niravkumar2008/AI-CALCULATOR/hardware/fab_v15_lcd/cpl_easyeda_check_v15.md

| Ref | LCSC | EasyEDA footprint | KiCad rot | CPL rot | EasyEDA pin 1 -> KiCad pad 1 (mm) | worst same-number pad offset (mm) | every EasyEDA pad on a KiCad pad | Result |
|---|---|---|---|---|---|---|---|---|
| D1 | C8598 | SOD-123_L2.7-W1.6-LS3.7-RD-1 | 0 | 0 | 0.05 | 0.05 | yes | PASS |
| D2 | C8598 | SOD-123_L2.7-W1.6-LS3.7-RD-1 | 0 | 0 | 0.05 | 0.05 | yes | PASS |
| D6 | C8598 | SOD-123_L2.7-W1.6-LS3.7-RD-1 | 0 | 0 | 0.05 | 0.05 | yes | PASS |
| D7 | C193402 | SOD-123FL_L2.7-W1.8-LS3.8-RD | 180 | 180 | 0.18 | 0.18 | yes | PASS |
| J1 | C6364666 | FPC-SMD_24P-P0.50_FPC-0.5-24P-HYH2.0 | 180 | 180 | 11.50 | 11.50 | yes | PASS (pin numbers mirrored on purpose: geometry only) |
| J3 | C46061768 | CONN-SMD_4P-P2.54_HX-PM2.54-1X4PWT | 0 | 180 | 7.62 | 7.62 | yes | PASS (unpolarised 4 identical contacts: geometry only) |
| J4 | C295747 | CONN-SMD_P2.00_S2B-PH-SM4-TB-LF-SN | 0 | 0 | 0.00 | 0.00 | yes | PASS |
| J5 | C2919501 | FPC-SMD_30P-P0.50_HDGC_0.5K-HX-30PWB | 90 | 90 | 14.50 | 14.50 | yes | PASS (pin numbers mirrored on purpose, _LcdReversed, review 13: geometry only) |
| Q1 | C15127 | SOT-23_L2.9-W1.3-P1.90-LS2.4-BR | 0 | 180 | 0.21 | 0.21 | yes | PASS |
| Q2 | C15127 | SOT-23_L2.9-W1.3-P1.90-LS2.4-BR | 90 | 270 | 0.21 | 0.21 | yes | PASS |
| Q4 | C15127 | SOT-23_L2.9-W1.3-P1.90-LS2.4-BR | 90 | 270 | 0.21 | 0.21 | yes | PASS |
| Q5 | C20917 | SOT-23-3_L2.9-W1.3-P1.90-LS2.4-BR | -90 | 90 | 0.06 | 0.06 | yes | PASS |
| R23 | C22810 | R0603 | 180 | 180 | 0.07 | 0.07 | yes | PASS |
| U1 | C3013941 | BULETM-SMD_ESP32-S3-MINI-1-N8 | 90 | 90 | 0.02 | 0.03 | yes | PASS |
| U2 | C424093 | SOT-23-5_L3.0-W1.7-P0.95-LS2.8-BL | 0 | 270 | 0.01 | 0.01 | yes | PASS |
| U3 | C841192 | TSOT-23-5_L2.9-W1.6-P0.95-LS2.8-BL | 0 | 270 | 0.01 | 0.01 | yes | PASS |
| U4 | C53099 | SOT-23-5_L3.0-W1.7-P0.95-LS2.8-BR | 0 | 180 | 0.16 | 0.16 | yes | PASS |
| U5 | C53100 | SOT-23-5_L3.0-W1.7-P0.95-LS2.8-BR | 0 | 180 | 0.16 | 0.16 | yes | PASS |
| U6 | C138713 | WQFN-24_L4.0-W4.0-P0.50-TL-EP2.5 | 0 | 0 | 0.08 | 0.08 | yes | PASS |
| U7 | C7519 | SOT-23-6_L2.9-W1.6-P0.95-LS2.8-BL | 0 | 270 | 0.01 | 0.01 | yes | PASS |
