niravkumar2008/AI-CALCULATOR/hardware/fitcheck/clearance_table.md

# F-side clearance table (generated by tools/make_fitcheck.py)

Height = tallest point of the 3D model above the board F side. Rib = tallest back-cover feature within 1.5 mm of the part (photo positions are +-1 mm). Margin = free height - rib - part, for the free-height cases in backcover_fx115es.json (design 6.0 = D4 measured to the inside face of the back cover). Below 0.3 = needs a fix or a grind.

Last column: after the grind plan (solar box -> 0 mm, upper rib B (camera) -> 0 mm).

| Part | Height | Back-cover feature over it | Feature height | Margin @ 6.0 (design) | Margin @ 5.5 (pessimistic) | Margin after grind (design) |
|---|---|---|---|---|---|---|
| J4 | 5.50 | solar box | 5.5 | **-5.00** | **-5.50** | 0.50 |
| camera 5.4 * | 5.40 | upper rib B (camera) | 1 | **-0.40** | **-0.90** | 0.60 |
| magnet body * | 4.80 | - | 0 | 1.20 | 0.70 | 1.20 |
| LiPo #1317 150 mAh 3.8 thick * | 3.80 | solar box | 5.5 | **-3.30** | **-3.80** | 2.20 |
| J3 | 2.50 | solar box | 5.5 | **-2.00** | **-2.50** | 3.50 |
| U1 | 2.41 | upper rib B left | 1 | 2.59 | 2.09 | 2.59 |
| L1 | 2.00 | upper vert 1 | 1 | 3.00 | 2.50 | 3.00 |
| J2 | 1.99 | upper rib B | 1 | 3.01 | 2.51 | 3.01 |
| J1 | 1.99 | low rib 1 | 1 | 3.01 | 2.51 | 3.01 |
| U2 | 1.60 | solar box | 5.5 | **-1.10** | **-1.60** | 4.40 |
| C20 | 1.59 | - | 0 | 4.41 | 3.91 | 4.41 |
| U7 | 1.55 | upper rib A | 1 | 3.45 | 2.95 | 3.45 |
| U3 | 1.55 | solar box | 5.5 | **-1.05** | **-1.55** | 4.45 |
| U5 | 1.55 | low rib 1 | 1 | 3.45 | 2.95 | 3.45 |
| U4 | 1.55 | - | 0 | 4.45 | 3.95 | 4.45 |
| D4 | 1.26 | upper rib C, upper vert 1 | 1 | 3.74 | 3.24 | 3.74 |
| D1 | 1.26 | solar box | 5.5 | **-0.76** | **-1.26** | 4.74 |
| D3 | 1.26 | upper rib C, upper vert 1 | 1 | 3.74 | 3.24 | 3.74 |
| D5 | 1.26 | upper rib C, upper vert 1 | 1 | 3.74 | 3.24 | 3.74 |
| D6 | 1.26 | - | 0 | 4.74 | 4.24 | 4.74 |
| D2 | 1.26 | big ring | 4 | 0.74 | **0.24** | 0.74 |
| C32 | 1.24 | upper rib A | 1 | 3.76 | 3.26 | 3.76 |
| C33 | 1.24 | - | 0 | 4.76 | 4.26 | 4.76 |
| C34 | 1.24 | - | 0 | 4.76 | 4.26 | 4.76 |
| C1 | 1.24 | upper rib C | 1 | 3.76 | 3.26 | 3.76 |
| Q2 | 1.20 | solar box | 5.5 | **-0.70** | **-1.20** | 4.80 |
| Q1 | 1.20 | upper rib A, upper vert 2 | 1 | 3.80 | 3.30 | 3.80 |
| Q3 | 1.10 | upper rib B | 1 | 3.90 | 3.40 | 3.90 |
| U6 | 1.02 | - | 0 | 4.98 | 4.48 | 4.98 |
| D7 | 0.99 | solar box | 5.5 | **-0.49** | **-0.99** | 5.01 |
| C6 | 0.79 | solar box | 5.5 | **-0.29** | **-0.79** | 5.21 |
| C23 | 0.79 | - | 0 | 5.21 | 4.71 | 5.21 |
| C19 | 0.79 | upper rib B, upper rib B (camera) | 1 | 4.21 | 3.71 | 4.21 |
| C27 | 0.79 | upper rib C, upper vert 1 | 1 | 4.21 | 3.71 | 4.21 |
| C22 | 0.79 | - | 0 | 5.21 | 4.71 | 5.21 |
| FB1 | 0.79 | - | 0 | 5.21 | 4.71 | 5.21 |
| C7 | 0.79 | - | 0 | 5.21 | 4.71 | 5.21 |
| C28 | 0.79 | upper rib B | 1 | 4.21 | 3.71 | 4.21 |
| C21 | 0.79 | - | 0 | 5.21 | 4.71 | 5.21 |
| C8 | 0.79 | upper rib A | 1 | 4.21 | 3.71 | 4.21 |
| C3 | 0.79 | upper rib C | 1 | 4.21 | 3.71 | 4.21 |
| C5 | 0.79 | solar box | 5.5 | **-0.29** | **-0.79** | 5.21 |
| C24 | 0.79 | - | 0 | 5.21 | 4.71 | 5.21 |
| C25 | 0.79 | - | 0 | 5.21 | 4.71 | 5.21 |
| C26 | 0.79 | upper rib B | 1 | 4.21 | 3.71 | 4.21 |
| C30 | 0.79 | - | 0 | 5.21 | 4.71 | 5.21 |
| C29 | 0.79 | - | 0 | 5.21 | 4.71 | 5.21 |
| C17 | 0.60 | - | 0 | 5.40 | 4.90 | 5.40 |
| C18 | 0.49 | - | 0 | 5.51 | 5.01 | 5.51 |
| C13 | 0.49 | - | 0 | 5.51 | 5.01 | 5.51 |
| C16 | 0.49 | big ring | 4 | 1.51 | 1.01 | 1.51 |
| C31 | 0.49 | - | 0 | 5.51 | 5.01 | 5.51 |
| C9 | 0.49 | upper rib C, upper vert 2 | 1 | 4.51 | 4.01 | 4.51 |
| C10 | 0.49 | - | 0 | 5.51 | 5.01 | 5.51 |
| C12 | 0.49 | - | 0 | 5.51 | 5.01 | 5.51 |
| C2 | 0.49 | upper rib C | 1 | 4.51 | 4.01 | 4.51 |
| C15 | 0.49 | low rib 1 | 1 | 4.51 | 4.01 | 4.51 |
| C11 | 0.49 | - | 0 | 5.51 | 5.01 | 5.51 |
| C14 | 0.49 | - | 0 | 5.51 | 5.01 | 5.51 |
| C4 | 0.49 | - | 0 | 5.51 | 5.01 | 5.51 |
| R12 | 0.45 | upper rib B, upper vert 1 | 1 | 4.55 | 4.05 | 4.55 |
| R10 | 0.34 | - | 0 | 5.66 | 5.16 | 5.66 |
| R19 | 0.34 | - | 0 | 5.66 | 5.16 | 5.66 |
| R3 | 0.34 | - | 0 | 5.66 | 5.16 | 5.66 |
| R17 | 0.34 | - | 0 | 5.66 | 5.16 | 5.66 |
| R20 | 0.34 | upper rib A | 1 | 4.66 | 4.16 | 4.66 |
| R11 | 0.34 | - | 0 | 5.66 | 5.16 | 5.66 |
| R2 | 0.34 | solar box | 5.5 | **0.16** | **-0.34** | 5.66 |
| R6 | 0.34 | upper rib C | 1 | 4.66 | 4.16 | 4.66 |
| R16 | 0.34 | - | 0 | 5.66 | 5.16 | 5.66 |
| R15 | 0.34 | - | 0 | 5.66 | 5.16 | 5.66 |
| R1 | 0.34 | - | 0 | 5.66 | 5.16 | 5.66 |
| R14 | 0.34 | - | 0 | 5.66 | 5.16 | 5.66 |
| R13 | 0.34 | - | 0 | 5.66 | 5.16 | 5.66 |
| R4 | 0.34 | solar box | 5.5 | **0.16** | **-0.34** | 5.66 |
| R5 | 0.34 | upper rib A | 1 | 4.66 | 4.16 | 4.66 |
| R9 | 0.34 | - | 0 | 5.66 | 5.16 | 5.66 |
| R18 | 0.34 | - | 0 | 5.66 | 5.16 | 5.66 |
| R7 | 0.34 | upper rib C | 1 | 4.66 | 4.16 | 4.66 |
| R8 | 0.34 | - | 0 | 5.66 | 5.16 | 5.66 |
| TP6 | 0.05 | upper rib A, upper vert 2 | 1 | 4.95 | 4.45 | 4.95 |
| TP1 | 0.05 | - | 0 | 5.95 | 5.45 | 5.95 |
| TP5 | 0.05 | upper rib A | 1 | 4.95 | 4.45 | 4.95 |
| TP4 | 0.05 | - | 0 | 5.95 | 5.45 | 5.95 |
| TP3 | 0.05 | upper vert 2 | 1 | 4.95 | 4.45 | 4.95 |
| TP7 | 0.05 | - | 0 | 5.95 | 5.45 | 5.95 |
| TP2 | 0.05 | upper vert 2 | 1 | 4.95 | 4.45 | 4.95 |

\* = not a board part. **camera:** not soldered; module sits on the board (or taped to the cover), lens under the drilled window. **LiPo:** rev E: Adafruit #1317 flat on the back-cover floor under the solar-box zone (ground flat), 2.2 mm under the board, 0.3 mm under the LR44 cup (kept); its margin row counts the floor-to-board space (6.0) only. **magnet:** stage 13b: body in front of the board edge (y 57.3-61.3), centred 1.3 mm above the F side, spanning 2.2 below to 4.8 above it; legs straightened into J3 (right-angle header). The LiPo row is the floor-to-board space (6.0) minus the cell (3.8): the real limit is the LR44 cup in the faceplate (0.3 mm, assembly_report.md section 9).

Front shell: LR44 cup (centre 168.3, 69.0, outer dia 14); magnet slot (top wall) at [116.75, 56.9]-[138.25, 58.6]; antenna relief (inner rib) at [114.15, 71.5]-[115.15, 106.5]. See the grind list on grind_map_front_shell.svg.
