niravkumar2008/AI-CALCULATOR/hardware/kicad/DESIGN_SUMMARY.md

# AI Calculator PCB - KiCad design summary

Generated by `hardware/kicad/kicad_summary.py` from the KiCad 10 project in `C:\Users\r_kas\OneDrive\Documents\GitHub\AI-CALCULATOR\hardware\kicad`. Do not edit by hand. Context and decisions: `Claude outputs/AI_CALC_PCB_HANDOFF.md`.

## Hierarchy

Root sheet `ai_calc.kicad_sch` contains:

- **Power and charging** (`power.kicad_sch`)
- **ESP32-S3 MCU** (`mcu.kicad_sch`)
- **Camera OV5640** (`camera.kicad_sch`)
- **E-paper driver** (`epaper.kicad_sch`)
- **Keypad and TCA8418** (`keypad.kicad_sch`)
- **Connectors (magnet USB, battery)** (`connectors.kicad_sch`)

## Sheet: Power and charging (`power.kicad_sch`)

Net labels: +3V3, BAT+, CHG_PROG, CHG_STAT, CHG_STAT_RAW, GND, Q1_G, SYS, VBAT_P, VBAT_SENSE, VBUS, VBUS_SENSE

| Ref | Value | Footprint | LCSC |
|---|---|---|---|
| C5 | 4.7uF | Capacitor_SMD:C_0603_1608Metric | C19666 |
| C6 | 4.7uF | Capacitor_SMD:C_0603_1608Metric | C19666 |
| C7 | 4.7uF | Capacitor_SMD:C_0603_1608Metric | C19666 |
| C8 | 10uF | Capacitor_SMD:C_0603_1608Metric | C19702 |
| C9 | 100nF | Capacitor_SMD:C_0402_1005Metric | C1525 |
| D1 | B5819W | Diode_SMD:D_SOD-123 | C8598 |
| D6 | B5819W (STAT level clamp) | Diode_SMD:D_SOD-123 | C8598 |
| Q1 | AO3401A (reverse battery) | Package_TO_SOT_SMD:SOT-23 | C15127 |
| Q2 | AO3401A (load share) | Package_TO_SOT_SMD:SOT-23 | C15127 |
| R2 | 20k (50 mA) | Resistor_SMD:R_0402_1005Metric | C25765 |
| R3 | 100k | Resistor_SMD:R_0402_1005Metric | C25741 |
| R4 | 10k | Resistor_SMD:R_0402_1005Metric | C25744 |
| R5 | 20k | Resistor_SMD:R_0402_1005Metric | C25765 |
| R6 | 1M | Resistor_SMD:R_0402_1005Metric | C26083 |
| R7 | 1M | Resistor_SMD:R_0402_1005Metric | C26083 |
| R20 | 100k | Resistor_SMD:R_0402_1005Metric | C25741 |
| U2 | MCP73831T-2ACI/OT | Package_TO_SOT_SMD:SOT-23-5 | C424093 |
| U3 | RT9080-33GJ5 | Package_TO_SOT_SMD:SOT-23-5 | C841192 |

## Sheet: ESP32-S3 MCU (`mcu.kicad_sch`)

Net labels: +3V3, BAT+, BOOT, CAM_D0, CAM_D1, CAM_D2, CAM_D3, CAM_D4, CAM_D5, CAM_D6, CAM_D7, CAM_HREF, CAM_PCLK, CAM_PWDN, CAM_PWR_EN, CAM_RESET, CAM_SIOC, CAM_SIOD, CAM_VSYNC, CAM_XCLK, CHG_STAT, EN, EPD_BUSY, EPD_CLK, EPD_CS, EPD_DC, EPD_DIN, EPD_RST, GND, I2C_SCL, I2C_SDA, KEYPAD_INT, KEY_ON, UART_RX, UART_TX, USB_DM, USB_DP, VBAT_SENSE, VBUS_SENSE

| Ref | Value | Footprint | LCSC |
|---|---|---|---|
| C1 | 22uF | Capacitor_SMD:C_0805_2012Metric | C45783 |
| C2 | 100nF | Capacitor_SMD:C_0402_1005Metric | C1525 |
| C3 | 10uF | Capacitor_SMD:C_0603_1608Metric | C19702 |
| C4 | 1uF | Capacitor_SMD:C_0402_1005Metric | C52923 |
| C32 | 22uF | Capacitor_SMD:C_0805_2012Metric | C45783 |
| C33 | 22uF | Capacitor_SMD:C_0805_2012Metric | C45783 |
| C34 | 22uF | Capacitor_SMD:C_0805_2012Metric | C45783 |
| R1 | 10k | Resistor_SMD:R_0402_1005Metric | C25744 |
| TP1 | BOOT | TestPoint:TestPoint_Pad_D1.5mm |  |
| TP2 | UART_TX | TestPoint:TestPoint_Pad_D1.0mm |  |
| TP3 | UART_RX | TestPoint:TestPoint_Pad_D1.0mm |  |
| TP4 | GND | TestPoint:TestPoint_Pad_D1.5mm |  |
| TP5 | +3V3 | TestPoint:TestPoint_Pad_D1.5mm |  |
| TP6 | BAT+ | TestPoint:TestPoint_Pad_D1.5mm |  |
| TP7 | EN | TestPoint:TestPoint_Pad_D1.5mm |  |
| U1 | ESP32-S3-MINI-1-N4R2 | ai_calc:ESP32-S3-MINI-1 | C3013941 |

## Sheet: Camera OV5640 (`camera.kicad_sch`)

Net labels: CAM_2V8, CAM_AF, CAM_AVDD, CAM_D0, CAM_D1, CAM_D2, CAM_D3, CAM_D4, CAM_D5, CAM_D6, CAM_D7, CAM_DVDD, CAM_HREF, CAM_PCLK, CAM_PWDN, CAM_PWR_EN, CAM_RESET, CAM_SIOC, CAM_SIOD, CAM_VSYNC, CAM_XCLK, GND, SYS

| Ref | Value | Footprint | LCSC |
|---|---|---|---|
| C10 | 1uF | Capacitor_SMD:C_0402_1005Metric | C52923 |
| C11 | 2.2uF | Capacitor_SMD:C_0402_1005Metric | C12530 |
| C12 | 100nF | Capacitor_SMD:C_0402_1005Metric | C1525 |
| C13 | 2.2uF | Capacitor_SMD:C_0402_1005Metric | C12530 |
| C14 | 1uF | Capacitor_SMD:C_0402_1005Metric | C52923 |
| C15 | 2.2uF | Capacitor_SMD:C_0402_1005Metric | C12530 |
| C16 | 2.2uF | Capacitor_SMD:C_0402_1005Metric | C12530 |
| C17 | 100nF | Capacitor_SMD:C_0402_1005Metric | C1525 |
| C18 | 100nF | Capacitor_SMD:C_0402_1005Metric | C1525 |
| D2 | B5819W | Diode_SMD:D_SOD-123 | C8598 |
| FB1 | 600R@100MHz | Inductor_SMD:L_0603_1608Metric | C1002 |
| J1 | Camera FPC 24P 0.5mm dual-contact (OV5640, cable contacts down) | ai_calc:FPC_24P_P0.5mm_DualContact_C6364666_CamReversed | C6364666 |
| R8 | 10k | Resistor_SMD:R_0402_1005Metric | C25744 |
| R9 | 10k | Resistor_SMD:R_0402_1005Metric | C25744 |
| R10 | 100k | Resistor_SMD:R_0402_1005Metric | C25741 |
| R18 | 4.7k | Resistor_SMD:R_0402_1005Metric | C25900 |
| R19 | 4.7k | Resistor_SMD:R_0402_1005Metric | C25900 |
| U4 | ME6211C28M5G-N | Package_TO_SOT_SMD:SOT-23-5 | C53099 |
| U5 | ME6211C15M5G-N | Package_TO_SOT_SMD:SOT-23-5 | C53100 |

## Sheet: E-paper driver (`epaper.kicad_sch`)

Net labels: +3V3, EPD_BUSY, EPD_CLK, EPD_CS, EPD_DC, EPD_DIN, EPD_GDR, EPD_PREVGH, EPD_PREVGL, EPD_PUMP, EPD_RESE, EPD_RST, EPD_SW, EPD_VCOM, EPD_VDD, EPD_VGH, EPD_VGL, EPD_VPP, EPD_VSH, EPD_VSL, GND

| Ref | Value | Footprint | LCSC |
|---|---|---|---|
| C19 | 4.7uF | Capacitor_SMD:C_0603_1608Metric | C19666 |
| C20 | 4.7uF 50V | Capacitor_SMD:C_1206_3216Metric | C29823 |
| C21 | 1uF 50V | Capacitor_SMD:C_0603_1608Metric | C15849 |
| C22 | 1uF 50V | Capacitor_SMD:C_0603_1608Metric | C15849 |
| C23 | 1uF 50V | Capacitor_SMD:C_0603_1608Metric | C15849 |
| C24 | 1uF 50V | Capacitor_SMD:C_0603_1608Metric | C15849 |
| C25 | 1uF 50V | Capacitor_SMD:C_0603_1608Metric | C15849 |
| C26 | 1uF 50V | Capacitor_SMD:C_0603_1608Metric | C15849 |
| C27 | 1uF 50V | Capacitor_SMD:C_0603_1608Metric | C15849 |
| C28 | 1uF 50V | Capacitor_SMD:C_0603_1608Metric | C15849 |
| C29 | 1uF 50V | Capacitor_SMD:C_0603_1608Metric | C15849 |
| C30 | 1uF 50V | Capacitor_SMD:C_0603_1608Metric | C15849 |
| D3 | B5819W | Diode_SMD:D_SOD-123 | C8598 |
| D4 | B5819W | Diode_SMD:D_SOD-123 | C8598 |
| D5 | B5819W | Diode_SMD:D_SOD-123 | C8598 |
| J2 | E-paper FPC 24P 0.5mm dual-contact (2.13in V4) | ai_calc:FPC_24P_P0.5mm_DualContact_C6364666 | C6364666 |
| L1 | 68uH SMNR4020 | ai_calc:L_SMNR4020_4.0x4.0mm | C135265 |
| Q3 | SI1308EDL-T1-GE3 | ai_calc:SOT-323_SI1308EDL | C469327 |
| R11 | 10k | Resistor_SMD:R_0402_1005Metric | C25744 |
| R12 | 3R (2.13in B/W panel) | Resistor_SMD:R_0603_1608Metric | C23157 |

## Sheet: Keypad and TCA8418 (`keypad.kicad_sch`)

Net labels: +3V3, COL0, COL1, COL2, COL3, COL4, COL5, COL6, COL7, COL8, COL9, GND, I2C_SCL, I2C_SDA, KEYPAD_INT, KEY_ON, ROW0, ROW1, ROW2, ROW3, ROW4, ROW5, ROW6, ROW7, TCA_RESET

| Ref | Value | Footprint | LCSC |
|---|---|---|---|
| C31 | 100nF | Capacitor_SMD:C_0402_1005Metric | C1525 |
| R13 | 4.7k | Resistor_SMD:R_0402_1005Metric | C25900 |
| R14 | 4.7k | Resistor_SMD:R_0402_1005Metric | C25900 |
| R15 | 10k | Resistor_SMD:R_0402_1005Metric | C25744 |
| R16 | 10k | Resistor_SMD:R_0402_1005Metric | C25744 |
| R17 | 100k | Resistor_SMD:R_0402_1005Metric | C25741 |
| SW1 | SHIFT | ai_calc:KeyPad_6.0x4.5_H3notch |  |
| SW2 | ALPHA | ai_calc:KeyPad_6.0x4.5 |  |
| SW3 | MODE | ai_calc:KeyPad_6.0x4.5 |  |
| SW4 | CALC | ai_calc:KeyPad_6.0x4.5 |  |
| SW5 | ∫dx | ai_calc:KeyPad_6.0x4.5 |  |
| SW6 | x^-1 | ai_calc:KeyPad_6.0x4.5 |  |
| SW7 | log_a | ai_calc:KeyPad_6.0x4.5 |  |
| SW8 | a/b | ai_calc:KeyPad_6.0x4.5 |  |
| SW9 | sqrt | ai_calc:KeyPad_6.0x4.5 |  |
| SW10 | x^2 | ai_calc:KeyPad_6.0x4.5 |  |
| SW11 | x^n | ai_calc:KeyPad_6.0x4.5 |  |
| SW12 | log | ai_calc:KeyPad_6.0x4.5 |  |
| SW13 | ln | ai_calc:KeyPad_6.0x4.5 |  |
| SW14 | (-) | ai_calc:KeyPad_6.0x4.5 |  |
| SW15 | deg-min-sec | ai_calc:KeyPad_6.0x4.5 |  |
| SW16 | hyp | ai_calc:KeyPad_6.0x4.5 |  |
| SW17 | sin | ai_calc:KeyPad_6.0x4.5 |  |
| SW18 | cos | ai_calc:KeyPad_6.0x4.5 |  |
| SW19 | tan | ai_calc:KeyPad_6.0x4.5 |  |
| SW20 | RCL | ai_calc:KeyPad_6.0x4.5 |  |
| SW21 | ENG | ai_calc:KeyPad_6.0x4.5 |  |
| SW22 | ( | ai_calc:KeyPad_6.0x4.5 |  |
| SW23 | ) | ai_calc:KeyPad_6.0x4.5 |  |
| SW24 | S<>D | ai_calc:KeyPad_6.0x4.5 |  |
| SW25 | M+ | ai_calc:KeyPad_6.0x4.5 |  |
| SW26 | 7 | ai_calc:KeyPad_9.0x7.0 |  |
| SW27 | 8 | ai_calc:KeyPad_9.0x7.0 |  |
| SW28 | 9 | ai_calc:KeyPad_9.0x7.0 |  |
| SW29 | DEL | ai_calc:KeyPad_9.0x7.0 |  |
| SW30 | AC | ai_calc:KeyPad_9.0x7.0 |  |
| SW31 | 4 | ai_calc:KeyPad_9.0x7.0 |  |
| SW32 | 5 | ai_calc:KeyPad_9.0x7.0 |  |
| SW33 | 6 | ai_calc:KeyPad_9.0x7.0 |  |
| SW34 | x | ai_calc:KeyPad_9.0x7.0 |  |
| SW35 | / | ai_calc:KeyPad_9.0x7.0 |  |
| SW36 | 1 | ai_calc:KeyPad_9.0x7.0 |  |
| SW37 | 2 | ai_calc:KeyPad_9.0x7.0 |  |
| SW38 | 3 | ai_calc:KeyPad_9.0x7.0 |  |
| SW39 | + | ai_calc:KeyPad_9.0x7.0 |  |
| SW40 | - | ai_calc:KeyPad_9.0x7.0 |  |
| SW41 | 0 | ai_calc:KeyPad_6.0x4.5 |  |
| SW42 | . | ai_calc:KeyPad_6.0x4.5 |  |
| SW43 | x10^x | ai_calc:KeyPad_6.0x4.5 |  |
| SW44 | Ans | ai_calc:KeyPad_6.0x4.5 |  |
| SW45 | = | ai_calc:KeyPad_6.0x4.5 |  |
| SW46 | UP | ai_calc:KeyPad_5.0x4.0 |  |
| SW47 | DOWN | ai_calc:KeyPad_5.0x4.0 |  |
| SW48 | LEFT | ai_calc:KeyPad_5.0x4.0 |  |
| SW49 | RIGHT | ai_calc:KeyPad_5.0x4.0 |  |
| SW50 | ON | ai_calc:KeyPad_6.0x4.5 |  |
| U6 | TCA8418RTWR | Package_DFN_QFN:HVQFN-24-1EP_4x4mm_P0.5mm_EP2.6x2.6mm | C138713 |

## Sheet: Connectors (magnet USB, battery) (`connectors.kicad_sch`)

Net labels: +3V3, BAT+, GND, USB_DM, USB_DP, VBUS

| Ref | Value | Footprint | LCSC |
|---|---|---|---|
| D7 | SMF5.0A (VBUS TVS) | Diode_SMD:D_SMF | C193402 |
| J3 | Magnetic USB (Adafruit 5358, N end at pin 1): VBUS D- D+ GND | ai_calc:PinSocket_1x04_P2.54mm_SMD_RA_C46061768 | C46061768 |
| J4 | Battery JST-PH (Adafruit 1570) | ai_calc:JST_PH_S2B-PH-SM4-TB_LCSC | C295747 |
| U7 | USBLC6-2SC6 | Package_TO_SOT_SMD:SOT-23-6 | C7519 |

## Board (`ai_calc.kicad_pcb`)

- Outline extent: 71.6 x 148.8 mm, thickness 0.8 mm, 2 layers (F.Cu = component side facing back cover, B.Cu = key pads + e-paper)
- 147 footprints, 3035 track segments, 333 vias
- Copper zones on: GND
- Nets (92): +3V3, /Keypad and TCA8418/COL0, /Keypad and TCA8418/COL1, /Keypad and TCA8418/COL2, /Keypad and TCA8418/COL3, /Keypad and TCA8418/COL4, /Keypad and TCA8418/COL5, /Keypad and TCA8418/COL6, /Keypad and TCA8418/COL7, /Keypad and TCA8418/COL8, /Keypad and TCA8418/COL9, /Keypad and TCA8418/ROW0, /Keypad and TCA8418/ROW1, /Keypad and TCA8418/ROW2, /Keypad and TCA8418/ROW3, /Keypad and TCA8418/ROW4, /Keypad and TCA8418/ROW5, /Keypad and TCA8418/ROW6, /Keypad and TCA8418/ROW7, BAT+, BOOT, CAM_2V8, CAM_AF, CAM_AVDD, CAM_D0, CAM_D1, CAM_D2, CAM_D3, CAM_D4, CAM_D5, CAM_D6, CAM_D7, CAM_DVDD, CAM_HREF, CAM_PCLK, CAM_PWDN, CAM_PWR_EN, CAM_RESET, CAM_SIOC, CAM_SIOD, CAM_VSYNC, CAM_XCLK, CHG_PROG, CHG_STAT, CHG_STAT_RAW, EN, EPD_BUSY, EPD_CLK, EPD_CS, EPD_DC, EPD_DIN, EPD_GDR, EPD_PREVGH, EPD_PREVGL, EPD_PUMP, EPD_RESE, EPD_RST, EPD_SW, EPD_VCOM, EPD_VDD, EPD_VGH, EPD_VGL, EPD_VPP, EPD_VSH, EPD_VSL, GND, I2C_SCL, I2C_SDA, KEYPAD_INT, KEY_ON, Q1_G, SYS, TCA_RESET, UART_RX, UART_TX, USB_DM, USB_DP, VBAT_P, VBAT_SENSE, VBUS, VBUS_SENSE, unconnected-(J1-Pin_1-Pad1), unconnected-(J2-Pin_1-Pad1), unconnected-(J2-Pin_6-Pad6), unconnected-(J2-Pin_7-Pad7), unconnected-(U1-IO26-Pad26), unconnected-(U1-IO3-Pad7), unconnected-(U1-IO45-Pad41), unconnected-(U1-IO46-Pad44), unconnected-(U3-NC-Pad4), unconnected-(U4-NC-Pad4), unconnected-(U5-NC-Pad4)

| Ref | Footprint | Layer | Position (x y rot) |
|---|---|---|---|
| C1 | Capacitor_SMD:C_0805_2012Metric | F.Cu | 121.3 106.8 90 |
| C2 | Capacitor_SMD:C_0402_1005Metric | F.Cu | 123.3 106.15 90 |
| C3 | Capacitor_SMD:C_0603_1608Metric | F.Cu | 125 106.6 90 |
| C4 | Capacitor_SMD:C_0402_1005Metric | F.Cu | 125.7 87.9 |
| C5 | Capacitor_SMD:C_0603_1608Metric | F.Cu | 135.9 72 90 |
| C6 | Capacitor_SMD:C_0603_1608Metric | F.Cu | 139.6 66 90 |
| C7 | Capacitor_SMD:C_0603_1608Metric | F.Cu | 119 76.8 90 |
| C8 | Capacitor_SMD:C_0603_1608Metric | F.Cu | 125.8 79.3 |
| C9 | Capacitor_SMD:C_0402_1005Metric | F.Cu | 139 107 90 |
| C10 | Capacitor_SMD:C_0402_1005Metric | F.Cu | 134.6 157 90 |
| C11 | Capacitor_SMD:C_0402_1005Metric | F.Cu | 140 157 90 |
| C12 | Capacitor_SMD:C_0402_1005Metric | F.Cu | 141.2 157 90 |
| C13 | Capacitor_SMD:C_0402_1005Metric | F.Cu | 140 154.4 90 |
| C14 | Capacitor_SMD:C_0402_1005Metric | F.Cu | 134.6 160.6 90 |
| C15 | Capacitor_SMD:C_0402_1005Metric | F.Cu | 140 160.6 90 |
| C16 | Capacitor_SMD:C_0402_1005Metric | F.Cu | 158 151.8 |
| C17 | Capacitor_SMD:C_0402_1005Metric | F.Cu | 158 156.2 |
| C18 | Capacitor_SMD:C_0402_1005Metric | F.Cu | 137.2 165.2 90 |
| C19 | Capacitor_SMD:C_0603_1608Metric | F.Cu | 157.8 97.03 90 |
| C20 | Capacitor_SMD:C_1206_3216Metric | F.Cu | 165.2 102.83 |
| C21 | Capacitor_SMD:C_0603_1608Metric | F.Cu | 168.6 86.03 |
| C22 | Capacitor_SMD:C_0603_1608Metric | F.Cu | 168.6 87.63 |
| C23 | Capacitor_SMD:C_0603_1608Metric | F.Cu | 168.6 89.23 |
| C24 | Capacitor_SMD:C_0603_1608Metric | F.Cu | 168.6 90.83 |
| C25 | Capacitor_SMD:C_0603_1608Metric | F.Cu | 168.6 92.43 |
| C26 | Capacitor_SMD:C_0603_1608Metric | F.Cu | 168.6 94.03 |
| C27 | Capacitor_SMD:C_0603_1608Metric | F.Cu | 160.4 108.83 180 |
| C28 | Capacitor_SMD:C_0603_1608Metric | F.Cu | 168.6 97.23 |
| C29 | Capacitor_SMD:C_0603_1608Metric | F.Cu | 168.6 98.83 |
| C30 | Capacitor_SMD:C_0603_1608Metric | F.Cu | 168.6 100.43 |
| C31 | Capacitor_SMD:C_0402_1005Metric | F.Cu | 129.4 144.2 90 |
| C32 | Capacitor_SMD:C_0805_2012Metric | F.Cu | 118.4 81 90 |
| C33 | Capacitor_SMD:C_0805_2012Metric | F.Cu | 121.7 84.75 180 |
| C34 | Capacitor_SMD:C_0805_2012Metric | F.Cu | 124.55 85.35 -90 |
| D1 | Diode_SMD:D_SOD-123 | F.Cu | 129.2 75.2 |
| D2 | Diode_SMD:D_SOD-123 | F.Cu | 158 154 |
| D3 | Diode_SMD:D_SOD-123 | F.Cu | 164.6 106.23 |
| D4 | Diode_SMD:D_SOD-123 | F.Cu | 159.5 106.23 |
| D5 | Diode_SMD:D_SOD-123 | F.Cu | 164.6 108.63 |
| D6 | Diode_SMD:D_SOD-123 | F.Cu | 130.3 78.6 |
| D7 | Diode_SMD:D_SMF | F.Cu | 119.2 73.4 180 |
| FB1 | Inductor_SMD:L_0603_1608Metric | F.Cu | 137.4 154.4 |
| FID1 | Fiducial_1mm_Mask2mm | F.Cu | 121.5 203.5 |
| FID2 | Fiducial_1mm_Mask2mm | F.Cu | 178.5 203.5 |
| FID3 | Fiducial_1mm_Mask2mm | F.Cu | 177 112.5 |
| H1 | ai_calc:ScrewBoss_Hole_6.0mm | F.Cu | 127.5 126.1 |
| H2 | ai_calc:Post_Slot_4.2x5.0mm | F.Cu | 130.85 176.25 |
| H3 | ai_calc:ScrewBoss_Hole_6.0mm | F.Cu | 174 126.1 |
| H4 | ai_calc:Post_Hole_4.2mm | F.Cu | 171.06 145.96 |
| H6 | ai_calc:Post_Hole_4.2mm | F.Cu | 130.6 186.99 |
| H8 | ai_calc:Post_Hole_4.2mm | F.Cu | 128.85 137 |
| H9 | ai_calc:Post_Slot_4.4x4.8mm | F.Cu | 169.2 176.2 |
| H10 | ai_calc:Post_Hole_4.2mm | F.Cu | 171.25 136.8 |
| H13 | ai_calc:Post_Slot_4.2x4.45mm | F.Cu | 130.5 198.325 |
| H14 | ai_calc:Post_Slot_4.2x4.65mm | F.Cu | 169.1 198.375 |
| J1 | ai_calc:FPC_24P_P0.5mm_DualContact_C6364666_CamReversed | F.Cu | 150 161 180 |
| J2 | ai_calc:FPC_24P_P0.5mm_DualContact_C6364666 | F.Cu | 177.9 92.83 -90 |
| J3 | ai_calc:PinSocket_1x04_P2.54mm_SMD_RA_C46061768 | F.Cu | 127.5 72 |
| J4 | ai_calc:JST_PH_S2B-PH-SM4-TB_LCSC | F.Cu | 142.6 74.6 |
| L1 | ai_calc:L_SMNR4020_4.0x4.0mm | F.Cu | 159.8 101.83 180 |
| Q1 | Package_TO_SOT_SMD:SOT-23 | F.Cu | 136.1 79.5 |
| Q2 | Package_TO_SOT_SMD:SOT-23 | F.Cu | 135.9 75.6 90 |
| Q3 | ai_calc:SOT-323_SI1308EDL | F.Cu | 163.6 97.43 |
| R1 | Resistor_SMD:R_0402_1005Metric | F.Cu | 127.6 87.9 |
| R2 | Resistor_SMD:R_0402_1005Metric | F.Cu | 132.5 74.6 |
| R3 | Resistor_SMD:R_0402_1005Metric | F.Cu | 133.25 78.6 90 |
| R4 | Resistor_SMD:R_0402_1005Metric | F.Cu | 124.9 74.8 90 |
| R5 | Resistor_SMD:R_0402_1005Metric | F.Cu | 126.07 81 |
| R6 | Resistor_SMD:R_0402_1005Metric | F.Cu | 136.6 107 90 |
| R7 | Resistor_SMD:R_0402_1005Metric | F.Cu | 137.8 107 90 |
| R8 | Resistor_SMD:R_0402_1005Metric | F.Cu | 136 165.2 90 |
| R9 | Resistor_SMD:R_0402_1005Metric | F.Cu | 138.4 165.2 90 |
| R10 | Resistor_SMD:R_0402_1005Metric | F.Cu | 134.6 163.4 |
| R11 | Resistor_SMD:R_0402_1005Metric | F.Cu | 165.45 99.85 |
| R12 | Resistor_SMD:R_0603_1608Metric | F.Cu | 164 95.3 180 |
| R13 | Resistor_SMD:R_0402_1005Metric | F.Cu | 122.4 141 90 |
| R14 | Resistor_SMD:R_0402_1005Metric | F.Cu | 123.6 141 90 |
| R15 | Resistor_SMD:R_0402_1005Metric | F.Cu | 124.8 141 90 |
| R16 | Resistor_SMD:R_0402_1005Metric | F.Cu | 126 141 90 |
| R17 | Resistor_SMD:R_0402_1005Metric | F.Cu | 124 117.6 |
| R18 | Resistor_SMD:R_0402_1005Metric | F.Cu | 139.6 165.2 90 |
| R19 | Resistor_SMD:R_0402_1005Metric | F.Cu | 140.8 165.2 90 |
| R20 | Resistor_SMD:R_0402_1005Metric | F.Cu | 130.3 80.6 |
| SW1 | ai_calc:KeyPad_6.0x4.5_H3notch | B.Cu | 176.623 120.795 180 |
| SW2 | ai_calc:KeyPad_6.0x4.5 | B.Cu | 166.026 120.795 180 |
| SW3 | ai_calc:KeyPad_6.0x4.5 | B.Cu | 133.974 120.795 180 |
| SW4 | ai_calc:KeyPad_6.0x4.5 | B.Cu | 176.623 132.45 180 |
| SW5 | ai_calc:KeyPad_6.0x4.5 | B.Cu | 166.026 132.45 180 |
| SW6 | ai_calc:KeyPad_6.0x4.5 | B.Cu | 133.974 132.45 180 |
| SW7 | ai_calc:KeyPad_6.0x4.5 | B.Cu | 123.377 132.45 180 |
| SW8 | ai_calc:KeyPad_6.0x4.5 | B.Cu | 176.623 141.325 180 |
| SW9 | ai_calc:KeyPad_6.0x4.5 | B.Cu | 166.026 141.325 180 |
| SW10 | ai_calc:KeyPad_6.0x4.5 | B.Cu | 155.298 141.325 180 |
| SW11 | ai_calc:KeyPad_6.0x4.5 | B.Cu | 144.702 141.325 180 |
| SW12 | ai_calc:KeyPad_6.0x4.5 | B.Cu | 133.974 141.325 180 |
| SW13 | ai_calc:KeyPad_6.0x4.5 | B.Cu | 123.377 141.325 180 |
| SW14 | ai_calc:KeyPad_6.0x4.5 | B.Cu | 176.623 150.728 180 |
| SW15 | ai_calc:KeyPad_6.0x4.5 | B.Cu | 166.026 150.728 180 |
| SW16 | ai_calc:KeyPad_6.0x4.5 | B.Cu | 155.298 150.728 180 |
| SW17 | ai_calc:KeyPad_6.0x4.5 | B.Cu | 144.702 150.728 180 |
| SW18 | ai_calc:KeyPad_6.0x4.5 | B.Cu | 133.974 150.728 180 |
| SW19 | ai_calc:KeyPad_6.0x4.5 | B.Cu | 123.377 150.728 180 |
| SW20 | ai_calc:KeyPad_6.0x4.5 | B.Cu | 176.623 160.265 180 |
| SW21 | ai_calc:KeyPad_6.0x4.5 | B.Cu | 166.026 160.265 180 |
| SW22 | ai_calc:KeyPad_6.0x4.5 | B.Cu | 155.298 160.265 180 |
| SW23 | ai_calc:KeyPad_6.0x4.5 | B.Cu | 144.702 160.265 180 |
| SW24 | ai_calc:KeyPad_6.0x4.5 | B.Cu | 133.974 160.265 180 |
| SW25 | ai_calc:KeyPad_6.0x4.5 | B.Cu | 123.377 160.265 180 |
| SW26 | ai_calc:KeyPad_9.0x7.0 | B.Cu | 175.695 170.728 180 |
| SW27 | ai_calc:KeyPad_9.0x7.0 | B.Cu | 162.848 170.728 180 |
| SW28 | ai_calc:KeyPad_9.0x7.0 | B.Cu | 150 170.728 180 |
| SW29 | ai_calc:KeyPad_9.0x7.0 | B.Cu | 137.152 170.728 180 |
| SW30 | ai_calc:KeyPad_9.0x7.0 | B.Cu | 124.305 170.728 180 |
| SW31 | ai_calc:KeyPad_9.0x7.0 | B.Cu | 175.695 181.854 180 |
| SW32 | ai_calc:KeyPad_9.0x7.0 | B.Cu | 162.848 181.854 180 |
| SW33 | ai_calc:KeyPad_9.0x7.0 | B.Cu | 150 181.854 180 |
| SW34 | ai_calc:KeyPad_9.0x7.0 | B.Cu | 137.152 181.854 180 |
| SW35 | ai_calc:KeyPad_9.0x7.0 | B.Cu | 124.305 181.854 180 |
| SW36 | ai_calc:KeyPad_9.0x7.0 | B.Cu | 175.695 192.98 180 |
| SW37 | ai_calc:KeyPad_9.0x7.0 | B.Cu | 162.848 192.98 180 |
| SW38 | ai_calc:KeyPad_9.0x7.0 | B.Cu | 150 192.98 180 |
| SW39 | ai_calc:KeyPad_9.0x7.0 | B.Cu | 137.152 192.98 180 |
| SW40 | ai_calc:KeyPad_9.0x7.0 | B.Cu | 124.305 192.98 180 |
| SW41 | ai_calc:KeyPad_6.0x4.5 | B.Cu | 175.695 204.106 180 |
| SW42 | ai_calc:KeyPad_6.0x4.5 | B.Cu | 162.848 204.106 180 |
| SW43 | ai_calc:KeyPad_6.0x4.5 | B.Cu | 150 204.106 180 |
| SW44 | ai_calc:KeyPad_6.0x4.5 | B.Cu | 137.152 204.106 180 |
| SW45 | ai_calc:KeyPad_6.0x4.5 | B.Cu | 124.305 204.106 180 |
| SW46 | ai_calc:KeyPad_5.0x4.0 | B.Cu | 150 119 180 |
| SW47 | ai_calc:KeyPad_5.0x4.0 | B.Cu | 150 131.9 180 |
| SW48 | ai_calc:KeyPad_5.0x4.0 | B.Cu | 156.623 125.563 180 |
| SW49 | ai_calc:KeyPad_5.0x4.0 | B.Cu | 143.377 125.563 180 |
| SW50 | ai_calc:KeyPad_6.0x4.5 | B.Cu | 123.377 120.795 180 |
| TP1 | TestPoint:TestPoint_Pad_D1.5mm | F.Cu | 121 110.4 |
| TP2 | TestPoint:TestPoint_Pad_D1.0mm | F.Cu | 138 86.4 |
| TP3 | TestPoint:TestPoint_Pad_D1.0mm | F.Cu | 140.4 86.4 |
| TP4 | TestPoint:TestPoint_Pad_D1.5mm | F.Cu | 120.6 113.1 |
| TP5 | TestPoint:TestPoint_Pad_D1.5mm | F.Cu | 123.6 82.35 |
| TP6 | TestPoint:TestPoint_Pad_D1.5mm | F.Cu | 140.4 80.3 |
| TP7 | TestPoint:TestPoint_Pad_D1.5mm | F.Cu | 128 84.6 |
| U1 | ai_calc:ESP32-S3-MINI-1 | F.Cu | 127.55 97 90 |
| U2 | Package_TO_SOT_SMD:SOT-23-5 | F.Cu | 135.9 67.5 |
| U3 | Package_TO_SOT_SMD:SOT-23-5 | F.Cu | 122 76.8 |
| U4 | Package_TO_SOT_SMD:SOT-23-5 | F.Cu | 137.4 157 |
| U5 | Package_TO_SOT_SMD:SOT-23-5 | F.Cu | 137.4 160.6 |
| U6 | Package_DFN_QFN:HVQFN-24-1EP_4x4mm_P0.5mm_EP2.6x2.6mm | F.Cu | 126 146.5 |
| U7 | Package_TO_SOT_SMD:SOT-23-6 | F.Cu | 133.6 83.2 |

## Custom footprint library `ai_calc.pretty`

- ESP32-S3-MINI-1
- FPC_24P_P0.5mm_DualContact_C6364666
- FPC_24P_P0.5mm_DualContact_C6364666_CamReversed
- FPC_AFC01-S24FCA-00_24P_P0.5mm_BottomContact
- JST_PH_S2B-PH-SM4-TB_LCSC
- KeyPad_5.0x4.0
- KeyPad_6.0x4.5
- KeyPad_6.0x4.5_H3notch
- KeyPad_7.0x5.5
- KeyPad_9.0x7.0
- L_SMNR4020_4.0x4.0mm
- MX1.25_2P_SMD_RA_H3.6_C7430468
- PinSocket_1x04_P2.54mm_SMD_H5.0_C42379197
- PinSocket_1x04_P2.54mm_SMD_RA_C46061768
- Post_Hole_4.2mm
- Post_Hole_4.4mm
- Post_Slot_4.2x4.45mm
- Post_Slot_4.2x4.65mm
- Post_Slot_4.2x5.0mm
- Post_Slot_4.4x4.8mm
- SOT-323_SI1308EDL
- ScrewBoss_Hole_6.0mm
