niravkumar2008/AI-CALCULATOR/hardware/enclosure/replica/fitcheck_report.md

# Fit check: our PCB in the fx-115ES replica

Generated by `python build_fx115es_replica.py fitcheck` on 2026-10-03 23:25:03. Re-run it after the PCB STEP is regenerated.

| Input | File | Timestamp |
| --- | --- | --- |
| PCB STEP | `hardware/fab/ai_calc_board.step` | **2026-10-03 23:02:16** |
| KiCad board (read only: positions, holes, keep-outs) | `hardware/kicad/ai_calc.kicad_pcb` | 2026-10-03 20:08:08 |

## Placement

- Front-view frame: X = 150 − x_kicad, Y = 138.94 − y_kicad, Z from the outside of the back cover. The board is turned over (180° about Y): F.Cu parts face the back cover, the key pads (B.Cu) face the keys.
- Board key side (B.Cu) at Z = 7.80, back side (F.Cu) at Z = 7.09; free height behind the board to the back floor 6.09 (D4 = 6.0 to the inside of the floor, rev B2). See "Stack-up used" for how the thickness readings were reconciled.
- STEP frame: x_step = x_kicad +0.00, y_step = −y_kicad -0.00, board 0.71 mm thick (KiCad 0.8: our parts sit 0.09 mm closer to the floor in reality); STEP board size matches Edge.Cuts to 0.00 mm.
- Check: 73 STEP parts land 0.00 mm (median) / 2.83 mm (max, model offsets) from their KiCad footprint origins.
- Bodies checked: 153 from the STEP + 3 proxies, against Front shell, Back cover, Keymat, Battery lid, Solar cell (dummy). 312 body pairs had overlapping boxes.

### Parts not in the STEP

- Proxy box: **camera module**, Z 1.69 to 7.09
- Proxy box: **LiPo battery**, Z 3.29 to 7.09
- Proxy box: **e-paper panel (P3)**, Z 7.80 to 8.80
- Not modelled: the magnetic connector (P5 not in hand), wires, solder fillets.

## Collisions (3D)

Depth = the smallest size of the overlap box (how far the parts would have to move apart). Location is the middle of the overlap: front-view X/Y and KiCad x/y. Sorted by depth.

| # | PCB part | Hits | X, Y (front view) | x, y (KiCad) | Z range | Overlap box (mm) | Depth | Volume mm³ | Note |
| --- | --- | --- | --- | --- | --- | --- | --- | --- | --- |
| 1 | J4 (conn-smd_p2.00_s2b-ph-sm4-tb-lf-sn) | Back cover: solar box (1 high) | 8.4, 66.5 | 141.6, 72.5 | 1.50–6.00 | 7.90 × 7.60 × 4.50 | **4.50** (Z) | 33.34 | part bottom Z 1.48, 0.48 above the floor: grind the rib/box |
| 2 | proxy: LiPo battery | Back cover: solar box grid (D13, 5 high) | -1.2, 69.7 | 151.2, 69.3 | 3.29–6.50 | 6.60 × 11.46 × 3.21 | **3.21** (Z) | 69.14 | part bottom Z 3.29, 2.29 above the floor: grind the rib/box |
| 3 | proxy: LiPo battery | Front shell: LR44 cup (D7) | -22.6, 69.7 | 172.6, 69.2 | 5.10–7.09 | 5.42 × 11.50 × 1.99 | **1.99** (Z) | 22.44 |  |
| 4 | proxy: LiPo battery | Front shell: LR44 cup (D7) | -14.0, 69.7 | 164.0, 69.2 | 5.10–7.09 | 5.44 × 11.50 × 1.99 | **1.99** (Z) | 22.44 |  |
| 5 | U3 (sot-23-5) | Back cover: solar box frame (D6, 5.5 high) | 28.0, 63.0 | 122.0, 75.9 | 5.45–6.50 | 2.25 × 1.19 × 1.05 | **1.05** (Z) | 1.68 | part bottom Z 5.45, 4.45 above the floor: grind the rib/box |
| 6 | J3 (hdr-smd_hx-pm2.54-1x4p-tp-yq) | Back cover: solar box grid (D13, 5 high) | 12.5, 72.3 | 137.5, 66.6 | 2.00–6.00 | 1.00 × 2.51 × 4.00 | **1.00** (X) | 6.22 | part bottom Z 2.00, 1.00 above the floor: grind the rib/box |
| 7 | J3 (hdr-smd_hx-pm2.54-1x4p-tp-yq) | Back cover: solar box grid (D13, 5 high) | 12.5, 72.3 | 137.5, 66.6 | 4.13–6.00 | 1.00 × 1.50 × 1.87 | **1.00** (X) | 1.37 | part bottom Z 2.00, 1.00 above the floor: grind the rib/box |
| 8 | D1 (d_sod-123) | Back cover: solar box grid (D13, 5 high) | 20.8, 63.7 | 129.2, 75.2 | 5.75–6.50 | 2.75 × 1.54 × 0.75 | **0.75** (Z) | 1.10 | part bottom Z 5.74, 4.74 above the floor: grind the rib/box |
| 9 | PCB (board) | Front shell: locating post H2 | 19.2, -38.7 | 130.8, 177.6 | 7.09–7.80 | 2.80 × 1.08 × 0.71 | **0.71** (Z) | 0.85 | the board itself |
| 10 | Q2 (sot-23) | Back cover: solar box frame (D6, 5.5 high) | 14.1, 63.2 | 135.9, 75.8 | 5.80–6.50 | 3.00 × 1.58 × 0.70 | **0.70** (Z) | 1.52 | part bottom Z 5.79, 4.79 above the floor: grind the rib/box |
| 11 | PCB (board) | Front shell: locating post H9 | -19.2, -38.9 | 169.2, 177.8 | 7.09–7.80 | 2.47 × 0.69 × 0.71 | **0.69** (Y) | 0.38 | the board itself |
| 12 | J4 (conn-smd_p2.00_s2b-ph-sm4-tb-lf-sn) | Back cover: solar box grid (D13, 5 high) | 7.4, 68.7 | 142.6, 70.3 | 3.62–6.00 | 0.50 × 0.62 × 2.38 | **0.50** (X) | 0.55 | part bottom Z 1.48, 0.48 above the floor: grind the rib/box |
| 13 | J4 (conn-smd_p2.00_s2b-ph-sm4-tb-lf-sn) | Back cover: solar box grid (D13, 5 high) | 9.4, 68.7 | 140.6, 70.3 | 3.62–6.00 | 0.50 × 0.62 × 2.38 | **0.50** (X) | 0.55 | part bottom Z 1.48, 0.48 above the floor: grind the rib/box |
| 14 | J4 (conn-smd_p2.00_s2b-ph-sm4-tb-lf-sn) | Back cover: solar box frame (D6, 5.5 high) | 5.7, 63.0 | 144.3, 75.9 | 4.15–6.50 | 0.50 × 0.71 × 2.35 | **0.50** (X) | 0.81 | part bottom Z 1.48, 0.48 above the floor: grind the rib/box |
| 15 | J4 (conn-smd_p2.00_s2b-ph-sm4-tb-lf-sn) | Back cover: solar box frame (D6, 5.5 high) | 11.1, 63.0 | 138.9, 75.9 | 4.15–6.50 | 0.50 × 0.71 × 2.35 | **0.50** (X) | 0.81 | part bottom Z 1.48, 0.48 above the floor: grind the rib/box |
| 16 | J4 (conn-smd_p2.00_s2b-ph-sm4-tb-lf-sn) | Back cover: solar box frame (D6, 5.5 high) | 11.5, 63.0 | 138.5, 75.9 | 4.46–6.50 | 0.35 × 0.71 × 2.04 | **0.35** (X) | 0.51 | part bottom Z 1.48, 0.48 above the floor: grind the rib/box |
| 17 | PCB (board) | Front shell: locating post H6 | 19.4, -46.2 | 130.6, 185.1 | 7.09–7.80 | 1.80 × 0.31 × 0.71 | **0.31** (Y) | 0.10 | the board itself |
| 18 | proxy: camera module | Back cover: upper rib B (1 high) | 0.0, 43.9 | 150.0, 95.1 | 1.69–2.00 | 8.50 × 1.04 × 0.31 | **0.31** (Z) | 2.64 | part bottom Z 1.69, 0.69 above the floor: grind the rib/box |
| 19 | J4 (conn-smd_p2.00_s2b-ph-sm4-tb-lf-sn) | Back cover: solar box frame (D6, 5.5 high) | 5.3, 63.0 | 144.7, 75.9 | 4.46–6.50 | 0.25 × 0.71 × 2.05 | **0.25** (X) | 0.36 | part bottom Z 1.48, 0.48 above the floor: grind the rib/box |
| 20 | J4 (conn-smd_p2.00_s2b-ph-sm4-tb-lf-sn) | Back cover: solar box frame (D6, 5.5 high) | 7.4, 63.3 | 142.6, 75.6 | 3.65–4.04 | 0.40 × 0.21 × 0.40 | **0.21** (Y) | 0.02 | part bottom Z 1.48, 0.48 above the floor: grind the rib/box |
| 21 | J4 (conn-smd_p2.00_s2b-ph-sm4-tb-lf-sn) | Back cover: solar box frame (D6, 5.5 high) | 9.4, 63.3 | 140.6, 75.6 | 3.65–4.04 | 0.40 × 0.21 × 0.40 | **0.21** (Y) | 0.02 | part bottom Z 1.48, 0.48 above the floor: grind the rib/box |

## Clearances at board height (2D, exact)

Negative = overlap. Holes: radial clearance between the KiCad hole and the replica post (post positions from calipers C8/C9/C10/C15, the rest from photos).

| Board feature | Shell feature | Clearance mm | Note |
| --- | --- | --- | --- |
| hole H2 Ø4.2 | locating post H2 Ø2.90 | **-0.54** | hole centre 1.19 from the post |
| hole H9 Ø4.2 | locating post H9 Ø2.90 | **-0.29** | hole centre 0.94 from the post |
| hole H6 Ø4.2 | locating post H6 Ø2.90 | **-0.11** | hole centre 0.76 from the post |
| hole H13 Ø4.2 | locating post H13 Ø2.90 | 0.01 | hole centre 0.64 from the post |
| hole H14 Ø4.2 | locating post H14 Ø2.90 | 0.11 | hole centre 0.54 from the post |
| hole H4 Ø4.2 | locating post H4 Ø2.90 | 0.53 | hole centre 0.12 from the post |
| hole H10 Ø4.2 | locating post H10 Ø2.90 | 0.58 | hole centre 0.07 from the post |
| hole H8 Ø4.2 | locating post H8 Ø2.90 | 0.59 | hole centre 0.06 from the post |
| hole H1 Ø6.0 | screw post mid R Ø3.85 | 0.91 | hole centre 0.17 from the post |
| hole H3 Ø6.0 | screw post mid L Ø3.85 | 0.91 | hole centre 0.17 from the post |
| board edge near (28.5, -71.6) | front-shell inner skin (outside it = wall) | 1.35 | KiCad (121.48, 210.53) |

## Display

- E-paper glass (P3 59.0 × 29.2) centre 0.03, 45.95 vs window (C12 60.65 × 24.30) centre 0.00, 45.95: offset 0.03, 0.00.
- The window is 1.65 mm wider than the glass: 0.82 mm of board shows at each end unless masked.

Side-wall stubs, wire holders and the inner rib end at Z 8.00, 0.20 above the board's key side (Nirav: they stop above the board plane), so they are not board-edge clearances any more; parts on the key side under them are in the 3D table.

## Compared with `hardware/fitcheck/clearance_table.md` (PCB agent)

That table assumes a 4.0 / 4.5 / 5.5 free height ("design" column 4.5) and adds a rib's height to the part height whenever a rib is within 1.5 mm. This report uses exact 3D overlap with the photo rib positions and 6.09 free height (D4 = 6.0 to the inside of the floor). Rows where the two disagree, or that they flag:

| Part | Their height | Their margin @4.5 | Their margin after grind | Here: overlap | Here: part bottom above the floor | Agree? |
| --- | --- | --- | --- | --- | --- | --- |
| J4 | 5.50 | -6.50 | -1.00 | 4.50 (Back cover: solar box (1 high)) | 0.48 | yes |
| J3 | 5.00 | -6.00 | -0.50 | 1.00 (Back cover: solar box grid (D13, 5 high)) | 1.00 | yes |
| U3 | 1.55 | -2.55 | 2.95 | 1.05 (Back cover: solar box frame (D6, 5.5 high)) | 4.45 | yes |
| U2 | 1.55 | -2.55 | 2.95 | none | 4.54 | no |
| D1 | 1.26 | -2.26 | 3.24 | 0.75 (Back cover: solar box grid (D13, 5 high)) | 4.74 | yes |
| Q2 | 1.20 | -2.20 | 3.30 | 0.70 (Back cover: solar box frame (D6, 5.5 high)) | 4.79 | yes |
| D7 | 0.99 | -1.99 | 3.51 | none | 5.10 | no |
| C6 | 0.79 | -1.79 | 3.71 | none | 5.30 | no |
| C5 | 0.79 | -1.79 | 3.71 | none | 5.30 | no |
| R2 | 0.34 | -1.34 | 4.16 | none | 5.75 | no |
| R4 | 0.34 | -1.34 | 4.16 | none | 5.75 | no |
| D2 | 1.26 | -0.76 | 1.24 | none | 4.83 | no |
| C16 | 0.49 | 0.01 | 2.01 | none | 5.60 | no |

- Camera: not in their table (it is a separate module). Here: 0.31 overlap with upper rib B (1 high), bottom 0.69 above the floor.
- Free height: their design value 4.5 came from reading D4 to the outside of the back; Nirav has since said D4 = 6.0 is to the inside face, so their "optimistic 5.5" column is the closest, and with 6.0 every part that only clashes with the floor clears it (J4 bottom 0.48, J3 bottom 1.00 above the floor, from the STEP models).

## Stack-up used

**How the thickness readings fit together (rev B2, Nirav's answers).** D4 = 6.0 is from the board's back (component, F.Cu) face to the *inside* of the back cover; D1 = 5.5 is from the front shell's *rim* (parting line) down to that same face. Stack at the top part: floor 1.0 (D5) + 6.0 (D4) + board 0.8 + 4.0 front side = 11.8 (D10 11.8); at the keys 3.5 front side gives 11.3 (D10 11.3). Parting line at Z 1.5. Cross-checks: D3 (board line to the outside at the top edge, "about 5") = 4.8; photo 871567b6: the LCD shield (D8 3.75 under a 1.2 plate) ends at Z 6.80, level with the Casio board's back face (Z 7.0).

| Z (mm) | What |
| --- | --- |
| 0 – 1.0 | back cover floor (D5) |
| 1.0 – 5.0 | rings (D13: 4 high); rib grid and lower ribs 1 high; solar box grid to 6.0, frame to 6.5 (D13, D6) |
| 7.0 – 7.8 | PCB (F.Cu parts below, towards the back) |
| 7.8 – 9.6 | keymat sheet + domes (D9) |
| 10.1 / 10.6 | front plate underside, keypad / screen section |
| 11.3 / 11.8 | face, keypad / screen section (D10) |

## Before / after: `fitcheck_report_stage11.md` vs this run

STEP 2026-10-03 18:10:31 (before) vs 2026-10-03 23:02:16 (now). Depth = worst overlap per part and shell feature (mm).

| PCB part | Shell feature | Before | Now | Status |
| --- | --- | --- | --- | --- |
| J4 | Back cover: solar box + floor | 4.50 | **4.50** | same |
| proxy: LiPo battery | Back cover: solar box grid | 3.21 | **3.21** | same |
| proxy: LiPo battery | Front shell: LR44 cup | 1.99 | **1.99** | same |
| U3 | Back cover: solar box frame | 1.05 | **1.05** | same |
| J3 | Back cover: solar box grid | 1.00 | **1.00** | same |
| D1 | Back cover: solar box grid | 0.75 | **0.75** | same |
| PCB | Front shell: screw post mid R | 0.71 | - | **gone** |
| PCB | Front shell: locating post H2 | 0.71 | **0.71** | same |
| Q2 | Back cover: solar box frame | 0.70 | **0.70** | same |
| PCB | Front shell: locating post H9 | 0.69 | **0.69** | same |
| J4 | Back cover: solar box grid | 0.50 | **0.50** | same |
| J4 | Back cover: solar box frame | 0.50 | **0.50** | same |
| PCB | Front shell: locating post H6 | 0.31 | **0.31** | same |
| proxy: camera module | Back cover: upper rib B | 0.31 | **0.31** | same |

2D clearances at board height (negative = overlap; worst value per item, only items below 0.3 mm):

| Item | Before | Now | Status |
| --- | --- | --- | --- |
| hole H2 | -0.54 | -0.54 | still overlaps |
| hole H9 | -0.29 | -0.29 | still overlaps |
| hole H6 | -0.11 | -0.11 | still overlaps |
| hole H1 | -0.06 | 0.91 | **ok now** |
| hole H13 | 0.01 | 0.01 | ok |
| hole H14 | 0.11 | 0.11 | ok |
