niravkumar2008/AI-CALCULATOR/hardware/enclosure/replica/photo_notes.md

# Photo notes for the fx-115ES replica

Nirav's 23 photos (uploads/60646b63-...). What each one shows and what the model takes from it.
Calipers override photos.

| Photo | Shows | Used for |
|---|---|---|
| 050df9b7 | back cover inside, top half | battery: a round LR44 opening (with a cross-shaped key notch) inside a recessed rounded-rectangle pad at the top-left (back view), not a separate door; ribbed box (4 x 2 cells) behind the solar cell top-right; 2 short ribs ("ticks") perpendicular to each long side wall, in pairs, every ~20 mm; 6 screw holes; two "x" marks between the rings |
| 132b4559 | bare Casio board + LCD | board is a plain rectangle with 2 half-round notches on the bottom edge; LCD glass sits above the board's top edge, joined by a flex; front shell is light grey/silver; the LR44 holder is a round cup fixed in the front shell top corner |
| 25490985 | front shell inside, one long side wall beside the screen | the "4.7 mm wall" (C4) is NOT solid: it is the outer skin plus a parallel inner rib with a ~2 mm channel between them where the solar/battery wires run. Three round horizontal pins (~1.5 mm dia, ~3 mm long) stick inward from the rib at mid-height = the "stubs". A rectangular rib frame surrounds the LCD. Small hook (wire holder) near the top = C4's 5.5 mm bit |
| 27bff2c8 | back cover inside + front shell with board, side by side | back cover is dark navy, front shell silver-grey; solar cell top-right and LR44 cup top-left (front view); the big ring sits over the board's black chip blob; lower ribs + long centre rib as in stage 10 |
| 28bb9c4b | loose rubber keymat, contact side | the mat is a plain grey RECTANGLE about the size of the Casio board (not case-shaped), with 2 half-round notches on one short edge (bottom screw posts), round post holes between keys, one round dome per key (5 big per number row, 6 small per function row), REPLAY = 4 small domes + 2 side clips. Model: mat outline = board rectangle |
| 32a2eea0 | duplicate of 25490985 (same file) | - |
| 4e287737 | whole calculator, front (branding NOT copied) | silver front face; all key caps dark grey (number keys bigger), SHIFT/ALPHA/MODE/ON ovals, REPLAY a grey round pad with 4 dark dots; display window has a darker grey bezel band around the LCD; solar cell top-right; the NAVY back cover shows along the lower half of both long sides -> the parting line is not flat (the back cover's side walls rise higher in the keypad section) - check side photos |
| 60c961e7 | board with LCD module + loose mat (key side) | LCD is a metal-framed module above the board top edge; mat is a rectangle with 2 bottom notches, round holes for posts |
| 66bb7a5f | front shell inside, top corner with LR44 cup | round LR44 cup (~12.5 mm inside) with spring-clip slots just under the corner screw post; 3 side-wall pins confirmed; outside of the long side shows a step/band along the side (consistent with a rail for the slide cover) |
| 76dd27d2 | front shell inside, whole | every key opening has a low raised collar on the inside; a full-width rib runs between every key row below the REPLAY rows; locating/screw posts sit ON those ribs; the oval-key/REPLAY area has its own frame; display window has an inner frame rib; solar window + LR44 cup above the display. Key openings are rounded rectangles (number keys slightly barrel-shaped) |
| 7c6e8116 | front shell inside, top half + LCD + solar cell | solar cell (~34 x 11) sits in its own through-window in a rib frame top-right (front view); LCD window has a deep rib frame; a cross rib separates display from keys; small hooks/pins on both side walls in the screen section; oval openings and the REPLAY opening have collars; posts sit on row ribs |
| 84e63d95 | back cover inside, whole | the back cover is a TRAY with real side walls (several mm tall), not a flat plate; pairs of short ribs on the inside of both long walls (about 7 pairs per side); upper rib grid in the screen section is LOW (thin ridges); keypad ribs, the small ring (with a rib through it) and the big ring are taller; 6 screw holes; ribbed box top-right (inside view = top-left... see note) |
| 921b4503 | front face, top half, LCD removed | display window sits in a wide (~3 mm) recessed bezel whose outer edge slopes down (bevelled), the window is a plain through-opening; solar window is a separate through-opening (cell behind it); the oval keys and REPLAY have a shallow dished/countersunk ring in the face; face is flat; top edge well rounded |
| 9f31444b | same corner as 66bb7a5f (closer) | pins are horizontal round pins (~1.5 mm dia, ~3 mm) pointing inward from the wall, at about mid-height, 3 per side, ~10 mm apart; wires run in the gap between the outer skin and a thin inner rib |
| aa09fe8a | front face, keypad, keys removed | key openings are NOT plain rounded rectangles: straight top edge with small corners, bottom corners much rounder (a "tab"/U shape) for both number and function keys; SHIFT/ALPHA/MODE/ON openings are ellipses; REPLAY opening round; thin bevel round each opening |
| dc7abe75 | mat lying on the board, key side | mat = rectangle the size of the board with 2 bottom notches; post holes line up with board holes |
| e82c982d | front shell inside + back cover OUTSIDE | back is flat navy; the battery opening is a round hole with a key notch, top-left in front view, sitting in a shallow rectangular recess (no separate door in the photo: lid missing, or a sticker?); screw holes: 2 top corners, 2 bottom, and a row of THREE at the REPLAY level (the 2 mid screws + a centre hole over the small ring); small round bumps near the corners look like feet |
| faf9599f | side wall pins, other side | same 3 pins + wire channel on the other long side |
| 88e03c27 | front shell (outside) next to back cover (inside) | the traced silhouette (fx115es_outline.json) is the BACK COVER. Together with 4e287737 (navy visible along the lower sides and the bottom) this says the back cover is a tray whose side walls come up round the front shell in the keypad section, and the front shell is slightly smaller there |

## Conclusions used in the model
1. Back cover = tray, outline = traced silhouette at 161 x 79.3 (C3). Front shell = the same outline, flush at the top and screen section, inset 0.9 mm per side below the screen (0.8 tray wall = C5, plus 0.1 gap) and 1.1 mm at the bottom end (gives exactly C1 = 159.9). Tray wall height is a guess (no side photo).
2. The 4.7 mm "wall" beside the screen (C4) = 1.2 skin + ~2.5 mm wire channel + 1.0 inner rib, with 3 horizontal pins per side.
3. Key openings: tab shape (small top corners, big bottom corners); SHIFT/ALPHA/MODE/ON ellipses; thin bevel on top; collars + full-width row ribs underneath.
4. Display: bevelled recessed bezel, lens in it. Solar: separate through-window with a cell behind it.
5. Keymat: board-sized rectangle with 2 notches.
6. Back: battery = round hole (with notch) in a shallow rectangular recess, lid modelled as a thin plate (guess); 7th hole in the centre over the small ring; low ribs in the screen section, tall ones in the keypad section; pairs of short ribs on the inside of the side walls.
7. Colours: silver front, navy back, dark grey keys.

## Batch 2 (2026-10-03, uploads/0abf7810-...)

| Photo | Shows | Used for |
|---|---|---|
| e59eff71 | whole calculator front, straight on, calipers along the length (159.8) (branding NOT copied) | confirms C1; long sides straight, top corners ~5 mm radius, larger bottom corners; screen section full width, navy tray visible along the keypad sides; bezel = lighter recessed band; solar window shows 4 cell segments |
| 2a97120d | front shell inside with the keymat in place | the 8 post rows (corner screws, mid screws, H8/H10 pair, single H4, H2/H9 pair, single H6, H13/H14 pair, bottom screws) = C15 mapping; locating posts are white tubes (bore); 3 stubs per side beside the window at Y ≈ 37 / 47.5 / 56 and a hook-shaped wire holder near the window's bottom corners (Y ≈ 26); LR44 cup with a frame and the solar-window frame at the top |
| fd923128 | Casio board (back side) + LCD module (white block) | LCD module about 68 wide (fits between the stub tips, 68.4), 3.75 thick (D8); board holes as before |
| fb0c138c | Waveshare 2.13" e-paper HAT | not shell-related (ignored) |
| 050df9b7 (re-read) | back cover inside, top half | the battery hole sits in a low pad, no tall rib round it, so the D7 "coin-cell holder rib" (5-6) is the cup in the front shell; solar box = 4 x 2 cells, clearly taller than the low rib grid |

### Rev B conclusions
1. Stack-up: D1 and D4 are both to the outside faces (5.5 + 0.8 + 5.5 = 11.8 = D10 top part).
2. Posts from calipers: C9 (68.1), C8 (46.5, 42.3), C10 (39), C15 rows read to the far edge of each post's hole.
3. The trace's top corners were too soft for C9 + C11 + C15; straightened sides up to Y 77 (about a 5 mm corner), matching e59eff71.
| 871567b6 | front shell inside with the real Casio board and the LCD module (metal shield) in place | the side-wall clips flank the LCD and stop above the board plane (stubs modelled down to Z 8.0); LCD shield back roughly level with the board's back face, which fits D8 3.75 under a 1.2 plate (LCD 6.8 to 10.55, board back 7.0); every post passes through the board; coin-cell holder and solar window frame as modelled |

## Rev C / C2 re-read (2026-10-05): split line, silver vs navy, side walls, grooves, case

Every photo looked at again for the split line, the silver faceplate vs the navy back cover, side profiles, rail
grooves and the slide case. Side-by-side photo/CAD comparisons: `../final_assembly/renders/compare/cmp_*.jpg`.

| Photo | What it shows about the body split / sides / case |
| --- | --- |
| 4e287737 | front: silver face; navy shows round the silver along both long sides from about the 3rd function row (~Y 0) down and along the bottom end, widening downwards: the navy cover wraps the keypad section |
| e59eff71 | front with calipers (159.8): same navy band on the keypad sides only; screen section all silver to the edge; top corners ~5 mm, bottom end curved. No groove visible from the front |
| 3d608fdb | knock-off listing (different product, no sizes taken): same look, silver face inside a navy back that wraps the keypad sides and bottom; "sliding hard cover" icon |
| 88e03c27 | silver part (outside) next to the navy back cover (inside): the cover's long walls are low in the top third and become tall/thick from about the small ring down; the cover outline = traced silhouette |
| e82c982d | silver part inside + navy cover outside: silver part has deep walls round the screen section only; keypad section edges are a thin rim (faceplate); snap clips ("III") mid top and mid bottom; flat navy back |
| 478afcb6 | navy cover inside + silver part with mat: navy walls rise from about the double ticks / small ring; silver keypad edges thin with a step line along both sides |
| 2f54d6c7 | navy cover inside (best view): screen-section walls are a low rim, then the walls thicken/rise at about 51 mm below the top and stay tall to the bottom, incl. the curved bottom end wall; wall ticks in pairs |
| 84e63d95 | navy cover inside, angled: confirms the low rim at the top and tall long walls + tall bottom wall in the keypad section (no separate inner lip there) |
| 050df9b7 | navy cover top half: low walls in the screen section, the right wall starts to rise below the double ticks |
| 27bff2c8 | navy cover inside + silver part with board: silver keypad-section sides narrower than the screen section (waist); deep silver walls only round the LCD |
| 7c6e8116 | silver part inside, top half: deep walls with clips round the screen; from just under SHIFT/ALPHA a long thin ledge runs down both keypad sides = where the silver steps in and the navy wall takes over |
| 76dd27d2 | silver part inside, whole: keypad section is a faceplate (collars, row ribs, posts) with a low edge; the deep walls end at the oval-key row |
| 2a97120d | silver part inside with mat: same; tall top wall at the display end (the magnet U-notch goes there), clips mid top and mid bottom |
| 871567b6 | silver part with board + LCD: deep silver walls in the screen section reach the board plane; keypad edges low |
| 921b4503 | face, top half: bevelled bezel recess (sharp top edge, sloped lower edge), separate solar through-window; the face edge is a smooth round-over, no groove on the face side |
| aa09fe8a | face, keypad: tab-shaped key openings, oval SHIFT/ALPHA/MODE/ON, round REPLAY; side edges plain |
| 66bb7a5f | silver top corner inside: LR44 cup, pins; the "band along the side" noted before is the glass table edge, NOT a groove |
| 9f31444b | same corner closer: pins, wire channel; outer side of the silver wall plain |
| faf9599f | other side's pins + wire channel; outer side plain |
| 25490985 / 32a2eea0 | (duplicates) screen-section wall = skin + wire channel + inner rib, clips; no outside detail |
| 0103f1dd | bare Casio board + LCD + mat (no shell info) |
| 132b4559 | board + LCD + loose mat on the silver part (no side info) |
| 28bb9c4b / 6996fcbd | key mat, both sides (no shell info) |
| 60c961e7 / dc7abe75 | board + LCD + mat (no shell info) |
| fd923128 | Casio board + LCD module (no shell info) |
| fb0c138c | Waveshare e-paper HAT: ignored for the shell |

**Conclusions used in rev C2:**
1. Two body parts, as Nirav says: a **silver faceplate** that is deep only in the screen section (and forms the top
   wall, so the magnet U-notch stays in it), and a **navy back cover** whose walls rise along a ramp (small ring ->
   big ring, Y 31 -> 8) to 9.8 and form the side walls round the keypad and the bottom end. The silver part steps in
   0.95 there (navy band visible from the front) and has only a short skirt (to Z 8.3, guess) inside the navy wall.
2. **No photo shows a rail groove** or the slide case itself. The groove in the model is a placeholder guess
   (questions 2-4 in `hardware/QUESTIONS_AND_ISSUES.md`).
3. Not modelled: the slight waist of the keypad-section sides. (The snap clips mid top / mid bottom: modelled in rev D, below.)
## Rev D re-read (2026-10-05 evening): faceplate details

Photos e82c982d (silver part flat on the table, inside up), 2a97120d (inside, with the mat), 2f54d6c7 (navy cover inside),
cropped and compared with `../final_assembly/renders/compare/cmp_faceplate_inside_e82c982d.jpg`.

| Feature | What the photos show | Rev D model |
| --- | --- | --- |
| LR44 holder (top-left in front view) | not a plain ring: a round cup open on its left and right sides (spring-clip slots), an I-shaped bar either side joined to the ring ends by short lugs (holder ~21 x 14), a bar across the cup with the contact clip on it | cup Ø12.4 + 0.8 wall, **D7 5.5 tall (unchanged)**, 4.0 gaps left/right, I-bars at ±9.0 (1.0 thick, 14 long, 2.6 flanges), lugs 0.8, contact rib 0.8 wide x 1.2 tall at +1.5. **Not ground any more** (stage 14: the LiPo lies on the back floor) |
| Comb snap tabs | mid top and mid bottom of the silver part: a block of 3 teeth ("III"), the top one ~9-11 wide just right of centre (front view), standing proud of the rim; the bottom one ~7 wide | 3 teeth each (1.0 gaps). Top: 1.6 deep, down to Z 1.1 (0.4 below the rim) into a notch in the navy lip (0.2 clearance). Bottom: hang inside the navy end wall (0.3 from it) down to Z 2.4 |
| Navy mating features | 2f54d6c7: a small lighter block on the top rim (~7 wide, right of centre) and a low block at the foot of the bottom end wall (~9 wide) | top: the lip notch; bottom: catch block 0.7-1.9 in from the outline, up to Z 2.2 (0.2 under the teeth). The hook/barb itself is not modelled |
| Side clips (screen section) | per side: 3 round pins + 3 wire hooks: one at the solar-window level (Y ~63.5), one at the window's top edge (Y ~58), one near the window's bottom corner (Y ~26-27, the C4 holder) | pins unchanged (C14, Y 37.3/47.5/56.0; photo re-read 36.6/47.4/54.7); hooks = arm to the C4 5.5 depth + a 1.6 return leg (towards the top for the upper two, down for the C4 one) |
| Key collars | a clear raised rim round every opening | 0.25-0.75 from the edge, **0.8 tall** (was 0.5, and the rings had not actually been built: only the webs between keys). REPLAY rim 0.35 (its direction domes sit under it) |
| Row ribs | full-width ribs between rows with small round beads between the columns; one more rib under the last row, just above the bottom screw bosses | beads Ø1.4 at the column gaps; extra rib midway between the last row and the bottom screws |
| Posts | screw posts = round bosses with a pilot hole (corner, mid, bottom); locating posts = thin pins with small star/crush ribs at the plate | screw posts unchanged; 4 crush ribs per locating post (0.5 wide, 0.6 past the post, 0.9 tall at the plate) |
