niravkumar2008/AI-CALCULATOR/firmware-v15-lcd/PORT_NOTES.md

# Port notes: v14 e-paper firmware → v15-LCD (2026-10-08)

Rules followed: `firmware-prototype/` (v14) and `core/` were **not modified** (`pio run` in
`firmware-prototype` still gives RAM 30.7 %, flash 63.4 %, byte-identical numbers to before; core tests
not re-run because core/ is untouched). Nothing committed. No API key anywhere. No eFuse touched.

## Build result

| Project | RAM | Flash (1.9 MB OTA slot) |
| --- | --- | --- |
| `firmware-v15-lcd` (`env:v15lcd`) | **28.8 %** (94,396 B) | **68.3 %** (1,343,269 B) (after the 2026-10-10 UI fixes; was 94,372 B / 1,336,201 B) |
| `firmware-prototype` (v14, unchanged) | 30.7 % (100,440 B) | 63.4 % (1,245,549 B) |

LovyanGFX 1.2.32 adds ~90 KB of flash over GxEPD2; internal RAM went *down* because the 320x170 canvas
lives in PSRAM and the e-paper library's buffers are gone. No compiler warnings from `src/`.
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
