niravkumar2008/AI-CALCULATOR/hardware/enclosure/final_assembly/renders/grind/overview_back_cover_after.png

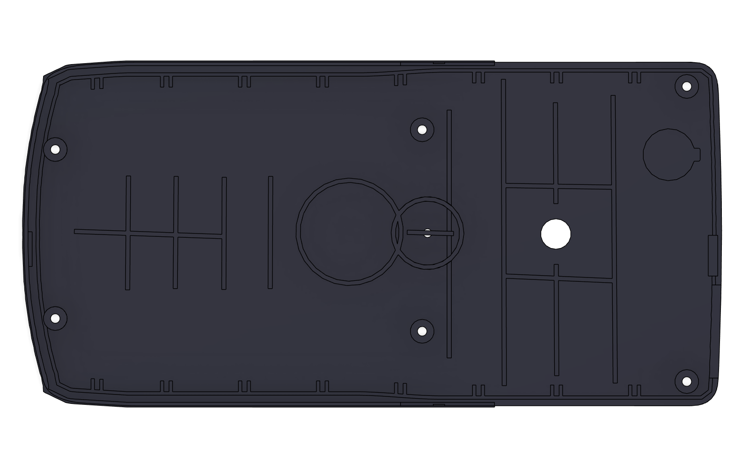
hardware/enclosure/final_assembly/renders/grind/overview_back_cover_after.png
