niravkumar2008/AI-CALCULATOR/hardware/enclosure/final_assembly/renders/grind/overview_faceplate_after.png

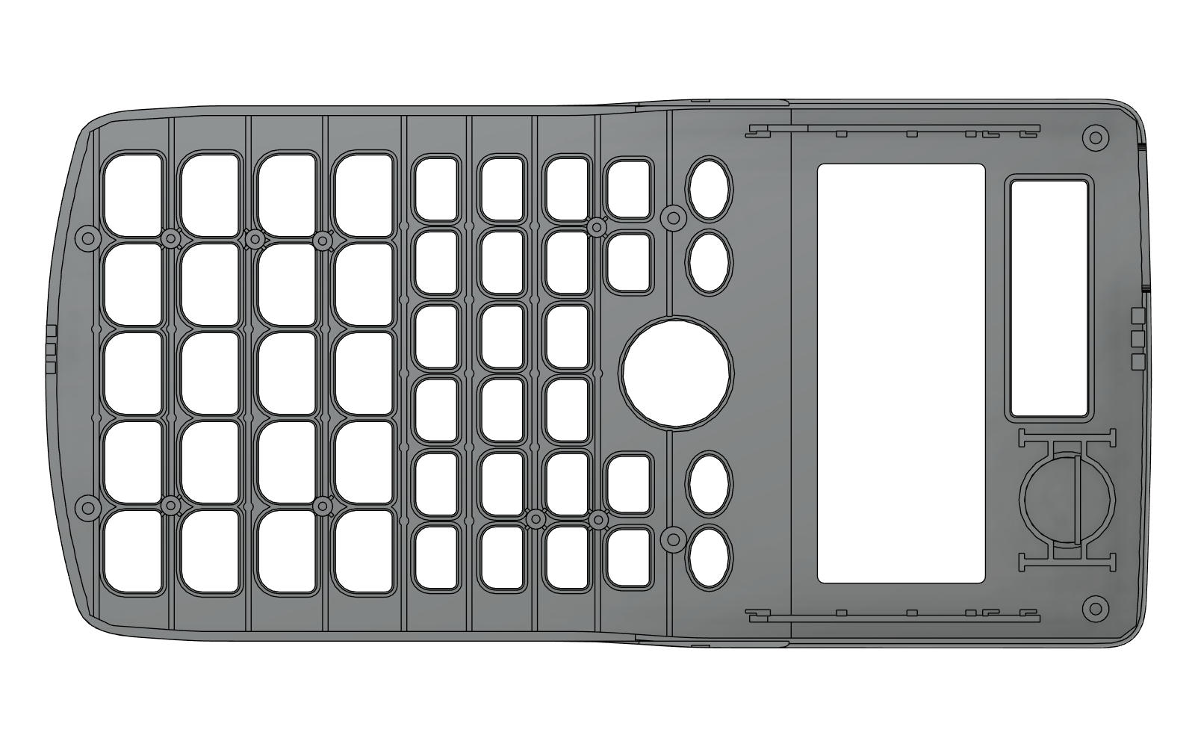
hardware/enclosure/final_assembly/renders/grind/overview_faceplate_after.png
