niravkumar2008/AI-CALCULATOR/hardware/enclosure/final_assembly/renders/photos/epaper_hat.jpg

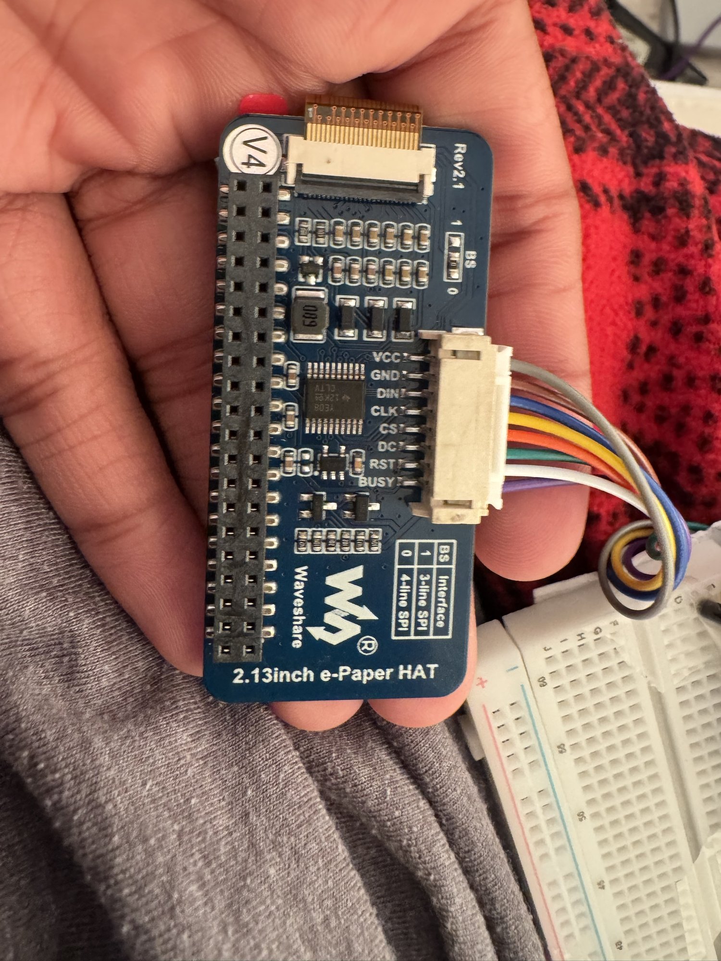
hardware/enclosure/final_assembly/renders/photos/epaper_hat.jpg
