niravkumar2008/AI-CALCULATOR/hardware/enclosure/final_assembly/renders/steps/s05a_epaper_fold.png

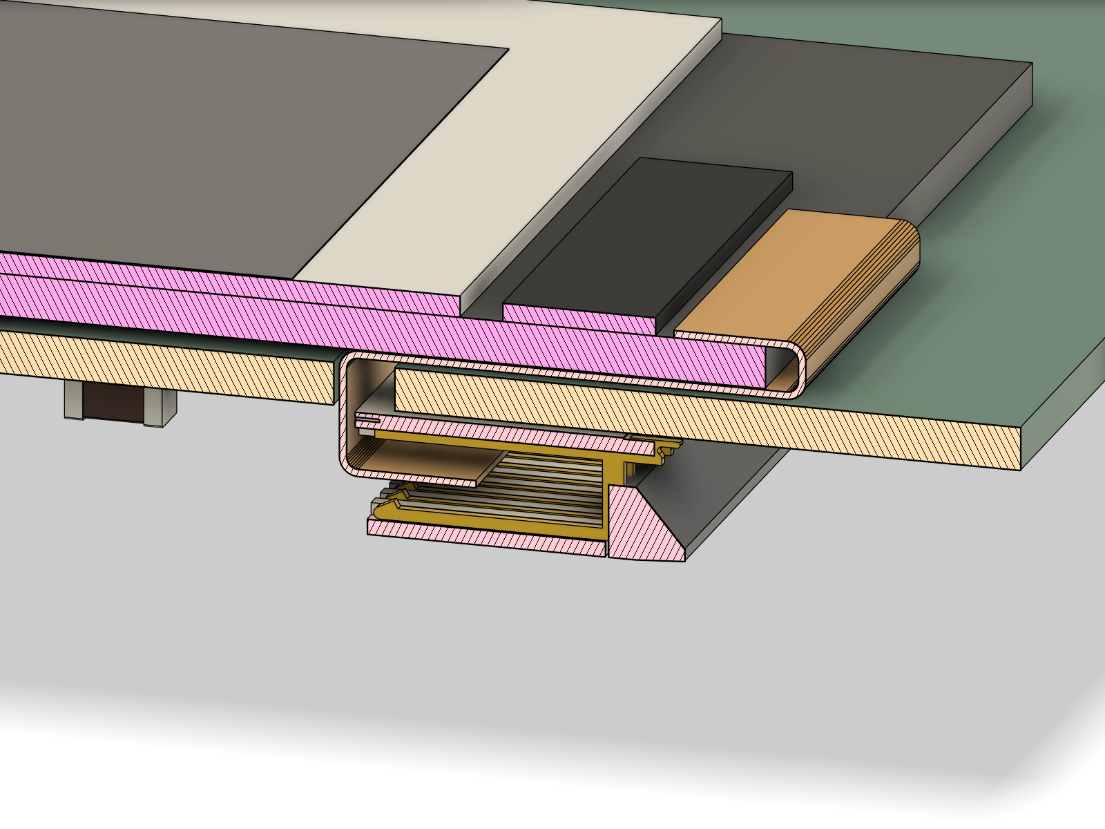
hardware/enclosure/final_assembly/renders/steps/s05a_epaper_fold.png
