niravkumar2008/AI-CALCULATOR/hardware/enclosure/final_assembly/renders/steps/s05b_epaper_j2_ann.png

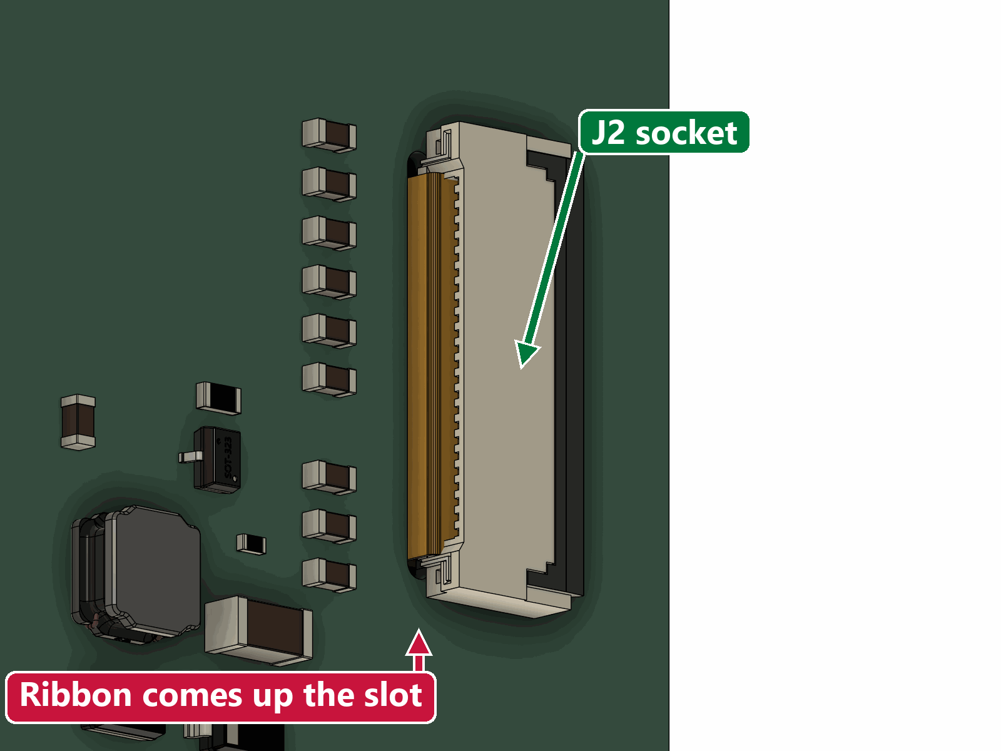
hardware/enclosure/final_assembly/renders/steps/s05b_epaper_j2_ann.png
