niravkumar2008/AI-CALCULATOR/hardware/enclosure/final_assembly/renders/steps/s05c_epaper_on_board.png

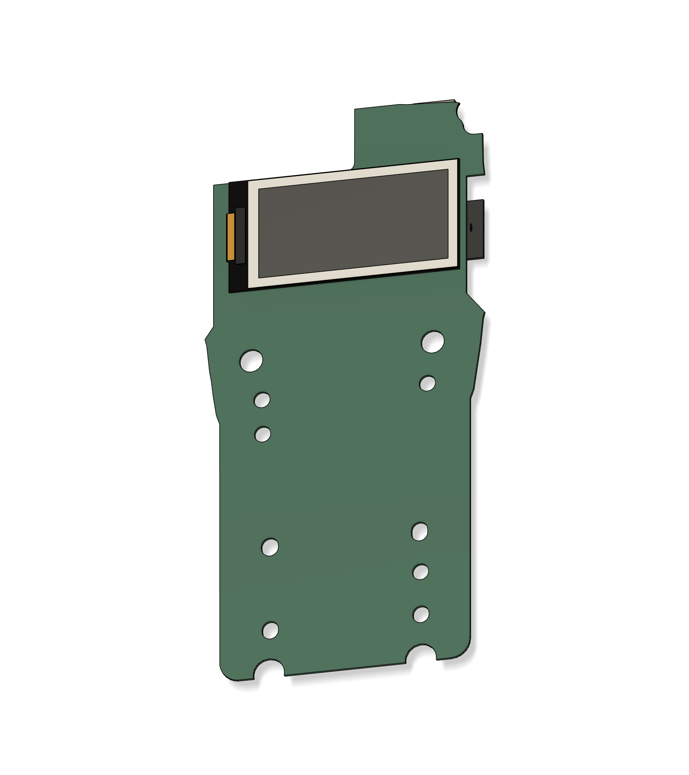
hardware/enclosure/final_assembly/renders/steps/s05c_epaper_on_board.png
