niravkumar2008/AI-CALCULATOR/hardware/enclosure/renders/front.png

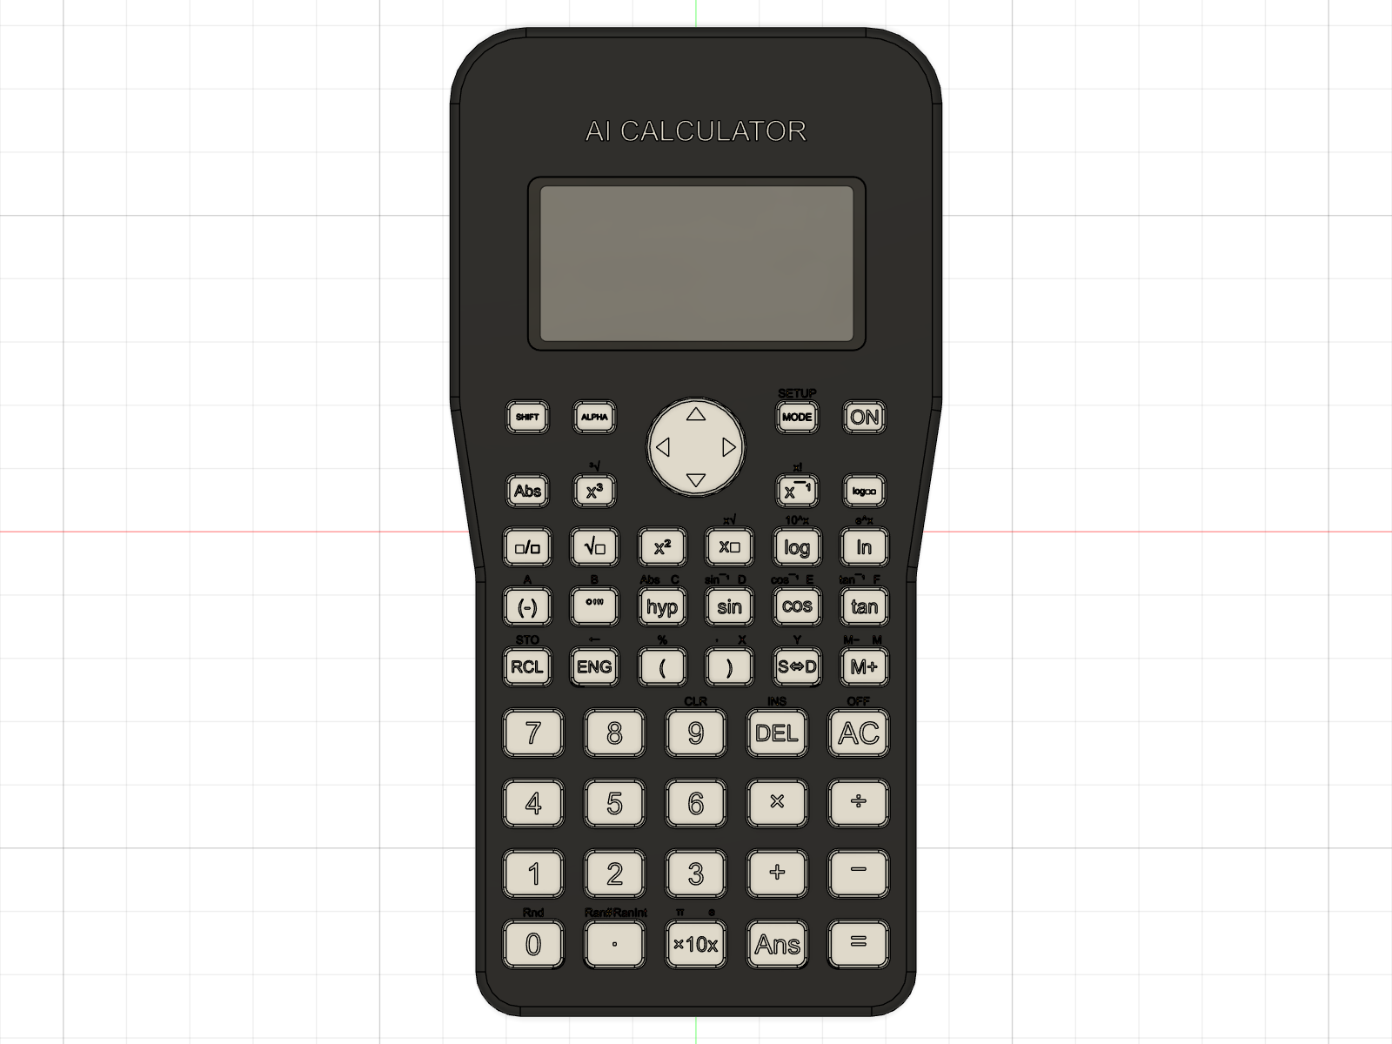
hardware/enclosure/renders/front.png
