niravkumar2008/AI-CALCULATOR/hardware/enclosure/renders/section_left.png

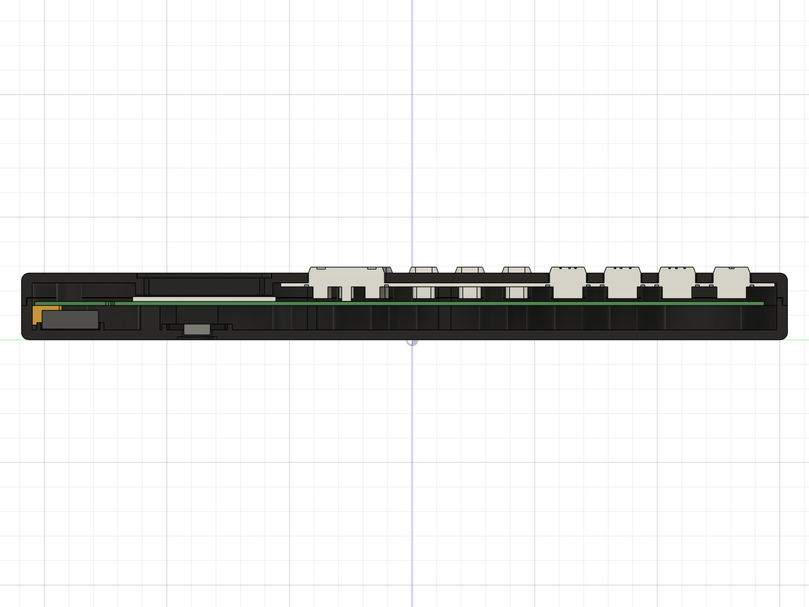
hardware/enclosure/renders/section_left.png
