niravkumar2008/AI-CALCULATOR/hardware/enclosure/renders/side.png

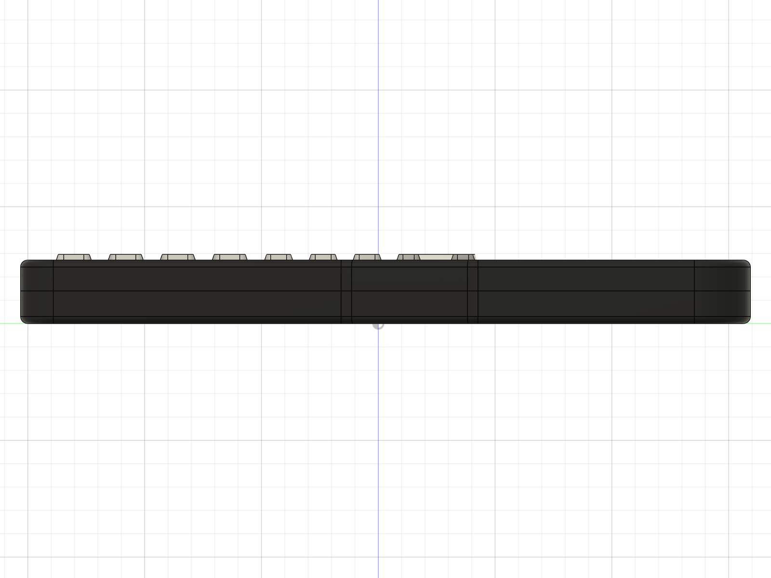
hardware/enclosure/renders/side.png
