niravkumar2008/AI-CALCULATOR/hardware/enclosure/replica/renders/closeup_top_0.png

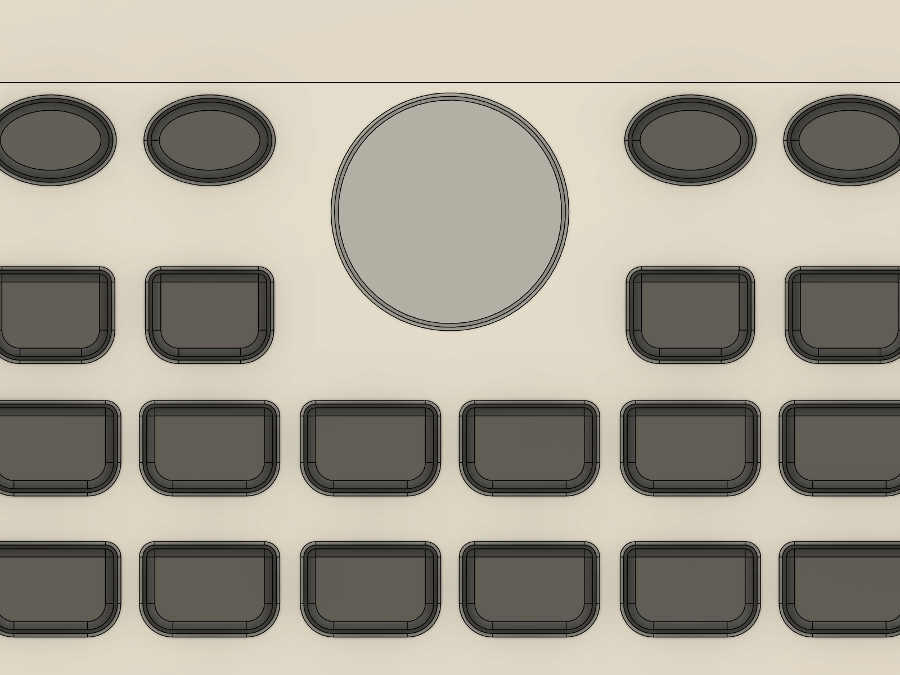
hardware/enclosure/replica/renders/closeup_top_0.png
