niravkumar2008/AI-CALCULATOR/hardware/enclosure/replica/renders/exploded_iso_back.png

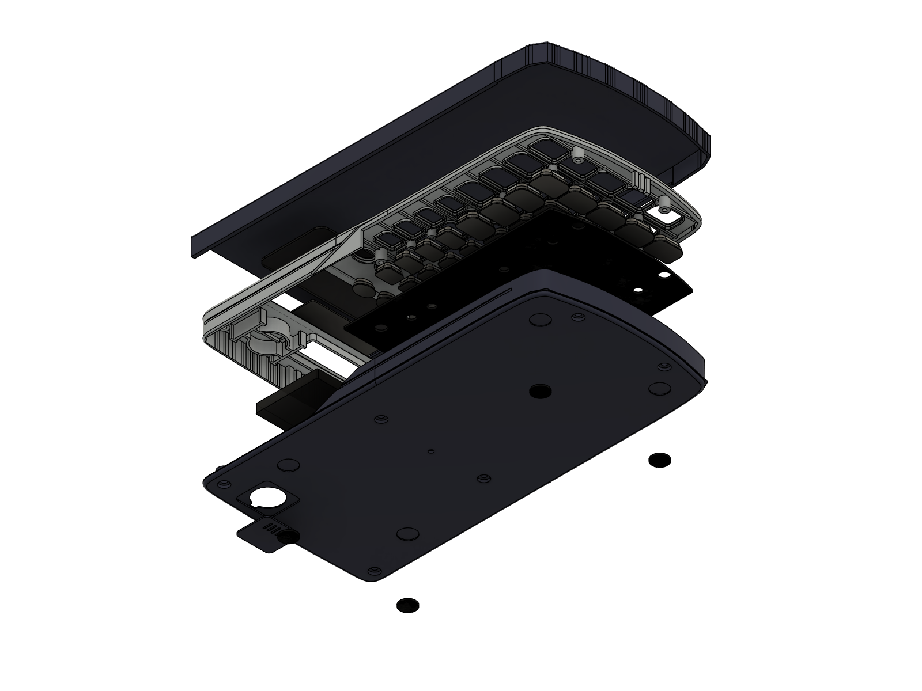
hardware/enclosure/replica/renders/exploded_iso_back.png
