niravkumar2008/AI-CALCULATOR/hardware/enclosure/replica/renders/fitcheck_front.png

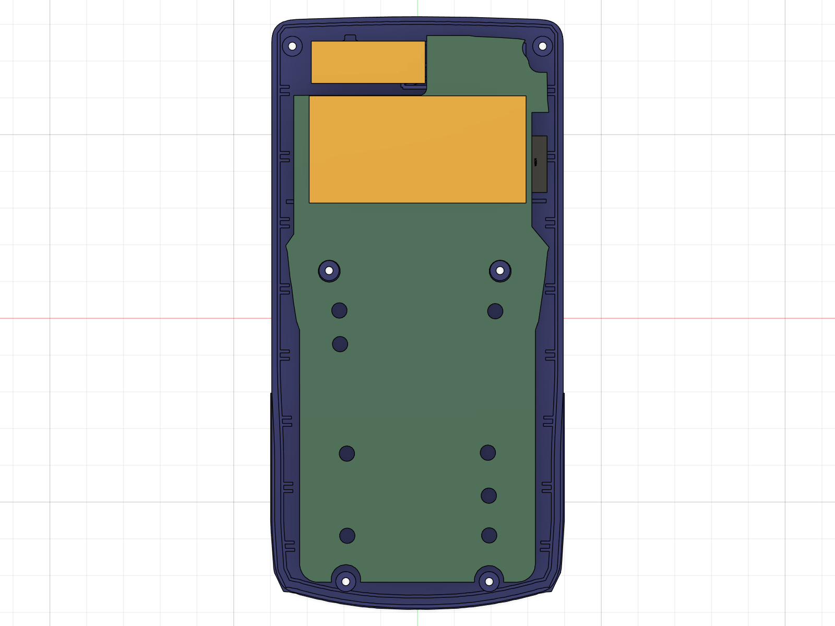
hardware/enclosure/replica/renders/fitcheck_front.png
