niravkumar2008/AI-CALCULATOR/hardware/enclosure/replica/renders/fitcheck_open_back_back.png

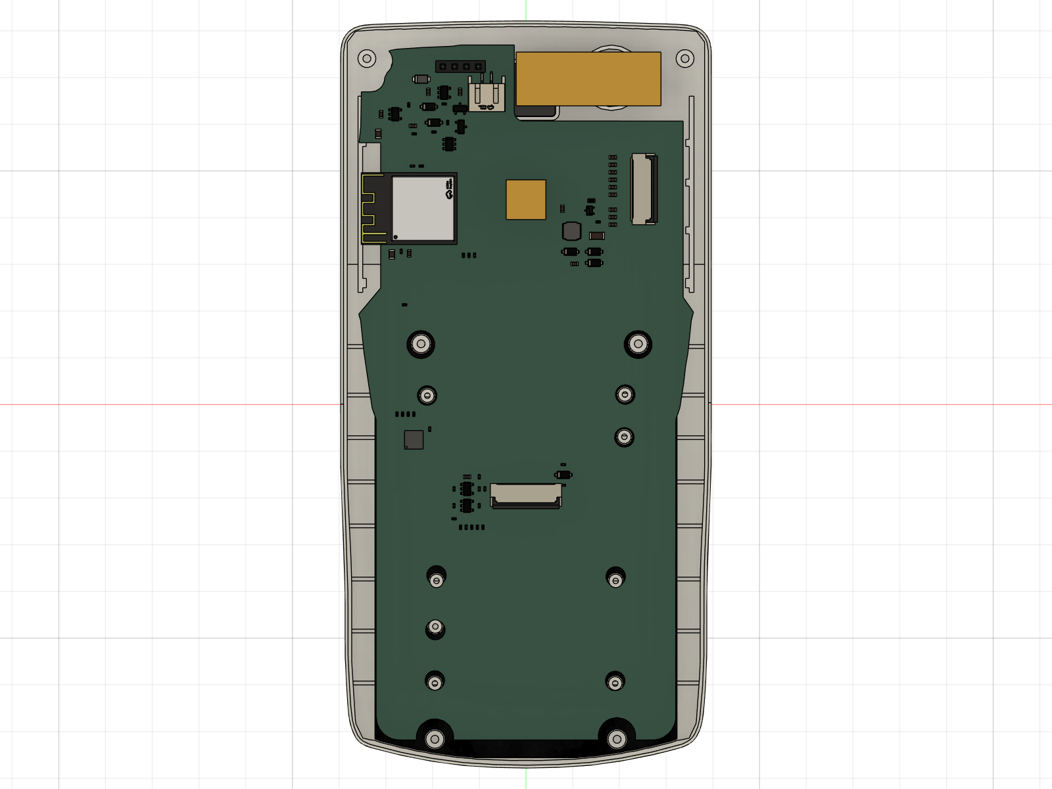
hardware/enclosure/replica/renders/fitcheck_open_back_back.png
