niravkumar2008/AI-CALCULATOR/hardware/enclosure/replica/renders/section_j4_eye_1.png

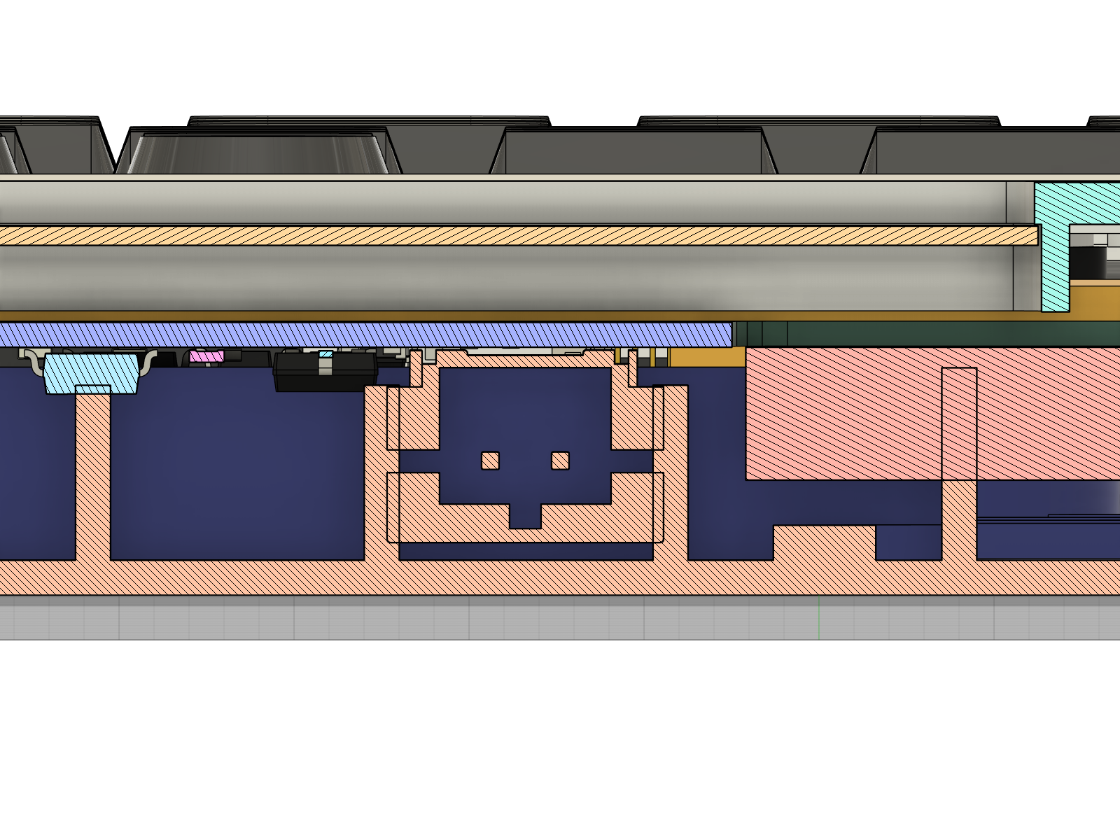
hardware/enclosure/replica/renders/section_j4_eye_1.png
