niravkumar2008/AI-CALCULATOR/hardware/enclosure/replica/renders/section_j4_top_end.png

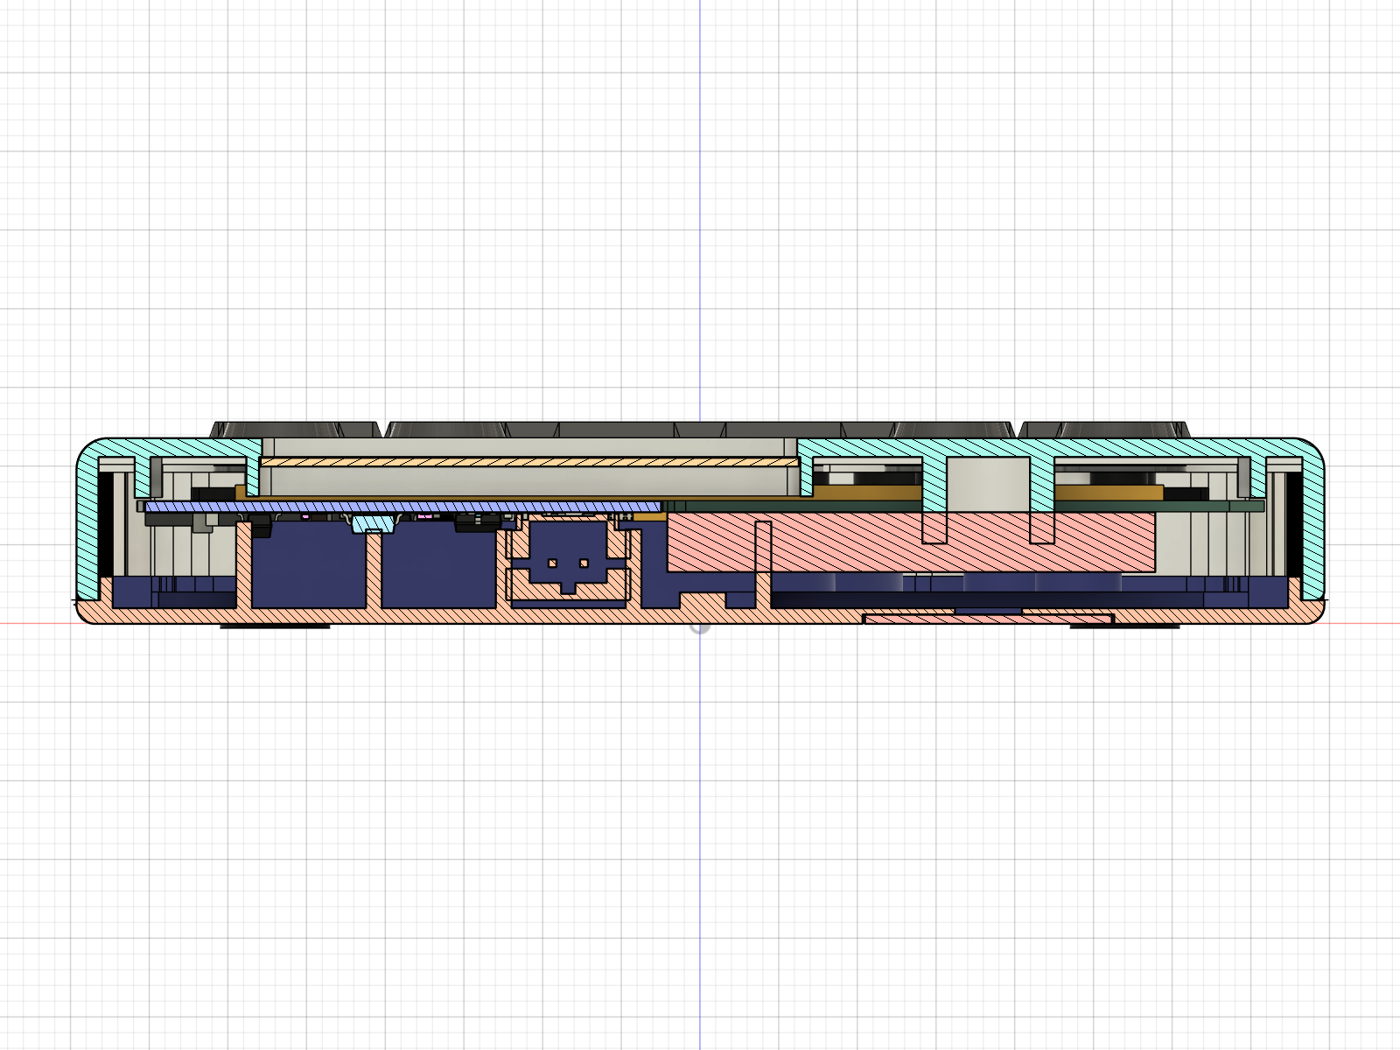
hardware/enclosure/replica/renders/section_j4_top_end.png
