niravkumar2008/AI-CALCULATOR/hardware/enclosure/replica/renders/section_screen_eye_1.png

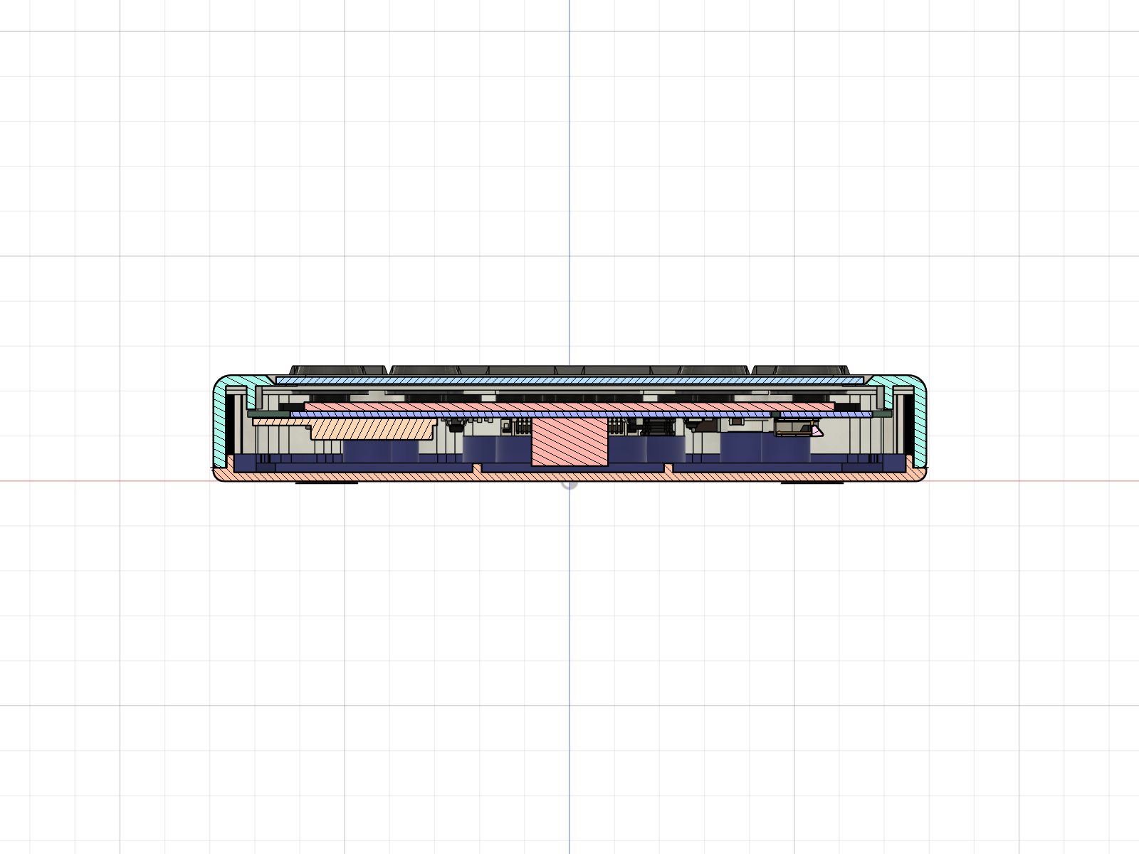
hardware/enclosure/replica/renders/section_screen_eye_1.png
