niravkumar2008/AI-CALCULATOR/hardware/enclosure/replica/renders/section_x_side.png

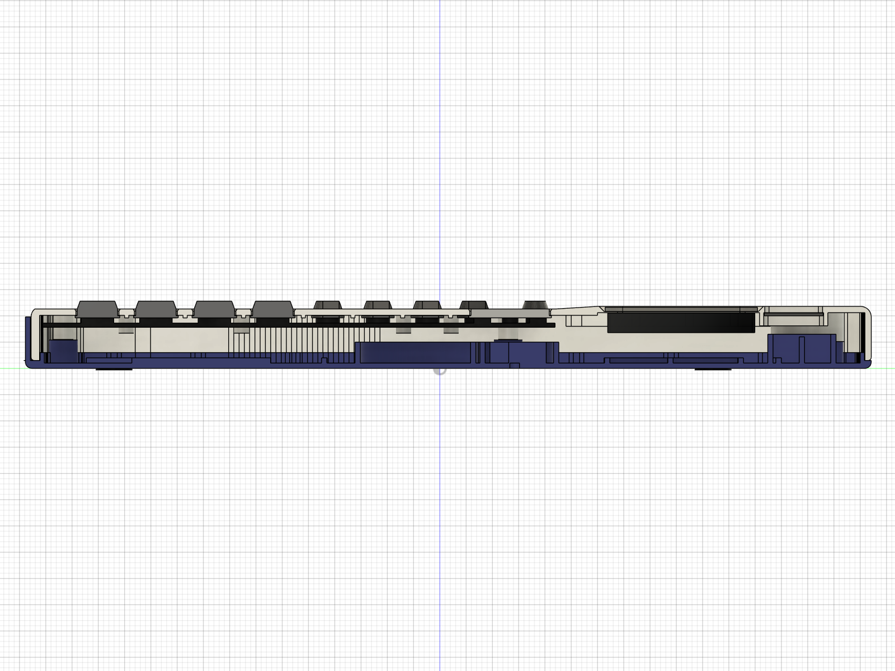
hardware/enclosure/replica/renders/section_x_side.png
