niravkumar2008/AI-CALCULATOR/hardware/enclosure/replica/renders/top_end.png

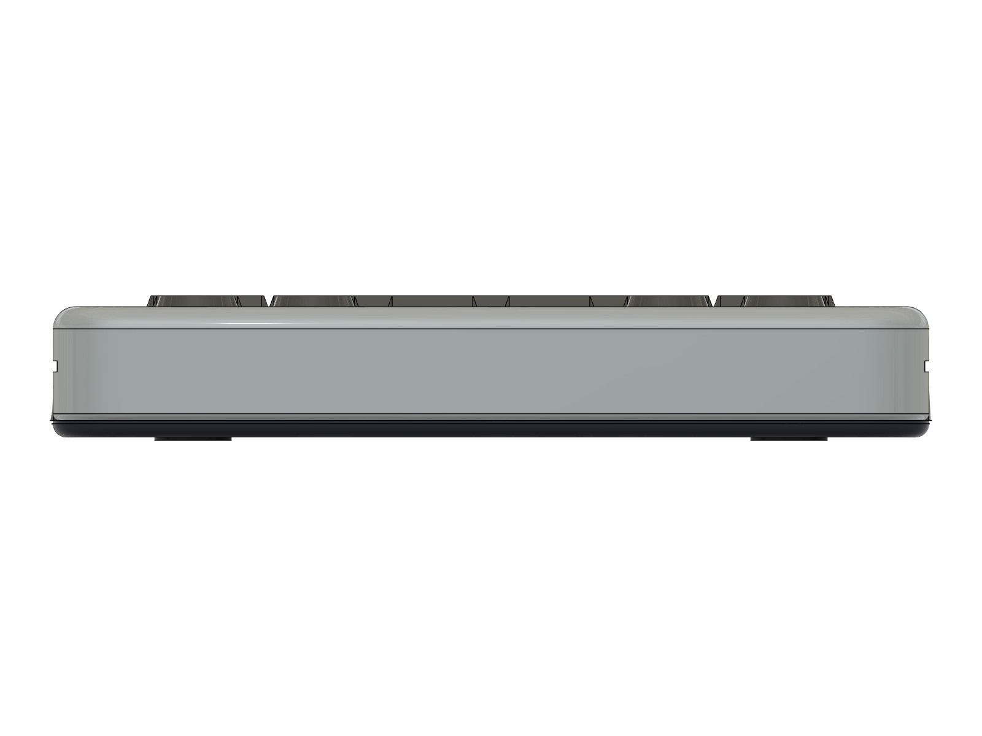
hardware/enclosure/replica/renders/top_end.png
