niravkumar2008/AI-CALCULATOR/hardware/project_hub/img/anim_turntable_v14_poster.jpg

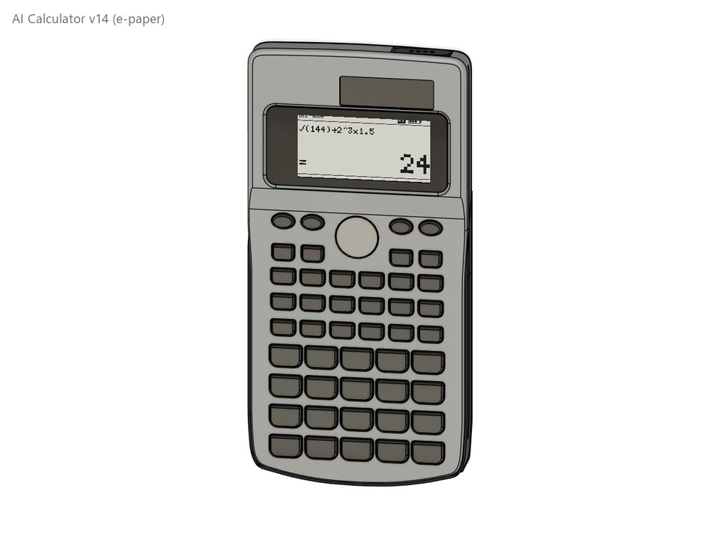
hardware/project_hub/img/anim_turntable_v14_poster.jpg
