niravkumar2008/AI-CALCULATOR/hardware/project_hub/img/anim_xray_v14_poster.jpg

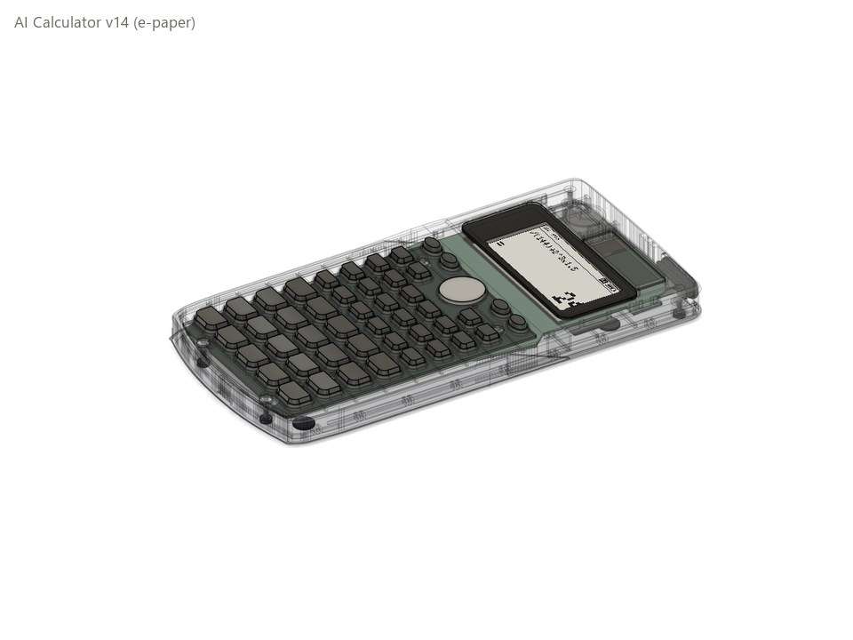
hardware/project_hub/img/anim_xray_v14_poster.jpg
