niravkumar2008/AI-CALCULATOR/hardware/project_hub/img/anim_xray_v15.gif

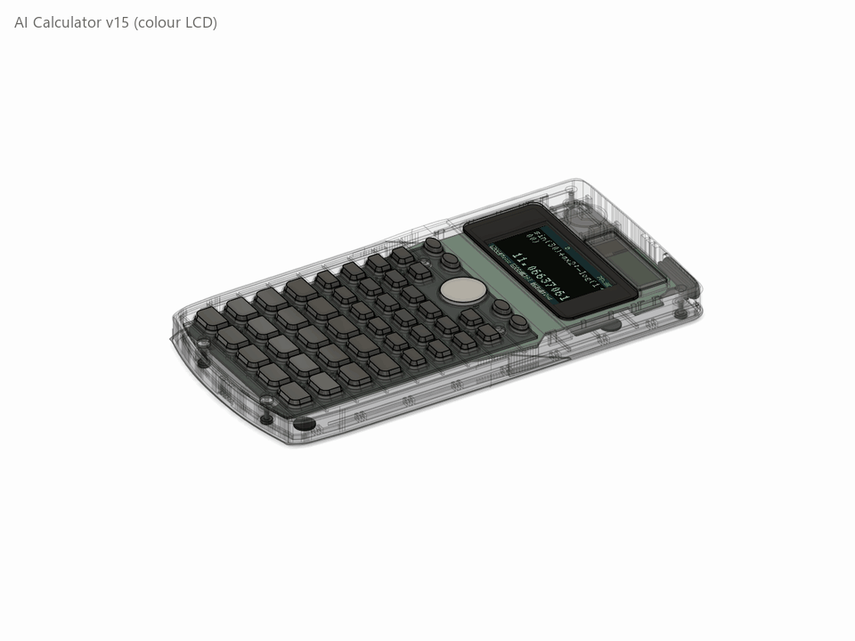
hardware/project_hub/img/anim_xray_v15.gif
