niravkumar2008/AI-CALCULATOR/hardware/project_hub/img/back_camera_window.jpg

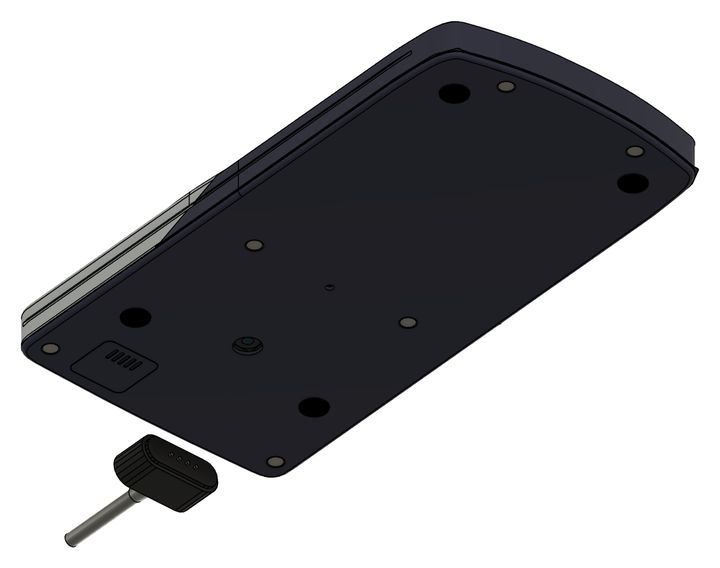
hardware/project_hub/img/back_camera_window.jpg
