niravkumar2008/AI-CALCULATOR/hardware/project_hub/img/front_v15.jpg

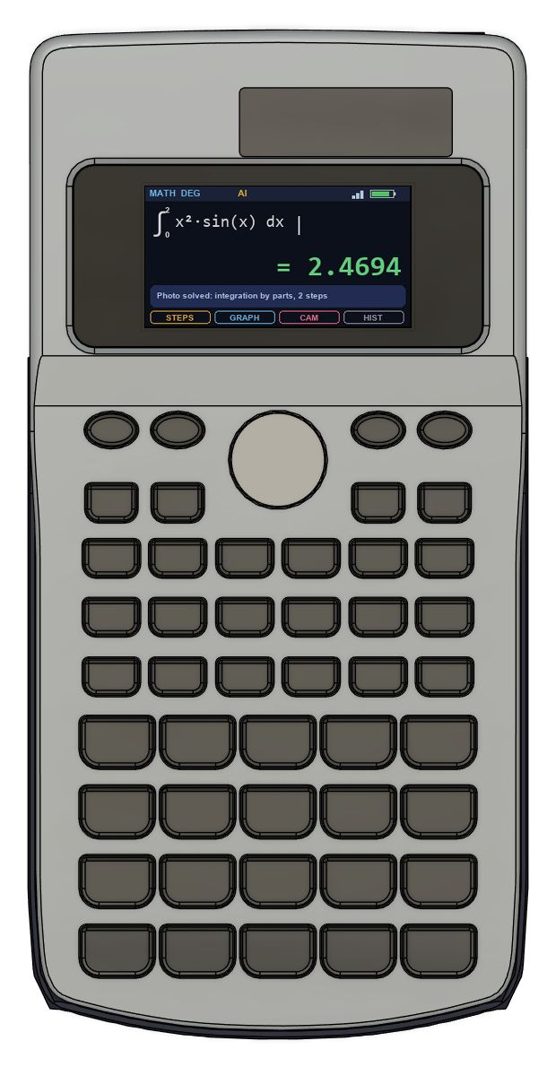
hardware/project_hub/img/front_v15.jpg
