niravkumar2008/AI-CALCULATOR/hardware/project_hub/img/hero_v15_lcd.jpg

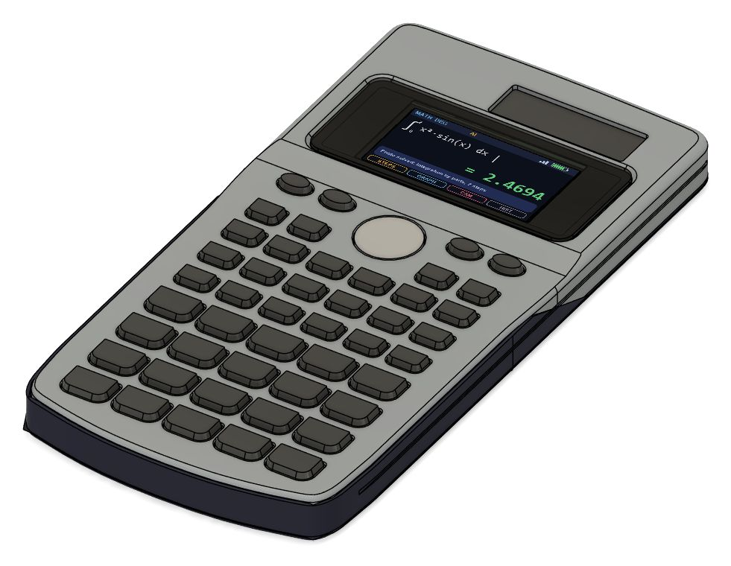
hardware/project_hub/img/hero_v15_lcd.jpg
