niravkumar2008/AI-CALCULATOR/hardware/project_hub/img/mock_ui.png

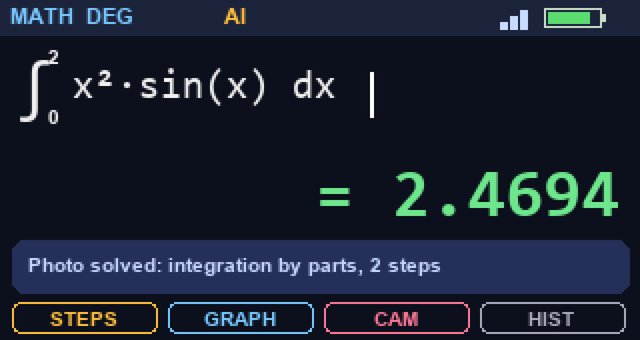
hardware/project_hub/img/mock_ui.png
