niravkumar2008/AI-CALCULATOR/hardware/project_hub/img/part_dcxyx_sfold.jpg

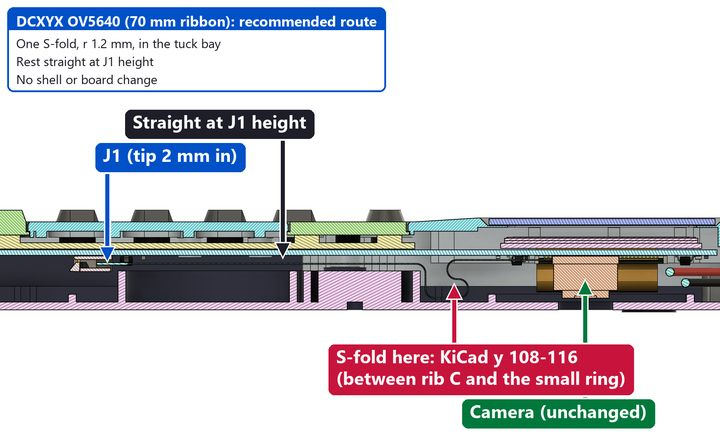
hardware/project_hub/img/part_dcxyx_sfold.jpg
