niravkumar2008/AI-CALCULATOR/hardware/project_hub/img/part_lcd_tail.jpg

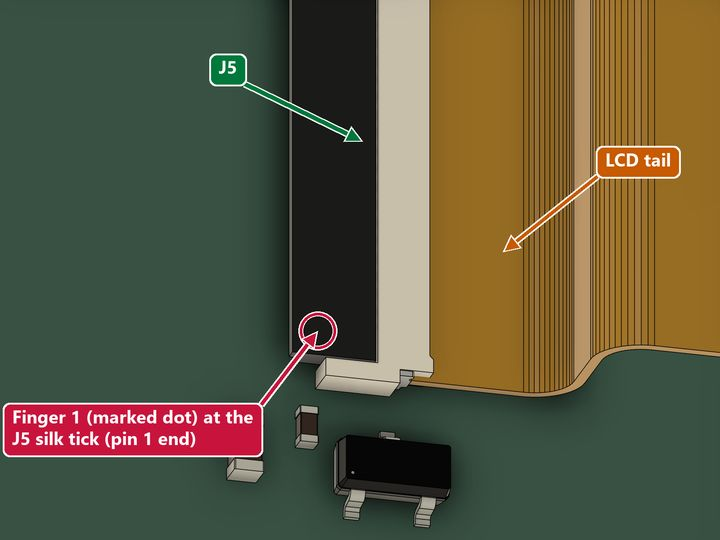
hardware/project_hub/img/part_lcd_tail.jpg
