niravkumar2008/AI-CALCULATOR/hardware/project_hub/img/part_magnet.jpg

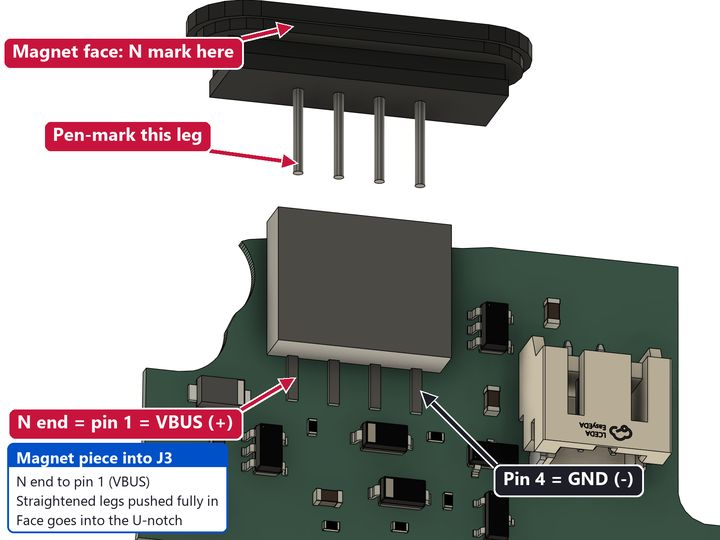
hardware/project_hub/img/part_magnet.jpg
