niravkumar2008/AI-CALCULATOR/hardware/project_hub/img/thumb_powerup_v14.jpg

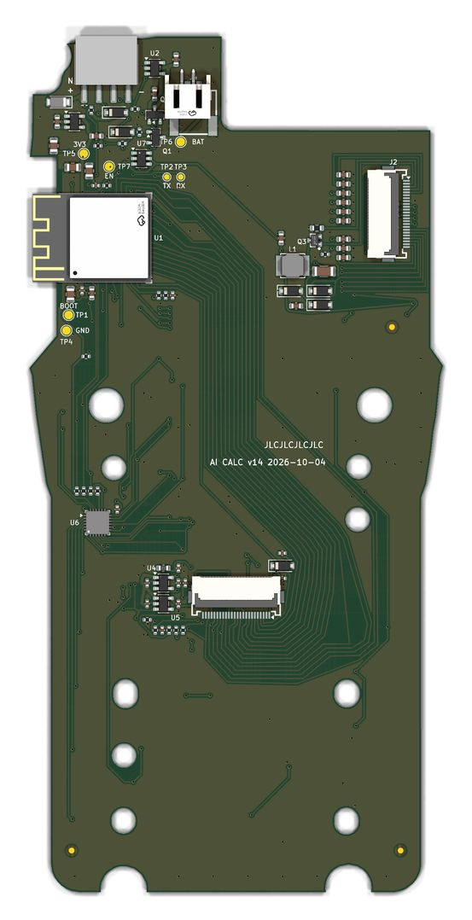
hardware/project_hub/img/thumb_powerup_v14.jpg
