niravkumar2008/AI-CALCULATOR/hardware/verification/renders/zoom_epaper_slot_J2.png

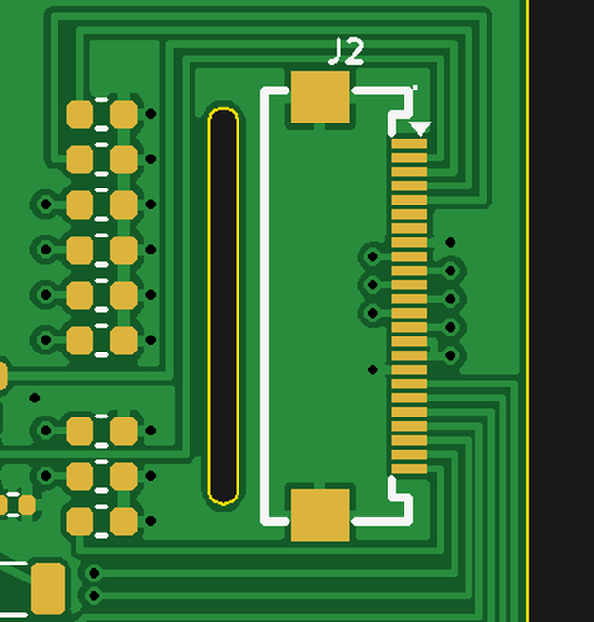
hardware/verification/renders/zoom_epaper_slot_J2.png
