niravkumar2008/AI-CALCULATOR/hardware/production/COST_MODEL.xlsx

Sheet: Summary
AI Calculator cost model: headline numbers
All values are formulas pointing at the other sheets. Edit blue cells on 'Inputs', 'Unit cost' and 'Cash budget'.
 | 5 testers | 10 units | 100 units | 1,000 units
Cost per unit (parts, freight, scrap, batch one-time)
Cost per unit incl. FCC / lawyer / LLC / trademark / insurance
Hardware profit per $225 unit
Hardware margin %
Subscription profit per paying user per month
Subscription margin %
Total profit per calculator (hardware + 12 months' subscription)
Units to cover this batch's one-time costs
Versions (10 / 100 / 1,000 only; the 5 testers are e-paper)
LCD version: cost per unit incl. selling-legally | n/a
LCD version: hardware profit per $225 unit | n/a
E-paper + 1,200-1,500 mAh: cost per unit incl. selling-legally | n/a
LCD + 1,200-1,500 mAh: cost per unit incl. selling-legally | n/a
LCD + 1,200-1,500 mAh: hardware profit per $225 unit | n/a
Claude API
Model
Cost per solve
API cost per subscriber per month (typical use)
API cost per month for a user at the 500 cap
Solves per day that $15 pays for (break-even)
Suggested fair-use cap (solves/month) for break-even
Same API cost per month on Sonnet 5.5 (typical)
Same on Sonnet 5.5 for a user at the 500 cap
The $2,000
Planned spend (5 testers → v15 order + panels → v15-LCD pilot)
Left over
Cash needed before the first 100 public units
Pre-orders at $225 that would fund it

Sheet: Inputs
Inputs: every blue number is an assumption you can edit. Black = formula.
Written 2026-10-06, updated 2026-10-08 evening (5 v14 testers, v15-LCD verified ORDER with the BuyDisplay ER-TFT019-1 panel, bigger battery). Sources beside each input. (estimate) = no hard source; confirm by quote.
Input | Value | Unit | Source / why
Pricing and fees
Calculator price | $225.00 | $ | Decided 2026-10-04 (LAUNCH_ROADMAP.md §0).
Subscription price per month | $15.00 | $/month | Decided 2026-10-04 (LAUNCH_ROADMAP.md §0).
Free months at the start | 1 | months | First month free = proxy TRIAL_DAYS=30 (server/proxy/config.py).
Fair-use cap, solves per month | 500 | solves | Proxy MONTHLY_CAP=500 (server/proxy/config.py).
Card fee, percent | 2.9% | % | Stripe US standard online card rate 2.9 % + 30¢ (estimate; check your Stripe dashboard).
Card fee, fixed per charge | $0.30 | $ | Stripe US standard 30¢ per charge (estimate).
Shipping one calculator to a customer | $6.00 | $ | USPS Ground Advantage, ~8 oz padded box, zone 4-5 (estimate).
Returns / warranty allowance (% of price) | 3.0% | % | Roadmap §5: budget 2-5 % of units needing help or replacement (estimate).
Subscription behaviour
Buyers who start paying after the free month | 70.0% | % | Assumption (estimate). Nothing measured yet: replace with beta data.
Monthly cancellation rate of paying users | 8.0% | %/month | Assumption (estimate). Student products churn in summer; 8 %/month ≈ half gone after 8 months.
Months counted for subscription value (LTV) | 12 | months | One school year plus summer. Conservative; anything after month 12 is upside.
Proxy hosting per month (server + database) | $25.00 | $/month | Small Render/Fly instance + disk (estimate). server/proxy/README.md: not deployed yet.
Claude API usage (per solve)
Model used for solves | Opus 5.5 |  | Pick from the table below (Opus 5.5 / Sonnet 5.5 / Haiku 4.5). NOTE: the proxy's default MAIN_MODEL today is claude-sonnet-5-5 (config.py).
Solves per active user per day (typical) | 5.00 | solves/day | Roadmap §3.3 'typical' = 150 solves/month ≈ 5/day (estimate).
Days per month | 30.40 | days | 365 / 12.
Input tokens per solve (photo + prompt) | 2500 | tokens | Roadmap §3.3: photo ≈ (w×h)/750 ≈ 1,600 for 1280×960, plus system prompt ≈ 2,500 total (estimate).
…of which a fixed system prompt that can be cached | 900 | tokens | Estimate. If the fixed prompt is shorter than the model's minimum cacheable prefix (512-4,096 tokens) it will not cache: set 0.
Cache hit rate on that prefix | 80.0% | % | Estimate (cache lives ~5 min; busy hours hit, quiet hours miss).
Cache write price as a multiple of input price | 1.25 | × | Anthropic 5-minute cache write = 1.25× base input.
Batch discount applied | 0.0% | % | Batch API is 50 % off but answers take minutes to hours: unusable for live solves. Keep 0 %.
Selling legally (one-time, before public sales)
FCC Part 15B SDoC test (1 lab day) | $1750 | $ | Roadmap §4: $1,000-2,500 [S10]; midpoint.
Lawyer: trade dress + terms of service | $300 | $ | Roadmap §4: clinic $0-300; KNOCKOFF_SHELL_PLAN.md §5: private consult $200-500.
Indiana LLC | $97 | $ | Roadmap §4 [S25].
USPTO trademark, classes 9 + 42 | $700 | $ | Roadmap §4: $350 per class [S24].
Product liability insurance, first year | $700 | $ | Roadmap §4: ~$400-1,000/yr (estimate).
JLCPCB assembly fee check (already inside the PCBA price row)
Standard PCBA setup fee per order | $25.00 | $ | Given 2026-10-06 (JLCPCB Standard PCBA).
Extended-part loading fee per part type | $3.00 | $ | Roadmap §3.1: $3 × 14 extended types per order (JLCPCB rule).
Extended part types on the board | 14 | types | Roadmap §3.1.
Solder joints per board | 310 | joints | Estimate from the 77-designator BOM: ESP32 module 65, TCA8418 25, 2 FPCs 52, SOT-23s ~45, connectors ~12, ~55 passives × 2.
Price per solder joint at 100 boards | $0.0013 | $ | Given 2026-10-06 (JLCPCB).
Your own time (shown, not added to cost at 2-100)
Your minutes per unit: grind + assemble + QA | 37 | min | Grinds with jigs 9-11 min (jigs/README.md), assembly ~15 min (estimate), QA Part A 5 + Part B 6-8 min (QA_TEST_PLAN.md).
Value of your hour | $15.00 | $/h | Assumption: a student job wage (estimate).
v15-LCD board change (per board; hardware/stage15_lcd.md §3, verification/13 and 14)
Parts removed: 17 e-paper parts (J2, L1, Q3, R11, R12, D3-D5, C20-C30) | $0.75 | $/board | Estimate from LCSC 1-off prices: J2 FPC socket ~$0.30, L1 68 µH ~$0.12, Q3 ~$0.15, 3 × B5819W ~$0.06, C20 + 10 × 1 µF/50 V ~$0.11, 2 resistors. Stage 15: board BOM ≈ $1 cheaper.
Parts added: J5 C2919501 $0.36, Q4 AO3401A $0.10, Q5 AO3400A C20917 $0.09, R21/R22/C36, R23 15 Ω C22810 | $0.56 | $/board | JLCPCB prices 2026-10-08 (stage15_lcd.md §3 table): 0.36 + 0.10 + 0.09 + 3 × 0.002 + R23 C22810 0.0013 (review 14: 22 Ω → 15 Ω).
Change in JLCPCB extended part types (v15 vs v14) | -1 | types | Review 14 stock list: v14 had 14 extended types, v15 has 13. L1 (C135265), Q3 (C469327) and R12 (C23157) leave; J5 (C2919501) and R23 15 Ω (C22810, ~$3 fee) join; J1 keeps C6364666.
v15-LCD JLCPCB order: 5 PCBs, 5 assembled, delivered (DHL + ~35 % duty) | $270 | $ | Estimate (hardware/ORDER_WALKTHROUGH_v15_lcd.md §8): the real v14 total $275 minus one extended-part fee and the ~$0.19/board cheaper BOM, with duty; range ≈ $255-285. Replace with the real quote.
Assembled v15 boards from that order that go into the pilot | 5 | boards | Plan: the 5 bench-tested v15 boards become pilot units 1-5, so the pilot pays for fewer new boards. Set 0 to keep them as spares.
Budget
Cash available for supply | $2000 | $ | Business plan: $2,000 budget.
v14 e-paper testers being built | 5 | units | Plan 2026-10-08: 5 testers in Casio shells.
v15-LCD pilot size (knockoff shells) | 10 | units | Plan: after the v15 order. Lower it (e.g. 5) if the cash budget goes negative.
Claude model prices (per million tokens)
Model | Input $/M | Output $/M | Cache read $/M | Output tokens per solve | Source
Opus 5.5 | $4.00 | $20.00 | $0.20 | 2100 | Given 2026-10-06 and Anthropic price table (cached 2026-09-25). Output incl. thinking (roadmap §3.3).
Sonnet 5.5 | $2.00 | $10.00 | $0.20 | 2100 | Anthropic price table (cached 2026-09-25). Proxy default MAIN_MODEL.
Haiku 4.5 | $1.00 | $5.00 | $0.10 | 800 | Anthropic price table; cache read = 0.1× input (estimate). Roadmap §3.3: ~800 output tokens.
Derived certification total (formula) |  |  | FCC + lawyer + LLC + trademark + insurance. Roadmap §3 calls this 'about $3.5k one-time'.

Sheet: Unit cost
Cost per finished calculator at 5 / 10 / 100 / 1,000 units (e-paper version; LCD and big battery on 'Versions')
5 = the v14 e-paper TESTERS in genuine Casio fx-115ES shells (option C of Claude outputs/AI_Calculator_Shopping_List.xlsx). 10 / 100 / 1,000 = knockoff 991ES-style shell (v15 board). Per-unit prices from Claude outputs/Alibaba_Bulk_Sourcing.xlsx 'Cost by batch' and LAUNCH_ROADMAP.md §3 unless noted.
# | Item | 5 testers | 10 units | 100 units | 1,000 units | Source / notes
 | Batch size (units) | 5 | 10 | 100 | 1000 | Edit to test other batch sizes; the per-unit prices below don't re-scale by themselves.
 | Shell used | Casio donor | Clone (retail) | Clone (Alibaba) | Clone (factory)
Per-unit parts (price per unit at that volume)
1 | PCB + PCBA (board, all SMD parts, JLCPCB assembly) | $55.00 | $18.00 | $9.00 | $7.30 | 5: JLCPCB v14 DELIVERED (incl. DHL + ~35 % duty) ≈ $220 for 2 assembled + $55 for 5 assembled = $275 ÷ 5 (Shopping List rows 1-2). 10/100/1,000: roadmap §3 table [S8].
2 | Shell + key mat + window + screws | $20.00 | $6.00 | $3.99 | $3.25 | 5: Casio fx-115ES $20 each (3 bought, 2 already owned; value shown for all 5). 10: retail clone incl. shipping. 100: Alibaba $3.25-3.99 MOQ 20 [S1]. 1,000: $3.25 (factories quote $1.50-3.50 at 3,000 [S2]).
3 | Camera OV5640 AF | $10.59 | $12.00 | $6.00 | $4.50 | 5: option C = (3 × Seeed 114993115 $12.99 + 2 × generic $7) ÷ 5. Then roadmap / Alibaba OEM [S3].
4 | E-paper 2.13" raw panel | $5.99 | $6.60 | $5.50 | $4.00 | 5: option C = (3 × Waveshare $6.99 + 2 × GDEY0213B74 $4.50) ÷ 5. Then Good Display direct by RFQ (estimate).
5 | LiPo 150 mAh + JST-PH | $4.77 | $5.95 | $1.80 | $1.30 | 5: option C = (3 × Adafruit #1317 $5.95 + 2 × generic 302030 $3) ÷ 5. 10: Adafruit #1317. 100/1,000: Alibaba cell with PH lead + PCM (estimate).
6 | Battery dangerous-goods freight surcharge | $0.00 | $0.00 | $0.80 | $0.30 | UN3481 air surcharge (estimate).
7 | Magnetic connector pair | $6.50 | $5.85 | $1.80 | $1.20 | Adafruit #5358 $6.50 / $5.85 (10+); Alibaba MG04-254-RA $1.80 [S7].
8 | Magnetic USB cable (in the box) | $4.95 | $4.95 | $1.80 | $1.40 | Adafruit #5412 $4.95; OEM $1.40-1.80 (estimate).
9 | Retail box + insert | $0.00 | $1.50 | $1.00 | $0.60 | Prototypes unboxed. Alibaba rigid box $0.20-1.02 @100 [S9].
10 | Quick-start card (with 'not affiliated with Casio') | $0.00 | $0.10 | $0.25 | $0.05 | [S10]; small runs estimate.
11 | Serial / QC label + polybag | $0.00 | $0.15 | $0.10 | $0.05 | Estimate.
12 | Tape, Kapton, glue (per-unit share) | $0.00 | $0.50 | $0.30 | $0.20 | 2: bought as bench tools (one-time row below). Estimate.
13 | Inbound freight + US import duty (per unit) | $0.00 | $8.00 | $8.00 | $5.00 | 5: JLCPCB freight/duty is inside row 1; other shipping is a lump (one-time row below). Roadmap: ~35 % duty, low end of 35-92.5 % [S8]. Biggest swing factor.
 | Parts subtotal
 | Scrap + spares allowance, % | 0.0% | 10.0% | 7.0% | 5.0% | Alibaba sheet row 15 (estimate). At 5 the spares are a one-time row instead.
 | Scrap + spares allowance, $
 | Paid assembly labour (box build) | $0.00 | $0.00 | $0.00 | $2.50 | You build 5-100 yourself (time not costed, see row below). 1,000: EMS box build (roadmap §3, estimate).
 | Variable cost per unit
One-time costs for the batch (whole $ amount)
 | Other shipping lump (Adafruit $15 + Seeed $12 + Waveshare $20 + AliExpress $10; JLCPCB's is in row 1) | $57.00 | $0.00 | $0.00 | $0.00 | Shopping List (option C) shipping rows. At 10+ freight is per unit (row 13).
 | Bench tools and consumables (tape, glue, drill bit, vinyl, IPA, glasses) | $61.00 | $0.00 | $0.00 | $0.00 | Shopping List supplies section (charger qty 0 = you own one).
 | Tester spares (option C: 1 spare of each current + generic camera, screen, battery; 1 magnet piece) | $46.93 | $0.00 | $0.00 | $0.00 | 12.99 + 7 + 6.99 + 4.50 + 5.95 + 3 + 6.50 (Shopping List qty 6 of each kind).
 | Supplier samples (2 each from 2 suppliers, incl. 4 knockoff shells) + express | $0.00 | $150.00 | $150.00 | $120.00 | Alibaba sheet row 16 (estimate); KNOCKOFF_SHELL_PLAN.md §1.
 | Pogo test jig + fixtures | $0.00 | $0.00 | $100.00 | $150.00 | Roadmap §5: $50-150 (estimate).
 | Third-party pre-shipment inspection | $0.00 | $0.00 | $0.00 | $300.00 | ~1 man-day (estimate). Only worth it at 1,000.
 | One-time total for the batch
 | One-time per unit
 | COST PER UNIT (before selling-legally costs) |  |  |  |  | Compare: Alibaba_Bulk_Sourcing.xlsx ≈ $92 @10, $46 @100, $34 @1,000 (see 'Checks').
 | Selling legally? (1 = yes, spread the one-time certification over this batch) | 0 | 0 | 1 | 1 | 5 = testers (not sold); 10 = free / at-cost beta (KNOCKOFF_SHELL_PLAN.md §5). Public sales start at 100.
 | Certification, lawyer, LLC, trademark, insurance per unit
 | COST PER UNIT incl. selling-legally costs
 | Cash for the whole batch (incl. one-time)
Information only (not added above)
 | JLCPCB assembly fee inside the PCBA price: (setup + extended fees) ÷ batch + joints × rate |  |  |  |  | Why the board price drops from 10 to 100: the fixed $67 per order is shared. The joint fee itself is only ~$0.40 a board; the rest of row 1 is parts.
 | Your time per unit, valued (not cash) |  |  |  |  | 37 min × $15/h. Zero where paid labour takes over.

Sheet: API cost
Claude API cost per solve and per subscriber per month
Chosen model and usage come from 'Inputs'. Batch pricing does not apply to live solves.
Item | Value | How it's worked out
Model |  | Inputs
Input price $/M tokens |  | Model table on Inputs
Output price $/M tokens |  | Model table
Cache read price $/M tokens |  | Model table
Output tokens per solve (incl. thinking) |  | Model table
Input tokens read from cache |  | cached prefix × hit rate
Input tokens written to cache (misses) |  | cached prefix × miss rate
Input tokens at full price |  | all input − cache reads (writes are billed at full price plus the write premium)
Input cost per solve |  | full-price input + cache reads + write premium
Output cost per solve |  | output tokens × output price
COST PER SOLVE |  | after any batch discount
Solves per user per month (typical) |  | solves/day × days
API COST PER SUBSCRIBER PER MONTH (typical)
API cost per month for a user at the fair-use cap |  | cap = 500 solves (proxy)
Solves per month that $15 can pay for |  | ($15 − card fee) ÷ cost per solve. Hosting excluded.
…as solves per day
Cap that keeps a heavy user at break-even (suggested MONTHLY_CAP) |  | rounded down to 10
Scenarios: API cost per user per month (same cache assumptions)
Model | Cost per solve | Light 2/day | Typical (Inputs) | Heavy 10/day | At the cap | Light / heavy solves per day: | 2 | 10
Column C is narrow-looking because it also holds the notes above; numbers are $ per user per month.

Sheet: Margins & payback
Margin on the $225 calculator, margin on the $15 subscription, break-even and payback
Columns = batch size. Unit cost includes the selling-legally costs where 'Selling legally' = 1 on 'Unit cost'.
Item | 5 testers | 10 units | 100 units | 1,000 units | How it's worked out
Batch size
HARDWARE
Price |  |  |  |  | Inputs
Card fee |  |  |  |  | 2.9 % + 30¢
Shipping to the customer |  |  |  |  | Inputs
Returns / warranty allowance |  |  |  |  | % of price
API cost of the free first month |  |  |  |  | Every buyer gets it, paying or not
Unit cost (incl. selling-legally costs) |  |  |  |  | 'Unit cost' sheet
HARDWARE PROFIT PER UNIT |  |  |  |  | price − everything above
Hardware margin % |  |  |  |  | profit ÷ price
SUBSCRIPTION (per paying user per month)
Price |  |  |  |  | Inputs
Card fee |  |  |  |  | the 30¢ hurts most on small charges
Claude API (typical user) |  |  |  |  | 'API cost' sheet
Hosting share |  |  |  |  | server $/month ÷ paying users (batch × attach rate)
SUBSCRIPTION PROFIT PER USER PER MONTH
Subscription margin %
Same, for a user at the 500-solve cap |  |  |  |  | negative = that user costs you money
Does $15 cover the API? (typical user)
LIFETIME (per calculator sold)
Expected paid months in the horizon |  |  |  |  | attach × (1 − (1−churn)^(months−free)) ÷ churn
Subscription profit over the horizon
TOTAL PROFIT PER CALCULATOR (hardware + subscription)
BREAK-EVEN AND PAYBACK
One-time costs this batch carries (samples, jig, QC, certification) |  |  |  |  | 'Unit cost' one-time + certification if selling
Variable cost per unit
Profit per unit before one-time costs
Units to sell to cover the one-time costs (hardware only) |  |  |  |  | one-time ÷ profit per unit
Months for one paying user to repay the free month's API |  |  |  |  | free-month API ÷ subscription profit
Months of subscription that would repay the unit cost alone |  |  |  |  | if the calculator were sold at cost
Calculators to sell to get the $2,000 budget back |  |  |  |  | $2,000 ÷ hardware profit per unit

Sheet: Versions
Four versions at 10 / 100 / 1,000: e-paper or LCD, 150 mAh or 1,200-1,500 mAh battery
Starts from the e-paper cost on 'Unit cost' and adds only the differences (each difference also carries that column's scrap %). LCD = v15-LCD board (hardware/stage15_lcd.md): 1.9" 170×320 IPS ST7789 30-pin panel instead of the 2.13" e-paper. Big battery = Adafruit #258 1,200 mAh at 10, Alibaba 504060 ~1,500 mAh at 100+ (enclosure/final_assembly/battery_upgrade.md): needs the custom shell pocket (70 × 41 × 5.4 mm) or a knockoff with room (KNOCKOFF_SHELL_PLAN.md K-D7/K-S5).
# | Item | 10 units | 100 units | 1,000 units | Source / notes
Inputs that differ by version
 | E-paper panel (from 'Unit cost') |  |  |  | Unit cost row 4.
 | LCD panel price at 10: BuyDisplay ER-TFT019-1 (no touch, datasheet-verified) | $6.22 |  |  | Given 2026-10-08 (verification/14, LCD_PANEL_OPTIONS.md): ~$6-7 each, $6.22 @10, $5.71 @100.
 | BuyDisplay shipping per order | $12.00 |  |  | Estimate, not quoted: check at checkout and replace.
 | LCD panel price at 100 / 1,000 (Alibaba / panel maker) |  | $2.50 | $2.30 | hardware/production/lcd_suppliers.json (2026-10-08): Alibaba, Zhengzhou Zhongjingyuan (ZJY) ST7789V3 30-pin, $2.50 @100, $2.30 @1,000, MOQ 2 (prices from search snippets; confirm drawing + pin table and get a written quote). Sample: Shenzhen Goldenmorning T190X7-C30-01 $1.85-2.50. No listing gave a short-tail FPC price.
 | LCD panel per unit |  |  |  | 10: BuyDisplay price + one shipping charge shared by the batch. 100/1,000: the line above (Alibaba after a sample check).
 | v15 PCBA parts change per board (added − removed) |  |  |  | Inputs: v15-LCD board change.
 | v15 extended-part fee change per board |  |  |  | types change × $3 per order ÷ batch.
 | 150 mAh battery + its DG surcharge (from 'Unit cost') |  |  |  | Unit cost rows 5-6.
 | 1,200-1,500 mAh battery | $9.95 | $4.00 | $3.00 | 10: Adafruit #258 1,200 mAh $9.95 (battery_upgrade.md). 100/1,000: Alibaba 504060 ~1,500 mAh ~$3-5 at MOQ (estimate). Must come with UN38.3 in the seller's name.
 | Its dangerous-goods freight surcharge | $0.00 | $1.20 | $0.50 | Estimate: ~5.5 Wh cell, heavier than the 150 mAh one (UN3481). At 10 it ships ground from Adafruit (in the price).
 | Longer JST-PH lead / extension (the pocket is under the keypad, ~150 mm lead) | $0.50 | $0.25 | $0.15 | Estimate. Also R2 20 k → 4.7 k on the board for a ~3 h charge (one resistor, no cost change).
Differences per unit (incl. scrap %)
 | LCD instead of e-paper |  |  |  | (panel − e-paper + board change) × (1 + scrap %).
 | Big battery instead of 150 mAh |  |  |  | (big cell + its DG + lead − small cell − its DG) × (1 + scrap %).
Results by version
 | Version | 10 units | 100 units | 1,000 units
 | Cost per unit before selling-legally costs
 | E-paper, 150 mAh (= 'Unit cost')
 | LCD, 150 mAh (v15-LCD)
 | E-paper, 1,200-1,500 mAh
 | LCD, 1,200-1,500 mAh (the long-term target)
 | Cost per unit incl. selling-legally costs (FCC, lawyer, LLC, trademark, insurance)
 | E-paper, 150 mAh (= 'Unit cost')
 | LCD, 150 mAh (v15-LCD)
 | E-paper, 1,200-1,500 mAh
 | LCD, 1,200-1,500 mAh (the long-term target)
 | Hardware profit per $225 unit (same fees, shipping, warranty, free-month API as 'Margins & payback')
 | E-paper, 150 mAh (= 'Unit cost')
 | LCD, 150 mAh (v15-LCD)
 | E-paper, 1,200-1,500 mAh
 | LCD, 1,200-1,500 mAh (the long-term target)
 | Variable cost per unit (no one-time costs), for the cash budget
 | E-paper, 150 mAh (= 'Unit cost')
 | LCD, 150 mAh (v15-LCD)
Battery life (stage15_lcd.md §3): LCD screen-on ≈ 80-90 mA → ~1.5 h on 150 mAh (charge every 1-2 days), 13-17 h on 1,200-1,500 mAh. The e-paper draws almost nothing between refreshes (~3 h screen-on, weekly charging). That is why the big cell matters for the LCD version.

Sheet: Cash budget
Where the $2,000 goes (supply budget), in order
Cash actually leaving your account, in the order of the 2026-10-08 plan. The 2 Casio shells you own are not cash. v14 JLCPCB was ordered 10/8; v15-LCD is verified ORDER (review 14) and is next; nothing else is bought yet.
# | What | When | Amount | Source / notes
1 | v14 JLCPCB order: 5 PCBs, 5 assembled, delivered (DHL + ~35 % duty) | Paid 10/8 | $275.00 | Shopping List rows 1-2: ≈ $220 for 2 assembled + ≈ $55 for 5 assembled (ranges $200-240 and $50-60). Replace with the real total.
2 | 5 testers: 3 Casio shells, cameras, screens, batteries, magnet pieces, cables, shipping, supplies (option C) | Now, before boards land | $388.97 | AI_Calculator_Shopping_List.xlsx option C total $663.97 minus the JLCPCB order. Option B would be ≈ $92 less, option A ≈ $2 less.
3 | v15-LCD prototype panels: 3 × BuyDisplay ER-TFT019-1 (no touch) + shipping | Now, with the v15 order | $32.25 | Shopping List sheet 'v15-LCD prototype' rows 1-2: 3 × ~$6.75 + ~$12 shipping (estimate). Bench checks at arrival: diode test, tail length, backlight current, 3.3 V.
4 | v15-LCD JLCPCB order (verified ORDER, review 14): 5 PCBs, 5 assembled, delivered | Now |  | Inputs: v15 order estimate. Files hardware/fab_v15_lcd/, steps hardware/ORDER_WALKTHROUGH_v15_lcd.md.
5 | Knockoff shell samples: 4 clones, 2 sellers (KNOCKOFF_SHELL_PLAN.md §1) | During tester feedback | $60.00 | Alibaba pair $40-60 incl. DHL + AliExpress/Amazon pair $10-16 (estimate).
6 | Other supplier samples for bulk (camera, bare LCD panels, 150 mAh + 1,200-1,500 mAh cells, magnet pair + cable) | After shells pass | $90.00 | Alibaba sheet row 16 total $150 minus the shells (estimate).
7 | v15-LCD pilot in knockoff shells: the remaining boards + all parts, freight, scrap | After the v15 boards pass the bench checks |  | Pilot size (Inputs) × LCD variable cost at 10 ('Versions'), minus the boards re-used from the v15 order × the $18 board cost at 10 ('Unit cost' row 1). Includes $8/unit freight and duty.
8 | Proxy hosting, first 3 months | At beta |  | Inputs: server $/month × 3.
9 | Claude API for the testers' and pilot users' free month | At beta |  | (testers + pilot) × 1 month at the typical rate of the model chosen on Inputs.
10 | Lawyer / IP clinic: trade-dress check before any unit leaves the house | Before testers go out | $150.00 | KNOCKOFF_SHELL_PLAN.md §5. University clinic / SCORE can be $0; private $200-500.
11 | Indiana LLC | Before taking money |  | Inputs (roadmap §4).
12 | Domain + email for the link page | Before beta | $20.00 | Estimate.
 | Subtotal
 | Contingency, % of subtotal (re-orders, a dead camera, express shipping) | 10.0%
 | TOTAL PLANNED SPEND
 | Budget
 | LEFT OVER (negative = over budget)
Not inside the $2,000: what the first 100 public units need
 | 100-unit batch (LCD version): variable cost × 100 + its one-time costs (samples, jig)
 | Selling legally: FCC SDoC, lawyer, LLC, trademark, insurance
 | Cash needed before the first public sale
 | Pre-orders at $225 (after card fees) that fund it |  |  | Uses any money left from the $2,000 first. Roadmap §6: take pre-orders before each step up.

Sheet: Checks
Cross-checks against earlier files
Check | This model | Earlier figure | Difference | Earlier source
5 testers: cash for the batch minus the 2 owned shells' value |  | $663.97 |  | AI_Calculator_Shopping_List.xlsx option C total ($663.97)
LCD version cost per unit at 100 (before selling-legally) |  | $42.22 |  | Alibaba_Bulk_Sourcing.xlsx 'v15-LCD cost by batch' total @100
Cost per unit at 10 (before selling-legally) |  | $92.00 |  | Alibaba_Bulk_Sourcing.xlsx 'Cost by batch' (≈ $92)
Cost per unit at 100 (before selling-legally) |  | $46.00 |  | Alibaba_Bulk_Sourcing.xlsx (≈ $46)
Cost per unit at 1,000 (before selling-legally) |  | $34.00 |  | Alibaba_Bulk_Sourcing.xlsx (≈ $34)
Opus 5.5 cost per solve, no caching (roadmap §3.3) |  | $0.0520 |  | LAUNCH_ROADMAP.md §3.3 (~$0.052)
Certification etc. one-time |  | $3500.00 |  | LAUNCH_ROADMAP.md §3 ('about $3.5k')
Differences come from the tester-only rows, rounding in the earlier sheet, and the cache saving on the system prompt.
