niravkumar2008/AI-CALCULATOR/hardware/enclosure/final_assembly/renders/exploded_3_parts_and_case.png

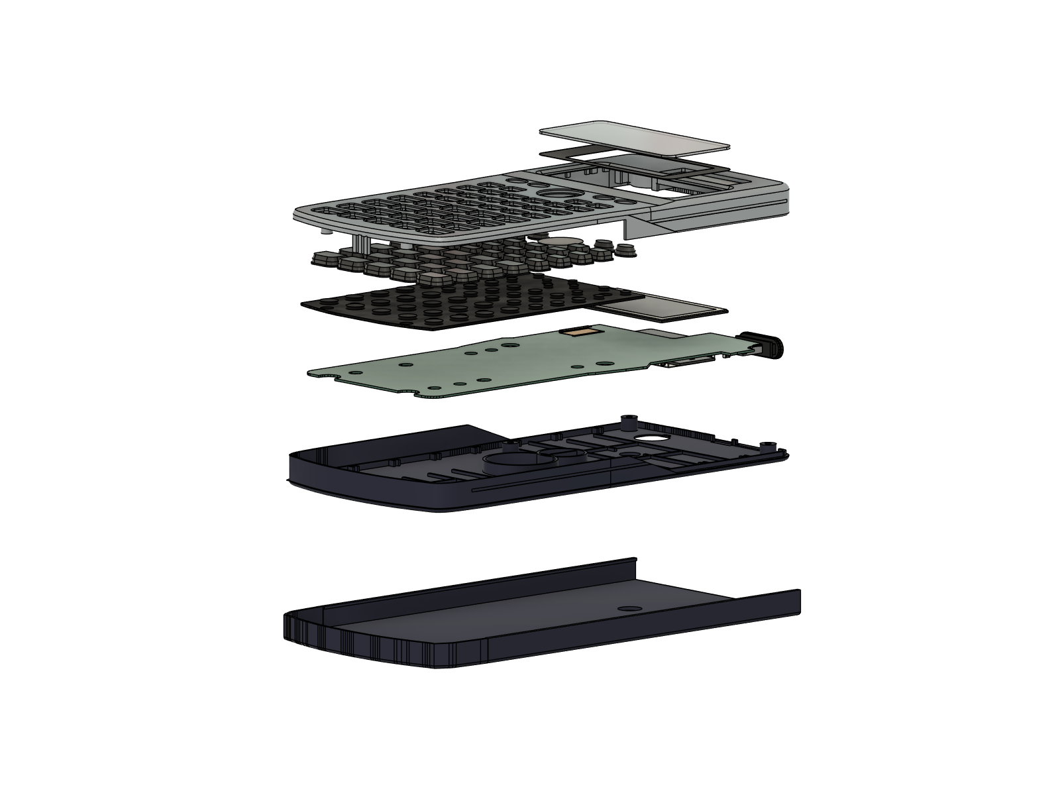
hardware/enclosure/final_assembly/renders/exploded_3_parts_and_case.png
