niravkumar2008/AI-CALCULATOR/hardware/enclosure/replica/stl/keycaps/05_Key_ALPHA.stl

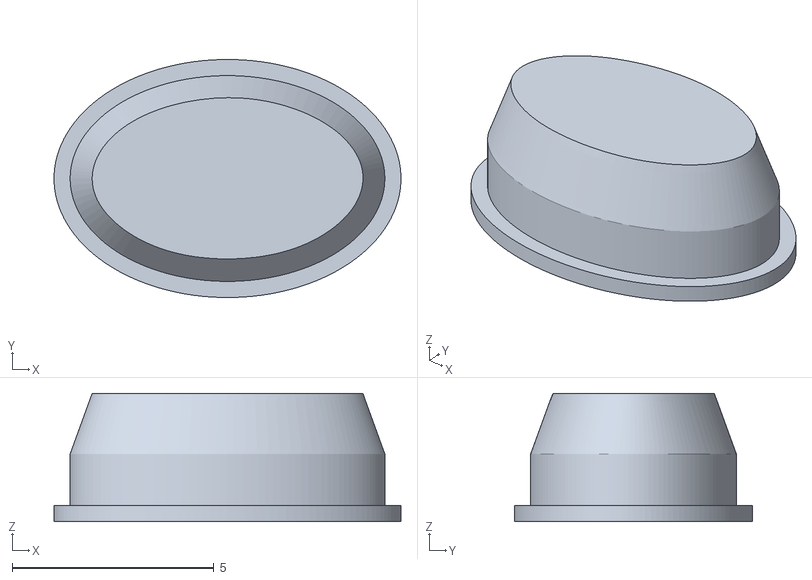
[picture p70: CAD file, 2026-10-08]
hardware/enclosure/replica/stl/keycaps/05_Key_ALPHA.stl
8.60 x 5.90 x 3.18
