niravkumar2008/AI-CALCULATOR/hardware/enclosure/replica/stl/Rubber_feet_Foot_2.stl

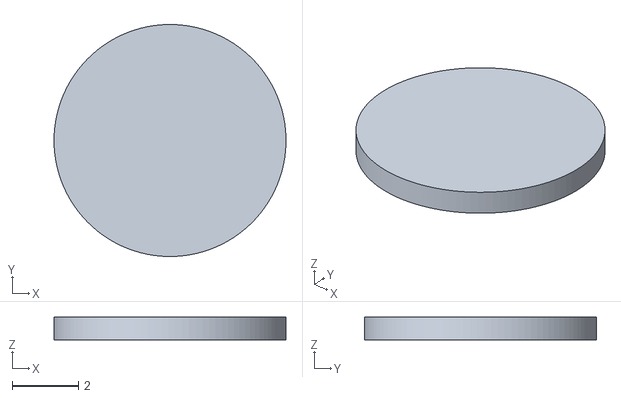
[picture p71: CAD file, 2026-10-08]
hardware/enclosure/replica/stl/Rubber_feet_Foot_2.stl
7.00 x 7.00 x 0.68
