niravkumar2008/AI-CALCULATOR/hardware/enclosure/export/back_cover.stl

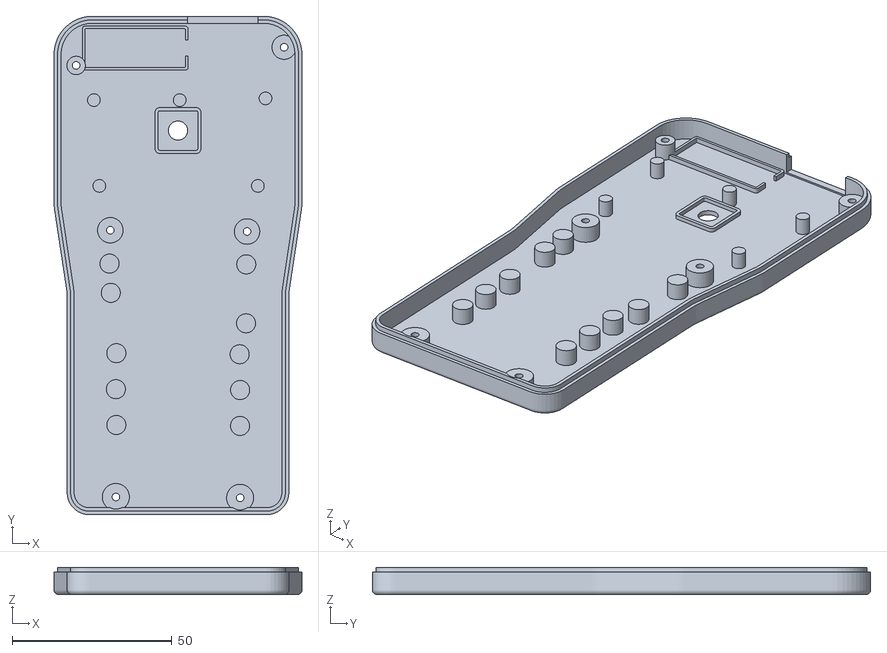
[picture p72: CAD file, 2026-10-03]
hardware/enclosure/export/back_cover.stl
77.7 x 156.2 x 8.50
