niravkumar2008/AI-CALCULATOR/hardware/enclosure/jigs/A3_depth_gauge_7_2.stl

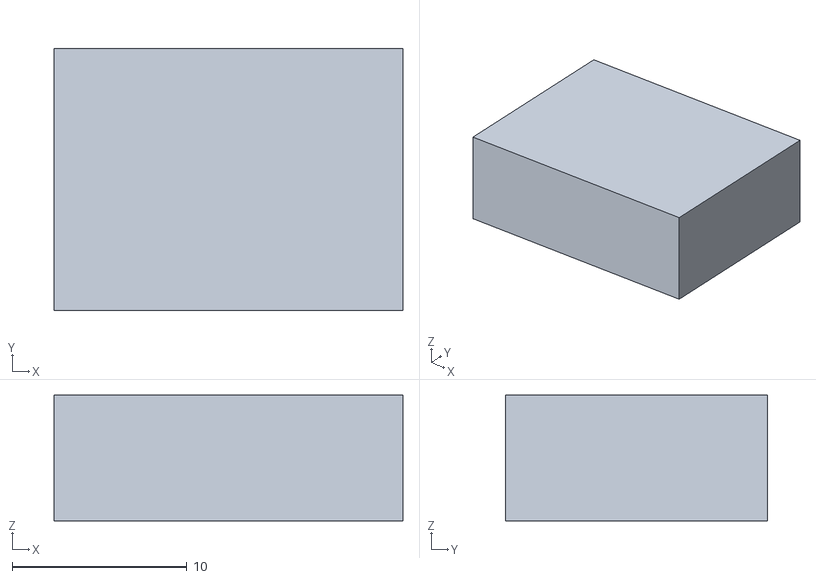
[picture p73: CAD file, 2026-10-08]
hardware/enclosure/jigs/A3_depth_gauge_7_2.stl
20.0 x 15.0 x 7.20
