niravkumar2008/AI-CALCULATOR/hardware/enclosure/replica/stl/Solar_cell__dummy__Solar_cell__dummy.stl

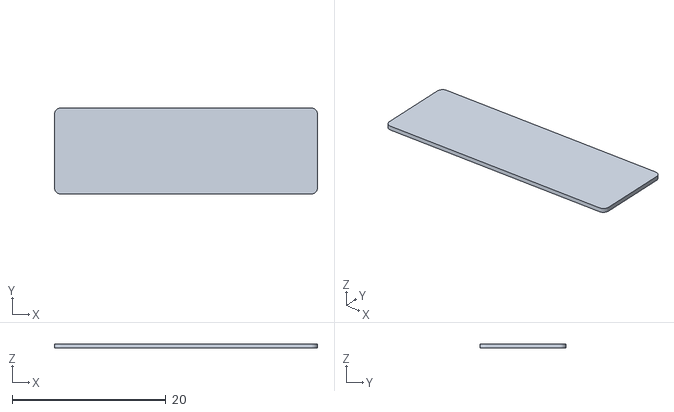
[picture p74: CAD file, 2026-10-08]
hardware/enclosure/replica/stl/Solar_cell__dummy__Solar_cell__dummy.stl
34.2 x 11.2 x 0.55
