niravkumar2008/AI-CALCULATOR/hardware/enclosure/export/ai_calc_case.step

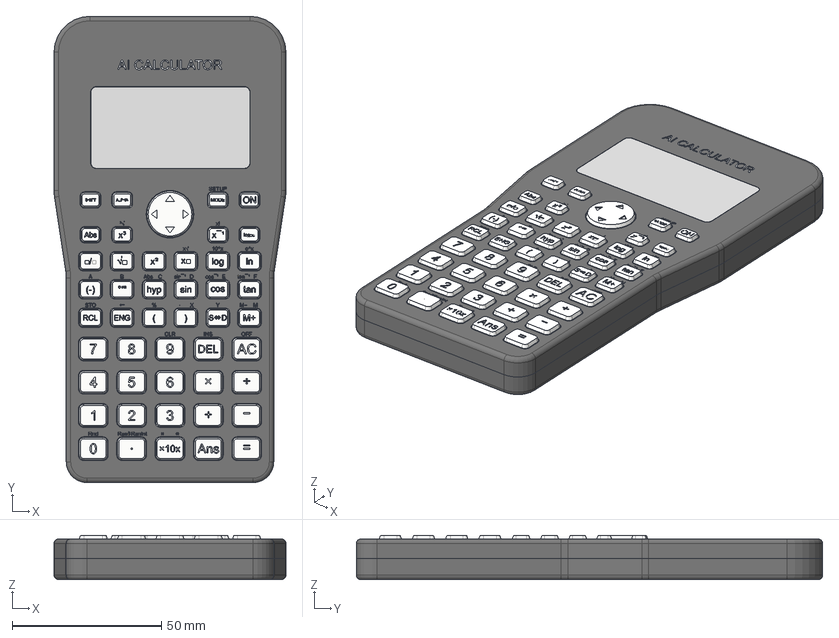
[picture p75: CAD file, 2026-10-03]
hardware/enclosure/export/ai_calc_case.step
77.7 x 156.2 x 14.8 mm
