niravkumar2008/AI-CALCULATOR/hardware/enclosure/jigs/A_back_cover_plate.stl

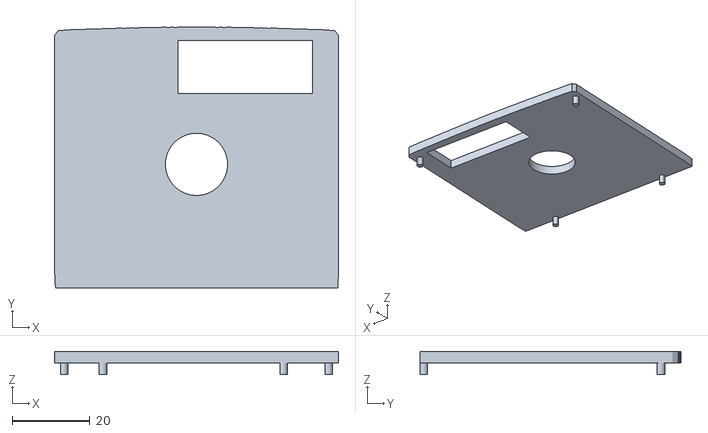
[picture p76: CAD file, 2026-10-08]
hardware/enclosure/jigs/A_back_cover_plate.stl
73.1 x 67.2 x 6.00
