niravkumar2008/AI-CALCULATOR/hardware/enclosure/replica/stl/Back_cover_Back_cover.stl

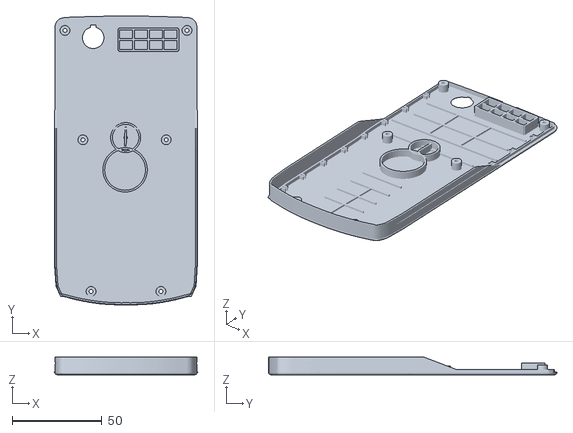
[picture p77: CAD file, 2026-10-08]
hardware/enclosure/replica/stl/Back_cover_Back_cover.stl
79.9 x 161.3 x 9.80
