niravkumar2008/AI-CALCULATOR/hardware/enclosure/replica/stl/keycaps/10_Key_x_2.stl

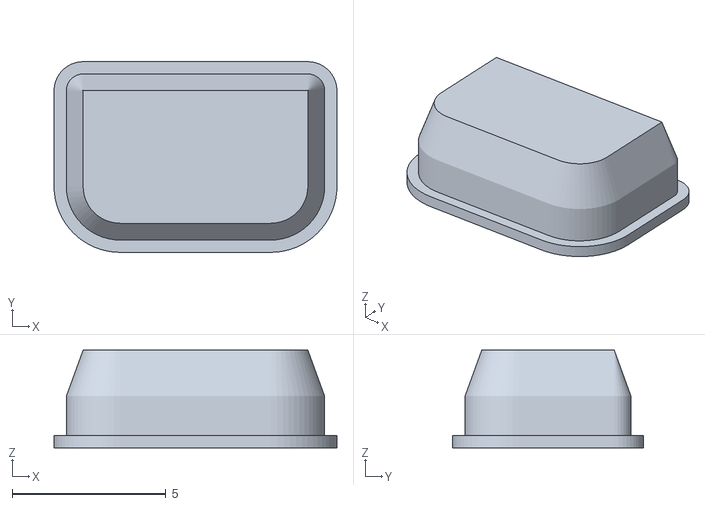
[picture p78: CAD file, 2026-10-08]
hardware/enclosure/replica/stl/keycaps/10_Key_x_2.stl
9.20 x 6.20 x 3.18
