niravkumar2008/AI-CALCULATOR/hardware/enclosure/export/front_shell.stl

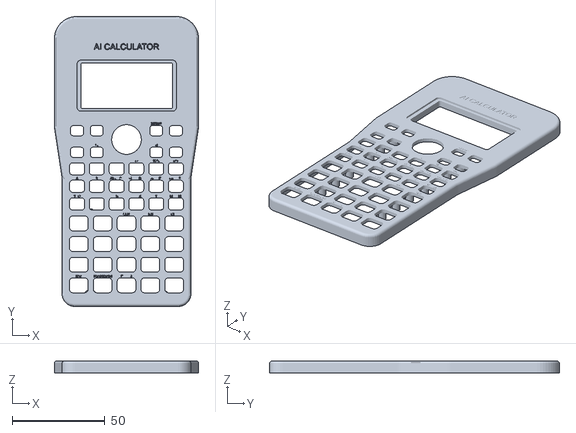
[picture p79: CAD file, 2026-10-03]
hardware/enclosure/export/front_shell.stl
77.7 x 156.2 x 6.60
