niravkumar2008/AI-CALCULATOR/hardware/enclosure/jigs/B_magnet_notch_saddle.stl

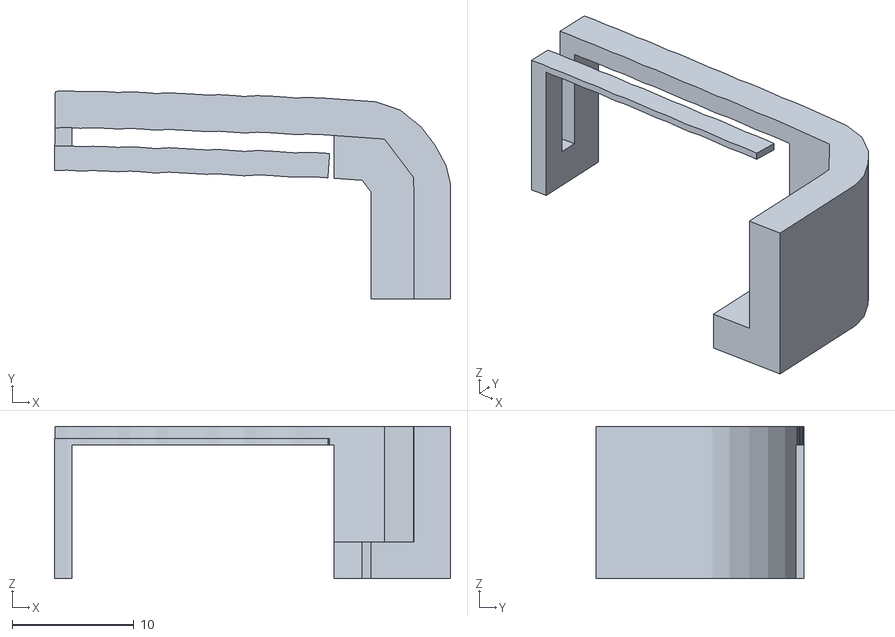
[picture p80: CAD file, 2026-10-08]
hardware/enclosure/jigs/B_magnet_notch_saddle.stl
32.5 x 17.1 x 12.5
