niravkumar2008/AI-CALCULATOR/hardware/enclosure/replica/stl/Slide_case__stored__Slide_case.stl

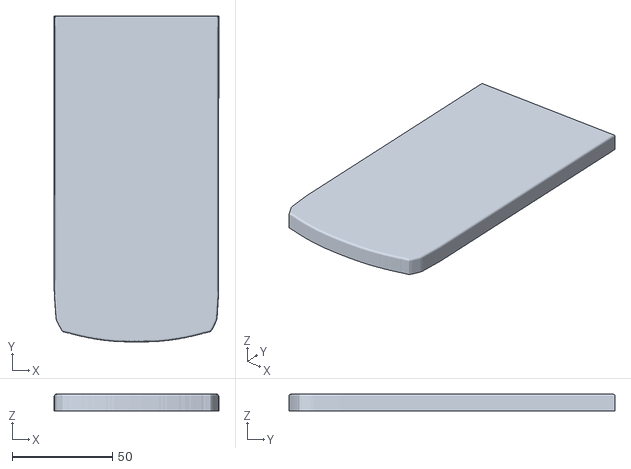
[picture p81: CAD file, 2026-10-08]
hardware/enclosure/replica/stl/Slide_case__stored__Slide_case.stl
81.9 x 162.3 x 8.35
