niravkumar2008/AI-CALCULATOR/hardware/enclosure/replica/stl/keycaps/29_Key_x__1.stl

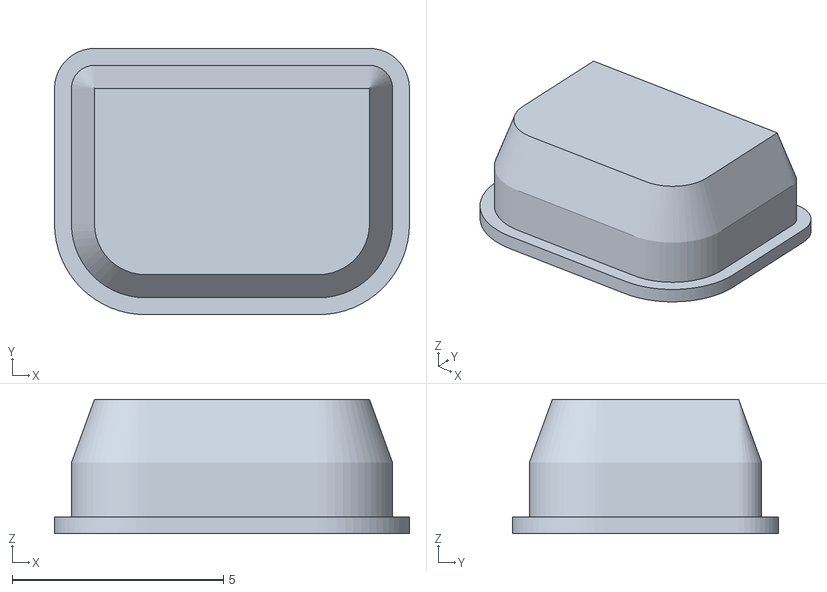
[picture p82: CAD file, 2026-10-08]
hardware/enclosure/replica/stl/keycaps/29_Key_x__1.stl
8.40 x 6.30 x 3.18
