niravkumar2008/AI-CALCULATOR/hardware/enclosure/replica/stl/Window_lens_Window_lens__clear.stl

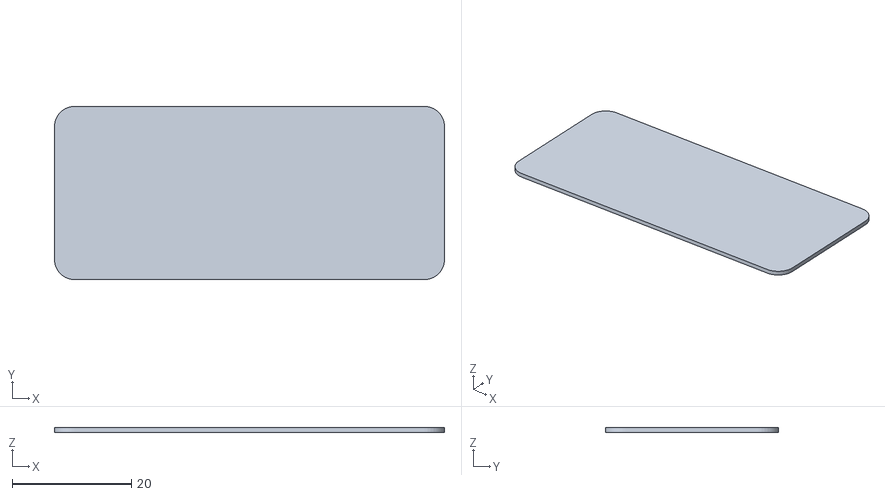
[picture p83: CAD file, 2026-10-08]
hardware/enclosure/replica/stl/Window_lens_Window_lens__clear.stl
65.3 x 29.0 x 0.8
