niravkumar2008/AI-CALCULATOR/hardware/enclosure/replica/stl/Front_shell_Front_shell.stl

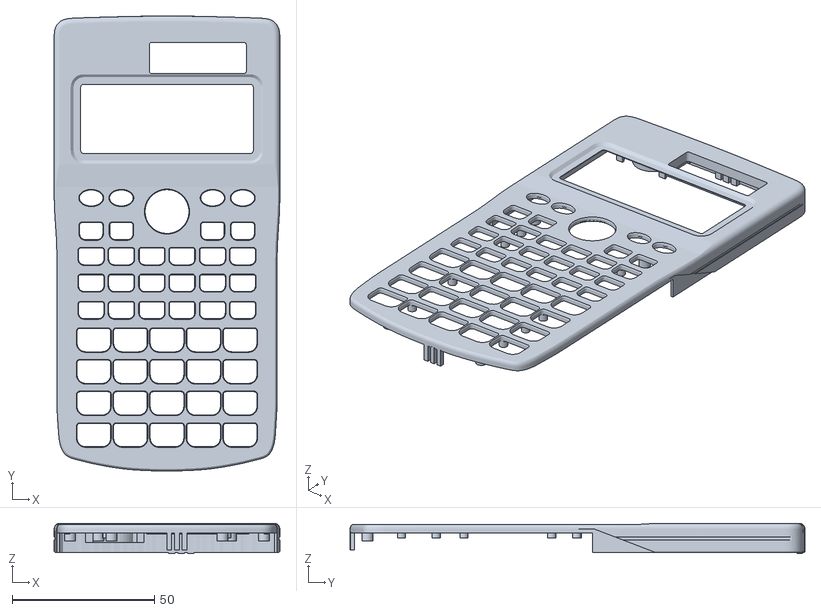
[picture p84: CAD file, 2026-10-08]
hardware/enclosure/replica/stl/Front_shell_Front_shell.stl
79.3 x 159.9 x 10.7
