niravkumar2008/AI-CALCULATOR/hardware/enclosure/replica/stl/Battery_lid_Battery_lid.stl

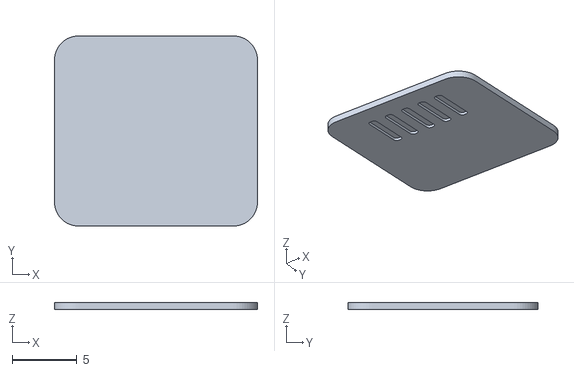
[picture p85: CAD file, 2026-10-08]
hardware/enclosure/replica/stl/Battery_lid_Battery_lid.stl
15.7 x 14.7 x 0.58
