niravkumar2008/AI-CALCULATOR/hardware/enclosure/replica/stl/Slide_cover_Slide_cover.stl

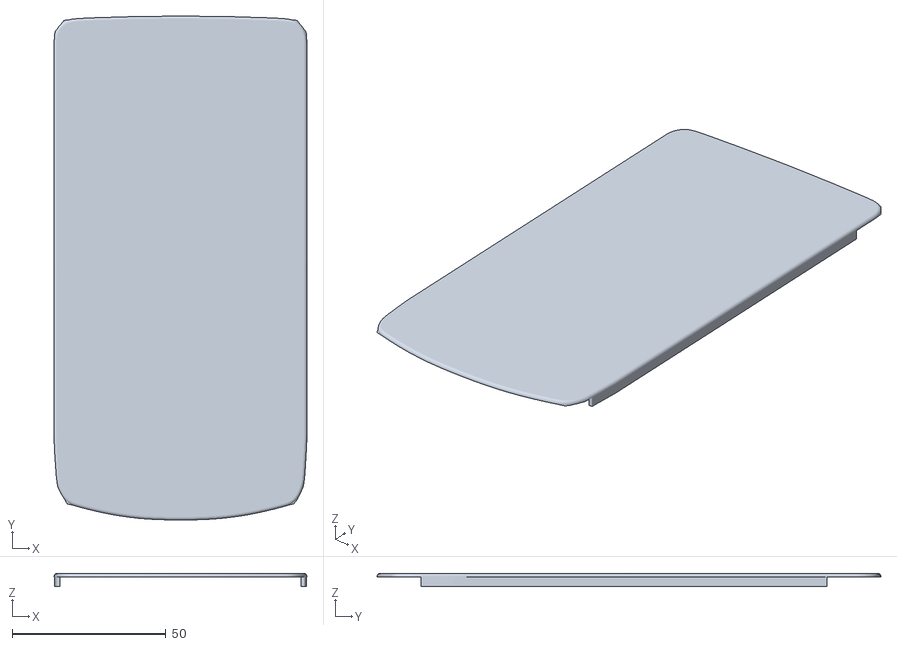
[picture p86: CAD file, 2026-10-08]
hardware/enclosure/replica/stl/Slide_cover_Slide_cover.stl
82.2 x 163.9 x 4.30
