niravkumar2008/AI-CALCULATOR/hardware/enclosure/replica/stl/keycaps_all.stl

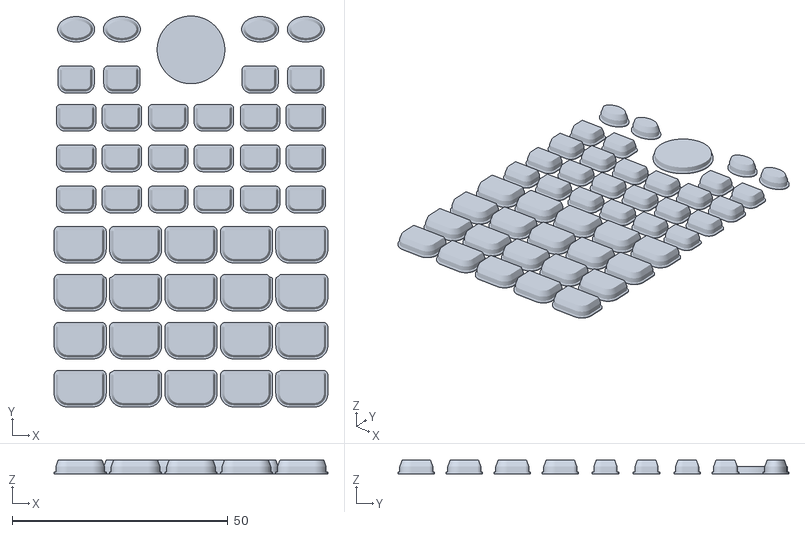
[picture p87: CAD file, 2026-10-08]
hardware/enclosure/replica/stl/keycaps_all.stl
63.5 x 90.6 x 3.18
