niravkumar2008/AI-CALCULATOR/hardware/enclosure/replica/stl/keycaps/46_Key_REPLAY.stl

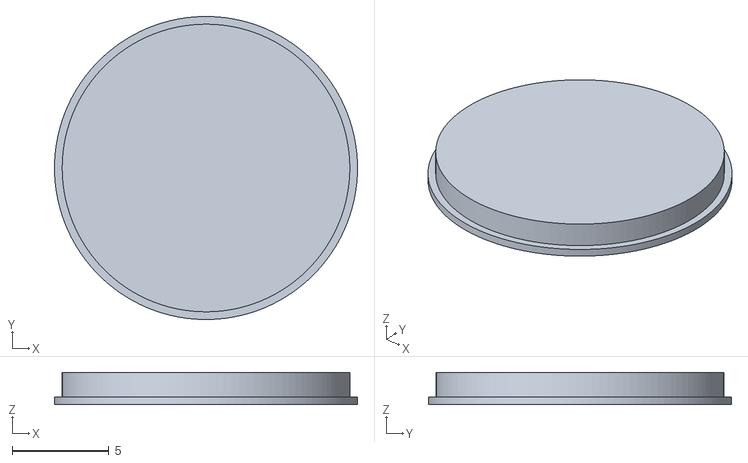
[picture p88: CAD file, 2026-10-08]
hardware/enclosure/replica/stl/keycaps/46_Key_REPLAY.stl
15.7 x 15.7 x 1.68
