niravkumar2008/AI-CALCULATOR/hardware/verification/04_manufacturing.md

# 04 — Manufacturing verification (JLCPCB PCB + PCBA), stage 13b

> **⚠ Superseded by stage 14: see `../FINAL_STATUS.md` and `05_stage14_recheck.md`.** M1/M2 (CPL rotations) are fixed: `fab/` CPL is generated by `tools/jlc_cpl.py`. In JLCPCB's preview rotate nothing; only verify.

Date: 2026-10-04. Board `kicad/ai_calc.kicad_pcb` (saved 04:09), fab files `fab/` (generated 04:11).
Method: gerbers unzipped and parsed with gerbonara, rasterised (20 px/mm) and checked with exact vector geometry (shapely); board data read with KiCad 10 `pcbnew` Python; DRC re-run with kicad-cli; JLCPCB footprints fetched with `easyeda2kicad` for every LCSC number and fitted against the KiCad footprints; live stock and parameters from JLCPCB's parts API. Nothing in `kicad/` or `fab/` was changed.

## Verdict

**Do not upload the CPL in `fab/` as-is.** 8 of the 77 placements will come out wrong in JLCPCB's frame:
- 7 rotated ICs and transistors, including the charger (U2), the 3.3 V regulator (U3) and both camera LDOs.
- J3, whose body would face into the board.

Use `verification/ai_calc_CPL_JLCPCB_corrected.csv` instead, and still check the preview.

The gerbers, drills, BOM and LCSC numbers are good to order. One copper-to-hole clearance on the key side is below JLCPCB's rule, but it is cosmetic: expect a question from JLCPCB, not a dead board.

With the corrected CPL and a preview check, the order is **GO**.

## Findings, by severity

### FATAL (if not corrected)

**M1. CPL rotations for the SOT packages: 7 parts would be placed with pin 1 in the wrong corner.**
- JLCPCB places each part using the EasyEDA footprint of its LCSC number. Those footprints have a different zero orientation from KiCad's.
- The corrections were derived from each part's EasyEDA pad coordinates, matched pin by pin to the KiCad footprint. Each one gives an exact match (residual ≤ 0.2 mm, which is only pad-size differences).
- **Not all SOT-23-5 parts need the same correction:**
  - The "-BL" EasyEDA footprints (U2, U3, U7) are drawn with pin 1 bottom-left and the pins in horizontal rows, so they need **+270°**.
  - The "-BR" footprints (U4, U5) and the SOT-23 (Q1, Q2) need **+180°**.
  - The previous review's "probably 180° for all SOT parts" is wrong for U2, U3 and U7. A 180° click on those would still be 90° off.
- **What happens if they aren't corrected:**
  - U3 (RT9080) reversed puts SYS into VOUT, so there is no 3.3 V.
  - U2 reversed means the charger is dead.
  - Q1 reversed means no battery path.
  - U7 is on the USB lines.

**M2. J3 (magnet socket, C46061768) needs 180°.**
- In the EasyEDA footprint the socket body sits on the **+y side of the pads** (courtyard 2.55–11.05 mm below the pad row). In the KiCad footprint the body runs **towards the top edge** (−y).
- The pads are a symmetric row of 4, so JLCPCB would happily place it at 0°. The body would then face into the board, over D1/D6/R20/U7, with the openings pointing inward.
- At 180° the body points over the top edge as designed. The socket isn't polarised (4 identical contacts), so the reversed "pin numbers" don't matter electrically: contact positions = pads.
- Confidence medium-high: it's based on EasyEDA's silk and courtyard, not the 3D model.

### LIKELY PROBLEM

**M3. Key pad SW1 (B.Cu) is 0.055 mm from the 6.0 mm NPTH hole H3.**
- Where: the bottom bar of SW1 pad 2 (COL0), at x 173.6–179.6, y 122.445–123.045. H3 is at (174.0, 126.1), radius 3.0. See `renders/zoom_SW1_H3_npth_clearance_bottom.png`.
- JLCPCB wants ≥ 0.2 mm from NPTH to copper.
- KiCad DRC did **not** flag it (0/0/0, see below), so the hole-clearance rule apparently isn't applied between this NPTH pad and this SMD pad. It's a real geometry fact in the gerber.
- **Effect:** JLCPCB's CAM will either pull the copper back about 0.2 mm locally or email an engineering question (which holds the order). Electrically harmless: a sliver of one finger of a key contact.
- **Recommendation:** answer "OK to clip copper locally" if asked. Optionally fix in KiCad first by moving H3 or trimming that bar; that is a design change, so not done here.
- SW50 vs H1 is 0.255 mm and the zones are 0.25 mm. Those pass.

**M4. Edge rails / conveyor.**
- U1 overhangs the left edge by about 4.2 mm: the module spans x ≈ 114.7–135.2, and the board edge there is at x ≈ 118.9.
- The left edge also carries C32, D7 and C7 within about 4 mm of it.
- JLCPCB needs clear conveyor edges, so it will very likely add rails (paid) or ask.
- A breakaway rail on the **left** edge would sit under the antenna overhang and is awkward to snap off. Ask for rails only on the short (top/bottom) edges, or accept "no rails" if they agree.
- J3 also overhangs the top edge (see C3), so the top rail must leave J3 free. In practice, **rails on the right edge + bottom edge** is the safe answer.

### CHECK

- **C1. Silkscreen pin-1 marks.**
  - The pin-1 marks on J1, J2, J4, L1 and Q3 use 0.06 mm silk lines (JLCPCB minimum about 0.15 mm), so they may not print.
  - Most other silk is 0.12 mm, which normally prints.
  - It's only cosmetic, but it's the reference JLCPCB's engineer compares against. Use `fab/render_top.png` / the assembly PDF when checking the preview.
- **C2. 0.8 mm board, 71.7 × 148.9 mm, with an LGA module.**
  - Thin, long boards warp in reflow. That's the main risk for U1's hidden pads.
  - Standard PCBA includes X-ray for BGA/QFN-type parts. Ask for **X-ray of U1 and U6** in the order notes (U6 = QFN EP).
  - Keep 0.8 mm only if the enclosure requires it.
- **C3. J3 body position.**
  - The EasyEDA drawing puts the body 1.0 mm further from the pads than the KiCad model does (2.55 vs 1.55 mm).
  - The part will land on the pads either way. If EasyEDA is right, the body overhangs the top edge by about 1.0 mm instead of 0.4 mm. Check with the magnet dry fit.
- **C4. J1 reversed numbering.**
  - J1 uses the `_CamReversed` footprint, so its pad numbers are mirrored relative to the C6364666 EasyEDA footprint.
  - **Geometry** matches exactly at the CPL's 180° (the mounting tabs fix it; at 0° it would be 3.2 mm off).
  - JLCPCB's preview will show EasyEDA "pin 1" at KiCad pin 24's end. That's correct: **do not let them rotate J1**. Tell them the numbering is intentionally reversed and they should align by the pads and mounting tabs.
- **C5. Solder-mask expansion is 0 everywhere.**
  - Every pad does have its own opening (checked pad by pad: 329 top pads, 556 key pads, 0 covered).
  - The dams between 0.5 mm-pitch pads are 0.2 mm, which is within JLCPCB's green-mask capability.
- **C6. TVS D7 leakage.**
  - SMF5.0A has Vrwm 5 V and Ir up to 400 µA (JLCPCB data). With 5.25–5.5 V adapters it conducts a little more, but only while plugged in.
  - Harmless for this design.

### OK (verified)

**Gerbers and drill**
- **Outline:** 2 closed loops, every endpoint degree 2. The outer loop is 71.65 × 148.76 mm. The inner loop is the e-paper slot: 1.0 × 14.0 mm, round ends, x 172.4–173.4.
- **Drills:**
  - PTH = 332 vias, all 0.30 mm drill / 0.60 mm pad, so the annular ring is 0.15 mm (≥ 0.13).
  - NPTH = 4.2 mm and 6.0 mm round holes, plus 4 oval slots (G85): H2 4.2×5.0, H9 4.4×4.8, H13 4.2×4.45, H14 4.2×4.65.
  - Nothing is under 0.3 mm.
- **Copper to the board edge** (exact vector distance to the Edge.Cuts centrelines, including the slot): **≥ 0.30 mm on both layers.** No copper outside the outline.
- **Antenna:** no copper exists under the antenna, because the board stops at x ≈ 118.9 and the antenna overhangs it. There are keep-out areas above and below it.
- **Trace / space:**
  - Minimum trace 0.20 mm (2,529 × 0.2, 356 × 0.25, 35 × 0.3, 113 × 0.5).
  - Minimum clearance 0.15 mm (global and the J1 fan-out rule), 0.2 on the camera netclass.
  - JLCPCB's 2-layer limit is 0.127 / 0.127.
- **Silk:** 0 px over any mask opening and 0 px off-board. B.Silk contains only clear objects, so nothing prints on the key side.
- **Mask:**
  - Every pad has an opening.
  - The ENIG key pads are 100 % exposed, with no silk and no paste.
  - Vias are tented.
  - The only openings without a pad are the 10 NPTH holes.
- **Fiducials:** FID1–3 are 1.0 mm copper with a 2.0 mm mask opening.
- **Paste:**
  - F.Paste sits only on copper inside mask openings. Fiducials and test points have none.
  - B.Paste is empty: there are no bottom-side parts.

**DRC and file freshness**
- **DRC re-run** (scratch copy, `--refill-zones --schematic-parity --severity-all`): **0 violations, 0 unconnected, 0 parity.**
  - Ignored checks: missing courtyard, track-not-centred-on-via, footprint filters, `npth_inside_courtyard`, footprint type mismatch.
- **Fab freshness:**
  - Gerbers and drill are from 04:11, newer than the board (04:09).
  - A fresh drill export is byte-identical apart from dates.
  - Fresh copper differs only by plot-option extras.
  - CPL positions and rotations equal the board for all 77 parts.

**BOM ↔ CPL ↔ schematic**
- 77 = 77 = 77 designators.
- Every LCSC number and footprint in the BOM equals the schematic field and the board field.
- No DNP parts.
- TP, FID, H and SW items are correctly excluded.

**Part ratings (JLCPCB data vs the nets they sit on)**
- C5 (VBUS) 4.7 µF 16 V.
- C11/C13/C15/C16 2.2 µF 6.3 V on the 2.8 / 1.5 V rails: about 1.3 µF effective at bias, still above the ME6211's 1 µF.
- EPD caps C21–C30 1 µF 50 V X5R. C20 4.7 µF 50 V X7R 1206.
- L1 68 µH, Isat 600 mA, 1.38 Ω.
- FB1 200 mA.
- Q1/Q2 AO3401A 30 V, Vgs ±12 V. Q3 SI1308 30 V. B5819W 40 V / 1 A.
- RT9080 5.5 V maximum input. SYS ≤ about 5.2 V via D1.
- MCP73831 6 V. JST-PH 2 A.

**Stock (live, 2026-10-04)**
- ESP32-S3-MINI-1-N4R2 C3013941: 1,888.
- L1: 5,250. MCP73831: 8,799. J3: 8,753.
- Everything else ≥ 13 k.
- 14 Extended part types (14 × $3 loading fee). The rest are Basic.
- JLCPCB adds attrition automatically: about 10 extra pieces per 0402/0603 line, 2–4 on SOT lines, 0 on U1, U6, J1/J2 and J3. That is cents in total.

**Assembly**
- Top side only.
- Courtyards touch but never overlap. The closest pairs are R2/D1, R1/C4, J3/R4, U1/C1 and U1/C3 at 0.0–0.03 mm courtyard-to-courtyard, which still leaves about 0.4–0.5 mm body-to-body. That's OK for JLCPCB's nozzles.
- Tallest parts: J4 5.5 mm, J3 about 5 mm, U1 2.4 mm. No parts underneath.

## Rotation table

JLCPCB rotation = KiCad rotation + Δ.
- "Offset" = how far the EasyEDA origin sits from the KiCad origin.
- All offsets are 0 except the pad-geometry residuals noted.
- **U1 has no 2.55 mm offset:** EasyEDA's origin is also the pad-area centre, with the antenna on the same side.

| Ref | LCSC | EasyEDA footprint | CPL rot (fab) | JLCPCB needs | Δ | Offset | Confidence |
|---|---|---|---|---|---|---|---|
| Q1 | C15127 | SOT-23 …-BR | 0 | **180** | +180 | 0 | High |
| Q2 | C15127 | SOT-23 …-BR | 90 | **270** | +180 | 0 | High |
| U2 | C424093 | SOT-23-5 …-BL | 0 | **270** | +270 | 0 | High |
| U3 | C841192 | TSOT-23-5 …-BL | 0 | **270** | +270 | 0 | High |
| U4 | C53099 | SOT-23-5 …-BR | 0 | **180** | +180 | 0 | High |
| U5 | C53100 | SOT-23-5 …-BR | 0 | **180** | +180 | 0 | High |
| U7 | C7519 | SOT-23-6 …-BL | 0 | **270** | +270 | 0 | High |
| J3 | C46061768 | HX-PM2.54-1X4PWT | 0 | **180** | +180 | 0 (body 1 mm further out) | Med-high |
| Q3 | C469327 | SOT-323 …-BR | 0 | 0 | 0 | 0 (identical pads) | High |
| U6 | C138713 | WQFN-24 …-TL | 0 | 0 | 0 | 0 (rms 0.08 mm) | High |
| U1 | C3013941 | ESP32-S3-MINI-1 | 90 | 90 | 0 | 0 (60 pins matched, rms 0.025 mm) | High |
| J1 | C6364666 | FPC-0.5-24P-HYH2.0 | 180 | 180 | 0 (geometry) | 0 | High (pin numbers intentionally reversed) |
| J2 | C6364666 | same | −90 | −90 | 0 | 0 | High |
| J4 | C295747 | S2B-PH-SM4-TB | 0 | 0 | 0 | 0 (tabs make it unambiguous) | High |
| D1–D6 | C8598 | SOD-123 (band = pad 1) | 0 | 0 | 0 | 0 | High |
| D7 | C193402 | SOD-123FL (band = pad 1) | 180 | 180 | 0 | 0 | High (cathode on VBUS, right pad) |
| L1, FB1, R, C | various | — | as is | as is | 0 | 0 | High (non-polar) |

## Instructions

1. Upload `hardware/verification/ai_calc_CPL_JLCPCB_corrected.csv` as the CPL, with the unchanged `fab/` gerber zip and BOM. Only the 8 rotations above differ from `fab/`.
2. In the placement preview, confirm:
   - **U2, U3, U4, U5, U7:** pin-1 dot top-left.
   - **Q1:** pins 1–2 on the left, pin 3 on the right.
   - **Q2:** single pin on top.
   - **J3:** body over the top edge.
   - **J1:** don't rotate it (C4).
   - **D7:** band on the right.
   - **U1:** antenna off the left edge.

   If the preview disagrees with this table, the preview wins: JLCPCB's library can change.
3. Order notes:
   - "J1 pin numbering intentionally reversed vs library, align to pads/tabs."
   - "U1 antenna and J3 overhang board edges intentionally; rails only on right/bottom edges please."
   - "X-ray U1/U6."
   - "OK to pull back copper at H3 on the bottom layer."
4. Once the order is final, regenerate the CPL from KiCad with these rotations, or keep the corrected file next to the order record.

## Renders (`hardware/verification/renders/`)

- `layer_*.png`: each gerber/drill layer on its own.
- `composite_top.png` / `composite_bottom_mirrored.png`: what the fab sees (gold = exposed ENIG).
- Zooms:
  - `zoom_U1_antenna_*`
  - `zoom_SW1_H3_npth_clearance_bottom` (M3)
  - `zoom_J3_J4_D7_top`
  - `zoom_epaper_slot_J2`
  - `zoom_J1_U4_U5`
