niravkumar2008/AI-CALCULATOR/hardware/enclosure/final_assembly_v15_lcd/key_pills.md

# Key pads vs key-mat pills (v15-LCD final board)

Made by `key_pills_v15.py` from the final `kicad_v15_lcd/ai_calc_v15_lcd.kicad_pcb`. Pill = the carbon dot on the Casio key mat. **Casio** = pill centre measured in verification 15 (mean of three photo fits, +-0.4 mm rows 3-9, +-0.6-0.8 mm top row and ring). **Model** = where the CAD keymat dome / keycap sits (the replica places it on the v14 pad centre, board_snapshot.json). On bbox = share of the pill on the pad's copper outline (review-15 metric); on copper = share on the finger metal itself; gaps = finger-to-finger gaps the pill bridges (1 is enough to close the key); worst 0.7 = on-bbox share if the pill is 0.7 mm off in the worst direction.

| Ref | Key | Pad centre (KiCad) | Pill Ø | Casio pill offset | on bbox | on copper | gaps | worst 0.7 | Model dome offset | on bbox | gaps |
|---|---|---|---|---|---|---|---|---|---|---|---|
| SW1 (moved) | SHIFT | 177.750, 119.800 | 3.8 | 0.03 | 100 % | 58 % | 5 | 95 % | 1.50 | 88 % | 4 |
| SW2 (moved) | ALPHA | 167.150, 120.800 | 3.9 | 0.21 | 100 % | 59 % | 5 | 90 % | 1.12 | 100 % | 4 |
| SW3 | MODE | 133.974, 120.795 | 3.6 | 0.59 | 100 % | 62 % | 4 | 92 % | 0.00 | 100 % | 5 |
| SW4 | CALC | 176.623, 132.450 | 3.8 | 0.35 | 100 % | 61 % | 5 | 89 % | 0.00 | 100 % | 5 |
| SW5 | ∫dx | 166.026, 132.450 | 3.8 | 0.22 | 100 % | 59 % | 5 | 92 % | 0.00 | 100 % | 5 |
| SW6 | x⁻¹ | 133.974, 132.450 | 3.5 | 0.25 | 100 % | 59 % | 4 | 96 % | 0.00 | 100 % | 5 |
| SW7 | logₐb | 123.377, 132.450 | 3.5 | 0.43 | 100 % | 59 % | 4 | 97 % | 0.00 | 100 % | 5 |
| SW8 | a/b | 176.623, 141.325 | 3.7 | 0.34 | 100 % | 60 % | 5 | 90 % | 0.00 | 100 % | 5 |
| SW9 | √ | 166.026, 141.325 | 3.8 | 0.40 | 100 % | 62 % | 5 | 87 % | 0.00 | 100 % | 5 |
| SW10 | x² | 155.298, 141.325 | 3.7 | 0.24 | 100 % | 59 % | 5 | 91 % | 0.00 | 100 % | 5 |
| SW11 | x^n | 144.702, 141.325 | 3.6 | 0.32 | 100 % | 60 % | 5 | 90 % | 0.00 | 100 % | 5 |
| SW12 | log | 133.974, 141.325 | 3.5 | 0.27 | 100 % | 59 % | 4 | 94 % | 0.00 | 100 % | 5 |
| SW13 | ln | 123.377, 141.325 | 3.5 | 0.21 | 100 % | 59 % | 5 | 93 % | 0.00 | 100 % | 5 |
| SW14 | (−) | 176.623, 150.728 | 3.7 | 0.12 | 100 % | 58 % | 5 | 94 % | 0.00 | 100 % | 5 |
| SW15 | °'" | 166.026, 150.728 | 3.7 | 0.16 | 100 % | 59 % | 5 | 96 % | 0.00 | 100 % | 5 |
| SW16 | hyp | 155.298, 150.728 | 3.6 | 0.19 | 100 % | 58 % | 4 | 94 % | 0.00 | 100 % | 5 |
| SW17 | sin | 144.702, 150.728 | 3.6 | 0.05 | 100 % | 58 % | 5 | 97 % | 0.00 | 100 % | 5 |
| SW18 | cos | 133.974, 150.728 | 3.5 | 0.06 | 100 % | 57 % | 5 | 97 % | 0.00 | 100 % | 5 |
| SW19 | tan | 123.377, 150.728 | 3.5 | 0.10 | 100 % | 58 % | 4 | 98 % | 0.00 | 100 % | 5 |
| SW20 | RCL | 176.623, 160.265 | 3.7 | 0.34 | 100 % | 61 % | 5 | 89 % | 0.00 | 100 % | 5 |
| SW21 | ENG | 166.026, 160.265 | 3.6 | 0.33 | 100 % | 60 % | 5 | 90 % | 0.00 | 100 % | 5 |
| SW22 | ( | 155.298, 160.265 | 3.6 | 0.43 | 100 % | 61 % | 5 | 87 % | 0.00 | 100 % | 5 |
| SW23 | ) | 144.702, 160.265 | 3.5 | 0.44 | 100 % | 62 % | 4 | 89 % | 0.00 | 100 % | 5 |
| SW24 | S⇔D | 133.974, 160.265 | 3.5 | 0.37 | 100 % | 59 % | 5 | 89 % | 0.00 | 100 % | 5 |
| SW25 | M+ | 123.377, 160.265 | 3.5 | 0.40 | 100 % | 61 % | 4 | 91 % | 0.00 | 100 % | 5 |
| SW26 | 7 | 175.695, 170.728 | 4.9 | 0.15 | 100 % | 60 % | 6 | 100 % | 0.00 | 100 % | 7 |
| SW27 | 8 | 162.848, 170.728 | 4.9 | 0.32 | 100 % | 62 % | 6 | 100 % | 0.00 | 100 % | 7 |
| SW28 | 9 | 150.000, 170.728 | 4.9 | 0.09 | 100 % | 60 % | 7 | 100 % | 0.00 | 100 % | 7 |
| SW29 | DEL | 137.152, 170.728 | 4.9 | 0.08 | 100 % | 60 % | 7 | 100 % | 0.00 | 100 % | 7 |
| SW30 | AC | 124.305, 170.728 | 4.9 | 0.27 | 100 % | 61 % | 6 | 100 % | 0.00 | 100 % | 7 |
| SW31 | 4 | 175.695, 181.854 | 4.9 | 0.10 | 100 % | 61 % | 6 | 100 % | 0.00 | 100 % | 7 |
| SW32 | 5 | 162.848, 181.854 | 4.9 | 0.18 | 100 % | 60 % | 6 | 100 % | 0.00 | 100 % | 7 |
| SW33 | 6 | 150.000, 181.854 | 4.9 | 0.50 | 100 % | 62 % | 6 | 100 % | 0.00 | 100 % | 7 |
| SW34 | × | 137.152, 181.854 | 4.9 | 0.15 | 100 % | 61 % | 6 | 100 % | 0.00 | 100 % | 7 |
| SW35 | ÷ | 124.305, 181.854 | 4.9 | 0.18 | 100 % | 60 % | 7 | 100 % | 0.00 | 100 % | 7 |
| SW36 | 1 | 175.695, 192.980 | 4.9 | 0.14 | 100 % | 59 % | 6 | 100 % | 0.00 | 100 % | 7 |
| SW37 | 2 | 162.848, 192.980 | 4.9 | 0.09 | 100 % | 60 % | 7 | 100 % | 0.00 | 100 % | 7 |
| SW38 | 3 | 150.000, 192.980 | 4.9 | 0.09 | 100 % | 59 % | 7 | 100 % | 0.00 | 100 % | 7 |
| SW39 | + | 137.152, 192.980 | 4.9 | 0.11 | 100 % | 61 % | 6 | 100 % | 0.00 | 100 % | 7 |
| SW40 | − | 124.305, 192.980 | 4.9 | 0.11 | 100 % | 60 % | 7 | 100 % | 0.00 | 100 % | 7 |
| SW41 | 0 | 175.695, 204.106 | 5.0 | 0.11 | 96 % | 61 % | 6 | 86 % | 0.00 | 96 % | 7 |
| SW42 | . | 162.848, 204.106 | 4.9 | 0.05 | 97 % | 61 % | 7 | 87 % | 0.00 | 97 % | 7 |
| SW43 | ×10^x | 150.000, 204.106 | 4.9 | 0.02 | 97 % | 61 % | 7 | 87 % | 0.00 | 97 % | 7 |
| SW44 | Ans | 137.152, 204.106 | 4.9 | 0.04 | 97 % | 62 % | 7 | 87 % | 0.00 | 97 % | 7 |
| SW45 | = | 124.305, 204.106 | 5.0 | 0.11 | 96 % | 62 % | 6 | 87 % | 0.00 | 96 % | 7 |
| SW46 | UP | 150.000, 119.000 | 3.5 | 0.73 | 92 % | 60 % | 4 | 70 % | 1.27 | 76 % | 4 |
| SW47 | DOWN | 150.000, 131.900 | 3.4 | 0.29 | 100 % | 62 % | 4 | 86 % | 1.04 | 84 % | 4 |
| SW48 | LEFT | 156.623, 125.563 | 3.6 | 0.60 | 94 % | 61 % | 4 | 75 % | 0.00 | 100 % | 4 |
| SW49 | RIGHT | 143.377, 125.563 | 3.4 | 0.82 | 91 % | 59 % | 4 | 69 % | 0.00 | 100 % | 4 |
| SW50 (moved) | ON | 122.450, 119.550 | 3.5 | 0.02 | 100 % | 56 % | 5 | 97 % | 1.55 | 85 % | 4 |
