niravkumar2008/AI-CALCULATOR/Claude outputs/tests/golden/answer_chem_steps.txt

icons: UP DN
.............................................................................................................................
.............................................................................................................................
.............................................................................................................................
.............................................................................................................................
.............................................................................................................................
.............................................................................................................................
.............................................................................................................................
.............................................................................................................................
####..##.........#........................#.......#..#.......##....#.........................................................
...#.#..........#.#......................#.#......#..#......#..#..#.#........................................................
.##..###........#.#.......###.......##...#........####......#..#....#........................................................
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
.............................................................................................................................
.............................................................................................................................
