niravkumar2008/AI-CALCULATOR/Claude outputs/tests/golden/menu_setup.txt

icons: -- --
...............#..#..........................###...........................................###...............................
...............####..........................#..#.........................................#...#..............................
...............####..........................#..#...........................................#................................
...............#..#..........................#..#..........................................#.#...............................
...............#..#..........................#..#............................................................................
...............#..#..........................###............................................#................................
.............................................................................................................................
.........################....................................................................................................
..#......#...############...............................##.......###..........#..............................................
.##...##.#.##.###########..............................#..#..##..#..#.........#..............................................
..#...##.#.##.##..###...#.................................#..##..#..#..###..###..............................................
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
.............................................................................................................................
.............................................................................................................................
