niravkumar2008/AI-CALCULATOR/hardware/enclosure/final_assembly/renders/antenna_corner.png

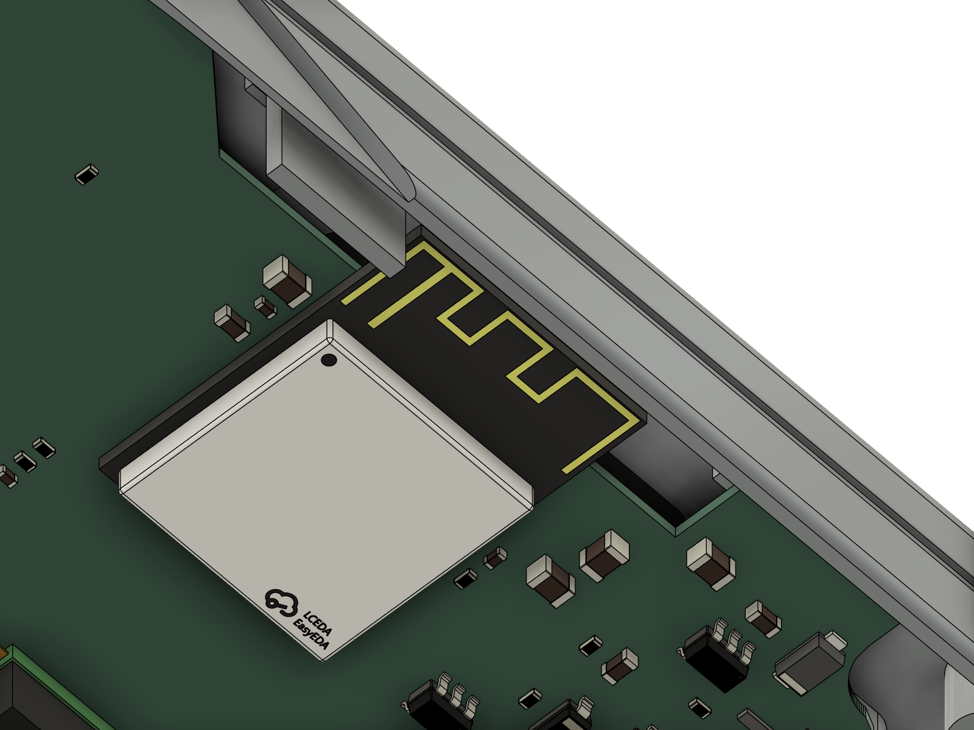
hardware/enclosure/final_assembly/renders/antenna_corner.png
