niravkumar2008/AI-CALCULATOR/hardware/enclosure/final_assembly/renders/back_cover_off_closeup_top.png

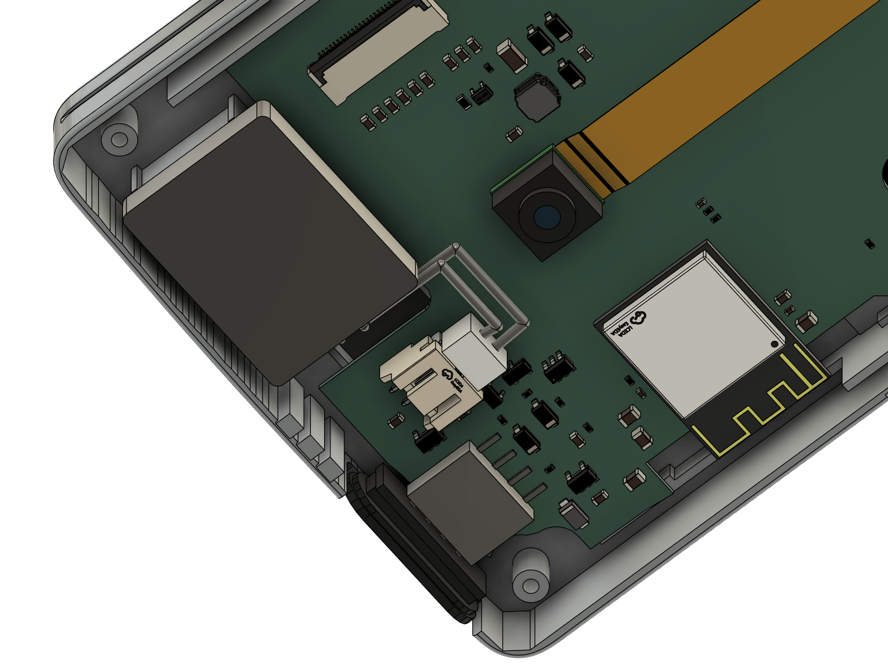
hardware/enclosure/final_assembly/renders/back_cover_off_closeup_top.png
