niravkumar2008/AI-CALCULATOR/hardware/enclosure/final_assembly/renders/battery_upgrade/cell_after_top.png

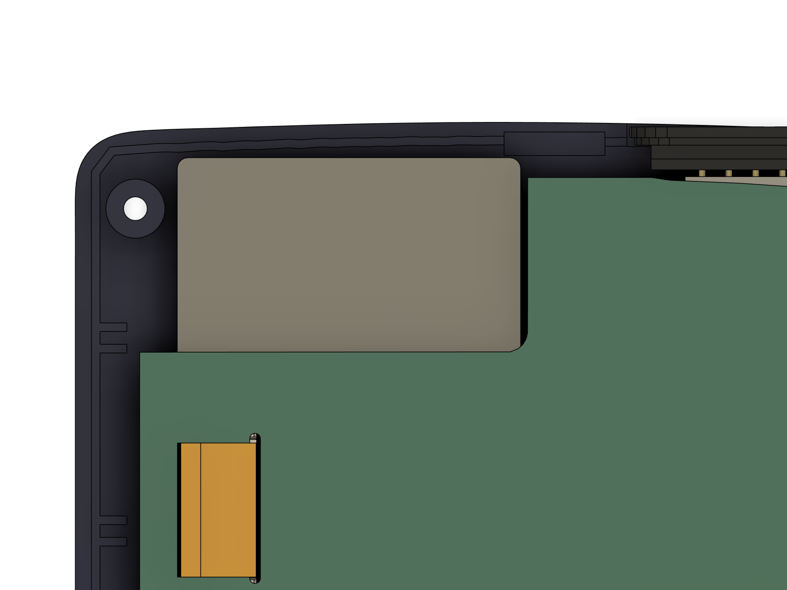
hardware/enclosure/final_assembly/renders/battery_upgrade/cell_after_top.png
