niravkumar2008/AI-CALCULATOR/hardware/enclosure/final_assembly/renders/battery_upgrade/envelope_custom.png

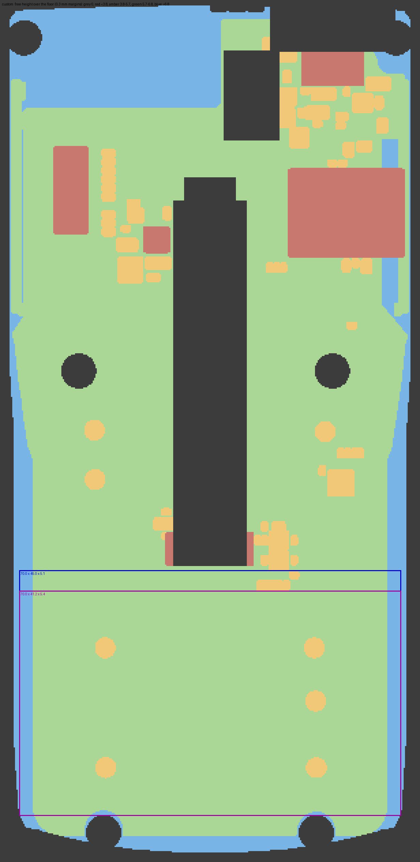
hardware/enclosure/final_assembly/renders/battery_upgrade/envelope_custom.png
