niravkumar2008/AI-CALCULATOR/hardware/enclosure/final_assembly/renders/battery_upgrade/lr44_holder_before.png

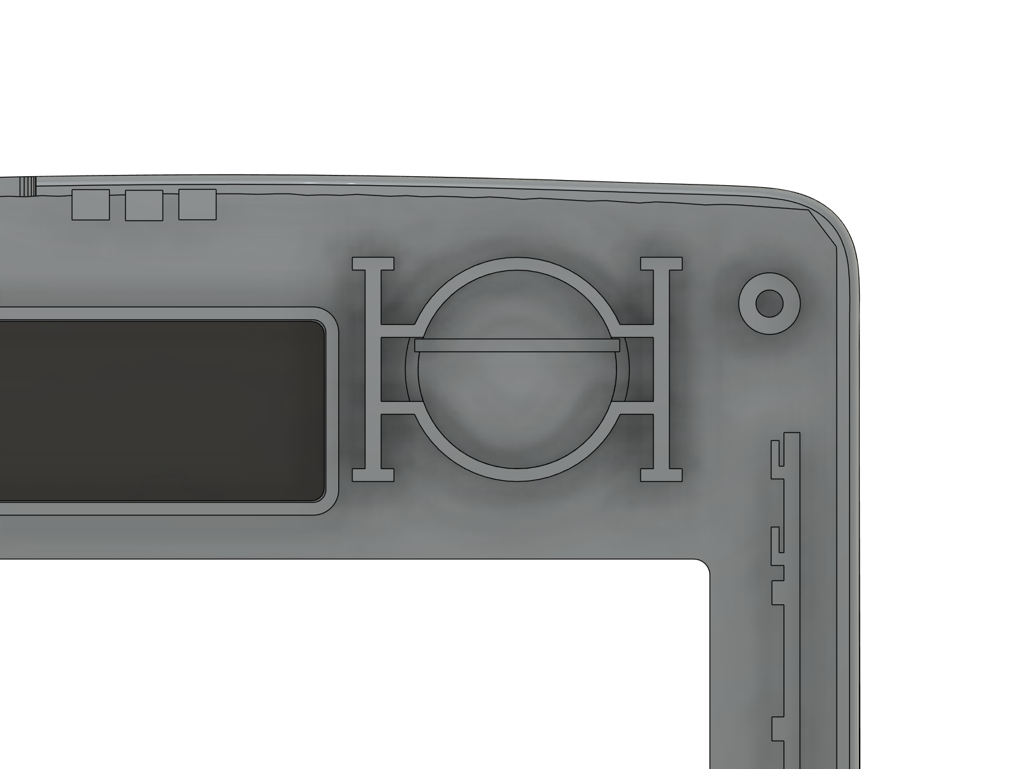
hardware/enclosure/final_assembly/renders/battery_upgrade/lr44_holder_before.png
