niravkumar2008/AI-CALCULATOR/hardware/enclosure/final_assembly/renders/case_camera_hole_section.png

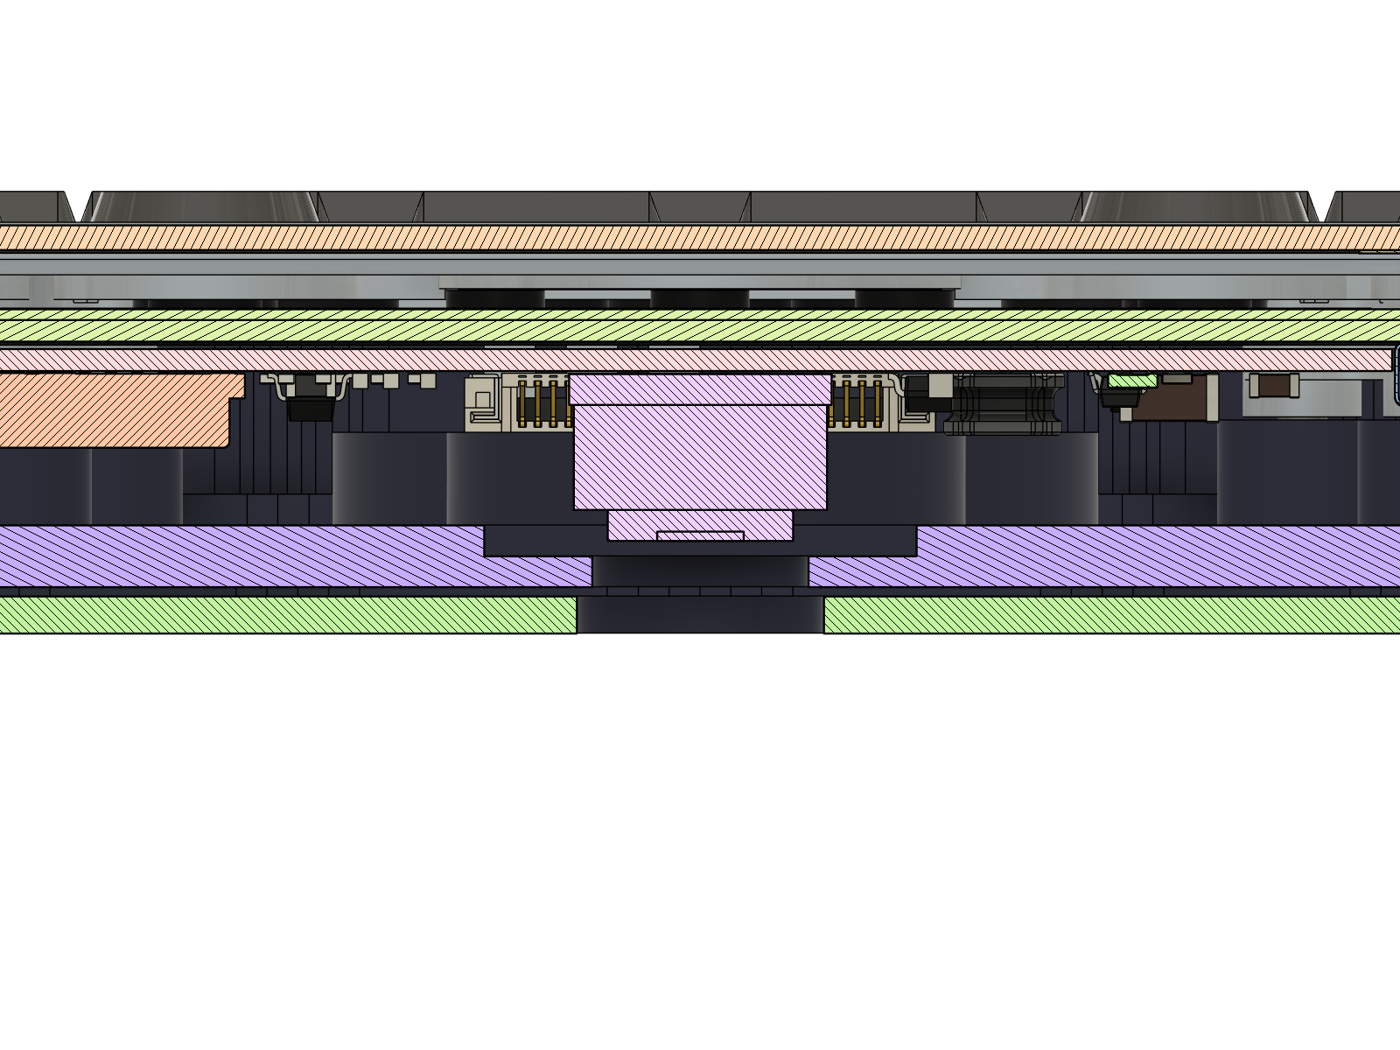
hardware/enclosure/final_assembly/renders/case_camera_hole_section.png
