niravkumar2008/AI-CALCULATOR/hardware/enclosure/final_assembly/renders/case_magnet_closeup_stored.png

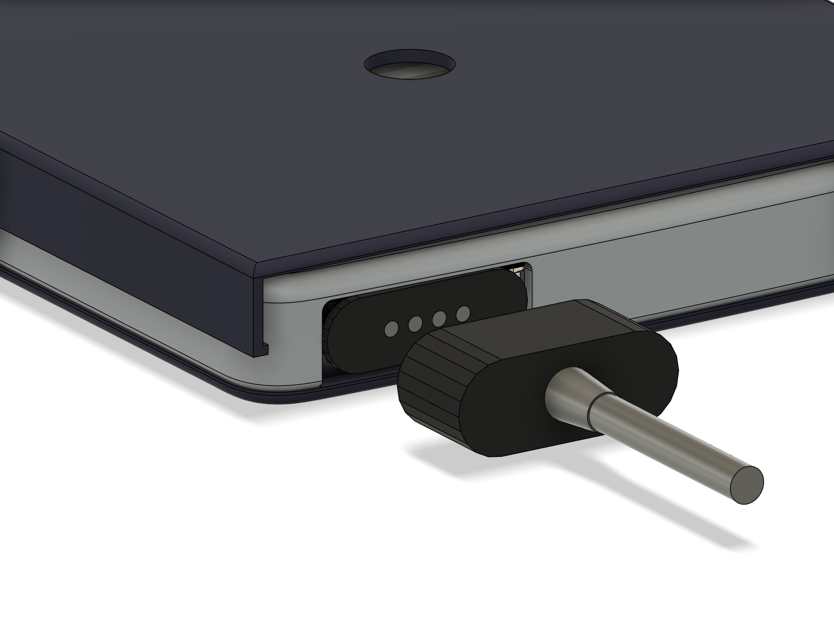
hardware/enclosure/final_assembly/renders/case_magnet_closeup_stored.png
