niravkumar2008/AI-CALCULATOR/hardware/enclosure/final_assembly/renders/compare/back_cad.png

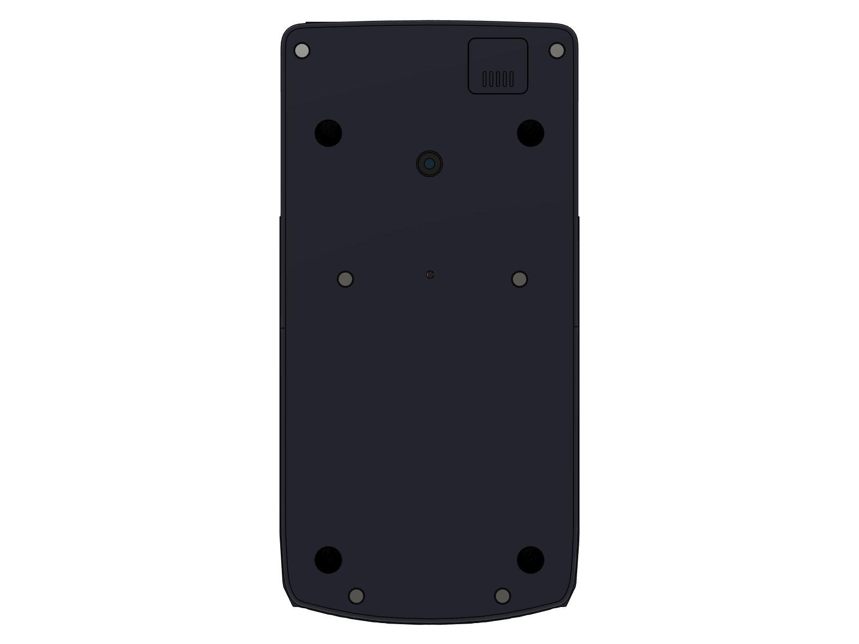
hardware/enclosure/final_assembly/renders/compare/back_cad.png
