niravkumar2008/AI-CALCULATOR/hardware/enclosure/final_assembly/renders/compare/back_cover_inside_persp_cad.png

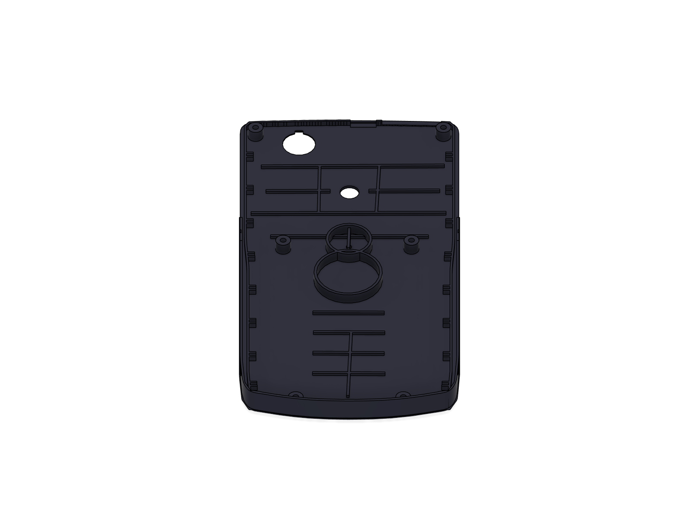
hardware/enclosure/final_assembly/renders/compare/back_cover_inside_persp_cad.png
