niravkumar2008/AI-CALCULATOR/hardware/enclosure/final_assembly/renders/compare/cmp_back_cover_inside_2f54d6c7.jpg

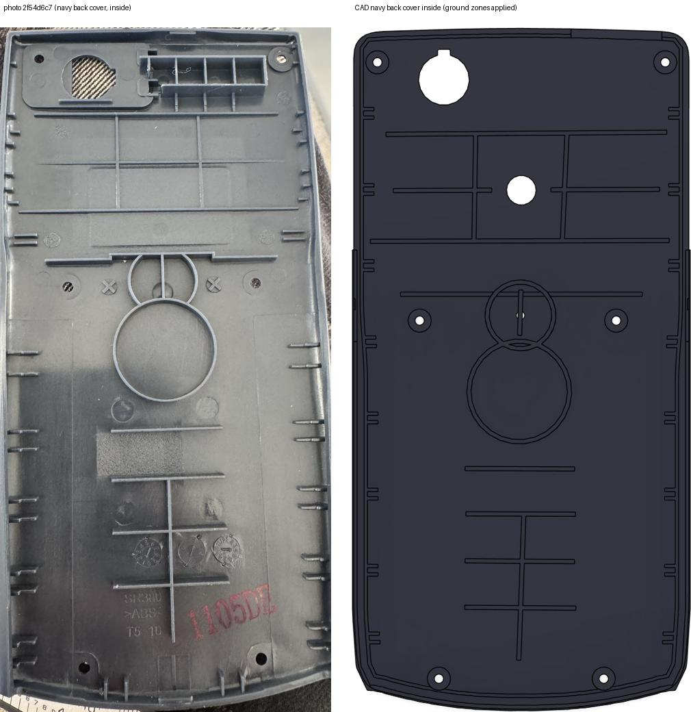
hardware/enclosure/final_assembly/renders/compare/cmp_back_cover_inside_2f54d6c7.jpg
