niravkumar2008/AI-CALCULATOR/hardware/enclosure/final_assembly/renders/compare/cmp_faceplate_inside_e82c982d.jpg

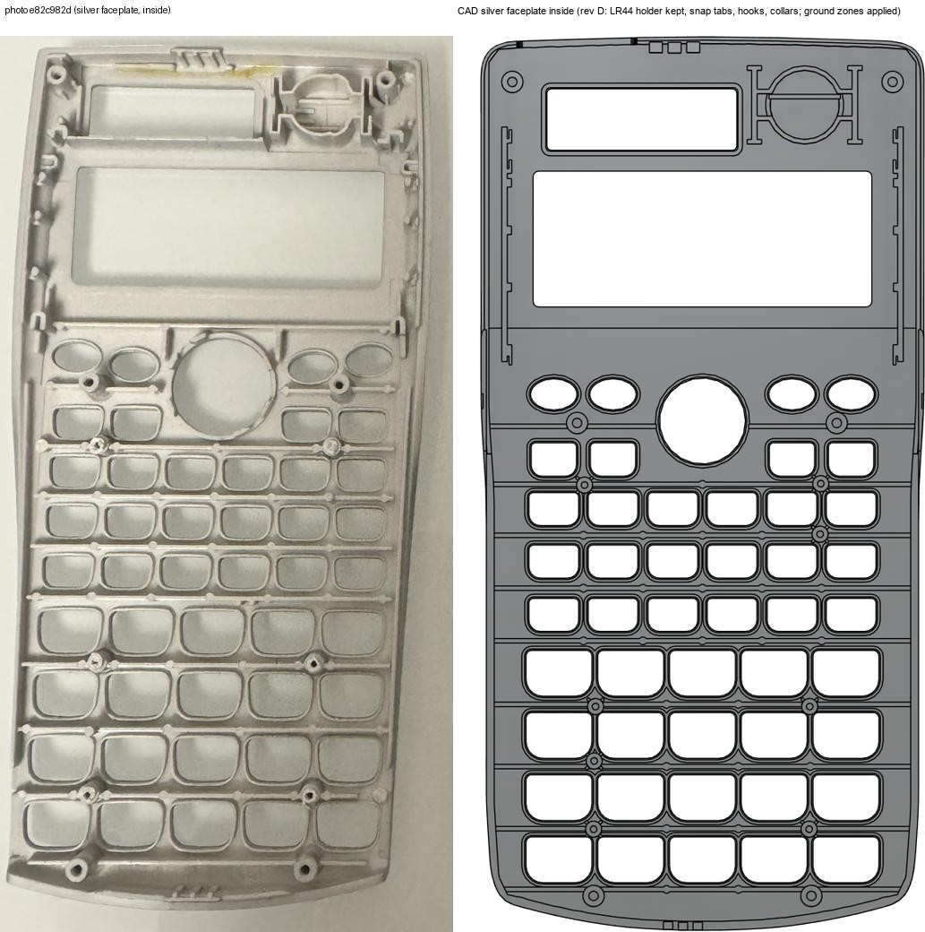
hardware/enclosure/final_assembly/renders/compare/cmp_faceplate_inside_e82c982d.jpg
