niravkumar2008/AI-CALCULATOR/hardware/enclosure/final_assembly/renders/compare/cmp_front_e59eff71.jpg

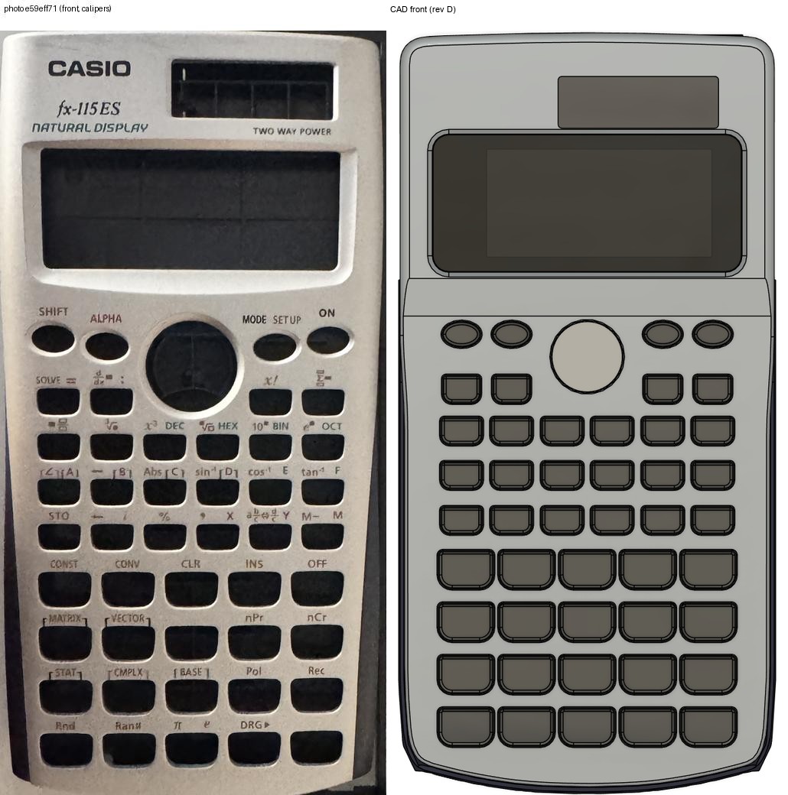
hardware/enclosure/final_assembly/renders/compare/cmp_front_e59eff71.jpg
