niravkumar2008/AI-CALCULATOR/hardware/enclosure/final_assembly/renders/compare/front_shell_inside_cad.png

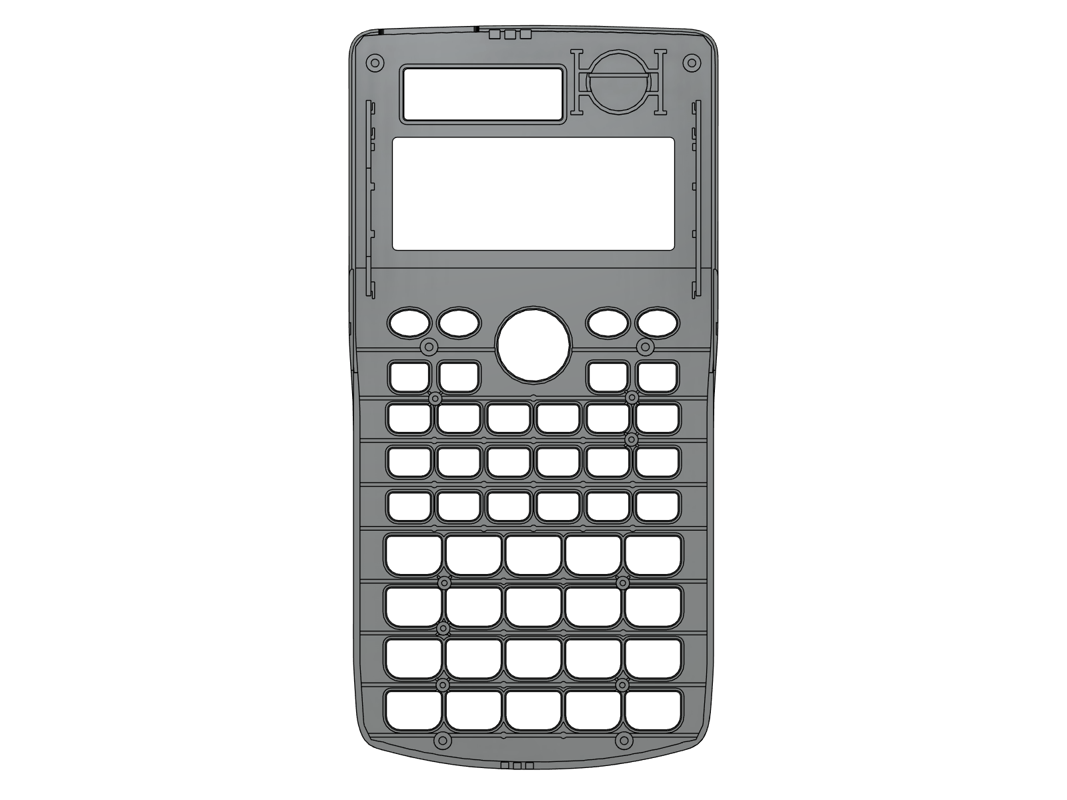
hardware/enclosure/final_assembly/renders/compare/front_shell_inside_cad.png
