niravkumar2008/AI-CALCULATOR/hardware/enclosure/final_assembly/renders/compare/side_cad.png

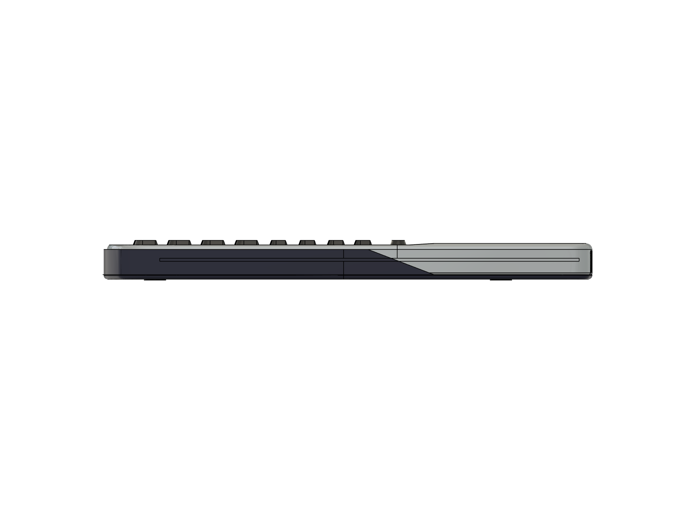
hardware/enclosure/final_assembly/renders/compare/side_cad.png
