niravkumar2008/AI-CALCULATOR/hardware/enclosure/final_assembly/renders/detail/d03_j2_latch_open.png

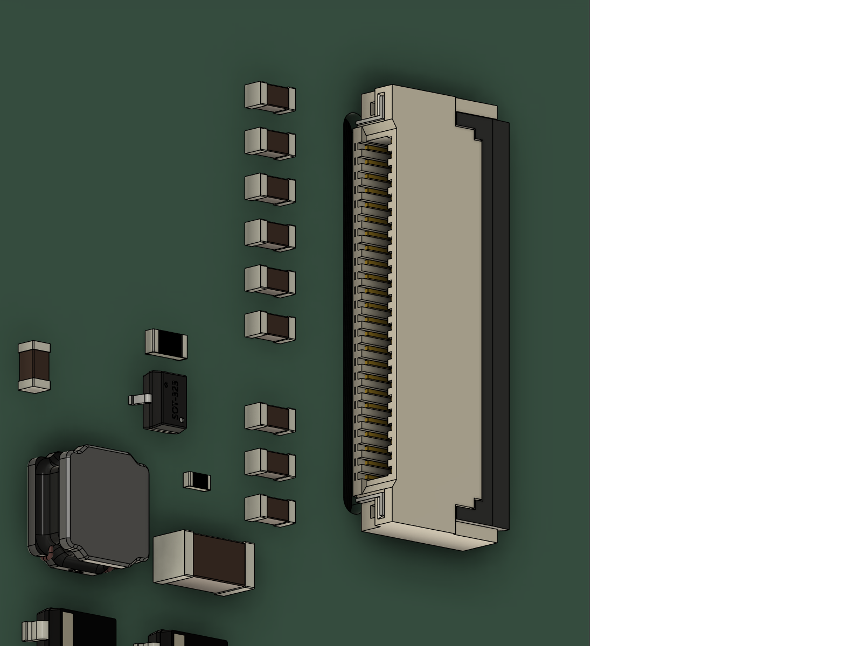
hardware/enclosure/final_assembly/renders/detail/d03_j2_latch_open.png
