niravkumar2008/AI-CALCULATOR/hardware/enclosure/final_assembly/renders/detail/d05_camera_tape.png

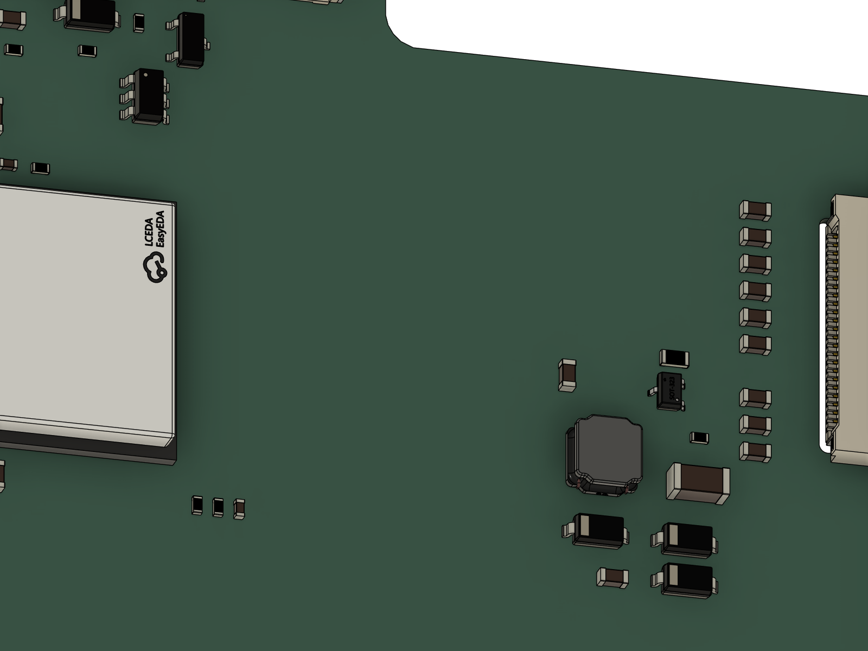
hardware/enclosure/final_assembly/renders/detail/d05_camera_tape.png
