niravkumar2008/AI-CALCULATOR/hardware/enclosure/final_assembly/renders/detail/d07_j1_latch_open.png

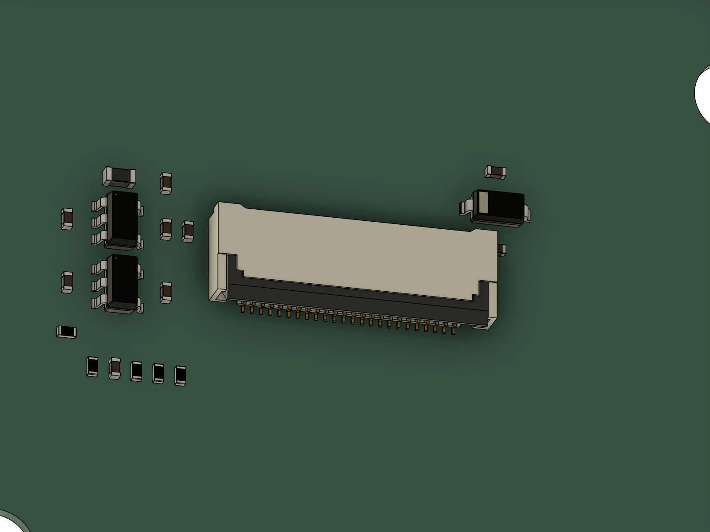
hardware/enclosure/final_assembly/renders/detail/d07_j1_latch_open.png
