niravkumar2008/AI-CALCULATOR/hardware/enclosure/final_assembly/renders/detail/d08_j1_latch_closed.png

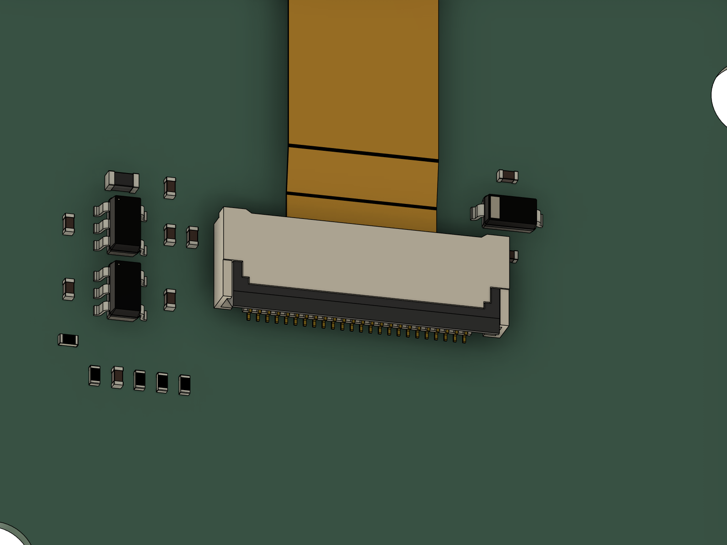
hardware/enclosure/final_assembly/renders/detail/d08_j1_latch_closed.png
