niravkumar2008/AI-CALCULATOR/hardware/enclosure/final_assembly/renders/detail/d09_magnet_j3.png

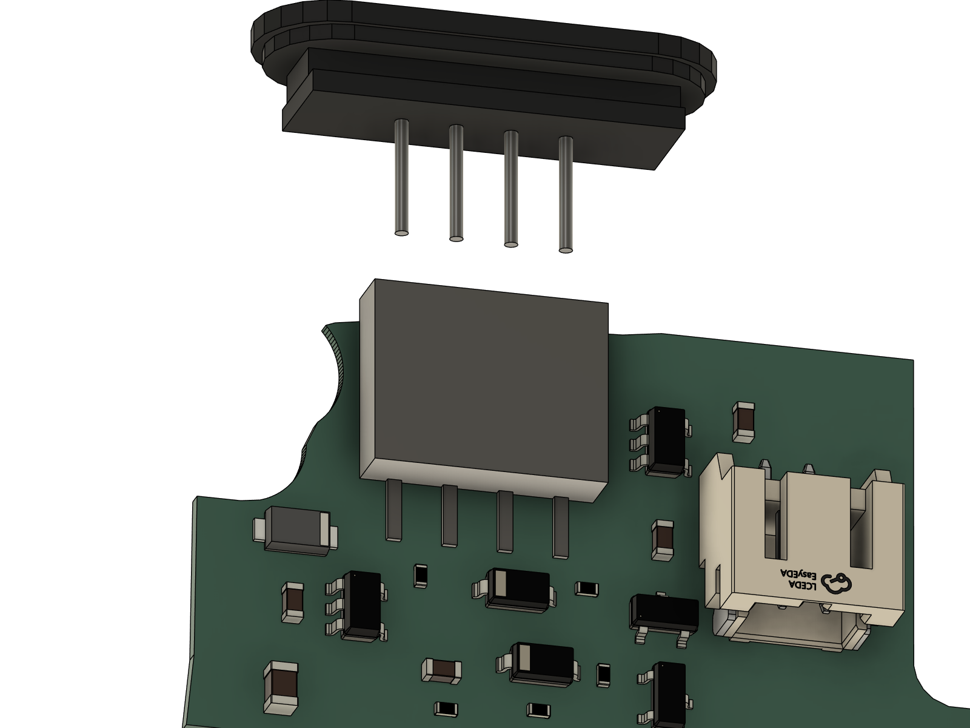
hardware/enclosure/final_assembly/renders/detail/d09_magnet_j3.png
