niravkumar2008/AI-CALCULATOR/hardware/enclosure/final_assembly/renders/detail/d10_battery_tape.png

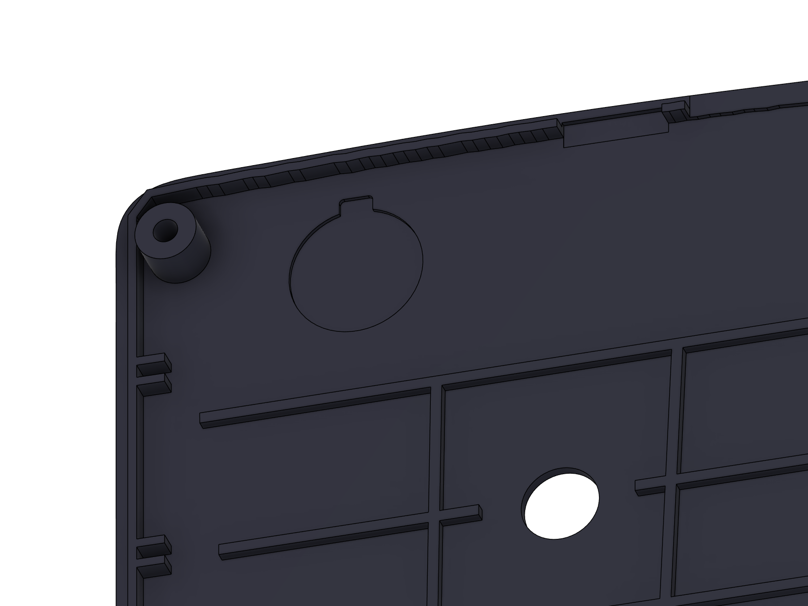
hardware/enclosure/final_assembly/renders/detail/d10_battery_tape.png
