niravkumar2008/AI-CALCULATOR/hardware/enclosure/final_assembly/renders/detail/d11_battery_placed.png

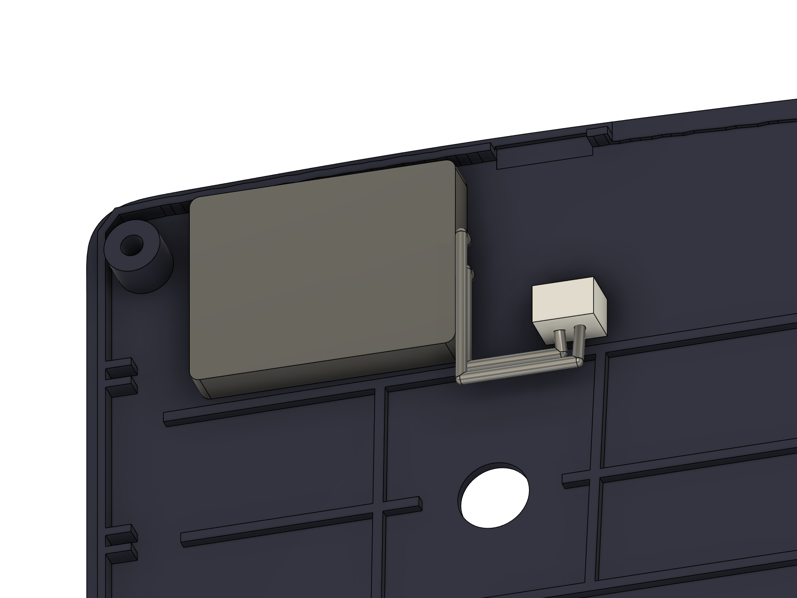
hardware/enclosure/final_assembly/renders/detail/d11_battery_placed.png
