niravkumar2008/AI-CALCULATOR/hardware/enclosure/final_assembly/renders/detail/d12_j4_plug.png

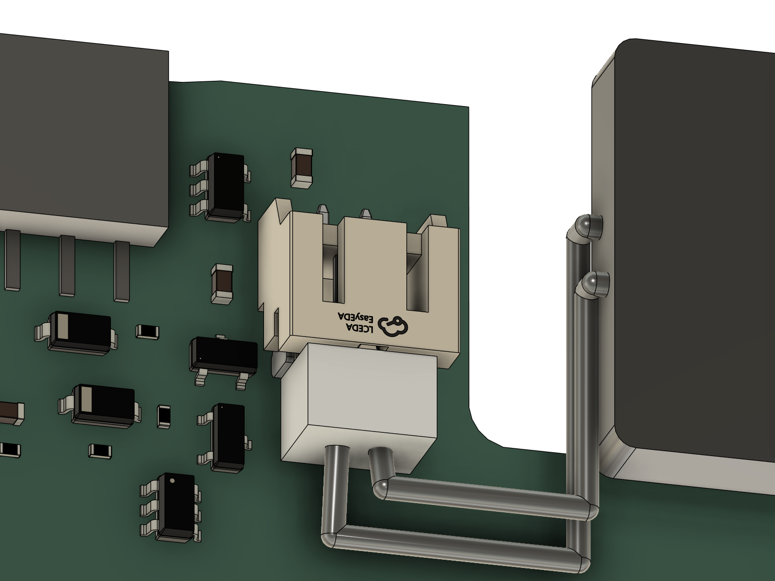
hardware/enclosure/final_assembly/renders/detail/d12_j4_plug.png
