niravkumar2008/AI-CALCULATOR/hardware/enclosure/final_assembly/renders/detail/d14_keymat_seated.png

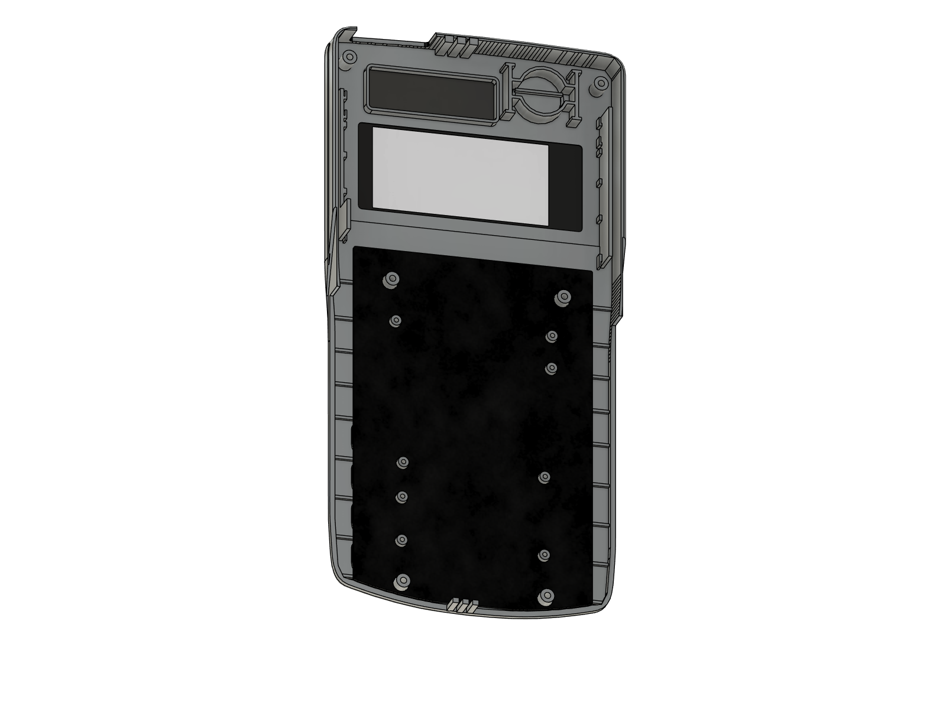
hardware/enclosure/final_assembly/renders/detail/d14_keymat_seated.png
