niravkumar2008/AI-CALCULATOR/hardware/enclosure/final_assembly/renders/detail/d17_cover_close_2.png

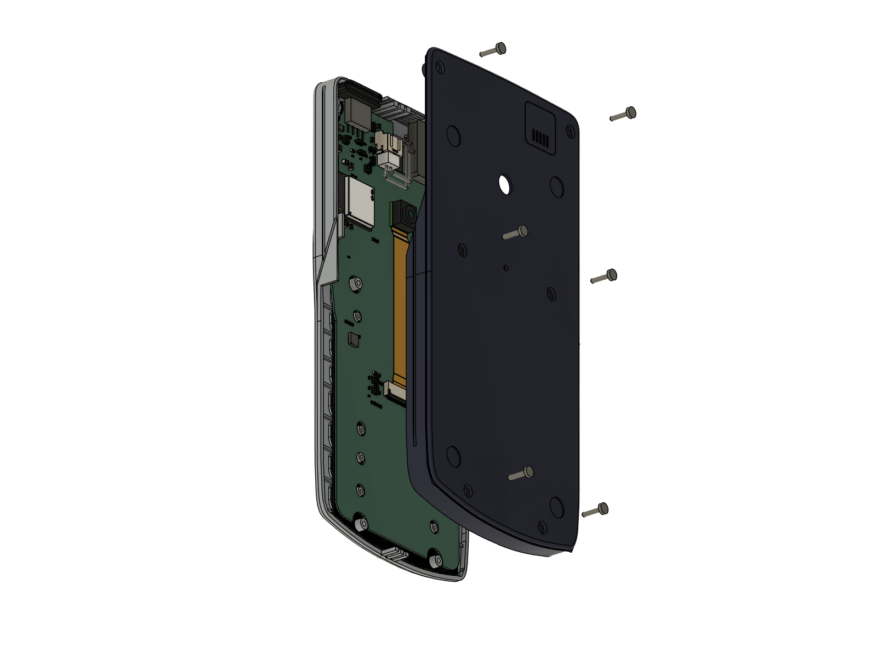
hardware/enclosure/final_assembly/renders/detail/d17_cover_close_2.png
