niravkumar2008/AI-CALCULATOR/hardware/enclosure/final_assembly/renders/detail/d19_cover_close_4.png

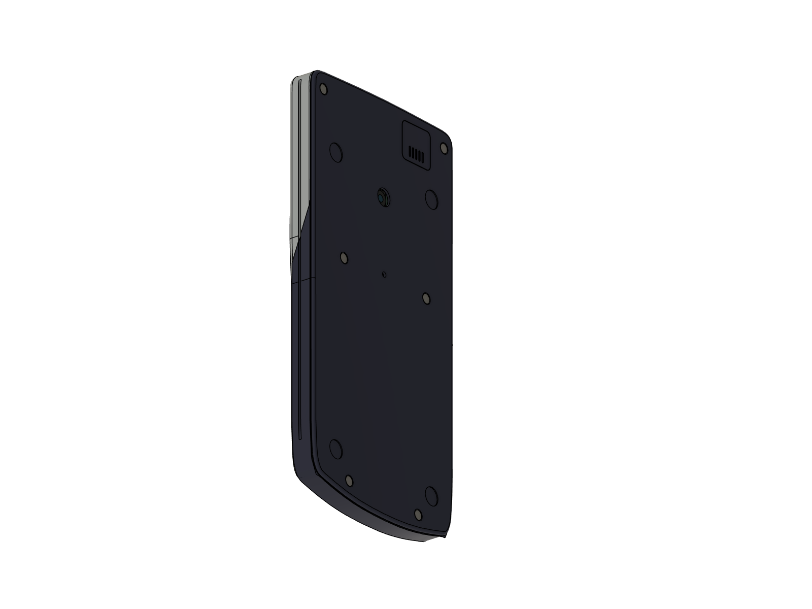
hardware/enclosure/final_assembly/renders/detail/d19_cover_close_4.png
