niravkumar2008/AI-CALCULATOR/hardware/enclosure/final_assembly/renders/exploded_shells_only.png

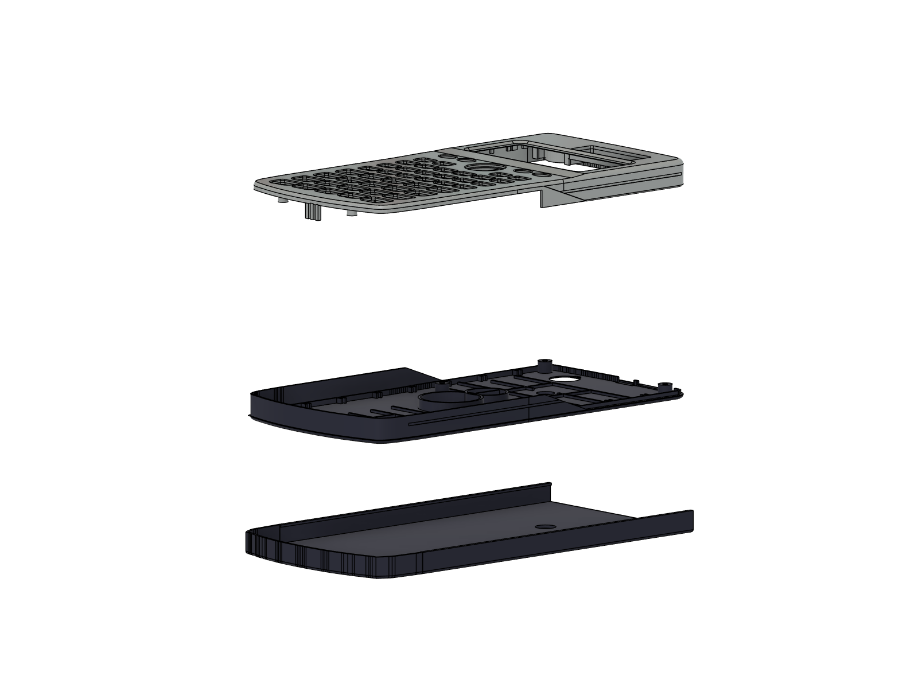
hardware/enclosure/final_assembly/renders/exploded_shells_only.png
