niravkumar2008/AI-CALCULATOR/hardware/enclosure/final_assembly/renders/front.png

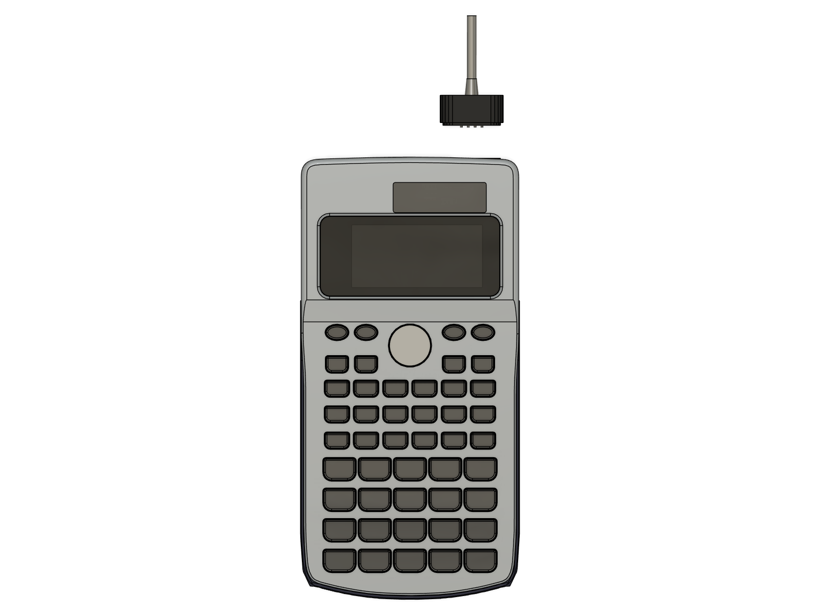
hardware/enclosure/final_assembly/renders/front.png
