niravkumar2008/AI-CALCULATOR/hardware/enclosure/final_assembly/renders/grind/magnet_notch_dims.png

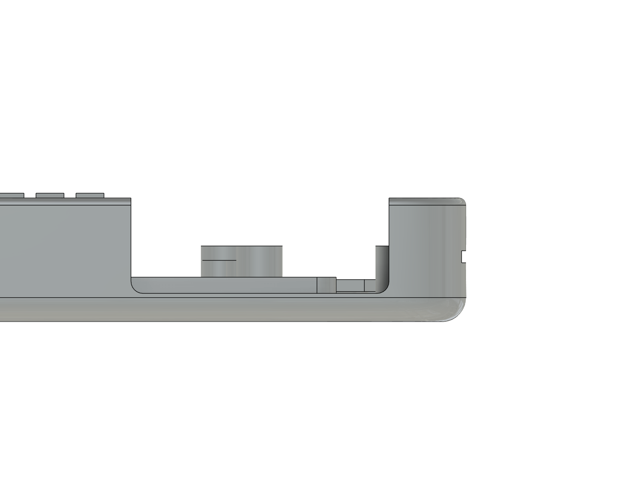
hardware/enclosure/final_assembly/renders/grind/magnet_notch_dims.png
