niravkumar2008/AI-CALCULATOR/hardware/enclosure/final_assembly/renders/grind/z1_solar_box_after.png

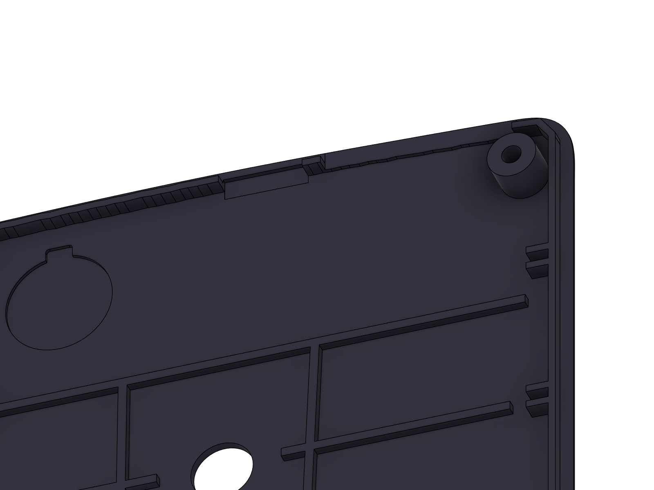
hardware/enclosure/final_assembly/renders/grind/z1_solar_box_after.png
