niravkumar2008/AI-CALCULATOR/hardware/enclosure/final_assembly/renders/grind/z2_rib_b_after.png

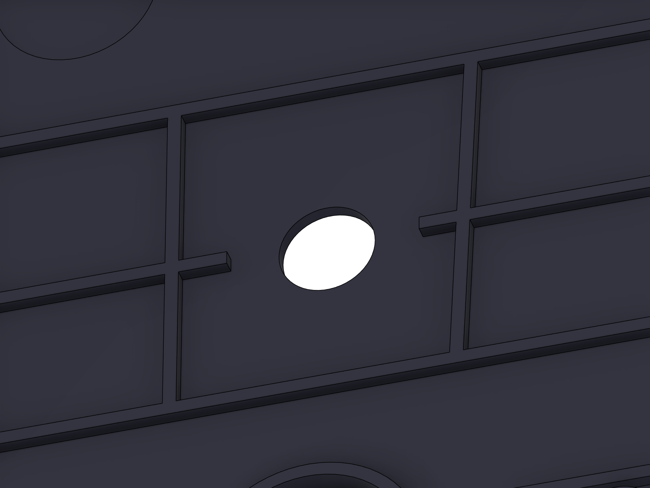
hardware/enclosure/final_assembly/renders/grind/z2_rib_b_after.png
