niravkumar2008/AI-CALCULATOR/hardware/enclosure/final_assembly/renders/grind/z3_camera_window_outside_after.png

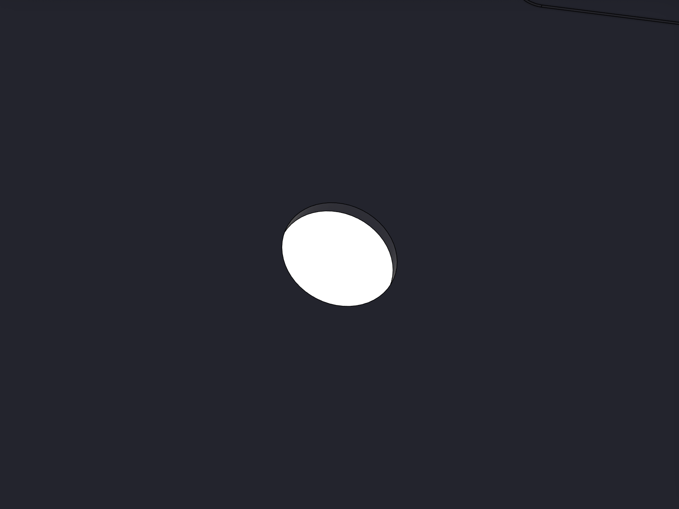
hardware/enclosure/final_assembly/renders/grind/z3_camera_window_outside_after.png
