niravkumar2008/AI-CALCULATOR/hardware/enclosure/final_assembly/renders/grind/z5_magnet_notch_before.png

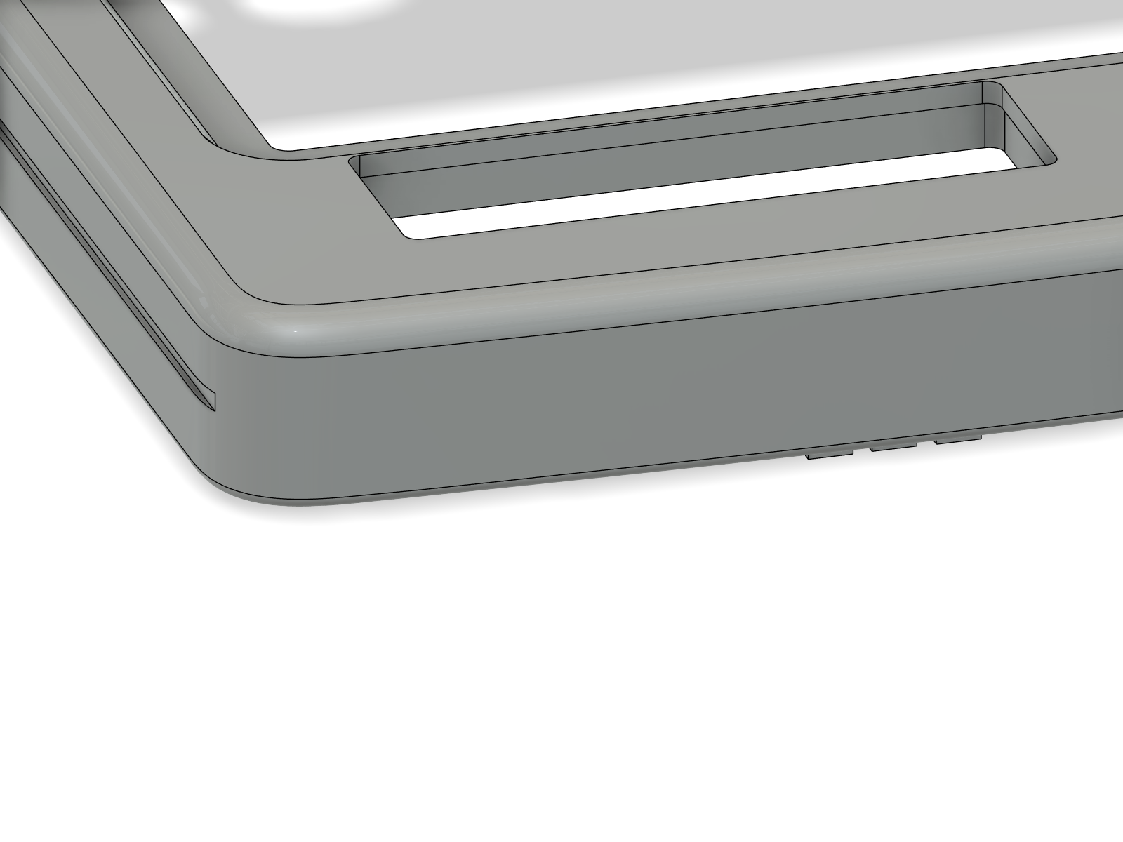
hardware/enclosure/final_assembly/renders/grind/z5_magnet_notch_before.png
