niravkumar2008/AI-CALCULATOR/hardware/enclosure/final_assembly/renders/grind/z5b_lip_after.png

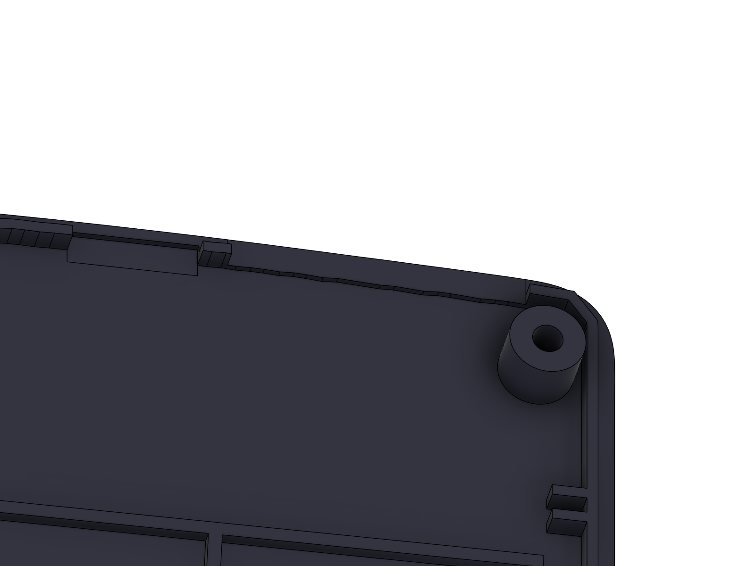
hardware/enclosure/final_assembly/renders/grind/z5b_lip_after.png
