niravkumar2008/AI-CALCULATOR/hardware/enclosure/final_assembly/renders/grind/z6_antenna_relief_before.png

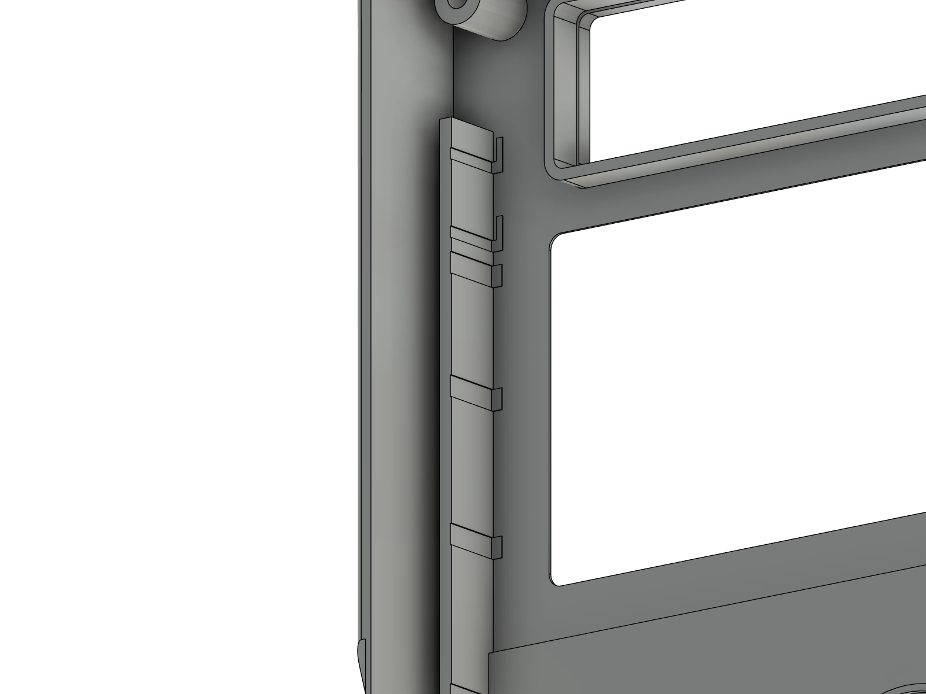
hardware/enclosure/final_assembly/renders/grind/z6_antenna_relief_before.png
