niravkumar2008/AI-CALCULATOR/hardware/enclosure/final_assembly/renders/grind/z6b_pins_hooks_after.png

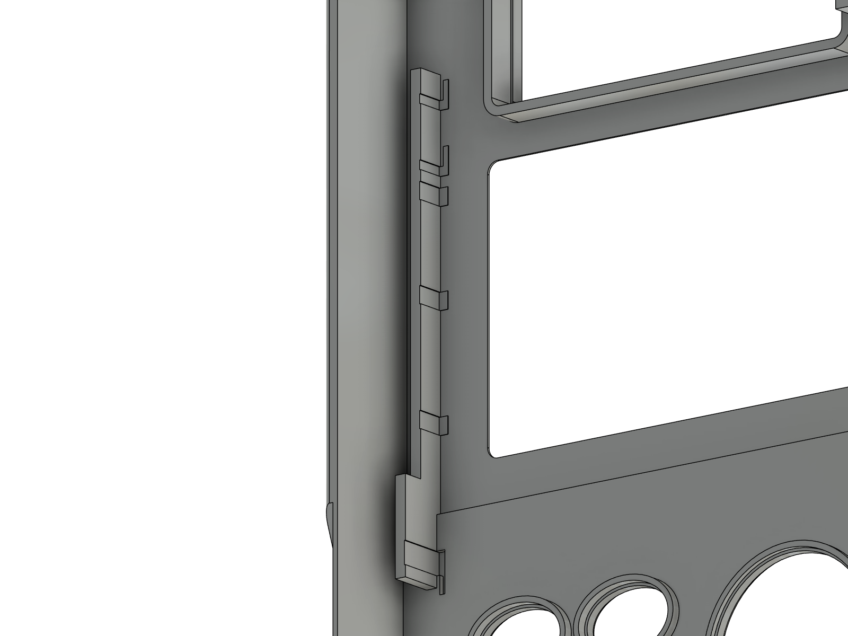
hardware/enclosure/final_assembly/renders/grind/z6b_pins_hooks_after.png
