niravkumar2008/AI-CALCULATOR/hardware/enclosure/final_assembly/renders/photos/front.jpg

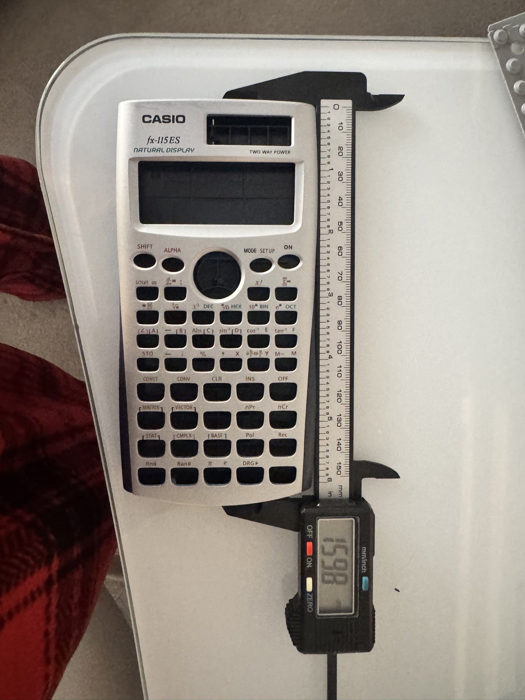
hardware/enclosure/final_assembly/renders/photos/front.jpg
