niravkumar2008/AI-CALCULATOR/hardware/enclosure/final_assembly/renders/section_antenna_wide.png

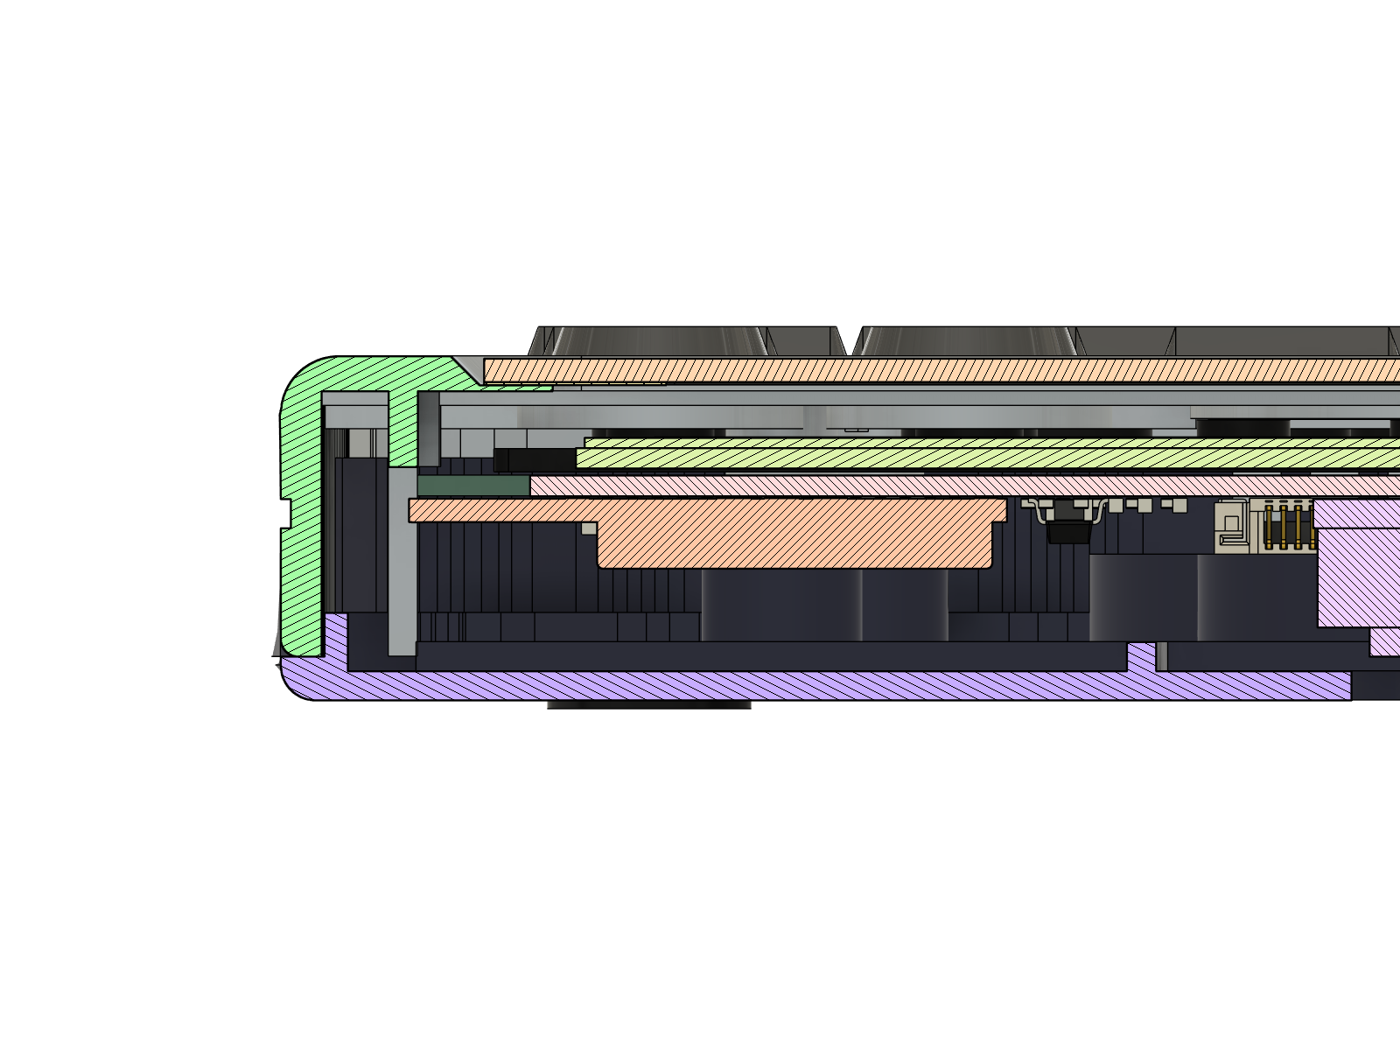
hardware/enclosure/final_assembly/renders/section_antenna_wide.png
