niravkumar2008/AI-CALCULATOR/hardware/enclosure/final_assembly/renders/section_battery_lengthwise.png

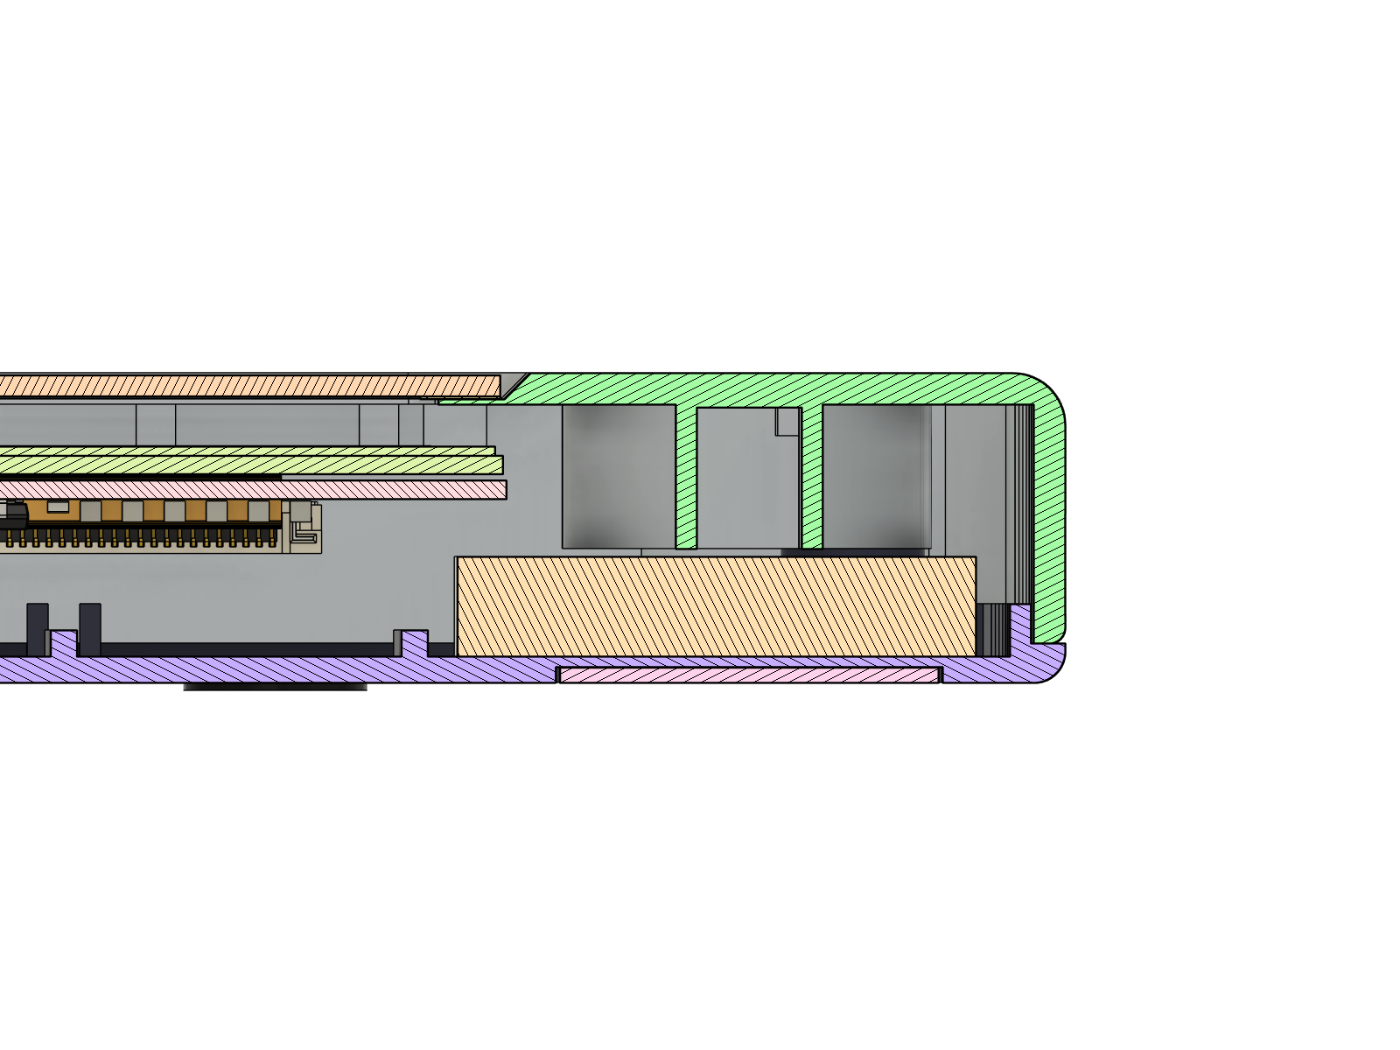
hardware/enclosure/final_assembly/renders/section_battery_lengthwise.png
