niravkumar2008/AI-CALCULATOR/hardware/enclosure/final_assembly/renders/section_camera_wide.png

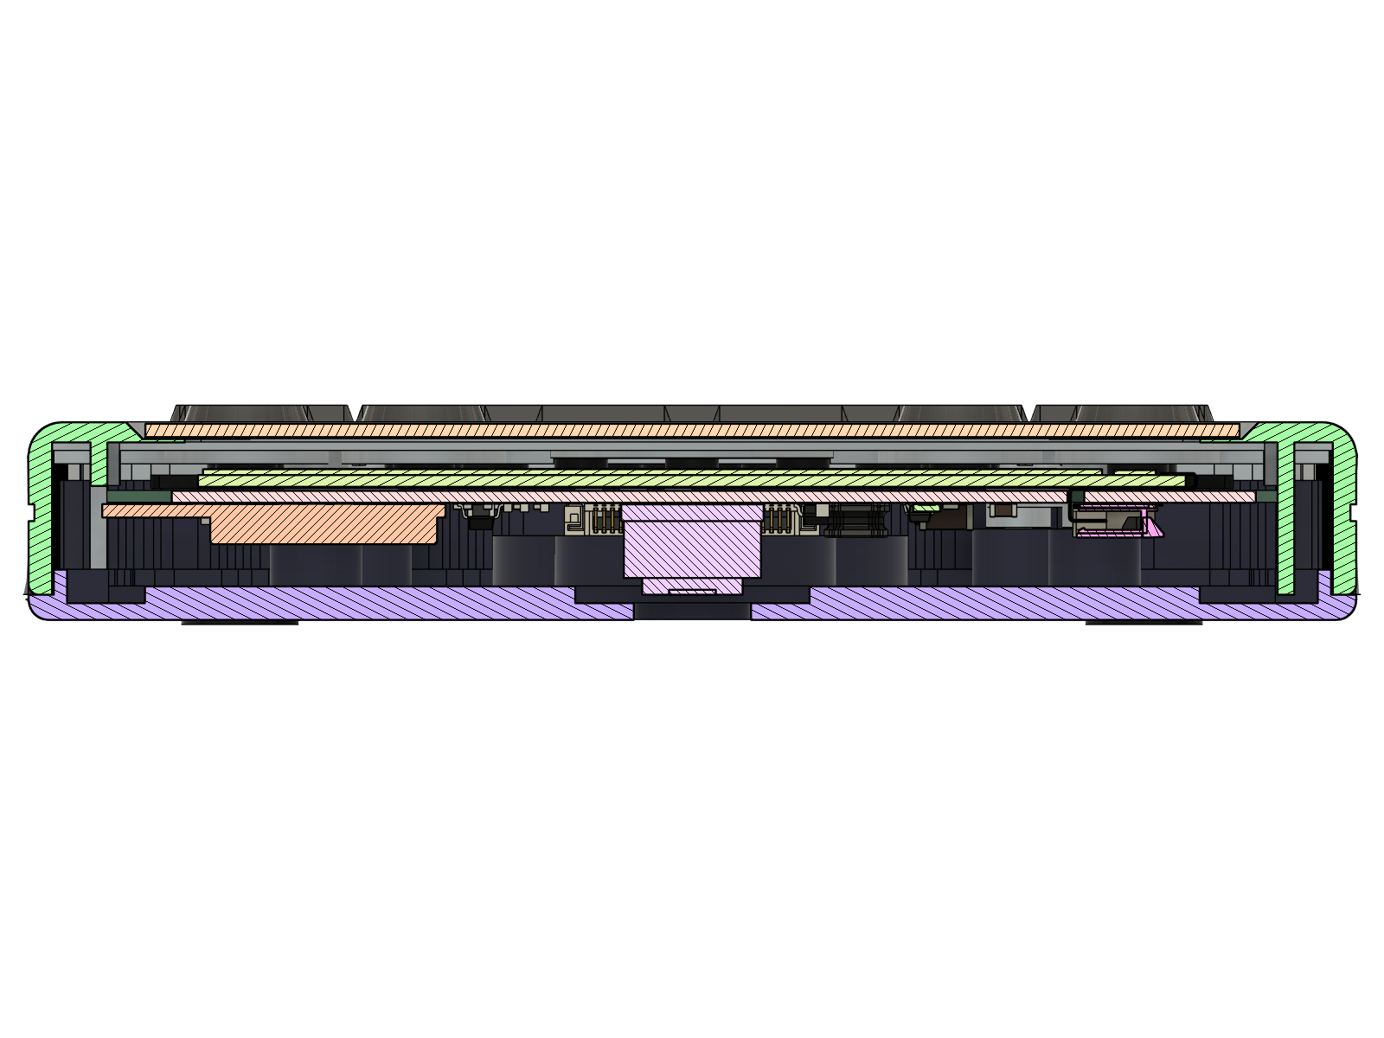
hardware/enclosure/final_assembly/renders/section_camera_wide.png
