niravkumar2008/AI-CALCULATOR/hardware/enclosure/final_assembly_v15_lcd/renders/compare_v14_v15_fpc_end_section.png

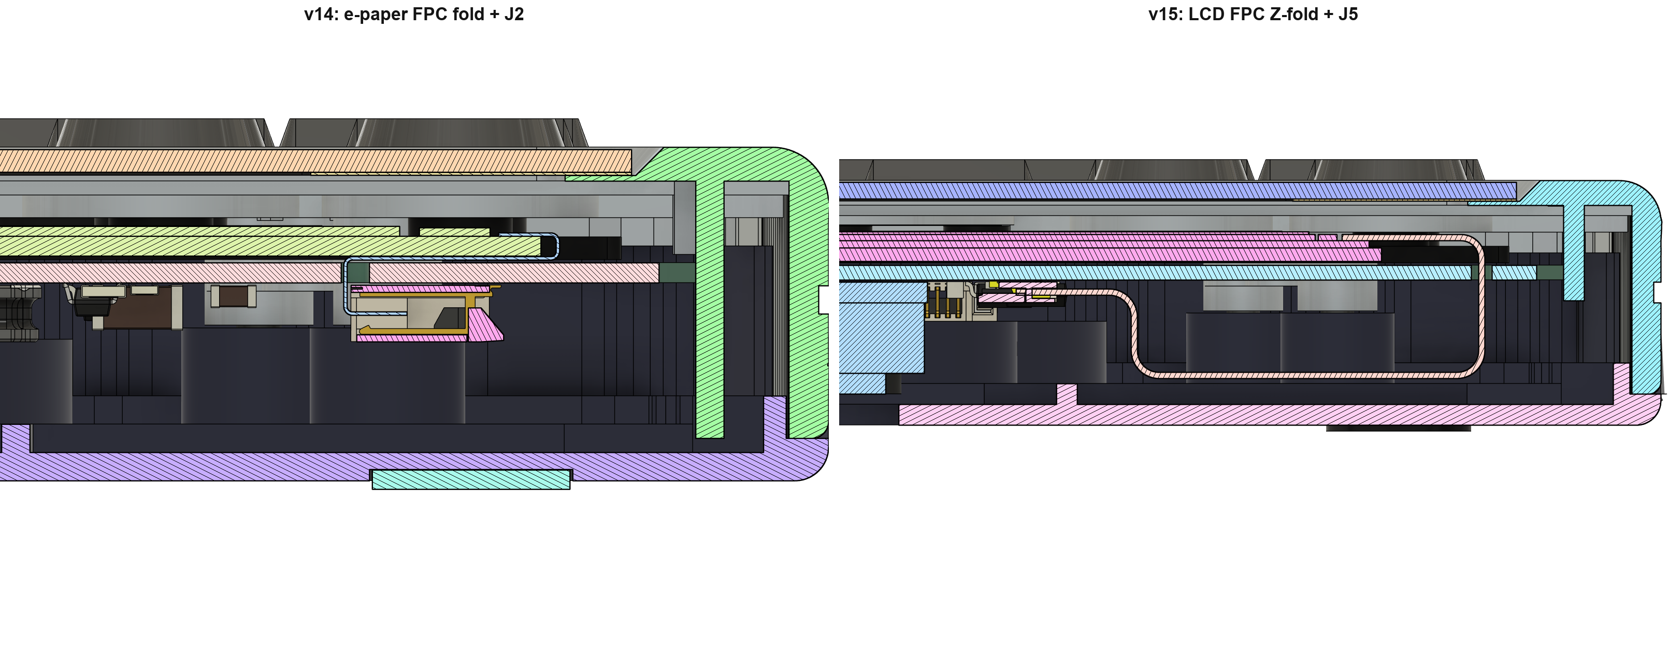
hardware/enclosure/final_assembly_v15_lcd/renders/compare_v14_v15_fpc_end_section.png
