niravkumar2008/AI-CALCULATOR/hardware/enclosure/final_assembly_v15_lcd/renders/detail/e03_tail_section_side.png

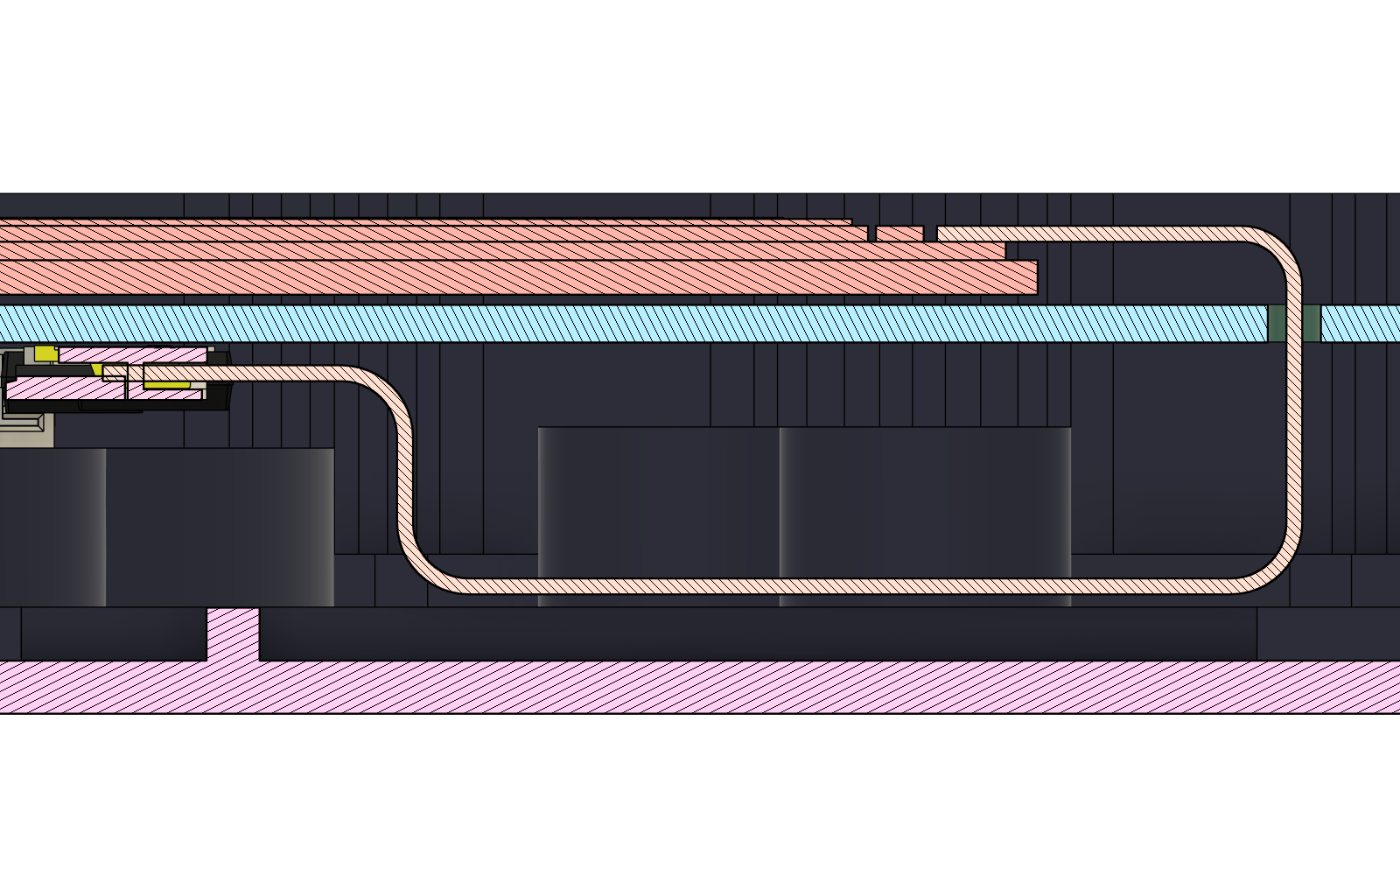
hardware/enclosure/final_assembly_v15_lcd/renders/detail/e03_tail_section_side.png
