niravkumar2008/AI-CALCULATOR/hardware/enclosure/final_assembly_v15_lcd/renders/detail/e04_tail_3d.png

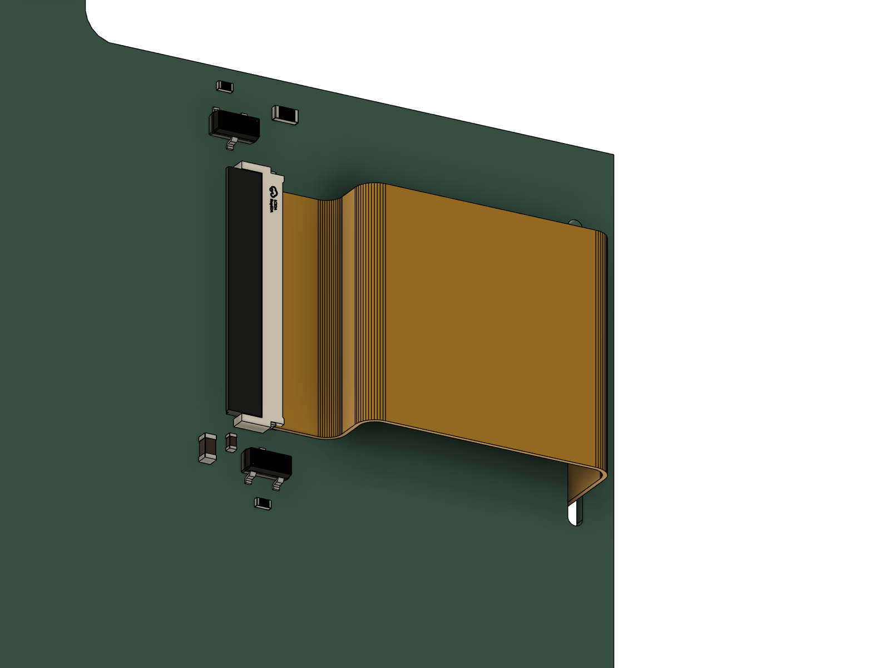
hardware/enclosure/final_assembly_v15_lcd/renders/detail/e04_tail_3d.png
