niravkumar2008/AI-CALCULATOR/hardware/enclosure/final_assembly_v15_lcd/renders/detail/e06_j5_latch_open.png

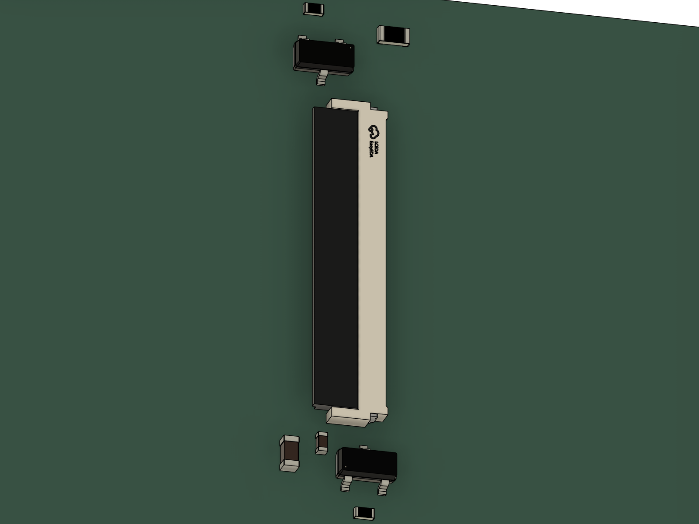
hardware/enclosure/final_assembly_v15_lcd/renders/detail/e06_j5_latch_open.png
