niravkumar2008/AI-CALCULATOR/hardware/enclosure/final_assembly_v15_lcd/renders/detail/e07_j5_latch_closed.png

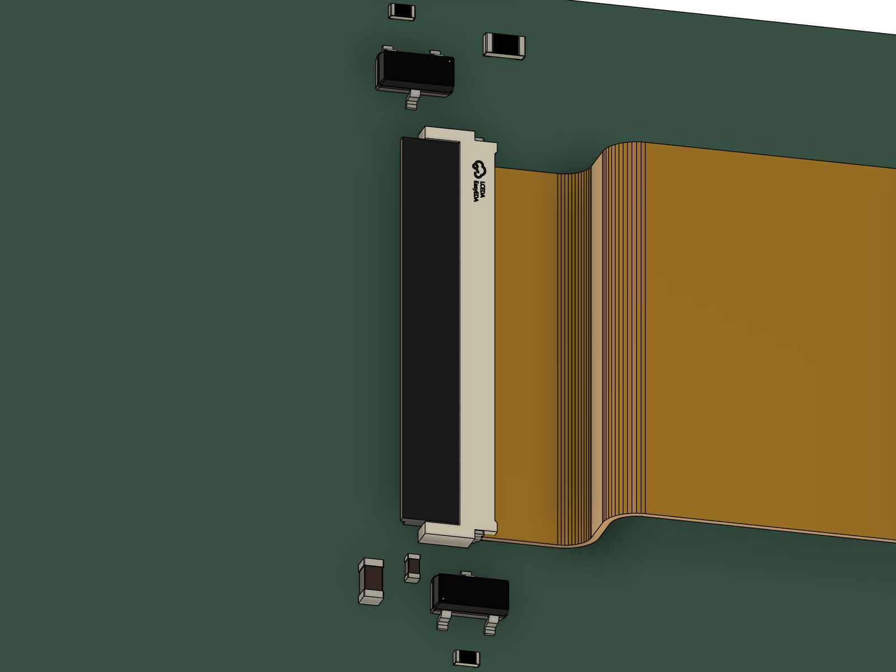
hardware/enclosure/final_assembly_v15_lcd/renders/detail/e07_j5_latch_closed.png
