niravkumar2008/AI-CALCULATOR/hardware/enclosure/final_assembly_v15_lcd/renders/detail/f02_dcxyx_sfold_closeup.png

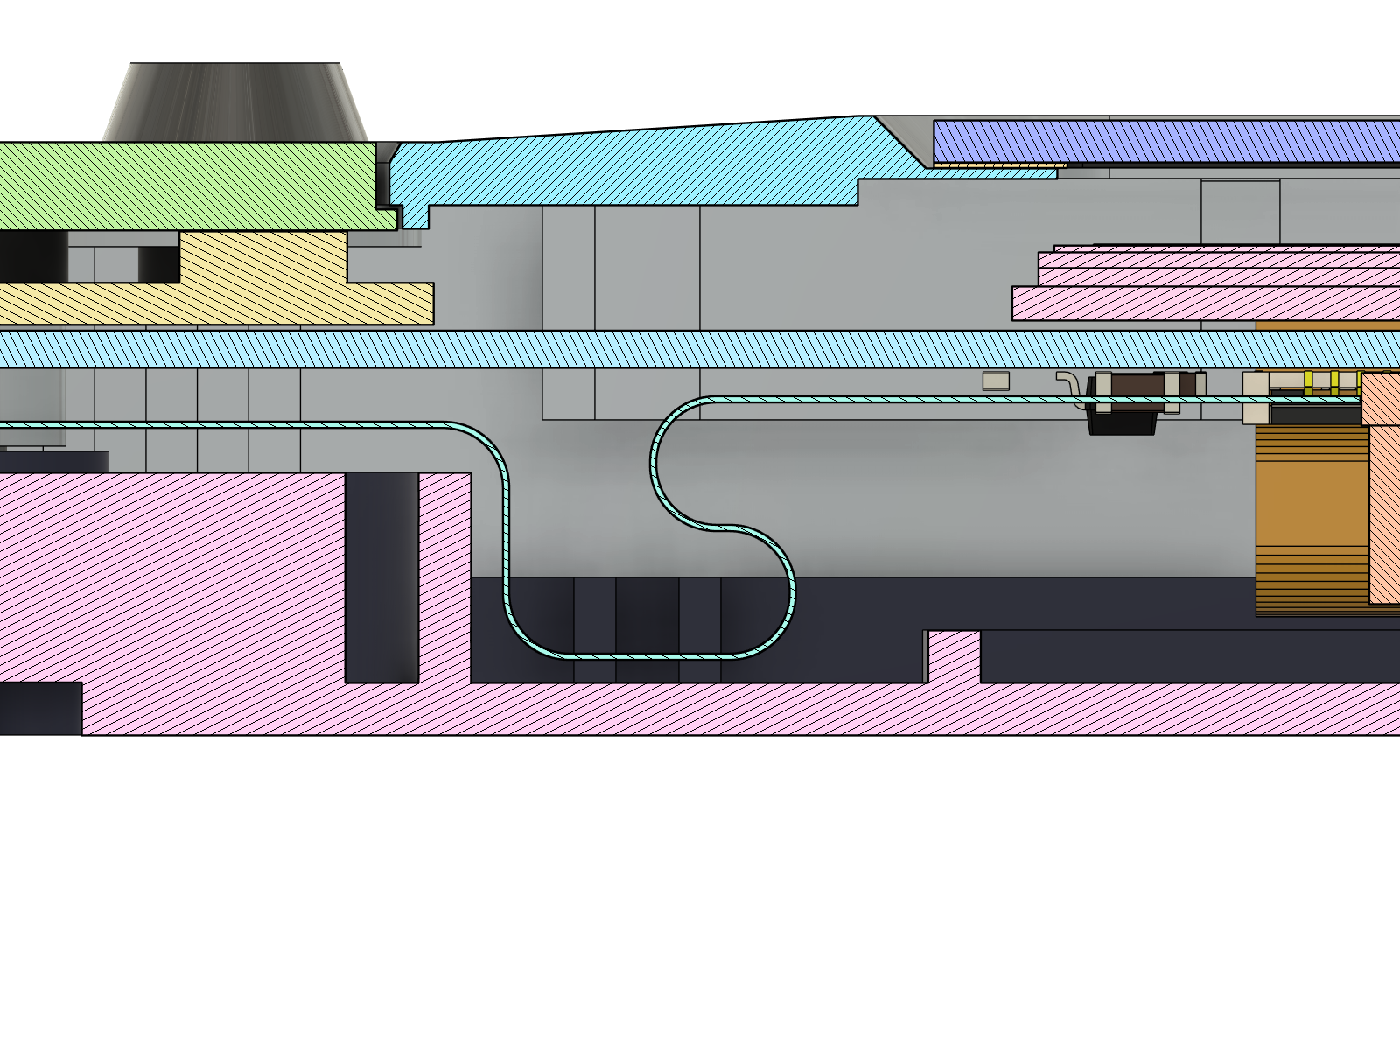
hardware/enclosure/final_assembly_v15_lcd/renders/detail/f02_dcxyx_sfold_closeup.png
