niravkumar2008/AI-CALCULATOR/hardware/enclosure/final_assembly_v15_lcd/renders/lcd_fpc_slot_closeup.png

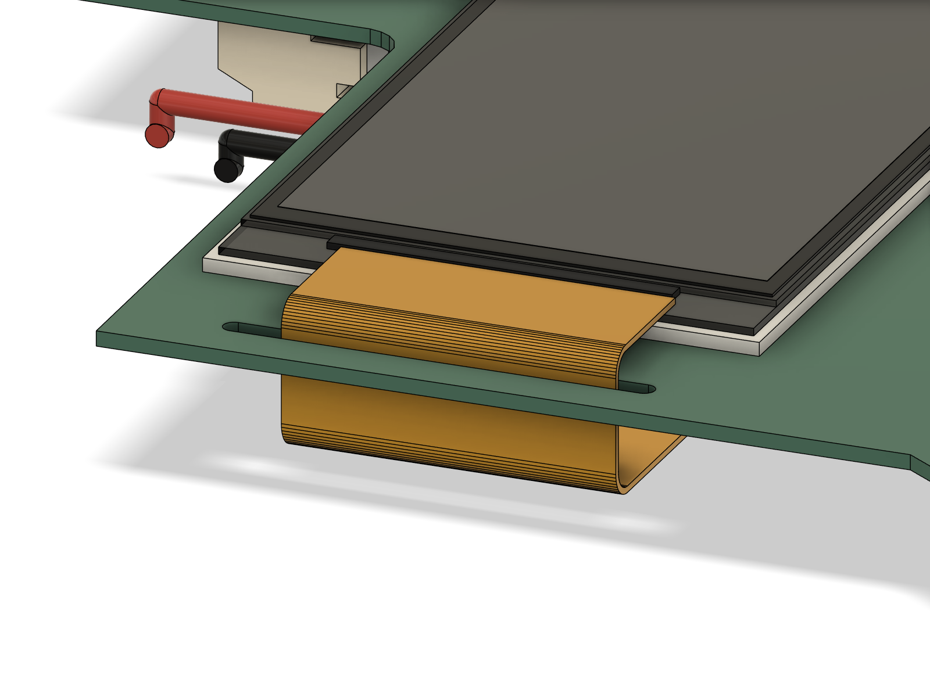
hardware/enclosure/final_assembly_v15_lcd/renders/lcd_fpc_slot_closeup.png
