niravkumar2008/AI-CALCULATOR/hardware/enclosure/final_assembly_v15_lcd/renders/section_lcd_across_solar.png

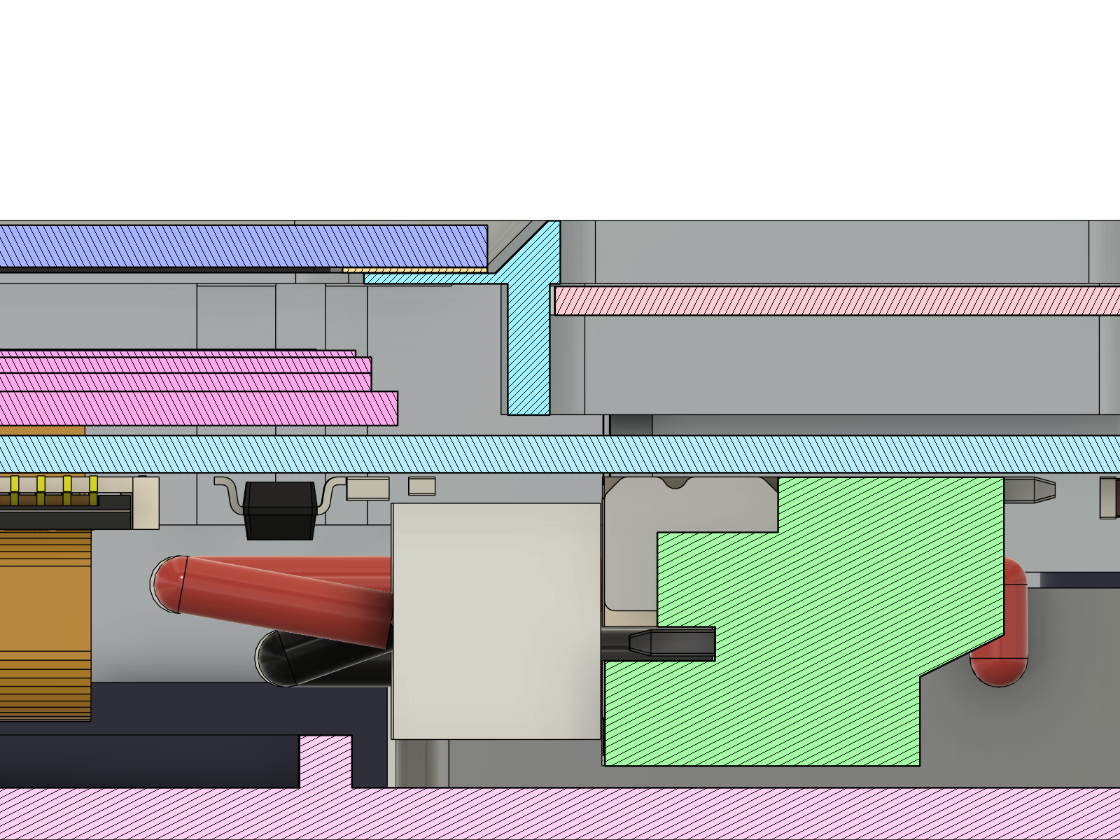
hardware/enclosure/final_assembly_v15_lcd/renders/section_lcd_across_solar.png
