niravkumar2008/AI-CALCULATOR/hardware/enclosure/final_assembly_v15_lcd/renders/section_lcd_lengthwise.png

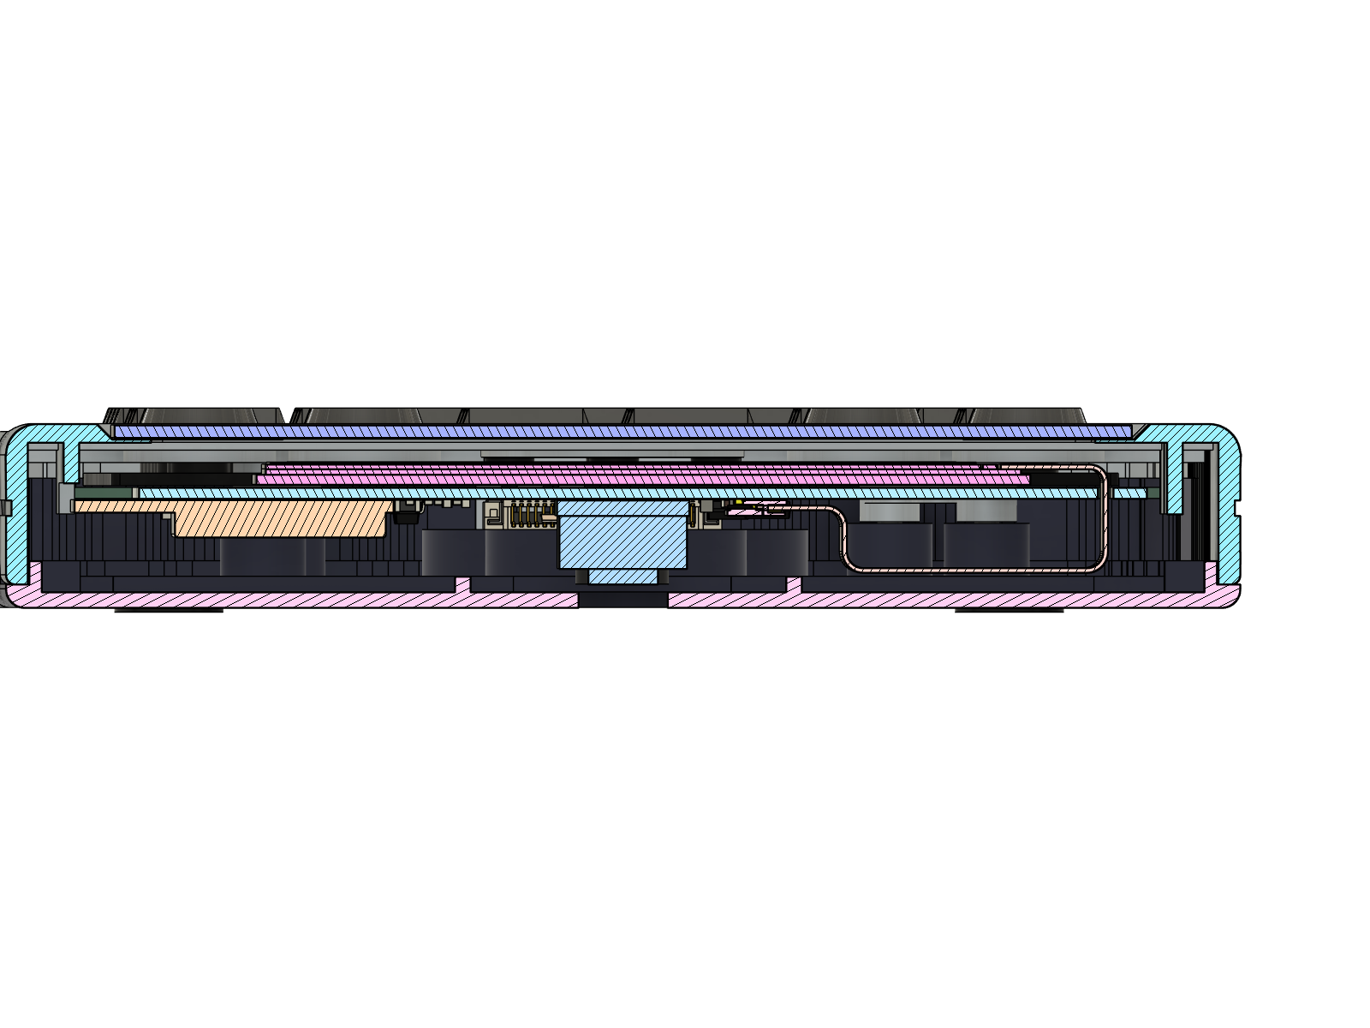
hardware/enclosure/final_assembly_v15_lcd/renders/section_lcd_lengthwise.png
