niravkumar2008/AI-CALCULATOR/hardware/enclosure/final_assembly_v15_lcd/renders/steps/s01_open_shell.png

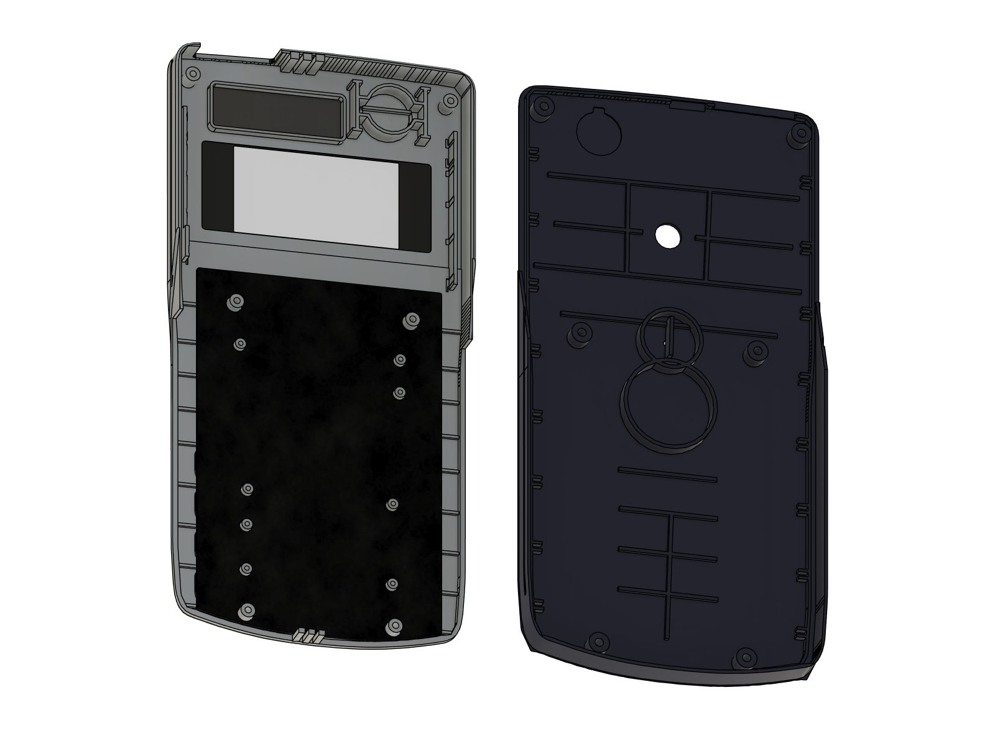
hardware/enclosure/final_assembly_v15_lcd/renders/steps/s01_open_shell.png
