niravkumar2008/AI-CALCULATOR/hardware/enclosure/final_assembly_v15_lcd/renders/steps/s05a_lcd_tail_ann.png

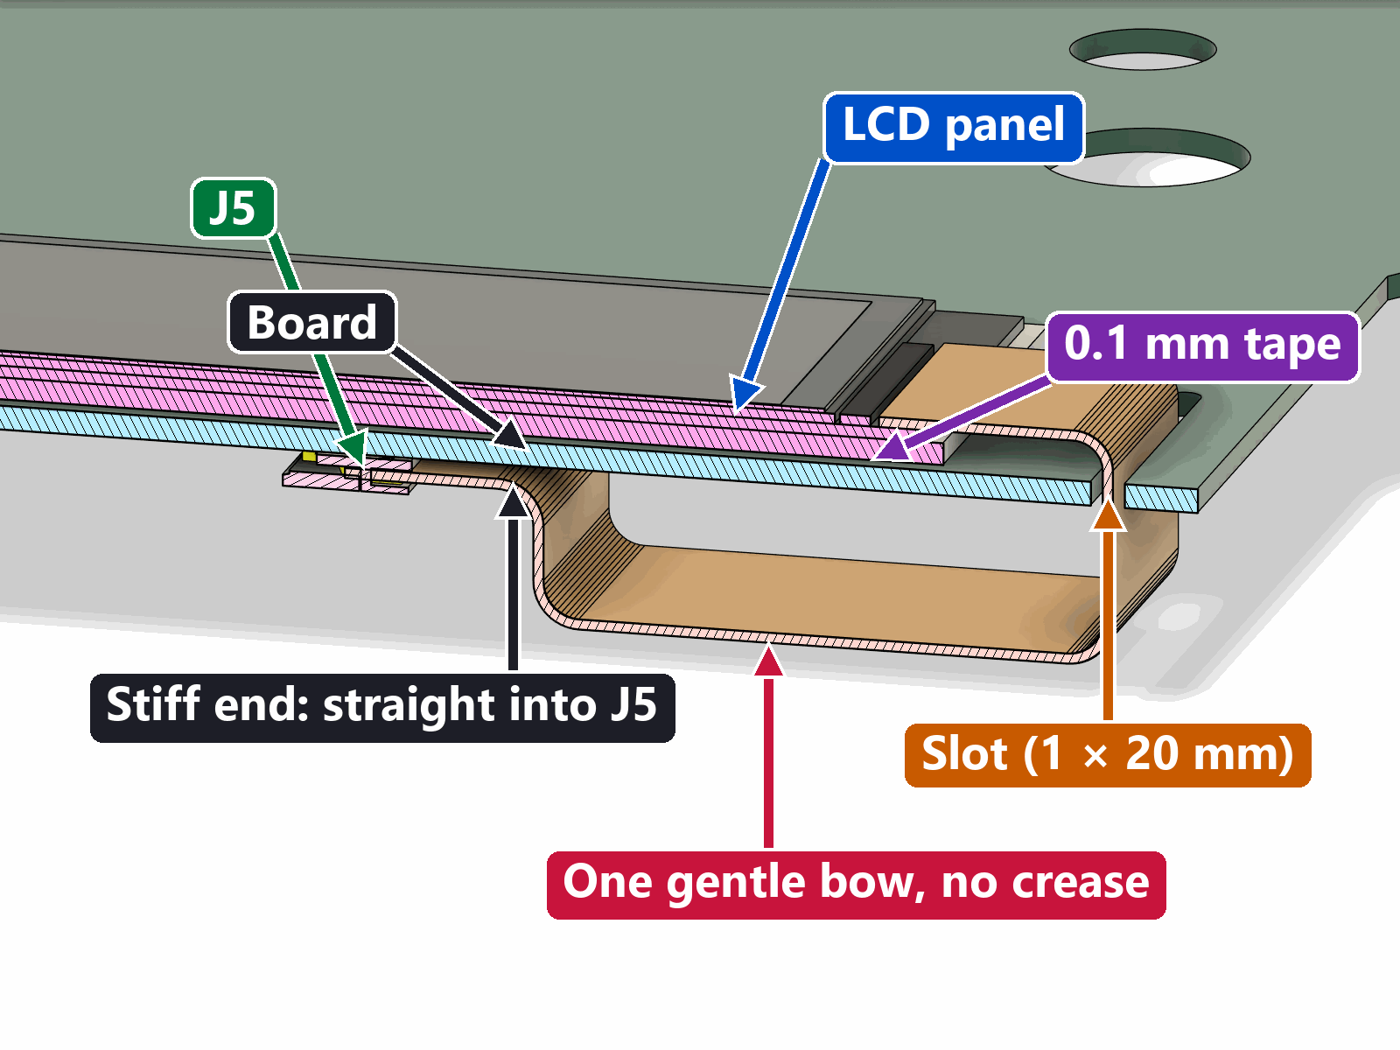
hardware/enclosure/final_assembly_v15_lcd/renders/steps/s05a_lcd_tail_ann.png
