niravkumar2008/AI-CALCULATOR/hardware/enclosure/final_assembly_v15_lcd/renders/steps/s05b_lcd_j5_ann.png

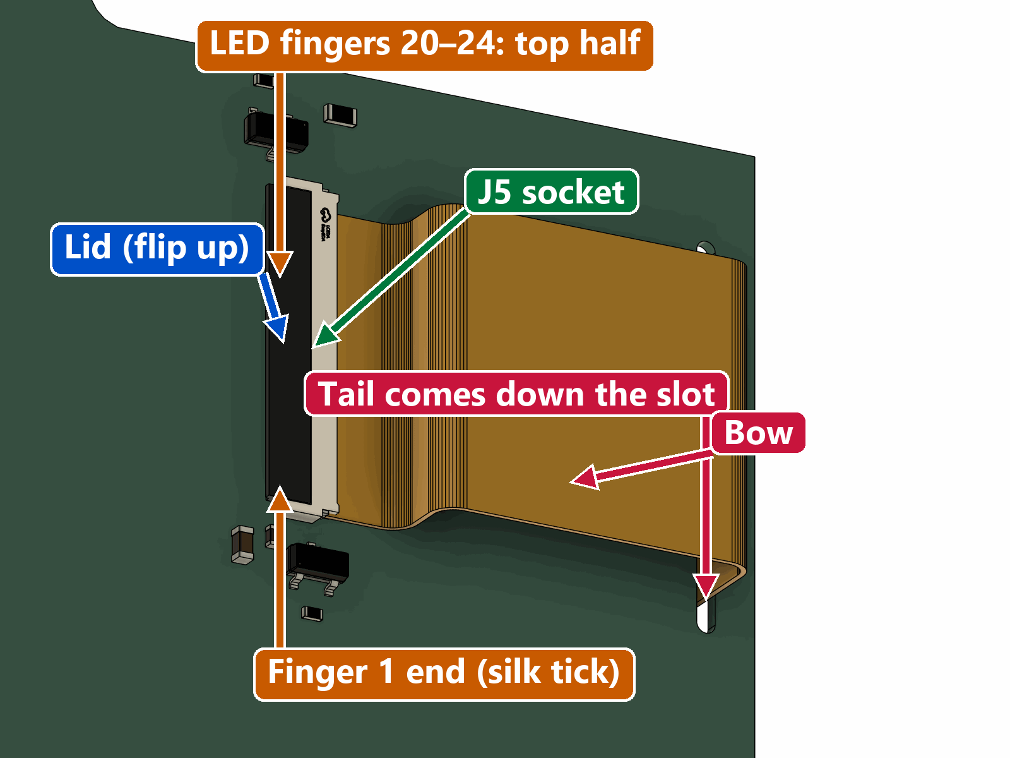
hardware/enclosure/final_assembly_v15_lcd/renders/steps/s05b_lcd_j5_ann.png
