niravkumar2008/AI-CALCULATOR/hardware/enclosure/final_assembly_v15_lcd/renders/steps/s06b_camera_j1.png

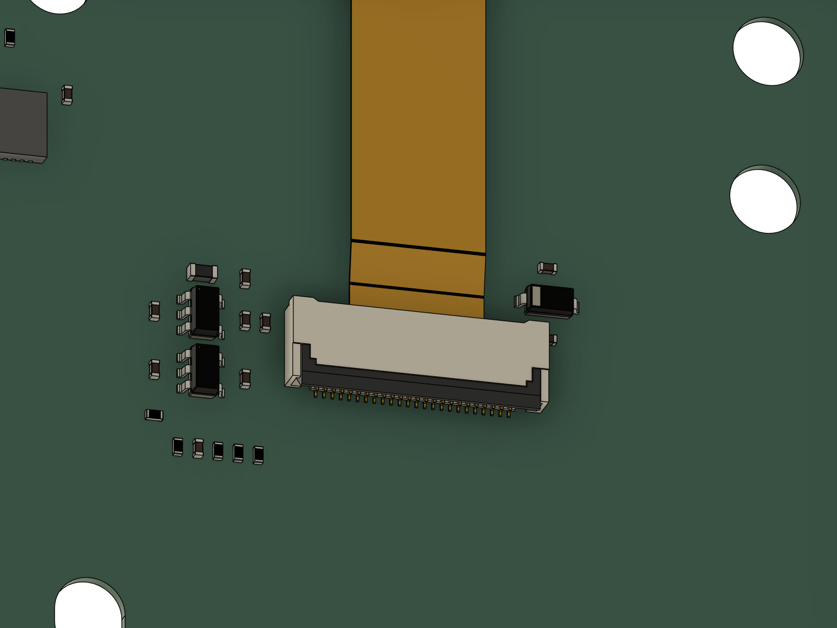
hardware/enclosure/final_assembly_v15_lcd/renders/steps/s06b_camera_j1.png
