niravkumar2008/AI-CALCULATOR/hardware/enclosure/final_assembly_v15_lcd/renders/steps/s07_magnet_j3.png

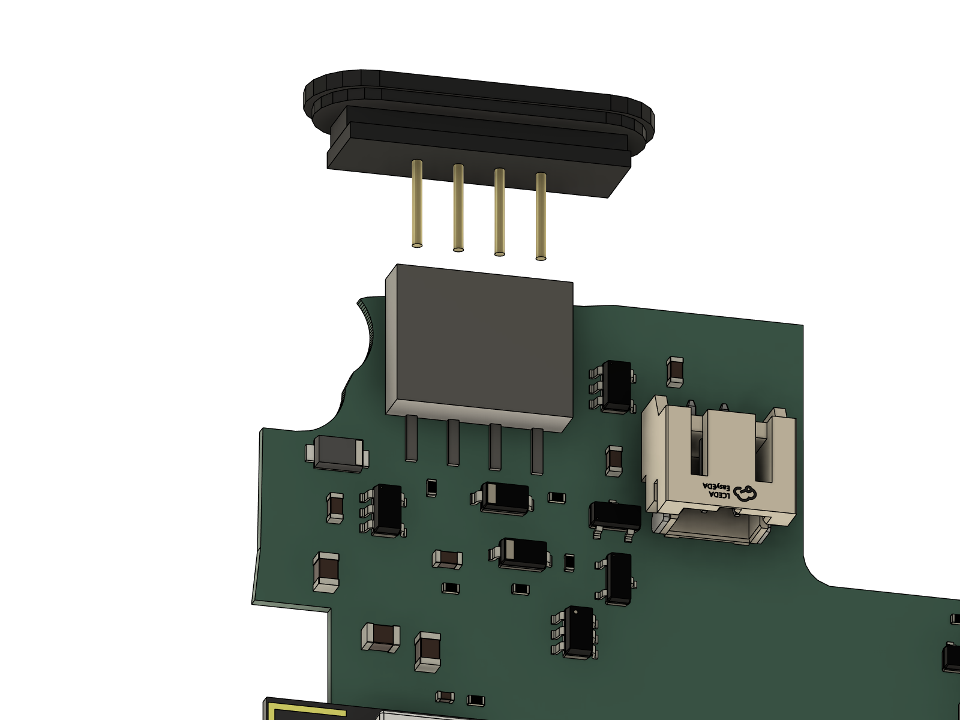
hardware/enclosure/final_assembly_v15_lcd/renders/steps/s07_magnet_j3.png
