niravkumar2008/AI-CALCULATOR/hardware/enclosure/final_assembly_v15_lcd/renders/steps/s08a_keymat.png

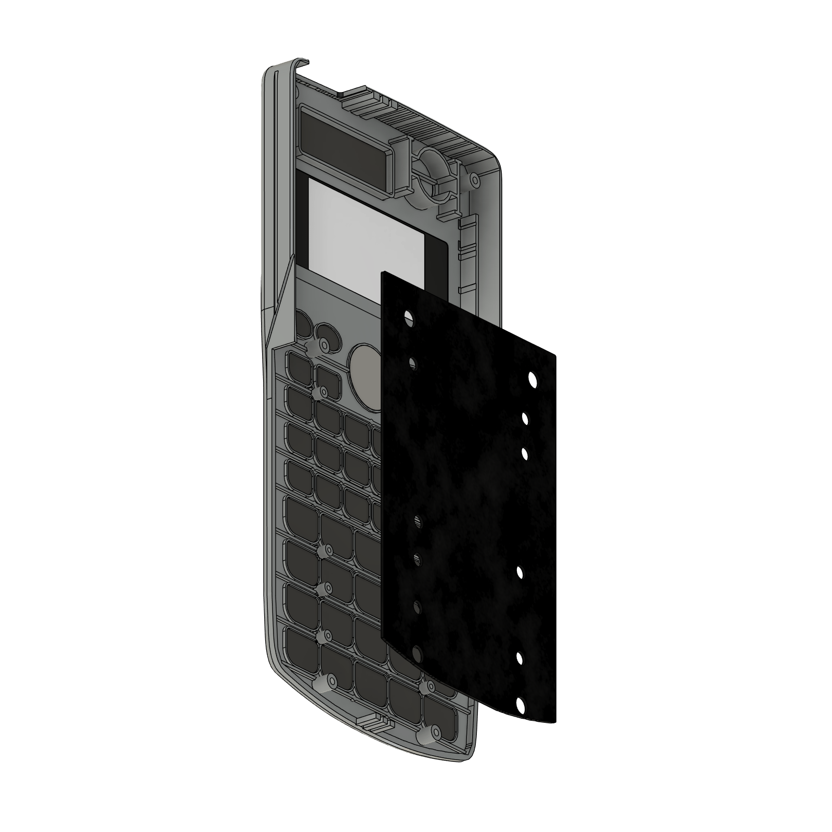
hardware/enclosure/final_assembly_v15_lcd/renders/steps/s08a_keymat.png
