niravkumar2008/AI-CALCULATOR/hardware/enclosure/final_assembly_v15_lcd/renders/steps/s08b_board_in.png

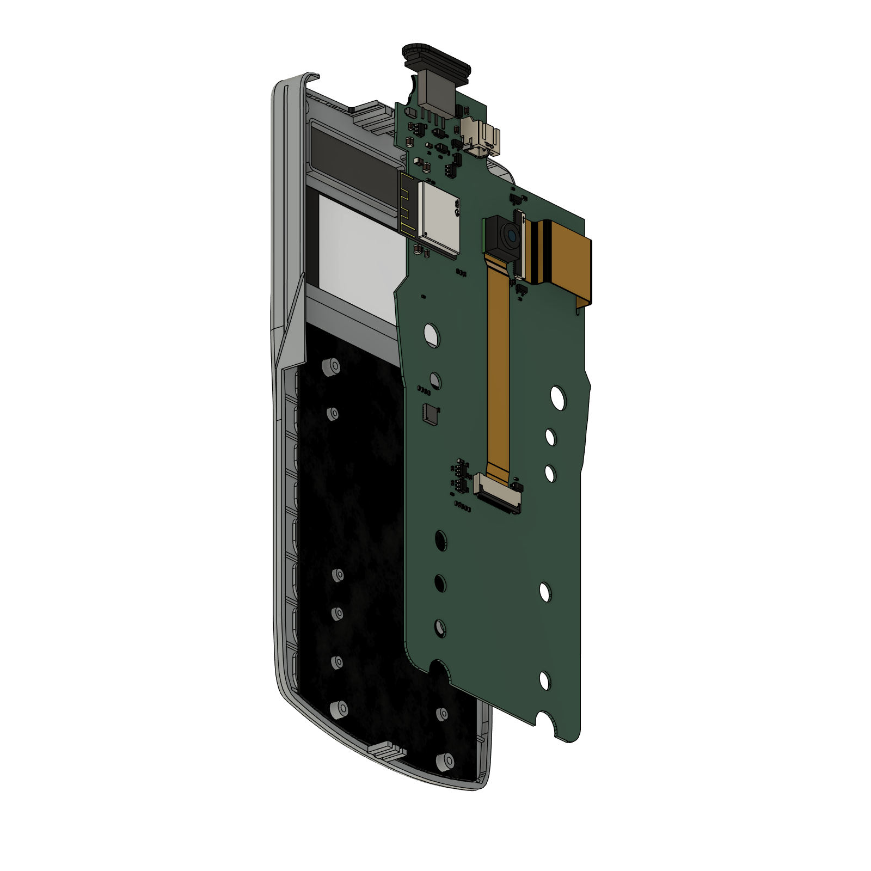
hardware/enclosure/final_assembly_v15_lcd/renders/steps/s08b_board_in.png
