niravkumar2008/AI-CALCULATOR/hardware/enclosure/final_assembly_v15_lcd/renders/steps/s10b_closed_back.png

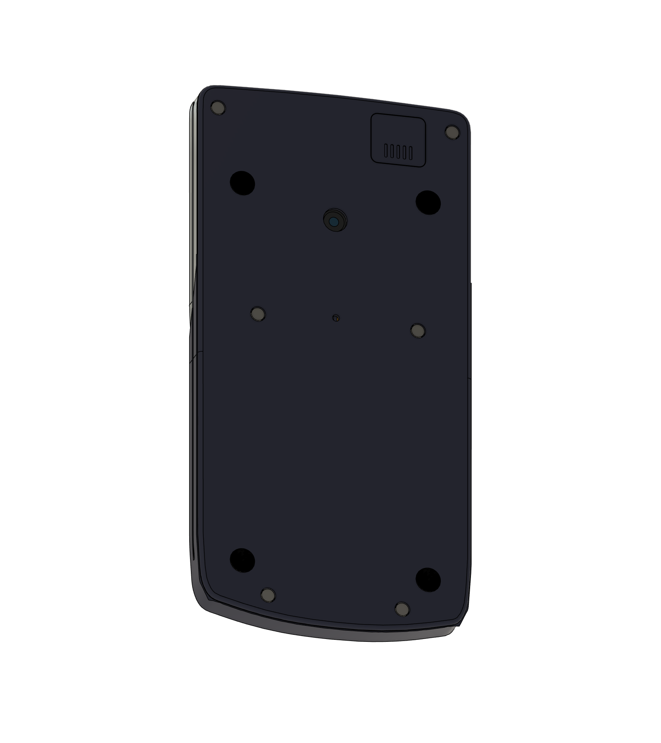
hardware/enclosure/final_assembly_v15_lcd/renders/steps/s10b_closed_back.png
