niravkumar2008/AI-CALCULATOR/hardware/enclosure/final_assembly_v15_lcd/renders/steps/s11_finished_front_ann.png

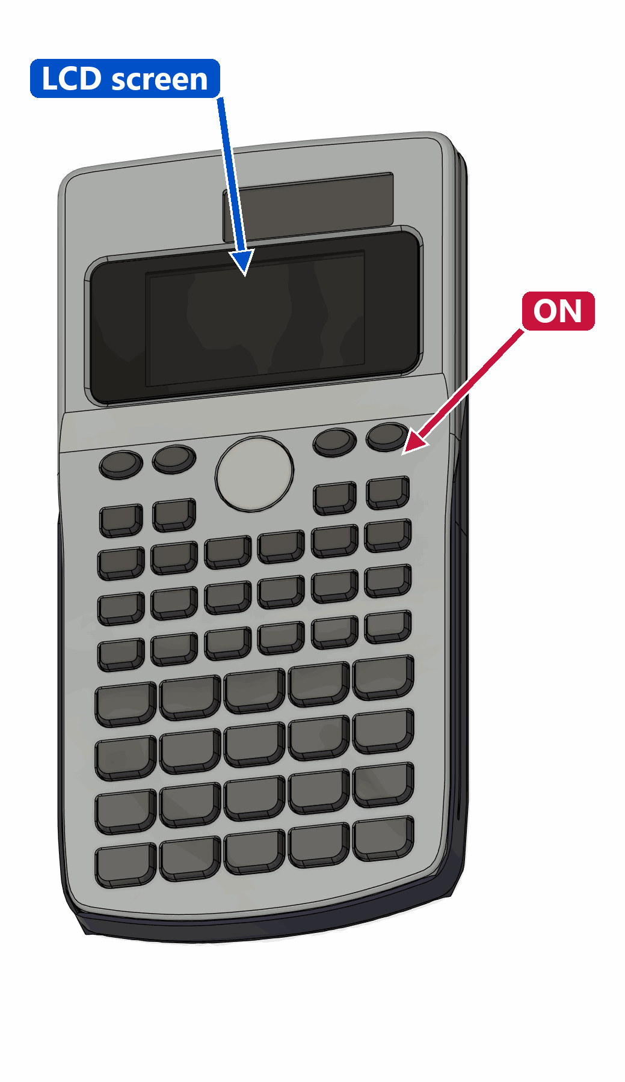
hardware/enclosure/final_assembly_v15_lcd/renders/steps/s11_finished_front_ann.png
