niravkumar2008/AI-CALCULATOR/hardware/enclosure/final_assembly_v15_lcd/variant_camera_dcxyx/dips/renders/dips_section_j1.png

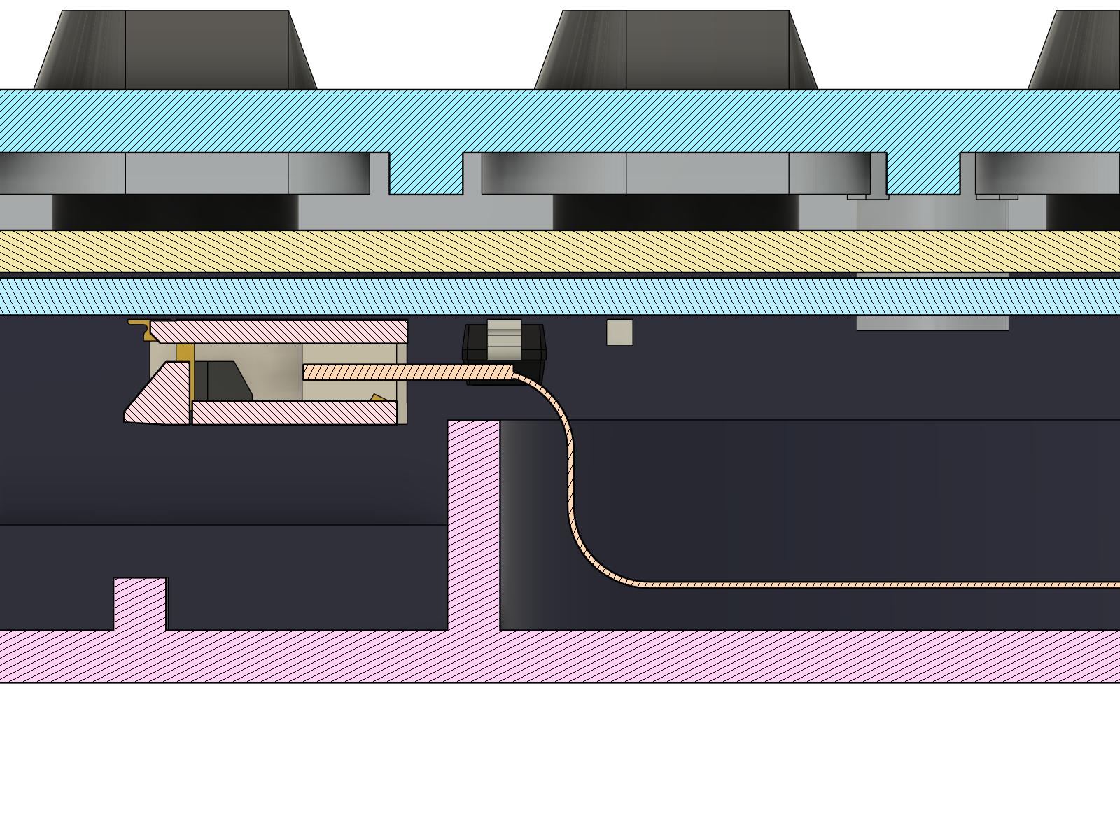
hardware/enclosure/final_assembly_v15_lcd/variant_camera_dcxyx/dips/renders/dips_section_j1.png
