niravkumar2008/AI-CALCULATOR/hardware/enclosure/final_assembly_v15_lcd/variant_camera_dcxyx/move8/renders/move8_back_closed.png

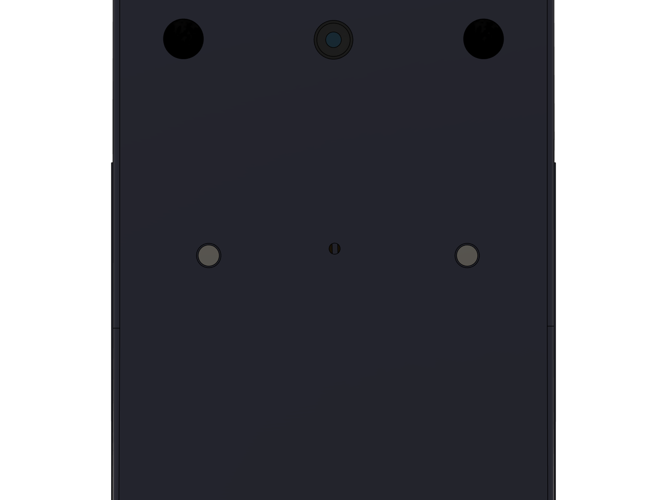
hardware/enclosure/final_assembly_v15_lcd/variant_camera_dcxyx/move8/renders/move8_back_closed.png
