niravkumar2008/AI-CALCULATOR/hardware/enclosure/final_assembly_v15_lcd/variant_goldenmorning/t218/renders/section_lcd_fpc_end.png

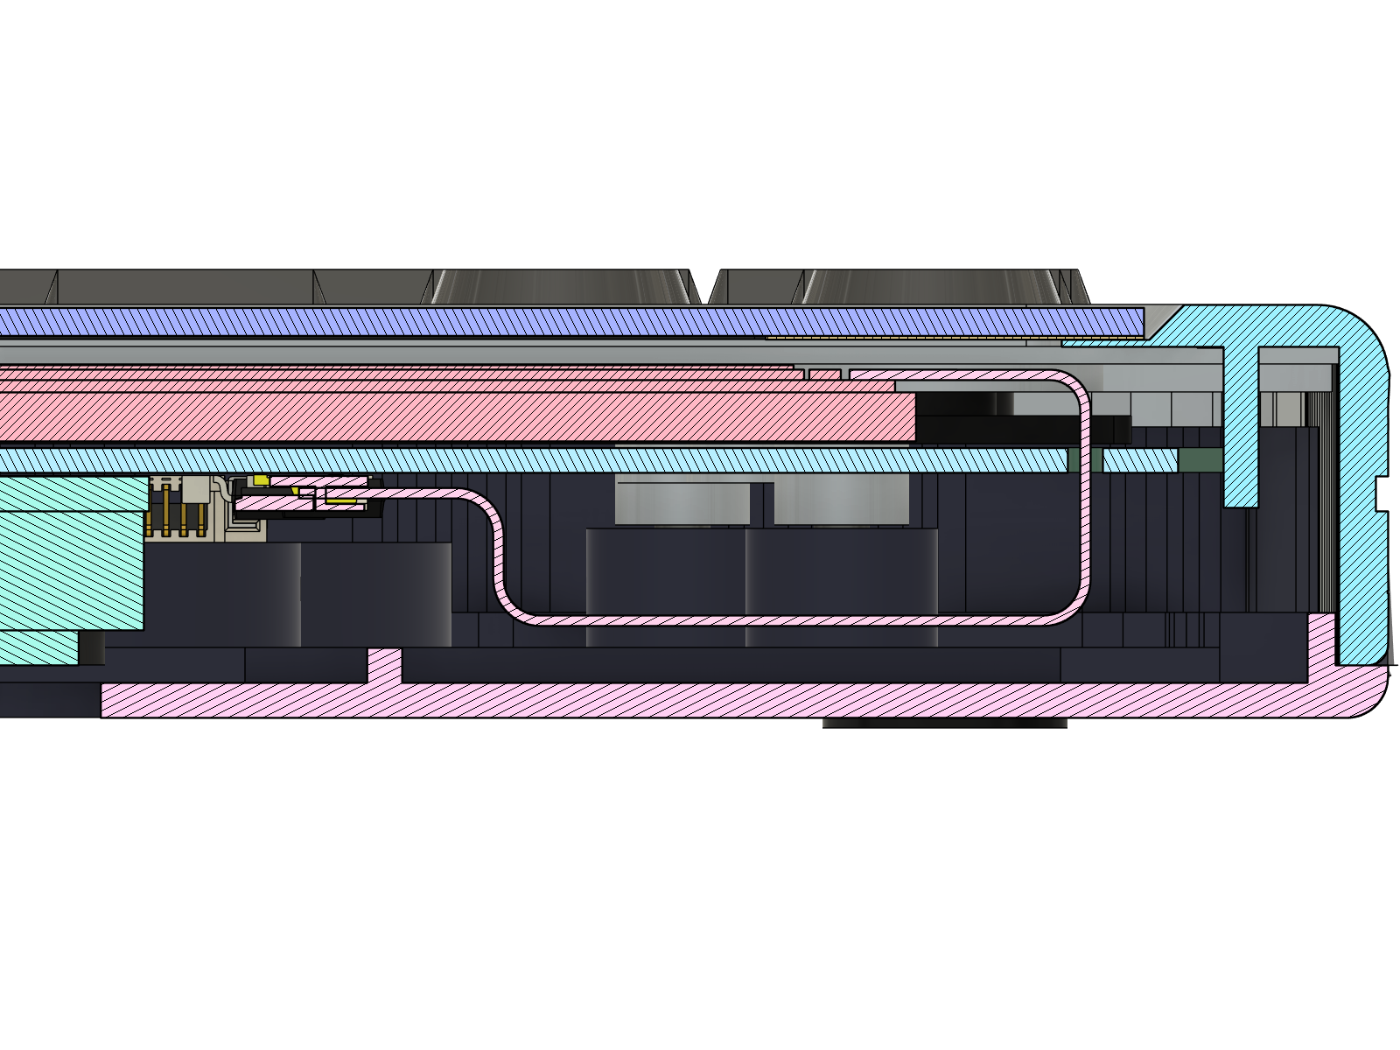
hardware/enclosure/final_assembly_v15_lcd/variant_goldenmorning/t218/renders/section_lcd_fpc_end.png
