niravkumar2008/AI-CALCULATOR/hardware/project_hub/img/anim_assembly_v14.gif

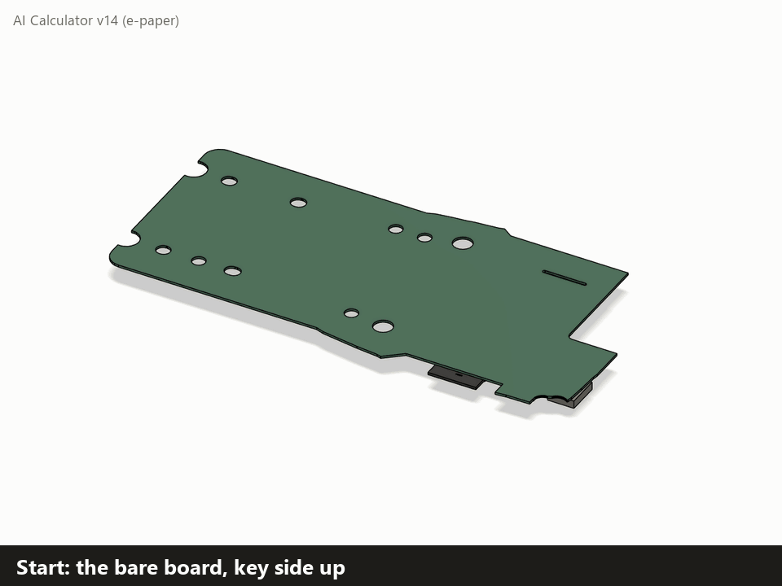
hardware/project_hub/img/anim_assembly_v14.gif
