niravkumar2008/AI-CALCULATOR/hardware/project_hub/img/thumb_assembly_v15.jpg

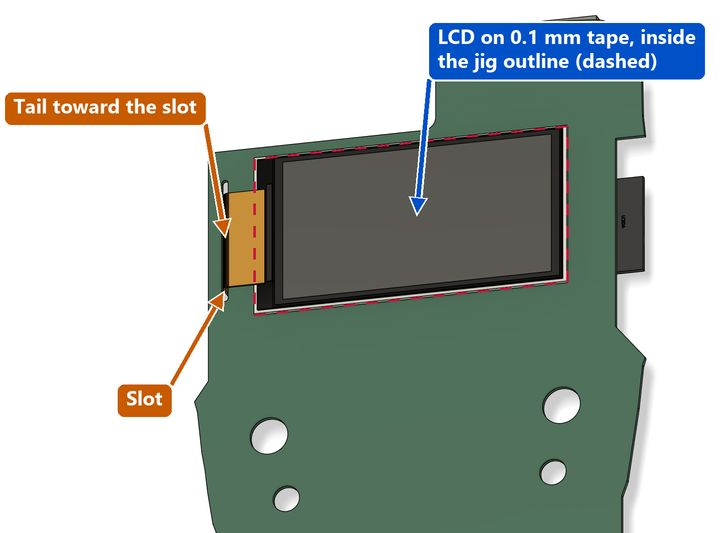
hardware/project_hub/img/thumb_assembly_v15.jpg
