niravkumar2008/AI-CALCULATOR/hardware/bringup_guide.html

AI Calculator · board v14 (stage 14) · firmware stage14-2026.10.10 · boards land about 10–14 days after the JLCPCB order

# First Power-Up Guide

Do these steps in order, one at a time, the day the JLCPCB boards arrive. Every check is there to catch a fault before it can hurt the board. Tick each box as you go; ticks are saved in this browser only.

Five rules for the whole day

1. If anything gets warm, smells, or a reading is wrong: unplug first, think second.
2. Never plug or unplug a ribbon (e-paper, camera) while the board has any power. Once the battery is in, the board is always powered, so ribbons go in before the battery. general practice
3. First power comes from a computer USB port, not a phone charger. A computer port cuts the current quickly on a fault; a charger may push 2 A or more.
4. Never connect the battery until its polarity has been metered (step 4).
5. Never burn eFuses, enable secure boot or flash encryption. They are the only things that can lock you out for good.

0 / 0 done Clear ticks

## 01What you need

- Multimeter with DC volts, continuity (beep), and mA
- Adafruit #5412 magnetic cable and the #5358 magnet piece (or the equivalent Yiwei MG0425-UB-60-4P cable and MG04254FRA1S1N piece; same check)
- A USB phone charger (only for the magnet check)
- USB-A to USB-C adapter, if your PC has only USB-C ports
- Kapton tape, tweezers, two short wires for the test pads
- PC with VS Code + PlatformIO, the repo's firmware-prototype folder
- For step 10: a 2.4 GHz phone hotspot, your AI server's https address and one device token for this board (setting the server up takes about 30 min; do it while you wait for the boards)

Test points on the board, all on the component side, labelled on the silkscreen: TP1 BOOT TP2 TX TP3 RX TP4 GND TP5 3V3 TP6 BAT TP7 EN. The black meter probe goes on TP4 for every voltage reading below.

## AMeet your tools

Ten minutes here saves a board later. You only need four meter settings all day. Your meter's dial may look different; look for the same symbols, not the same positions.

DC volts (V⎓ or V with a straight line). Red lead in VΩ, black in COM. Used for every rail: VBUS, SYS, 3V3, EN, BAT. Pick the 20 V range if it isn't auto-ranging. The meter is just "looking": it can't hurt anything in this mode.

Resistance (Ω). Same sockets. Board unpowered only. Used before first power to prove 3V3 and BAT aren't shorted to GND. The number climbs for a few seconds while the capacitors charge: wait 5 s, then read.

Diode / beep (→| and •))). Same sockets, unpowered. Beep = the two points are connected (under ~30 Ω). Diode shows the voltage a diode or LED needs (used in the QA plan). "OL" or "1" = open, no connection.

Current (mA). The red lead moves to the mA socket, and the meter goes in the wire (in series), never across two points. Only for the optional charge and sleep-current steps.

### How the leads go in, every time

Measuring | Dial | Black lead | Red lead
Volts (a rail) | V⎓, 20 V | COM → TP4 GND | VΩ → the point named in the step
Short check / beep / diode | Ω or →|•))) | COM | VΩ
Current | mA | COM | mA socket, then straight back to VΩ afterwards

### The other tools

The magnetic cable is also the data cable: flashing and the Serial Monitor go through it. A USB-C PC port needs a USB-A→C adapter; any data-capable one works.

Fine-tip tweezers, plastic-tipped if you have them for the socket lids.

Static (ESD) can kill the ESP32 or the e-paper without any visible mark. general practice

- Meter check: set it to beep and touch the probe tips together. It beeps. Set DC volts: it reads 0.00. (Dead battery in the meter = strange readings all day.)
- Sewing pins pushed onto the probe tips for the 0.5 mm ribbon fingers; a strip of tape so the two pins can't touch.

## BBoard map

Every name used below, on the real board (3D render of the v14 files). Yellow tags = test pads, blue = sockets, green = chips, red = parts whose turn matters most. Hold the board the same way: component side up, magnet header (J3) at the top. Tap a picture to open it full size.

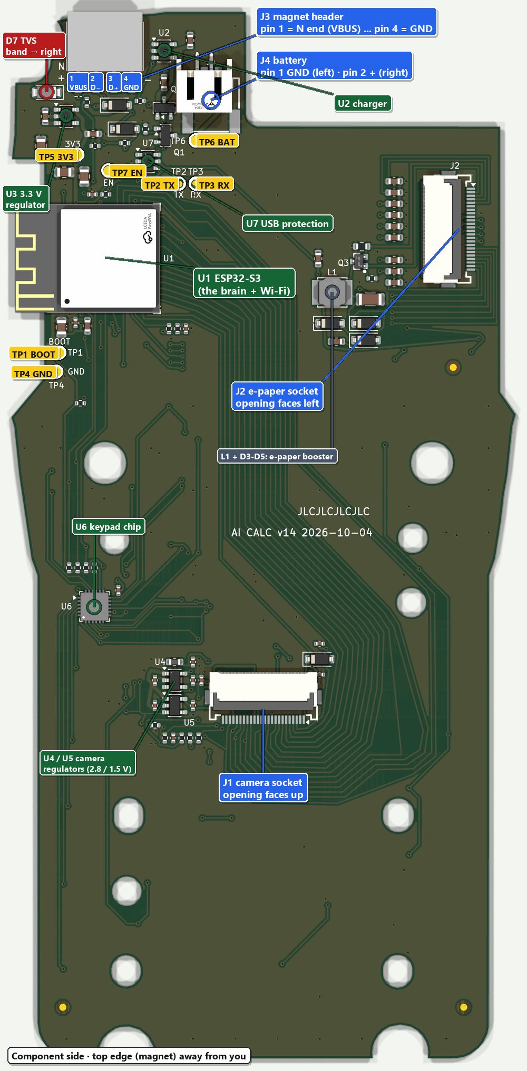
[picture p362: hardware/renders_bringup/v14/map_top.jpg]
Labelled render of the component side: test pads TP1 to TP7, J1 camera, J2 e-paper, J3 magnet header with pins VBUS, D minus, D plus, GND, J4 battery, U1 ESP32, U2 charger, U3 regulator, U7 USB prot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


Component side. TP4 (GND) is at the left edge below the ESP32, next to TP1.

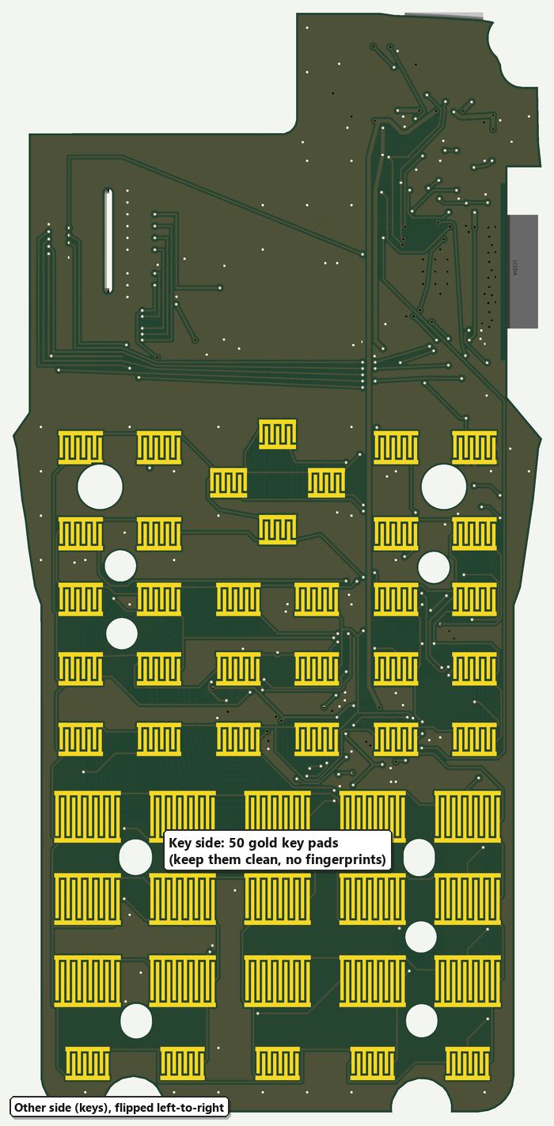
[picture p363: hardware/renders_bringup/v14/map_bottom.jpg]
Render of the key side with the gold key pads


Key side, seen from below (so left and right are swapped). Nothing to measure here; keep the gold pads clean.

### Zoomed in

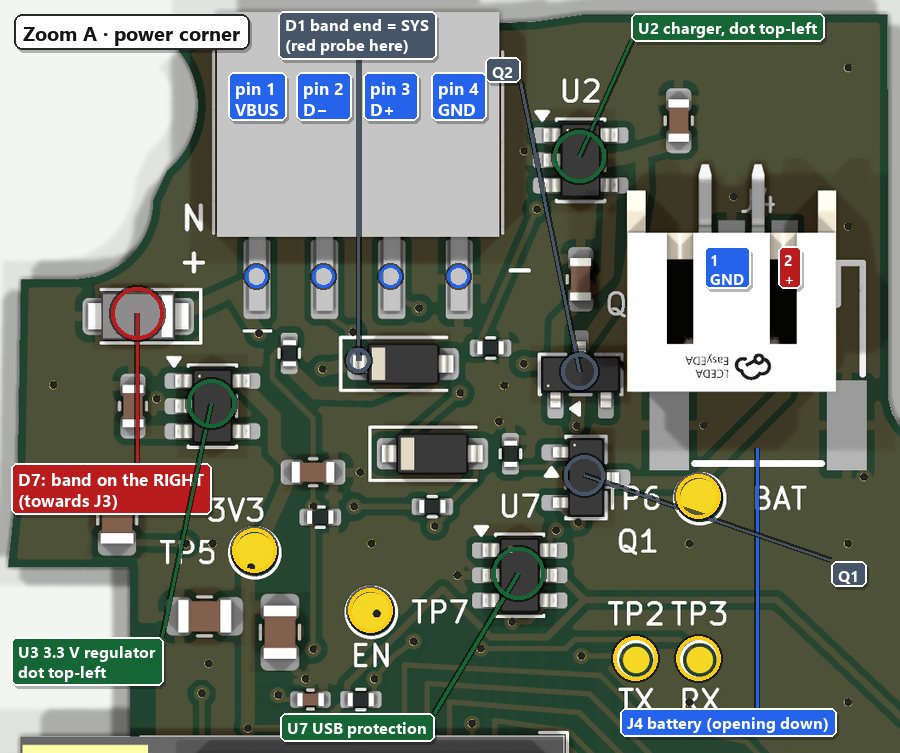
[picture p364: hardware/renders_bringup/v14/zoom_power.jpg]
Zoom A: power corner with J3 pins 1 to 4 labelled VBUS, D minus, D plus, GND; D7 with its band on the right; U3, U2, D1, J4 pin 1 GND and pin 2 plus; Q1, Q2, U7; TP5, TP6, TP7, TP2, TP3


A · Power corner. J3 pin 1 (VBUS) is the left pin, beside the silk N and +. J4: pin 1 GND left, pin 2 + right.

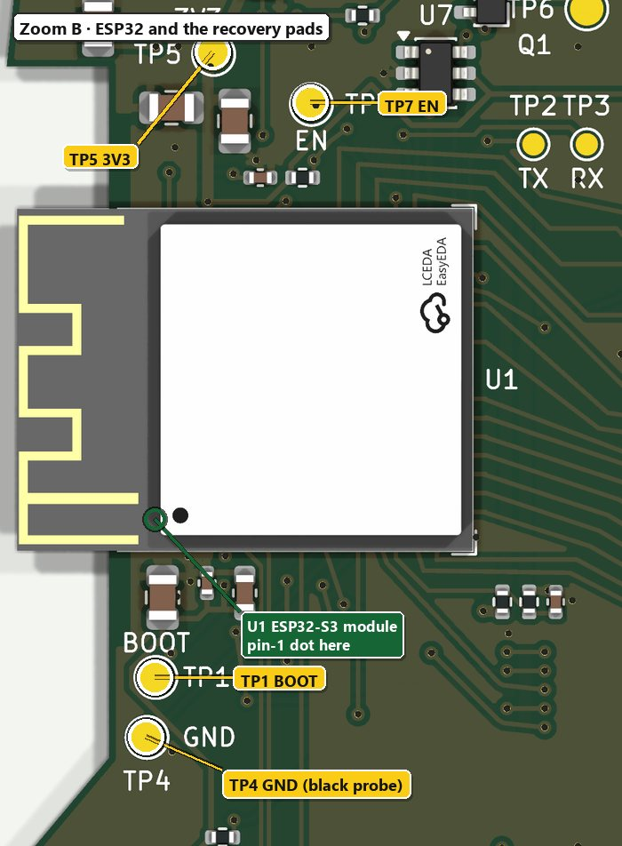
[picture p365: hardware/renders_bringup/v14/zoom_esp32.jpg]
Zoom B: the ESP32 module U1 with its pin-1 dot at the lower left, and the pads TP1 BOOT, TP4 GND, TP7 EN, TP5 3V3


B · ESP32 and the recovery pads. TP1 and TP4 sit 2.7 mm apart.

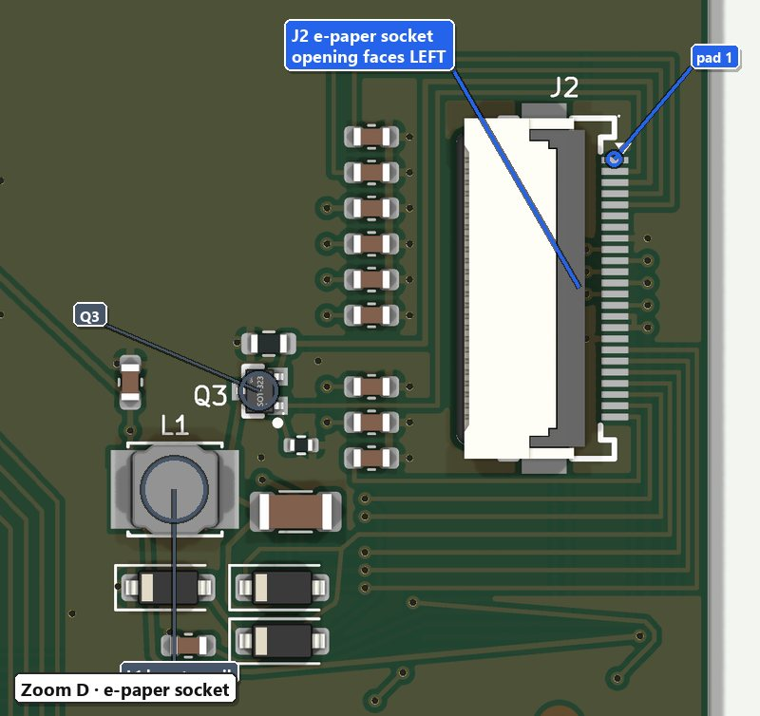
[picture p366: hardware/renders_bringup/v14/zoom_screen.jpg]
Zoom D: the e-paper socket J2


D · e-paper socket J2. Contacts on the right, opening on the left; pad 1 at the top.

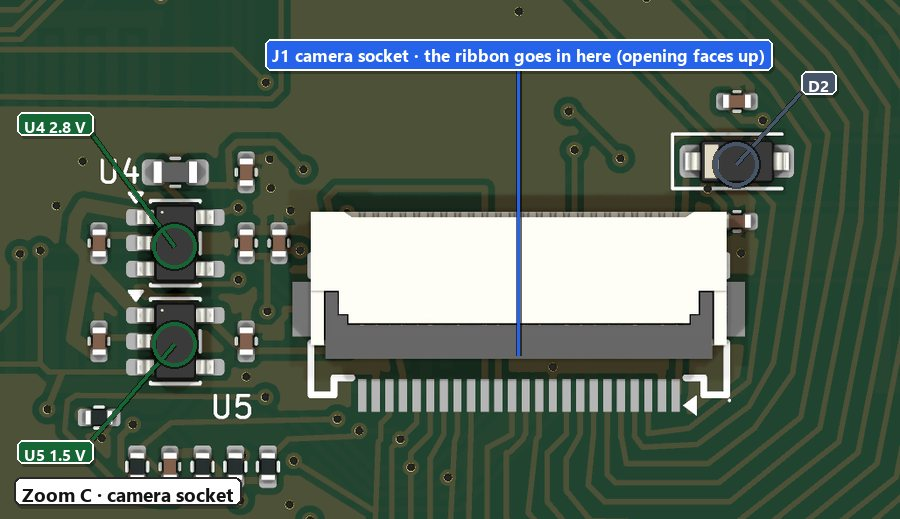
[picture p367: hardware/renders_bringup/v14/zoom_camera.jpg]
Zoom C: camera socket J1 with its camera regulators U4 and U5


C · Camera socket J1, near the bottom of the board, with its two small regulators.

Pad / part | What it is | You use it for
TP4 GND | Ground, 0 V | Black probe, every voltage reading
TP5 3V3 | The 3.3 V rail from U3 | Short check, first-power reading
TP6 BAT | Battery + after Q1 | Short check, battery reading
TP7 EN | ESP32 enable (reset when pulled to GND) | Reading; the "tap" in recovery
TP1 BOOT | GPIO0; held low at reset = download mode | Recovery
TP2 TX TP3 RX | Spare serial port | Last-resort flashing with a 3.3 V USB-serial adapter
J3 | Magnet header: 1 VBUS (N end), 2 D−, 3 D+, 4 GND | Power and USB data
J4 | Battery socket: 1 GND (left), 2 + (right) | The LiPo, after step 4
U1 / U2 / U3 / U7 | ESP32-S3 / LiPo charger / 3.3 V regulator / USB protection | Heat check at first power
J1 / J2 | Camera socket / e-paper socket | Ribbons, step 9

## 02Inspect the bare board

Unpowered, under good light (a phone camera zoomed in works). Hold it like the render: component side up, top edge away from you.

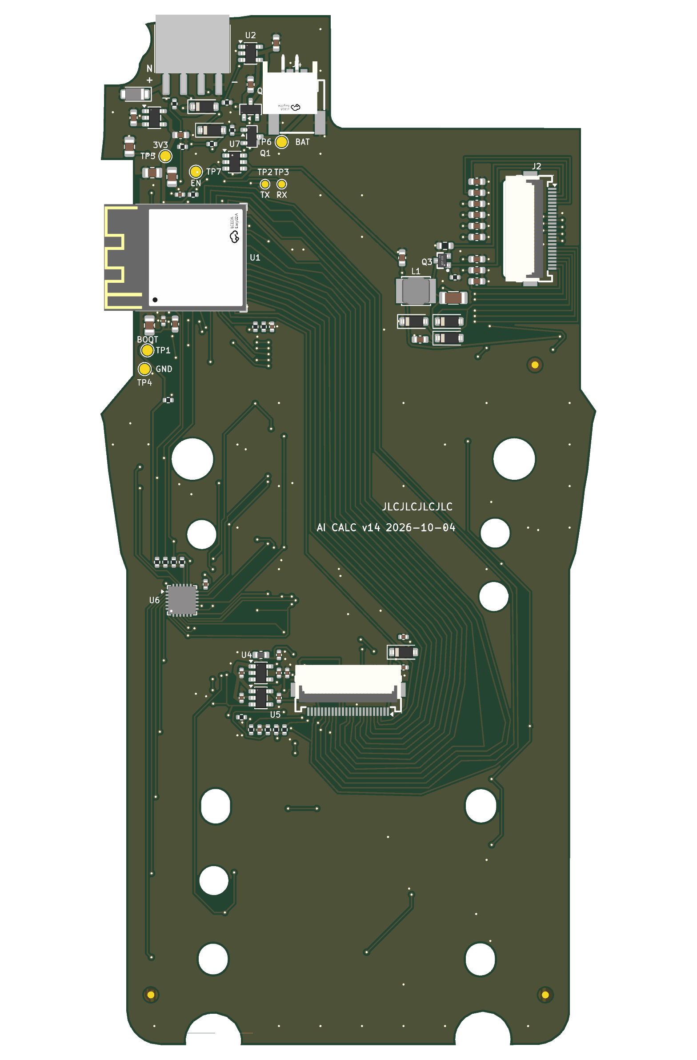
[picture p368: hardware/fab/render_top.png]
Render of the board's component side, top edge at the top


Component side. "Top-left" below means as seen here.

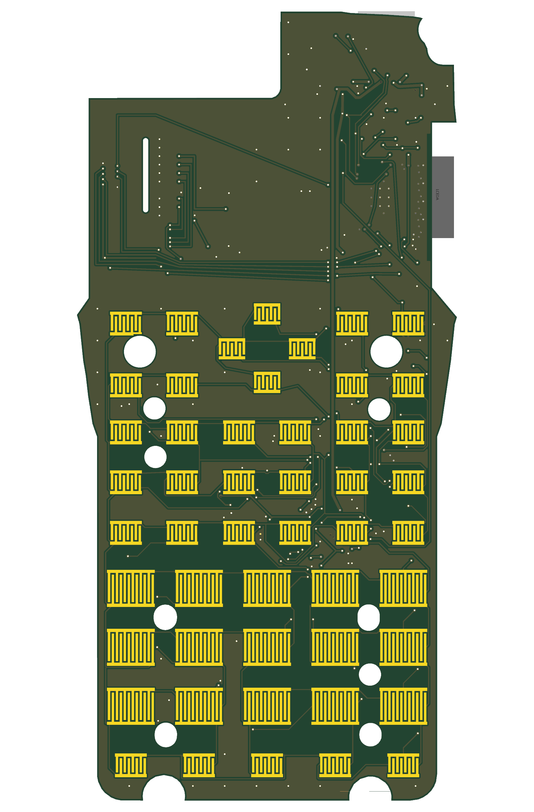
[picture p369: hardware/fab/render_bottom.png]
Render of the board's other side


Other side (key pads).

### What good and wrong look like (loupe checklist)

Use a 10× loupe or the phone camera at 2–3× zoom with the torch on. Compare each part with the drawings, then with zoom A / B / C / D in the board map. JLCPCB also e-mails placement photos: compare those too.

D7: grey body, dark band on the RIGHT (towards J3)

D7 band on the left: VBUS meets the wrong end

U2 / U3 / U4 / U5: dot top-left, 3 pins on the left

Dot at the other corner: chip turned 180°

U1 ESP32: the dot sits at the lower left of the can (antenna on the left edge)

Dot elsewhere: the module is rotated

J1 camera: opening faces up, contacts along the bottom

J1 turned round: contacts on top

J2 as on the render

Socket turned round

Good: smooth, shiny, concave fillet climbing the pin

Bridge: solder joins two pins. Don't power; photo, ask

Tombstone: part stood up on one end (missing joint)

Dull ball / loose solder ball: a joint that may not connect

Real renders of these parts are in the board map zooms A–D. A wrongly turned part on a JLCPCB-assembled board is rare, but D7, the ICs and the two sockets are the ones where it would matter.

- U2 (charger), U3 (3.3 V regulator), U4, U5: pin-1 dot top-left, the 3-pin side on the left. U7 (USB protection, 6 pins): dot top-left.
- Q1: two pins on the left, the single pin on the right. Q2: single pin at the top, two at the bottom. Q3: single pin on the left.
- D7 (near the magnet header): band on the right pad, towards J3. This one matters most. D1–D6: band on the left pad.
- No solder bridges between neighbouring pins, especially on U1 (ESP32), U6 (keypad chip), U7 and the two ribbon sockets. No loose balls of solder.
- J1 (camera) opening faces up towards the camera area; J2 (e-paper) opening faces left, towards the slot. Both lids open and close freely. Leave them closed for now.
- J4 battery socket opening faces down. J3 openings face the top edge.
- Meter on continuity: TP5 3V3 ↔ TP4 GND must not beep steadily. A short "chirp" as capacitors charge is fine. general practice

If a part is turned the wrong way or bridged: don't power it. Photograph it and ask.

### The short check, with pictures (board unpowered)

These four readings catch the faults that could hurt the board or the PC on first power (QA plan A3 #16, 17, 19, 20). Nothing is plugged in, no battery.

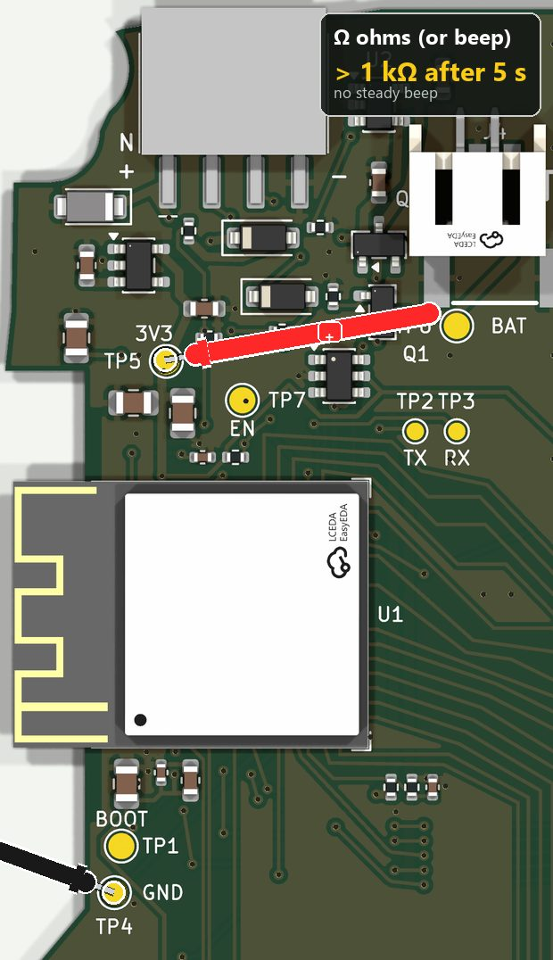
[picture p370: hardware/renders_bringup/v14/m_short_3v3.jpg]
Red probe on TP5, black probe on TP4, meter on ohms
 tap to enlarge

#### TP5 3V3 to TP4 GND: not shorted

Mode

Ω (resistance), or beep

Red

TP5 3V3

Black

TP4 GND

Expect

> 1 kΩ after 5 s (climbing at first is normal). No steady beep.

Wrong

< 100 Ω or a steady beep = short: bridged U3 or a cracked 22 µF capacitor.

Do

Don't power it. Photograph U3 and the caps near TP5; claim with JLCPCB.

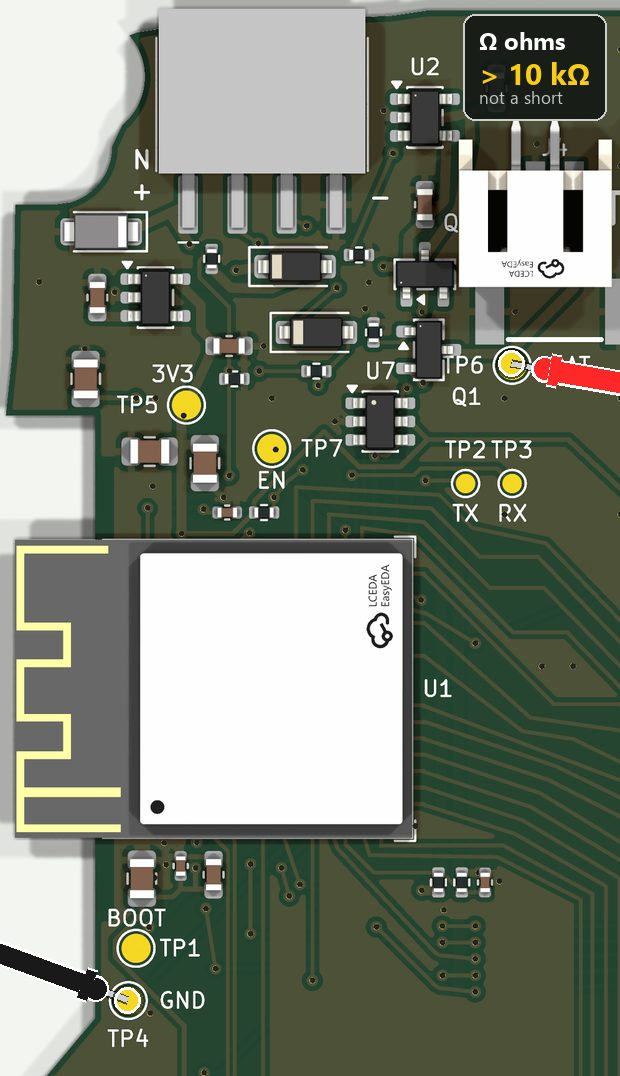
[picture p371: hardware/renders_bringup/v14/m_short_bat.jpg]
Red probe on TP6, black on TP4, ohms
 tap to enlarge

#### TP6 BAT to TP4 GND

Mode

Ω (resistance)

Red

TP6 BAT

Black

TP4 GND

Expect

> 10 kΩ (often around 1–2 MΩ: the battery-sense divider)

Wrong

Near 0 Ω = short on the battery side.

Do

Don't power or fit a battery. Photo of Q1, J4, U2; ask.

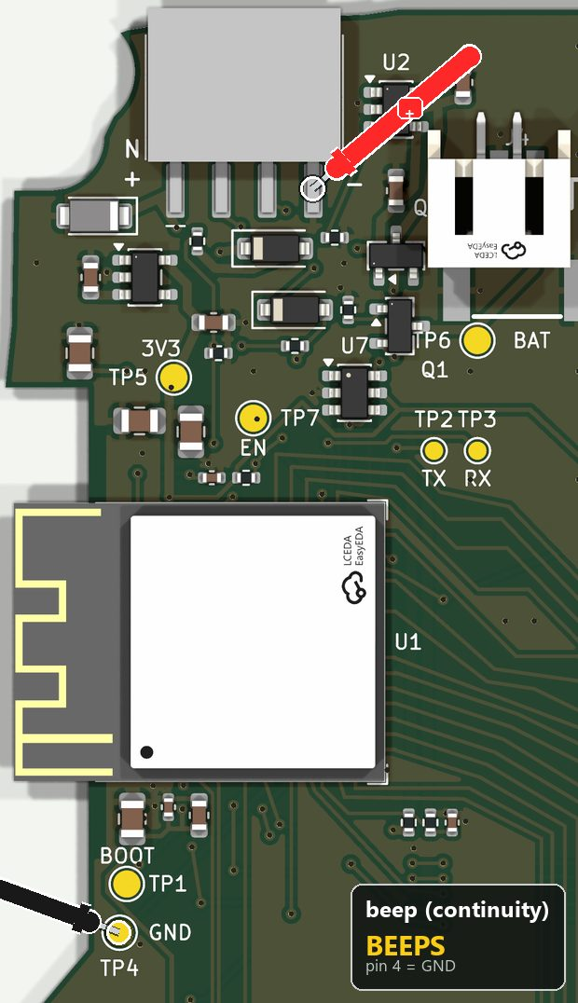
[picture p372: hardware/renders_bringup/v14/m_beep_j3gnd.jpg]
Red probe on J3 pin 4, black on TP4, beep mode
 tap to enlarge

#### J3 pin 4 is GND

Mode

beep (continuity)

Red

J3 pin 4 (the − end)

Black

TP4 GND

Expect

BEEPS

Wrong

No beep = pin 4 not soldered, or you are on pin 1.

Do

Recount the pins from the N end; look at the J3 joints.

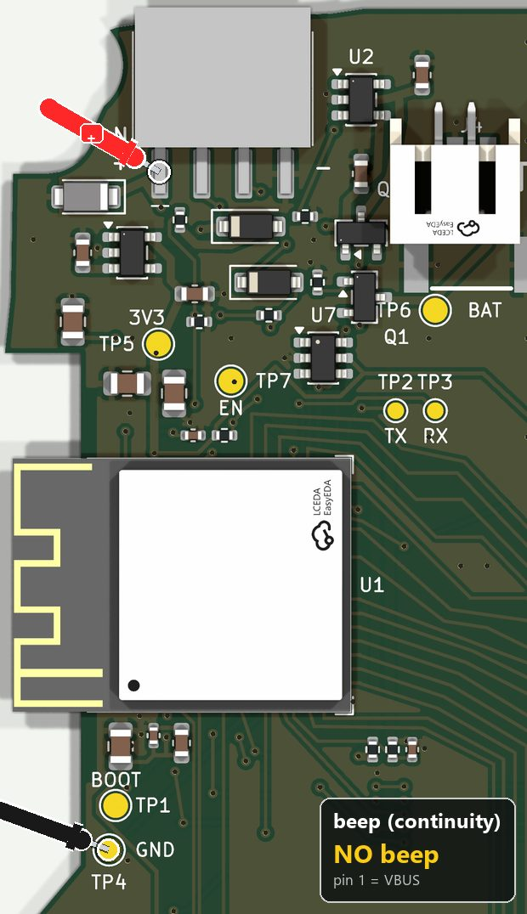
[picture p373: hardware/renders_bringup/v14/m_beep_j3vbus.jpg]
Red probe on J3 pin 1, black on TP4, beep mode
 tap to enlarge

#### J3 pin 1 is NOT GND

Mode

beep (continuity)

Red

J3 pin 1 (the N / + end)

Black

TP4 GND

Expect

NO beep (a short chirp is fine)

Wrong

Steady beep = VBUS shorted to GND (D7 or U7 bridged / reversed).

Do

Don't power. Photo of D7 and U7; ask.

- TP6 ↔ TP4 above 10 kΩ, J3 pin 4 beeps to TP4, J3 pin 1 does not.

## 03Magnet piece check, before gluing

J3 is wired, from pin 1 (silk N and +, leftmost pin seen from the component side, top edge away from you): VBUS, D−, D+, GND. The last pin has the silk −.

Step g2–g3: the piece snapped onto the cable, charger on, legs in the air. Mark the VBUS leg with a pen.

Step g4: which USB-A contact each leg must beep to.

- Straighten the 4 legs of the #5358 piece. Don't fit it yet. Snap the cable's magnet end onto it (it latches only one way).
- Plug the cable's USB-A end into the phone charger. Meter on DC volts. Black probe on one outer leg, red on the other outer leg: about +5 V. The red-probe leg is VBUS: mark it with a pen. (−5 V? swap the probes.)
- Each inner leg to the black (GND) leg reads 0–0.6 V. If 5 V shows on an inner leg, stop: the cable differs from Adafruit's drawing. Don't fit it; ask.
- Unplug the charger. Meter on continuity:
  - VBUS leg beeps to one outer contact of the USB-A plug (USB pin 1). GND leg beeps to the other outer contact (pin 4), usually to the metal shell too.
  - Inner leg next to VBUS beeps to the contact next to pin 1 (pin 2 = D−).
  - Inner leg next to GND beeps to the contact next to pin 4 (pin 3 = D+).
  - Inner legs the other way round: stop and ask. Not harmful, but USB data won't work.
- Push the piece in (no glue) with the VBUS leg in pin 1 (silk N / +) and the GND leg in pin 4 (silk −).
- On the board: J3 pin 4's leg beeps to TP4. J3 pin 1's leg does not beep to TP4.
- Only now glue the body into the top-wall slot (or leave it pushed in for the bench steps and glue at assembly).

Why: fitted backwards, the cable's 5 V lands on the board's GND. A computer port cuts the current quickly, but a phone charger can push 2 A or more through D7 and the charger chip and damage them. Never test that on purpose.

## 04Battery polarity

Polarity before anything else. On the board, J4 + is pin 2, the right-hand one (zoom A).

- Look at J4 from the component side with its opening towards you: − on the left, + on the right (silk "+" / "−" beside it).
- Hold the battery plug the same way it would go in. Meter on DC volts, red probe into the contact that will meet J4 "+": you should read the cell voltage as a positive number (about 3.0–4.2 V), and that contact should be on the red wire. Don't let the probes touch each other.
- If reversed: swap the two crimp pins in the plug. Lift each little plastic tab with a needle, slide the pin out, swap, push back until it clicks. No soldering. Meter again.

Q1 protects the board from a reversed cell, but with USB also plugged in a few mA would flow into the reversed cell. So: polarity first, always.

## 05Camera ribbon beep test

Camera ribbon, gold side up. Orange = the two GND fingers.

- Camera unplugged from everything. Count the ribbon's gold fingers from the end you think is pin 1. Fingers 2 and 15 must beep to each other (both GND).
- If they don't, try 2 against 10. If that pair beeps, you counted from the other end; recount and try again. If neither beeps, stop and ask. (Mirrored, 23 ↔ 10 should not beep.)

While the camera is out: measure its ribbon from the module's far edge to the tip and note it. Under about 70.3 mm means tape the module up to 1.7 mm towards J1 and drill the 7 mm window where the lens actually sits.

## 06First power: USB only

Nothing else connected: no battery, no display, no camera. Magnet piece pushed into J3, cable into a computer USB port. Keep one hand on the plug.

### Current limit: watch the current while you plug in

An inline USB power meter (about $10) between the PC and the cable shows the board's current at once (QA plan A4 #26). limit set in the QA plan, not a measured value

- Plug in. For the first 10 seconds touch the top of U2, U3, U7, D1, D7 and U1 lightly with a fingertip. Anything hot: unplug at once.
- Measure each row below (black probe on TP4) and write the values down.

Rail | Where (red probe) | Expect | If wrong
VBUS | J3 pin 1 leg (no TP on this rail) | ≈ 5.0 V (4.75–5.25) | Near 0 or negative: magnet piece backwards. Unplug.
SYS | D1, the banded (left) end derived from schematic | 4.55–4.7 V | 0 V with good VBUS: check D1. Unplug if anything is warm.
+3V3 | TP5 3V3 | 3.25–3.35 V | 0 V: U3 or SYS. Above 3.6 V: unplug now, ask.
EN | TP7 EN | ≈ 3.3 V (high) | Low: chip held in reset; check for a bridge near TP7.
BAT+ | TP6 BAT | ≈ 0 V, or 4.1–4.25 V | Both are normal with no cell: the charger may regulate into nothing (QA plan A4 #29). Anything else (say 1–4 V, or above 4.3 V): note it, ask before going on.

The VBUS range is the normal USB range, not a board figure. SYS is VBUS minus D1's drop. A few tenths of a volt off on VBUS/SYS is fine; +3V3 should be inside its range.

### Each reading, with a picture

Black probe stays on TP4 GND for all five (put a sewing pin on it and tape the lead down so it can't slide). Meter on DC volts.

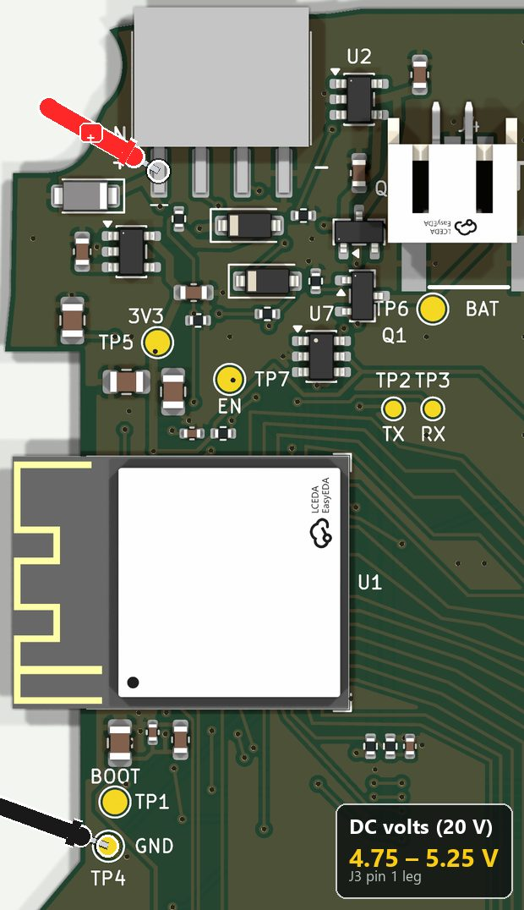
[picture p374: hardware/renders_bringup/v14/m_vbus.jpg]
Red probe on J3 pin 1, black on TP4, DC volts
 tap to enlarge

#### VBUS: power from the cable

Mode

DC volts, 20 V

Red

the J3 pin 1 leg (N / + end)

Black

TP4 GND

Expect

≈ 5.0 V (4.75–5.25)

Wrong

Near 0 or negative: magnet piece backwards. Below 4.75: weak port or cable.

Do

Negative or 0: unplug at once, redo step 3. Low: try another PC port.

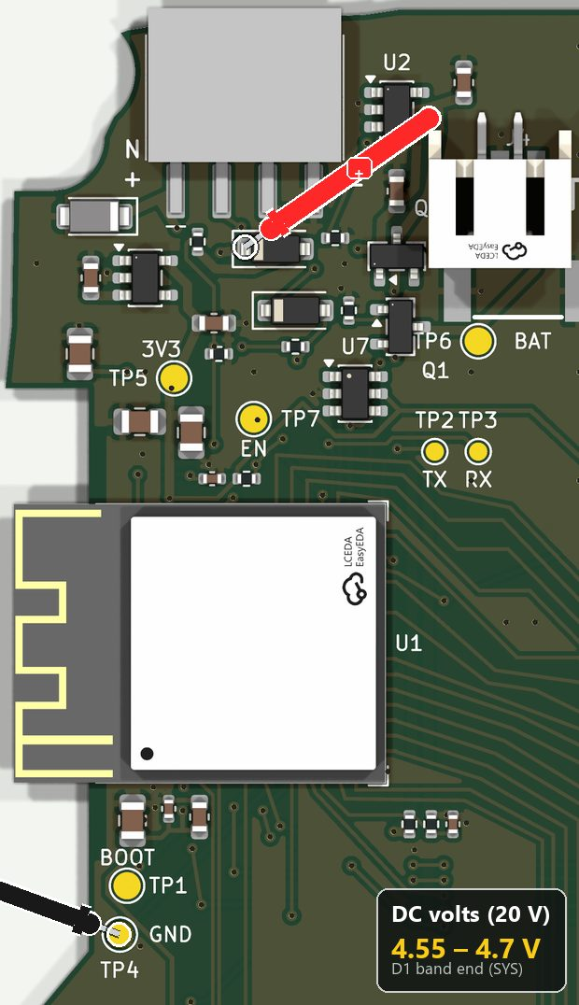
[picture p375: hardware/renders_bringup/v14/m_sys.jpg]
Red probe on the left pad of D1, black on TP4
 tap to enlarge

#### SYS: after diode D1

Mode

DC volts, 20 V

Red

D1's band end (left pad)

Black

TP4 GND

Expect

4.55–4.7 V (VBUS minus about 0.35 V)

Wrong

0 V with good VBUS: D1 open or not soldered. Equal to VBUS: you are on the wrong pad.

Do

Unplug if anything is warm; photo D1; ask.

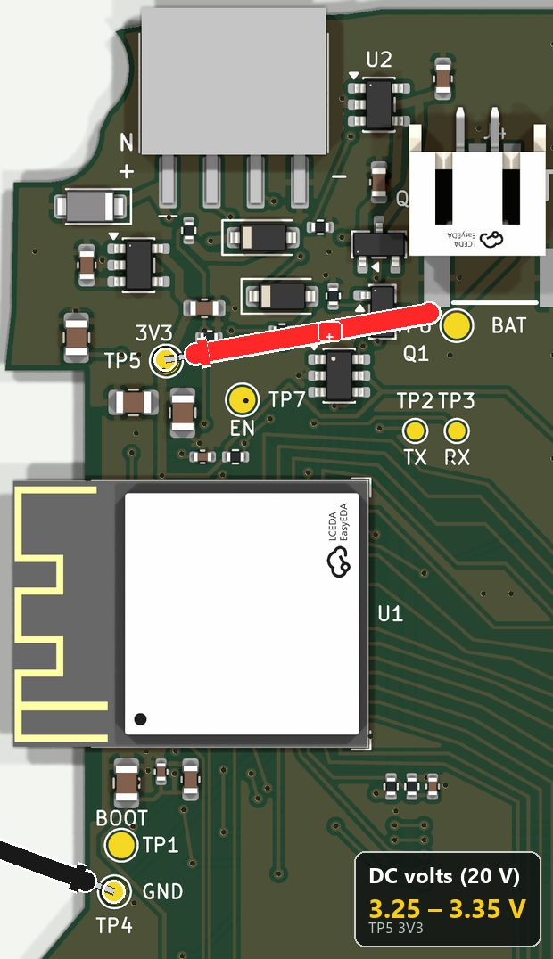
[picture p376: hardware/renders_bringup/v14/m_3v3.jpg]
Red probe on TP5, black on TP4
 tap to enlarge

#### +3V3: the main rail

Mode

DC volts, 20 V

Red

TP5 3V3

Black

TP4 GND

Expect

3.25–3.35 V

Wrong

0 V: U3 not running (or no SYS). Under 3.2 V: overloaded. Above 3.6 V: unplug now.

Do

0 V: measure SYS. Above 3.6 V: unplug, redo the step 3 inner-leg checks, ask.

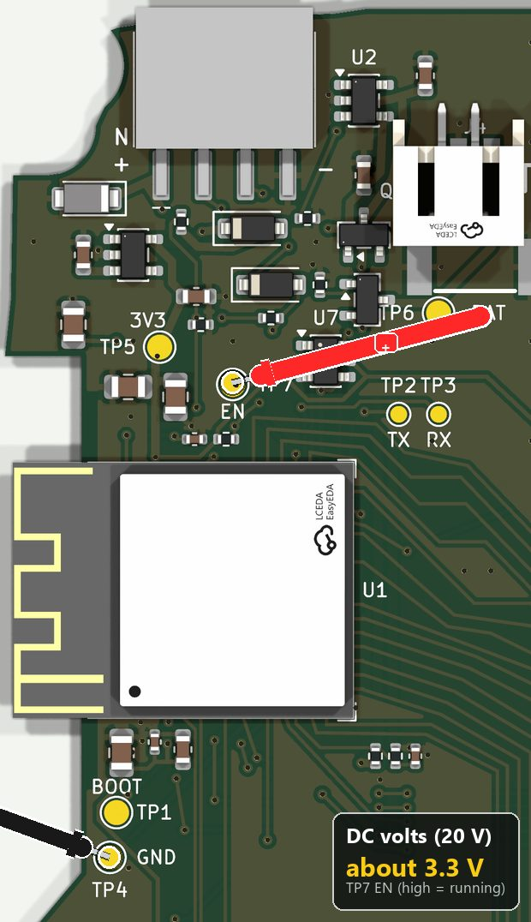
[picture p377: hardware/renders_bringup/v14/m_en.jpg]
Red probe on TP7, black on TP4
 tap to enlarge

#### EN: the chip is allowed to run

Mode

DC volts, 20 V

Red

TP7 EN

Black

TP4 GND

Expect

≈ 3.3 V (above 2.5 V)

Wrong

Low (under 1 V): chip held in reset.

Do

Look for a bridge or solder ball near TP7 and the EN capacitor; ask.

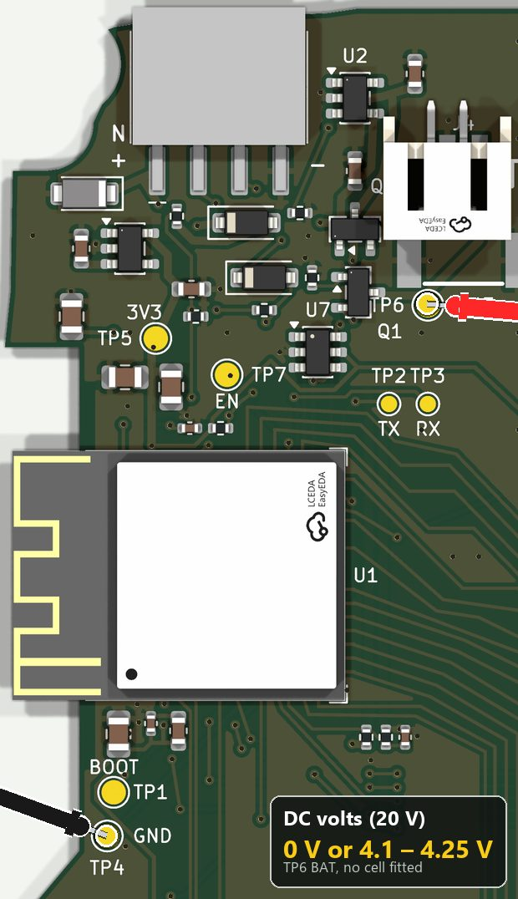
[picture p378: hardware/renders_bringup/v14/m_bat.jpg]
Red probe on TP6, black on TP4
 tap to enlarge

#### BAT: battery pin, no cell yet

Mode

DC volts, 20 V

Red

TP6 BAT

Black

TP4 GND

Expect

≈ 0 V, or 4.1–4.25 V (both normal with no cell)

Wrong

1–4 V, or above 4.3 V.

Do

Note the value and ask before fitting a battery.

Wrong reading or hot part: unplug, let it cool, don't plug in again "to check". Note which part was warm and which reading was off, then ask.

## 07Flash the firmware

- Cable still in the PC. In VS Code open firmware-prototype, click Upload (→ in the blue bar). Command line: %USERPROFILE%\.platformio\penv\Scripts\pio run -t upload
- Open the Serial Monitor at 115200, type help, then status. The first line reads Firmware: stage14-2026.10.10 (slot app0) id … (the version is kFirmwareVersion in src/claude_client.h); below it Wi-Fi: not set, AI proxy: not set, Device token: … (type token). That's expected until step 10.

The first flash is always over USB, on every board: a new board is blank, and this firmware uses a two-slot partition table (min_spiffs.csv) so that later versions can arrive over the air. An over-the-air update only replaces the app in the other slot; it can never write the partition table, so the first flash (and any future partition change) must be this USB upload. After it, status and the self-test show app0; the first over-the-air update moves to app1 (firmware-prototype/README.md §4).

### What it looks like

The PlatformIO buttons live in the blue bar at the bottom of VS Code. If the bar doesn't show env:prototype, the wrong folder is open.

Or type it (VS Code: Terminal > New Terminal, from the repo folder):

cd firmware-prototype %USERPROFILE%\.platformio\penv\Scripts\pio run -t upload %USERPROFILE%\.platformio\penv\Scripts\pio device monitor -b 115200

A good upload ends with Hard resetting via RTS pin... and [SUCCESS]. Then the Serial Monitor; type in the box at the bottom and press Enter:

> status
Firmware: stage14-2026.10.10 (slot app0)  id calc-3f9a21      <- right build, first USB flash
Camera: none
Wi-Fi: not set (type wifi, or = on SETUP 6)          <- normal until step 10
AI proxy: not set (type proxy)
Device token: not set (type token)
Battery: 0% (0 mV)                                     <- no cell yet

Example; the id and some numbers differ on your board.

### If no COM port appears, or "no serial data"

- Hold a wire from TP1 BOOT to TP4 GND.
- With a second wire, tap TP7 EN to TP4 GND for about 0.2 s. The chip restarts in download mode. Release TP1, click Upload.
- When it finishes, tap TP7 to GND once more to start the new firmware.

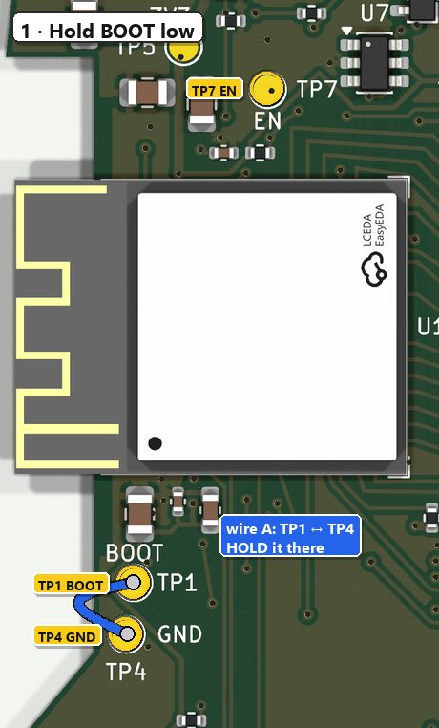
[picture p379: hardware/renders_bringup/v14/recovery_1.jpg]
Panel 1: a wire held from TP1 BOOT to TP4 GND


1 · Hold TP1 to TP4 (a wire, or the tweezers' tip across both pads).

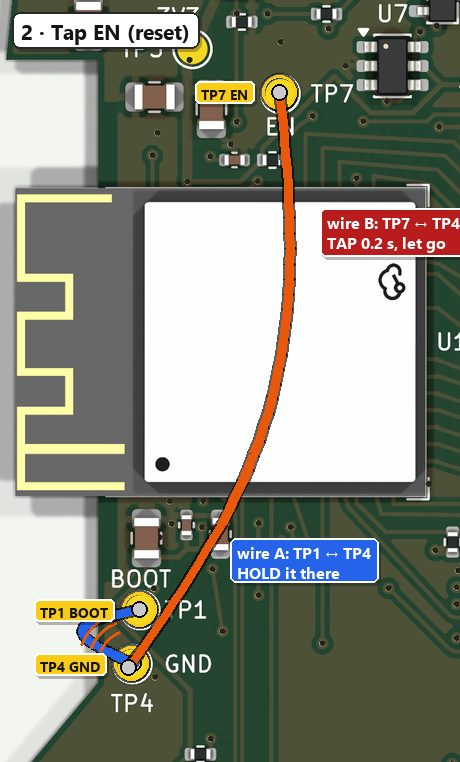
[picture p380: hardware/renders_bringup/v14/recovery_2.jpg]
Panel 2: keep TP1 held, briefly tap a second wire from TP7 EN to TP4 GND


2 · Keep holding; tap TP7 to TP4 for about 0.2 s. The chip restarts in download mode.

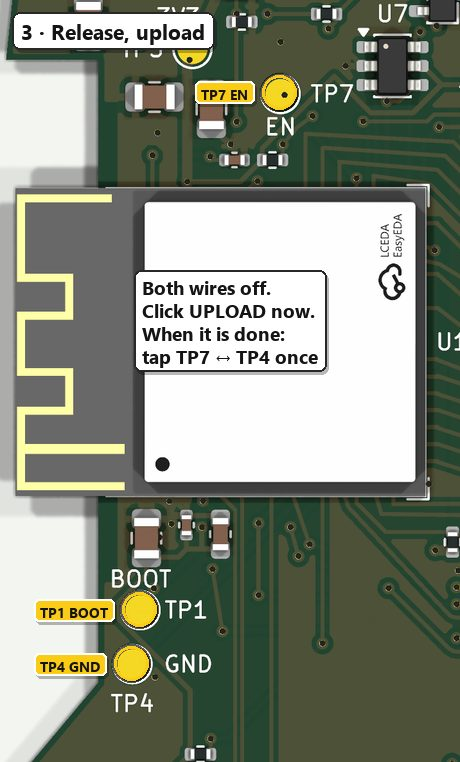
[picture p381: hardware/renders_bringup/v14/recovery_3.jpg]
Panel 3: both wires off, click Upload; afterwards tap TP7 to TP4 once


3 · Let go of TP1, click Upload. When it finishes, tap TP7 once more to start the new firmware.

In download mode the Serial Monitor shows waiting for download and the COM port number may change. Nothing you do on these pads can damage the board: they are pulled up through resistors. Never touch TP5 (3V3) to TP4.

With a battery connected later, plugging the cable in does not reset the chip, so holding BOOT while plugging in does nothing. Use the TP7 tap (or unplug the battery first). Last resort: a 3.3 V USB-serial adapter on TP2 (TX) / TP3 (RX) / TP4 (GND), then the same TP1 + TP7 sequence. In deep sleep the USB port disappears: press ON to bring it back.

## 08Factory self-test

- Type selftest in the Serial Monitor (the key combo, hold SHIFT + ALPHA, press ON, needs the keypad, so use the command on the bench). Type q to skip the 50-key test for now.
- Copy the SELFTEST_JSON line into a text file. With nothing attached, expect display_ok, camera_ok, keys_all_ok and so pass to be false; that's fine here. Without a panel the screen step no longer stalls (BUSY has a pull-down).

Field | Good value | What it proves
firmware, firmware_slot | stage14-…, app0 | Which build is running and from which app slot (app0 after a USB flash, app1 after the first over-the-air update)
memory_ok | true | 4 MB flash, 2 MB PSRAM found
keypad_scanner_ok | true | U6 (TCA8418) answers on I²C
vbus | true | Cable detected
battery_mv, battery_ok, charge | 3000–4300, true | Meaningful once a cell is in (with no cell and the cable in it may read about 4200 mV: the charger regulating into nothing)
display_refresh_ms, display_ok | 300–9000, true | E-paper BUSY line and booster work; look for dead lines
camera_ok, camera_jpeg_bytes, camera_autofocus | true, > 1000, true | OV5640 ID read, a VGA JPEG taken, the autofocus firmware loaded
wifi_ok | true | ≥ 1 network better than −80 dBm
keys_ok, keys_missing, keys_all_ok | 50, [], true | Every key (needs the rubber keypad: Assembly Guide steps 8 and 11)
pass | true | Everything above

SELFTEST_JSON {"firmware":"stage14-2026.10.10","firmware_slot":"app0","device_id":"calc-…","trigger":"serial","reset_reason":"…","memory_ok":true,"keypad_scanner_ok":true,"battery_mv":3987,"battery_pct":75,"vbus":true,"chg_stat_high":false,"charge":"charging","battery_ok":true,"display_refresh_ms":2140,"display_ok":true,"camera":"…OV5640","camera_jpeg_bytes":31877,"camera_autofocus":true,"camera_ok":true,"wifi_networks":7,"wifi_best_rssi":-48,"wifi_ok":true,"keys_ok":50,"keys_total":50,"keys_missing":[],"keys_all_ok":true,"pass":true}

Example of a full pass (shortened: the real line also has chip_rev, flash_mb, psram_kb, camera_ms, wifi_tx_cap_dbm_x4 and battery_mv_radio_on)

### The JSON line, field by field

The line is long; this is the same example split up. Left: the field and a good value. Right: what it tells you. Paste your real line into a text file and go down this list.

firmware: "stage14-2026.10.10"

The build that is running.

firmware_slot: "app0"

app0 after a USB flash; app1 after the first over-the-air update.

device_id: "calc-…"

This board's id. Write it on the bag.

reset_reason: "…"

Why it last restarted. 'brownout' = power dipped.

memory_ok: true

4 MB flash + 2 MB PSRAM found. False = wrong module or bad U1 joint.

keypad_scanner_ok: true

U6 answers on I²C. False = U6 bridge or pull-ups.

battery_mv: 3987

Cell voltage. 3000–4300 = ok. About 4200 with no cell and a cable = charger idling.

vbus / charge: true / "charging"

Cable seen; charger running.

display_refresh_ms / display_ok: 2140 / true

E-paper refresh 300–9000 ms (typ. 1800–2500). < 300 = BUSY never seen; > 9000 = booster.

camera_ok / camera_jpeg_bytes: true / 31877

OV5640 found and a JPEG over 1000 bytes taken.

camera_autofocus: true

Autofocus firmware loaded: the right (AF) camera.

wifi_networks / wifi_best_rssi: 7 / -48

At least one network better than −80 dBm.

keys_ok / keys_missing: 50 / []

Every key pressed. 'q' skips: then false, fine on the bench.

pass: true

Everything above. On the bare board it is false: that's fine here.

## 09Display, camera, then battery

Unplug the cable before each ribbon. Both sockets are flip-lid, dual-contact (they touch both faces of the ribbon).

### Ribbon technique general practice

- Lift the lid gently with a fingernail or the tweezers' tip, by its centre, to about 90°. Don't force it past its stop.
- Slide the ribbon in straight and fully (no angle), then press the lid down until it sits flat. Tug lightly: the ribbon must not move.

### Order

- E-paper into J2. The ribbon folds behind the panel and comes up through the slot into J2 (its length budget has no spare, so it must go fully in). Plug the cable in, run selftest: display_ok true, checkerboard visible.
- Unplug. Camera into J1 (only after step 5 passed). Lay the camera lens-up where it will sit and run its ribbon straight into J1, with no twist or flip (that's how the board was designed). Plug in, selftest: camera_ok true. If it fails, reseat once; then try the ribbon with a 180° twist (the J1 orientation is about 90 % sure, and the twist is the known fix). contact side not verified on a real part
- Unplug. Battery into J4 (polarity already checked). From now on the board is always on.
- Plug the cable in. status should say "(charging)"; later "(USB, full)". In the self-test JSON, chg_stat_high is false while charging and true when done. There's no charge LED on this board.
- Charge current is set to 50 mA. If you can put the meter (mA range) in series with the battery lead, expect about 50 mA mid-charge, about 5 mA if the cell is below ~3 V, tapering near full.
- Compare status mV with the meter on TP6 BAT once and note both (for the battery calibration).
- Optional: no cable, switch off (SHIFT AC), wait 10 s, battery current in series: target ≤ 40 µA.

### Optional current readings (meter in mA / µA)

Charge current: about 50 mA mid-charge, about 5 mA below ~3 V, tapering near full (R2 = 20 k on both boards). Sleep current (no cable, switched off, after 10 s): ≤ 40 µA; use the µA range if your meter has one. lead method: general practice

## 10Connect it to the AI server

The maths works without any of this. For AI SOLVE the calculator needs three things: a phone hotspot (2.4 GHz), the address of your AI server (the proxy in server/proxy) and its own device token. The Claude API key lives only on the server. The calculator never holds it: the token command refuses anything starting with sk-ant-.

### Once: put the server online (about 30 min, best while you wait for the boards)

The whole AI setup on one page. The phone form's four fields are exactly the ones in the firmware's setup page; the token starts with dt_, the device id (for revoke) with dev_.

- On Render (or Railway / Fly.io): a new Web Service from this repo, root directory server/proxy (the Dockerfile is ready). Add a 1 GB disk mounted at /data (the database and the firmware images live there).
- In the service's Environment settings: ANTHROPIC_API_KEY = your key, here and nowhere else (not in git, not in the calculator, not in a chat). PUBLIC_URL = the https address the host gives you. Everything else in .env.example can stay as it is.
- Set a monthly spend limit in the Anthropic Console. Open https://<your address>/healthz in a browser: it answers {"ok": true, …}.

### Per calculator: make its token

- In the host's shell (Render: the service's Shell tab; Fly.io: fly ssh console): python admin.py new-device "calc 1". Copy the token: it is shown once. One token per calculator; python admin.py revoke dev_… stops a lost one.

### Put the settings in the calculator (cable in)

- Serial Monitor: wifi → hotspot name and password (iPhone: turn on Maximize Compatibility). proxy → https://<your address>. token → paste it.
- Or from a phone (the way a customer does it): type setup here; on a finished calculator it is SHIFT MODE (SETUP), 6, =. The e-paper shows SETUP BY PHONE with a network AI-Calc-xxxx and an 8-character password (the Serial Monitor prints them too). Join it on the phone; the form pops up as the sign-in page (or open http://192.168.4.1). Pick the hotspot, type its password, the server address and the token (empty = keep the old one), Save. The network closes a few seconds later. AC (or setup off) cancels; it also ends by itself after 10 minutes.
- status: your hotspot's name, AI proxy: https://… and a masked Device token. The settings are kept in flash (they survive switching off, a battery pull and firmware updates; forget erases them).
- pair prints a 6-letter code. On the phone open https://<your address>/link, type the code and your e-mail. The free month starts. account shows it.
- Optional, camera connected: keys m4 (MODE 4 = AI SOLVE), point the camera at a printed problem, keys =. The log shows [solve] … answer after … ms. Otherwise the real AI test is Assembly Guide step 11.

Screen messages: Not set up yet: SETUP 6 = address or token missing. NO CONNECTION = the hotspot is off or not 2.4 GHz. AI ACCOUNT = not linked yet, trial over, or the monthly cap (the server's own sentence is shown). Battery low: plug in the cable to use AI solve = the cell is under 3.6 V: camera and Wi-Fi stay off until it is back above 3.7 V or a cable is in; maths keeps working. Later firmware versions reach the calculator over the air from this server (firmware-prototype/README.md §4, server/proxy/README.md).
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
