niravkumar2008/AI-CALCULATOR/hardware/bringup_guide_v15_lcd.html

AI Calculator · board v15-LCD (review 13, 2026-10-08) · firmware v15lcd-2026.10.10 (firmware-v15-lcd) · not for v14 boards

# v15 First Power-Up

The power-up guide for the colour-screen board: the v14 board with the e-paper swapped for a 1.9" IPS LCD on socket J5. Do the steps in order, one at a time, the day the boards arrive. Every check is there to catch a fault before it can hurt the board. Ticks are saved in this browser only, separately from the v14 guide.
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
