niravkumar2008/AI-CALCULATOR/hardware/verification/renders/composite_bottom_mirrored.png

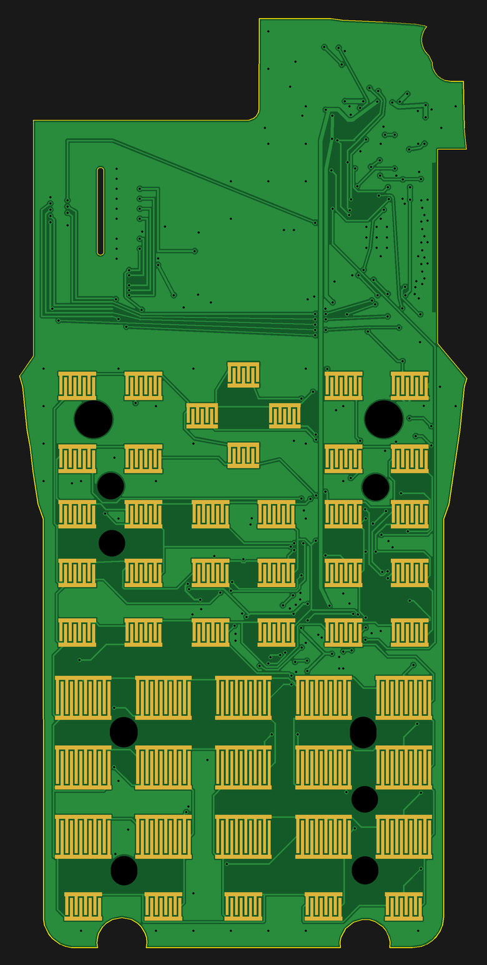
hardware/verification/renders/composite_bottom_mirrored.png
