niravkumar2008/AI-CALCULATOR/hardware/verification/renders/composite_top.png

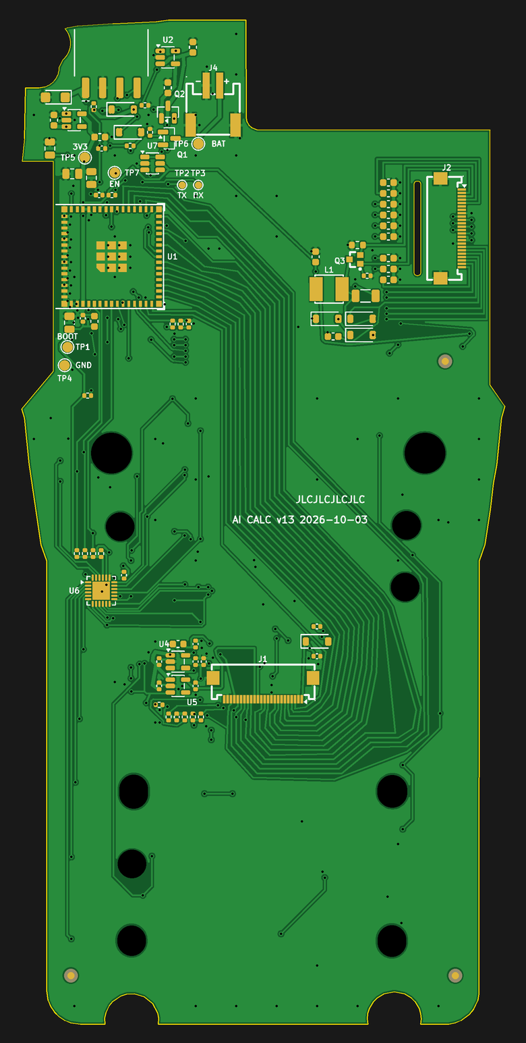
hardware/verification/renders/composite_top.png
