niravkumar2008/AI-CALCULATOR/hardware/verification/renders/layer_B_Mask.png

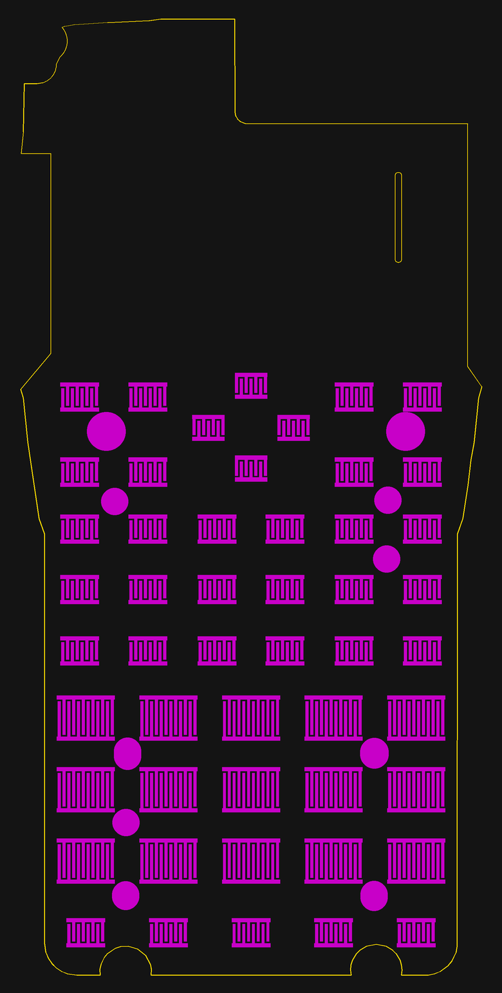
hardware/verification/renders/layer_B_Mask.png
