niravkumar2008/AI-CALCULATOR/hardware/verification/renders/layer_Edge.png

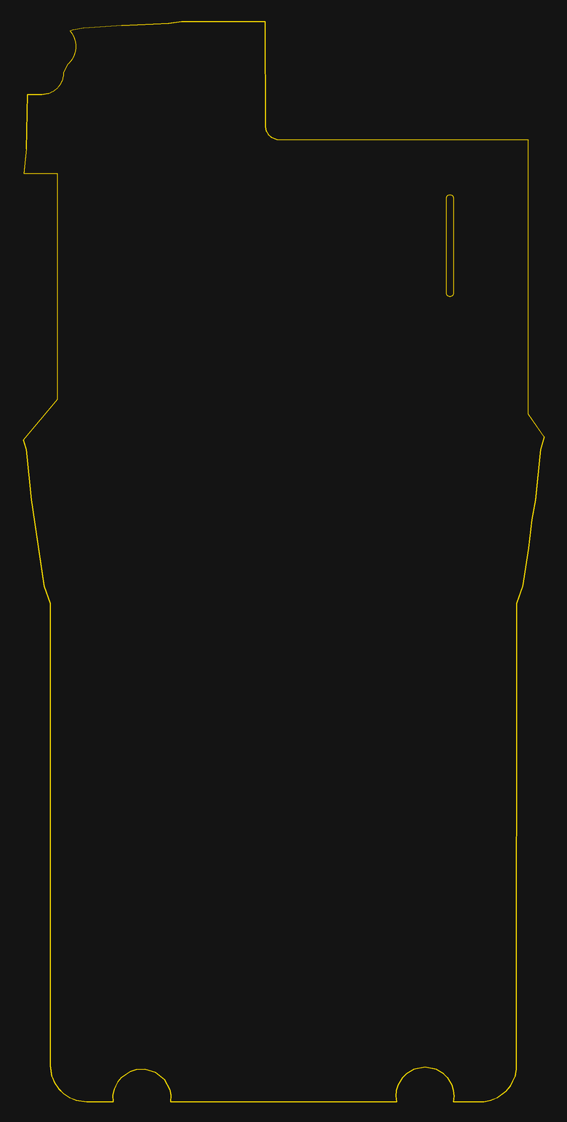
hardware/verification/renders/layer_Edge.png
