niravkumar2008/AI-CALCULATOR/hardware/verification/renders/layer_F_Mask.png

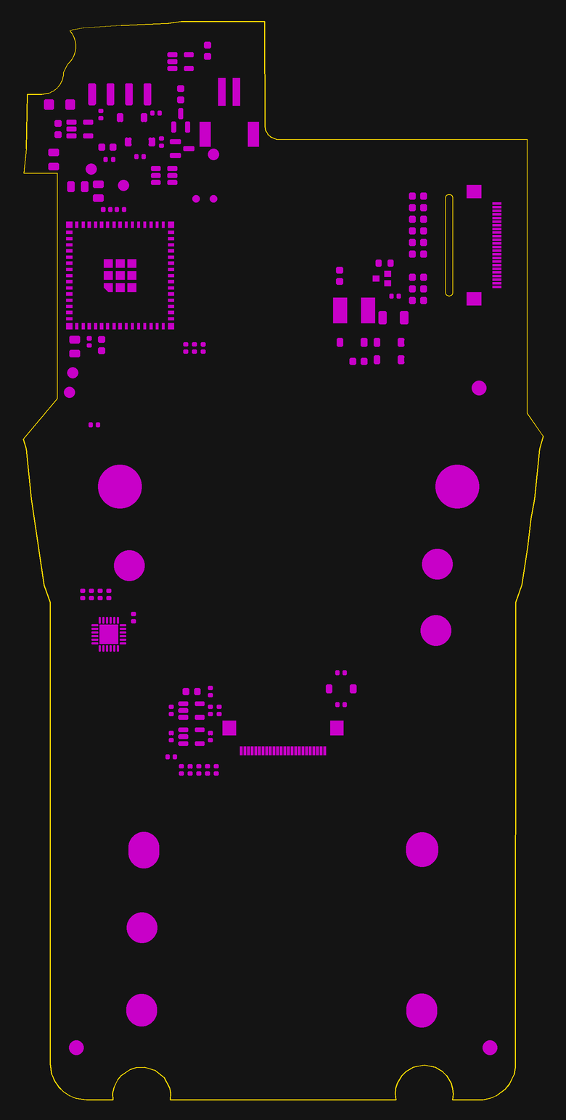
hardware/verification/renders/layer_F_Mask.png
