niravkumar2008/AI-CALCULATOR/hardware/verification/renders/layer_F_Paste.png

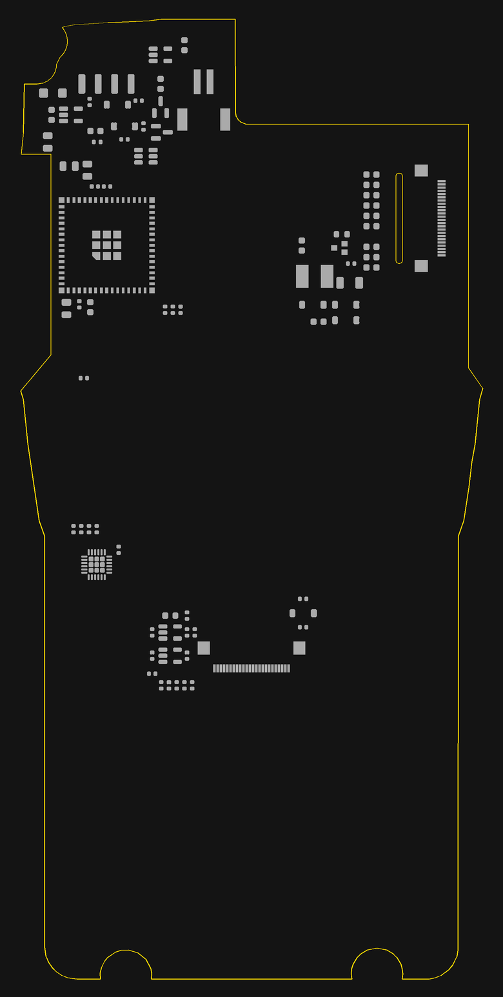
hardware/verification/renders/layer_F_Paste.png
