niravkumar2008/AI-CALCULATOR/hardware/verification/renders/layer_F_Silk.png

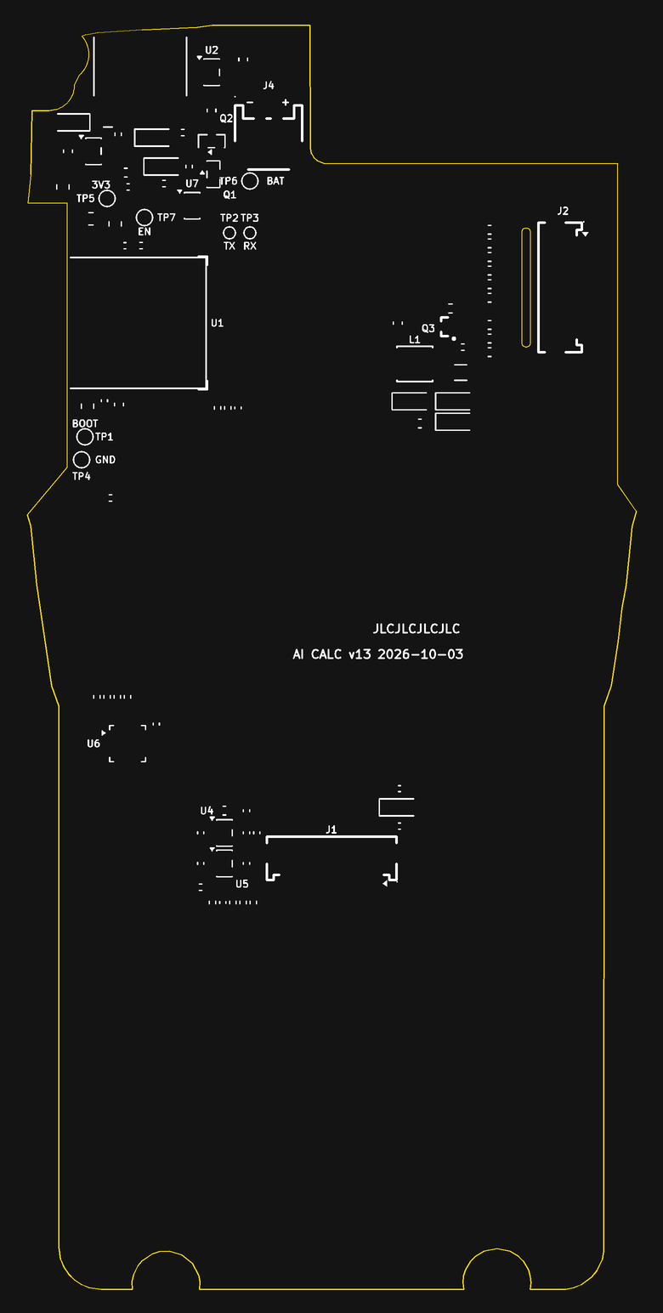
hardware/verification/renders/layer_F_Silk.png
