niravkumar2008/AI-CALCULATOR/hardware/verification/renders/zoom_J1_U4_U5.png

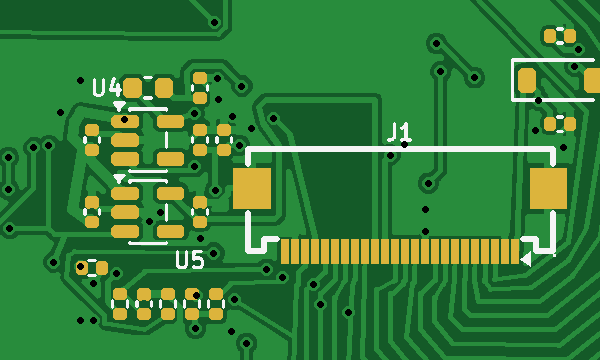
hardware/verification/renders/zoom_J1_U4_U5.png
