niravkumar2008/AI-CALCULATOR/hardware/verification/renders/zoom_SW1_H3_npth_clearance_bottom.png

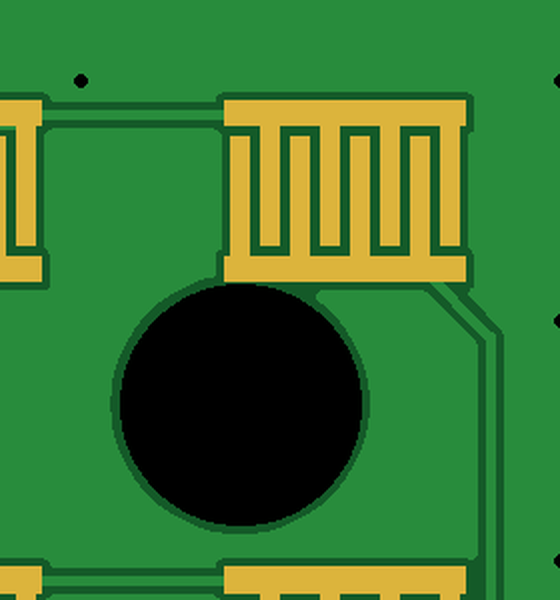
hardware/verification/renders/zoom_SW1_H3_npth_clearance_bottom.png
