niravkumar2008/AI-CALCULATOR/hardware/verification/renders/zoom_U1_antenna_top.png

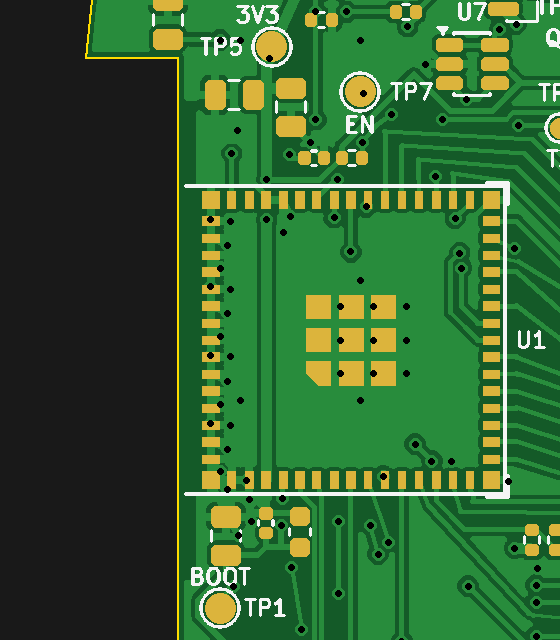
hardware/verification/renders/zoom_U1_antenna_top.png
