niravkumar2008/AI-CALCULATOR/firmware-prototype/src/pins.h

// Every pin of the board lives in ONE file: hardware/pins_final.h (checked against the
// schematic's netlist). This header only includes it, so the firmware can never drift
// from the board. Don't add pins here: change hardware/pins_final.h instead.
#pragma once
#include <stdint.h>

#include "../../hardware/pins_final.h"
