niravkumar2008/AI-CALCULATOR/firmware-v15-lcd/src/ota.h

// Over-the-air firmware updates from the AI proxy (review S1).
//
// The flash holds two app slots (platformio.ini: min_spiffs.csv, 1.9 MB each). An update
// is downloaded from the proxy (GET /v1/firmware for the manifest, then the image), its
// SHA-256 is checked against the manifest before it is accepted, and it is written to the
// slot that is not running. The next restart boots it. If that boot crashes before the
// firmware confirms itself (otaConfirm), the bootloader goes back to the old slot
// (CONFIG_BOOTLOADER_APP_ROLLBACK_ENABLE is on in this SDK; verifyRollbackLater() in
// ota.cpp stops the Arduino core from confirming blindly at start).
//
// The image is sent over TLS to a root-pinned proxy that only answers this calculator's
// device token, and its hash is checked; there is no signing key in the firmware.
#pragma once
#include <functional>
#include <string>

#include "settings.h"

struct OtaInfo {
  bool available = false;  // the proxy has an image that differs from the running version
  std::string version;     // its version string
  std::string sha256;      // 64 hex characters
  std::string path;        // where to GET it, e.g. "/v1/firmware/image"
  size_t size = 0;
};

// Only on a cable, or a well-charged cell: a download is a long Wi-Fi burst.
constexpr int kOtaMinBatteryMv = 3800;

// Asks the proxy (Wi-Fi must be connected). False = couldn't ask; `error` says why.
bool otaCheck(const Settings& s, OtaInfo& info, std::string& error);
// Downloads, checks the hash and writes the other slot. True = restart to run it.
// progress(percent) is called as bytes arrive (for the e-paper).
bool otaInstall(const Settings& s, const OtaInfo& info, const std::function<void(int)>& progress, std::string& error);

// This boot is the first run of a just-installed image: it must confirm itself.
bool otaPendingVerify();
// The new image works (keypad answers, the loop runs): keep it. Safe to call any time.
void otaConfirm();
// "app0" / "app1": which slot is running, for status and logs.
const char* otaSlotName();
