niravkumar2008/AI-CALCULATOR/firmware-v15-lcd/src/selftest.cpp

#include "selftest.h"

#include <Arduino.h>
#include <WiFi.h>
#include <esp_chip_info.h>

#include <string>
#include <vector>

#include "camera.h"
#include "claude_client.h"
#include "framebuffer.h"
#include "glyphdraw.h"
#include "keys.h"
#include "log.h"
#include "ota.h"
#include "pins.h"
#include "lcd.h"
#include "power.h"
#include "settings.h"
#include "ui.h"

using calc::DKey;
using calc::Framebuffer;

namespace {
constexpr int kKeyCount = int(DKey::Count);  // 49 matrix keys + ON = 50
constexpr uint32_t kKeyTimeoutMs = 90000;
constexpr uint32_t kResultShownMs = 60000;    // the PASS / FAIL screen stays this long
constexpr uint32_t kPatternShownMs = 1500;    // a moment to look at the checkerboard
constexpr uint32_t kKeyScreenEveryMs = 1500;  // e-paper: key count redrawn at most this often
constexpr int kLcdPushMaxMs = 200;  // a 320x170 frame at 40 MHz takes ~22 ms; far more = SPI trouble
constexpr int kBatteryMinMv = 3000, kBatteryMaxMv = 4300; // a connected cell
constexpr int kWifiMinRssi = -80;

std::string jsonStr(const std::string& s) {
  std::string o = "\"";
  for (char c : s) {
    if (c == '"' || c == '\\') o += '\\';
    if (static_cast<unsigned char>(c) < 0x20) continue;
    o += c;
  }
  return o + "\"";
}

struct Json {
  std::string s = "{";
  void add(const char* k, const std::string& raw) {
    if (s.size() > 1) s += ",";
    s += "\"" + std::string(k) + "\":" + raw;
  }
  void str(const char* k, const std::string& v) { add(k, jsonStr(v)); }
  void num(const char* k, long v) { add(k, std::to_string(v)); }
  void boolean(const char* k, bool v) { add(k, v ? "true" : "false"); }
  std::string done() const { return s + "}"; }
};

void show(const std::vector<std::string>& lines) {
  ui::Status st;
  st.battery = batteryPercent();
  st.charging = chargeState() == calc::Charge::Charging;
  ui::showLines(lines, st);
}

// v15 screen check: colour bars (every channel, stuck pixels, the column offset), a
// white border (panel alignment and the 170-px edge), then a backlight sweep 0 -> 100 %.
// The panel cannot answer (SDO is not wired), so "ok" here means the driver initialised
// and a full frame pushed in a sane time; the eyes do the rest (bringup_guide).
uint32_t lcdPattern() {
  LGFX_Sprite& s = lcd::canvas();
  s.fillSprite(ui::color::black);
  const uint16_t bars[] = {ui::color::white, lcd::rgb(255, 255, 0), lcd::rgb(0, 255, 255), lcd::rgb(0, 255, 0),
                           lcd::rgb(255, 0, 255), lcd::rgb(255, 0, 0), lcd::rgb(0, 0, 255), ui::color::black};
  for (int i = 0; i < 8; ++i) s.fillRect(i * 40, 0, 40, 110, bars[i]);
  for (int x = 0; x < 320; ++x) {  // a grey ramp: banding shows a wrong colour depth / byte order
    const uint8_t v = uint8_t(x * 255 / 319);
    s.fillRect(x, 112, 1, 30, lcd::rgb(v, v, v));
  }
  s.drawRect(0, 0, 320, 170, ui::color::white);
  s.drawRect(1, 1, 318, 168, ui::color::white);
  s.fillRect(0, 144, 320, 24, ui::color::black);
  // Caption: what to look at on the left, this board's id on the right (measured, so the
  // two never overlap and nothing runs off the 320-px edge).
  const std::string id = deviceId();
  const int idX = 314 - glyphdraw::width(id, 2) + 2;
  glyphdraw::text(s, idX, 148, id, 2, ui::color::dim);
  std::string caption = "SELF-TEST: bars, ramp";
  if (6 + glyphdraw::width(caption, 2) > idX - 8) caption = "SELF-TEST";
  glyphdraw::textFit(s, 6, 148, caption, 2, ui::color::white, idX - 8 - 6);
  lcd::flush();
  return lcd::lastFlushMs();
}

bool g_seen[kKeyCount];
int g_seenCount = 0;
int g_acPresses = 0;
void onTestKey(DKey k) {
  if (k >= DKey::Count) return;
  if (!g_seen[int(k)]) {
    g_seen[int(k)] = true;
    ++g_seenCount;
    LOGF("selftest", "key %-6s ok (%d/%d)", calc::dkeyName(k), g_seenCount, kKeyCount);
  }
  g_acPresses = k == DKey::AC ? g_acPresses + 1 : 0;
}
}  // namespace

bool selfTestComboHeld() { return keysHeld(DKey::Shift) && keysHeld(DKey::Alpha); }

[[noreturn]] void selfTestRun(const char* trigger) {
  LOGF("selftest", "start (%s)", trigger);
  Json j;
  bool pass = true;
  j.str("firmware", kFirmwareVersion);
  j.str("firmware_slot", otaSlotName());
  j.str("device_id", deviceId());
  j.str("trigger", trigger);
  j.str("reset_reason", resetReasonText());

  // 1. Chip and memory
  esp_chip_info_t chip;
  esp_chip_info(&chip);
  j.num("chip_rev", chip.revision);
  j.num("flash_mb", long(ESP.getFlashChipSize() / (1024 * 1024)));
  j.num("psram_kb", long(ESP.getPsramSize() / 1024));
  const bool memOk = ESP.getPsramSize() >= 2 * 1024 * 1024 - 65536 && ESP.getFlashChipSize() >= 4 * 1024 * 1024;
  j.boolean("memory_ok", memOk);
  pass &= memOk;

  // 2. Keypad scanner on I2C
  j.boolean("keypad_scanner_ok", keysScannerOk());
  pass &= keysScannerOk();

  // 3. Battery and charging
  const int mv = batteryMillivolts();
  j.num("battery_mv", mv);
  j.num("battery_pct", calc::lipoPercent(mv));
  j.boolean("vbus", usbPresent());
  j.boolean("chg_stat_high", statPinHigh());
  const calc::Charge ch = chargeState();
  j.str("charge", ch == calc::Charge::Charging ? "charging" : ch == calc::Charge::Full ? "full" : "no_cable");
  // A connected cell reads 3.0-4.25 V. No cell (or a reversed one behind Q1) reads
  // ~0 V, or the charger's 4.2 V regulation with a cable in.
  const bool batOk = mv >= kBatteryMinMv && mv <= kBatteryMaxMv;
  j.boolean("battery_ok", batOk);
  pass &= batOk;

  // 4. LCD (v15): colour bars + border, then a backlight sweep. The old e-paper fields
  // (display_refresh_ms, display_ok) are kept for the bring-up guide's checklist; the new
  // ones are lcd_ok, lcd_push_ms, backlight_ok.
  show({"SELF-TEST", "Screen pattern..."});
  const bool lcdInit = lcd::begin();
  const uint32_t pushMs = lcdInit ? lcdPattern() : 0;
  const bool lcdOk = lcdInit && pushMs < uint32_t(kLcdPushMaxMs);
  j.boolean("lcd_ok", lcdOk);
  j.num("lcd_push_ms", long(pushMs));
  j.num("display_refresh_ms", long(pushMs));
  j.boolean("display_ok", lcdOk);
  bool blOk = lcdInit;
  if (lcdInit) {  // 0 -> 100 % in 1.5 s, then the user's setting: a dead FET / LED shows here
    for (int pct = 0; pct <= 100; pct += 5) {
      lcd::setBrightness(pct < 10 ? 10 : pct, false);
      delay(75);
    }
    blOk = lcd::level() >= 100;
    delay(kPatternShownMs);
    lcd::setBrightness(60, false);
  }
  j.boolean("backlight_ok", blOk);
  j.num("backlight_pct", long(lcd::brightness()));
  pass &= lcdOk && blOk;
  const bool epdOk = lcdOk;  // for the result screen below

  // 5. Camera
  show({"SELF-TEST", "Camera..."});
  std::string sensor;
  size_t bytes = 0;
  uint32_t camMs = 0;
  bool af = false;
  const bool camOk = cameraSelfTest(sensor, bytes, camMs, af);
  j.str("camera", sensor);
  j.num("camera_jpeg_bytes", long(bytes));
  j.num("camera_ms", long(camMs));
  j.boolean("camera_autofocus", af);
  j.boolean("camera_ok", camOk);
  pass &= camOk;
  cameraSleep();

  // 6. Wi-Fi: scan (no password needed), strongest signal, battery dip while the radio works.
  show({"SELF-TEST", "Wi-Fi scan..."});
  WiFi.mode(WIFI_STA);
  powerLimitWifi();
  const int n = WiFi.scanNetworks();
  int best = -127;
  for (int i = 0; i < n; ++i) best = std::max(best, int(WiFi.RSSI(i)));
  const int mvRadio = batteryMillivolts();
  WiFi.scanDelete();
  WiFi.mode(WIFI_OFF);
  j.num("wifi_networks", n < 0 ? 0 : n);
  j.num("wifi_best_rssi", n > 0 ? best : 0);
  j.num("wifi_tx_cap_dbm_x4", kWifiMaxTxQuarterDbm);
  j.num("battery_mv_radio_on", mvRadio);
  const bool wifiOk = n > 0 && best > kWifiMinRssi;
  j.boolean("wifi_ok", wifiOk);
  pass &= wifiOk;

  // 7. Every key (needs a person): press all 50, or AC twice in a row to stop early.
  g_seenCount = 0;
  g_acPresses = 0;
  for (bool& s : g_seen) s = false;
  LOGF("selftest", "press every key once (ON too); AC twice in a row (or q here) to stop early");
  uint32_t t0 = millis(), shownAt = 0;
  int shownCount = -1;
  while (g_seenCount < kKeyCount && millis() - t0 < kKeyTimeoutMs && g_acPresses < 2) {
    keysPoll(onTestKey);
    if (Serial.available() && Serial.read() == 'q') break;  // "q" in the Serial Monitor skips
    if (g_seenCount != shownCount && millis() - shownAt > kKeyScreenEveryMs) {
      shownCount = g_seenCount;
      shownAt = millis();
      show({"SELF-TEST: KEYS", "Press every key once.", std::to_string(g_seenCount) + " of " + std::to_string(kKeyCount) + " done",
            "AC AC: stop early", "", std::to_string((kKeyTimeoutMs - (millis() - t0)) / 1000) + " s left"});
    }
    delay(5);
  }
  std::string missing;
  for (int k = 0; k < kKeyCount; ++k)
    if (!g_seen[k]) missing += std::string(missing.empty() ? "" : ",") + jsonStr(calc::dkeyName(DKey(k)));
  j.num("keys_ok", g_seenCount);
  j.num("keys_total", kKeyCount);
  j.add("keys_missing", "[" + missing + "]");
  const bool keysOk = g_seenCount == kKeyCount;
  j.boolean("keys_all_ok", keysOk);
  pass &= keysOk;

  j.boolean("pass", pass);
  Serial.printf("SELFTEST_JSON %s\n", j.done().c_str());
  show({pass ? "SELF-TEST PASS" : "SELF-TEST FAIL", std::string("Keys ") + std::to_string(g_seenCount) + "/50" + (keysOk ? " ok" : ""),
        std::string("Screen ") + (epdOk ? "ok" : "FAIL") + "  Camera " + (camOk ? "ok" : "FAIL"),
        std::string("Wi-Fi ") + (wifiOk ? std::to_string(best) + " dBm" : "FAIL") + "  Bat " + std::to_string(mv) + "mV",
        std::string("Charge ") + (ch == calc::Charge::Charging ? "charging" : ch == calc::Charge::Full ? "full" : "no cable"),
        "Any key: restart"});
  // Wait for a key (or a minute), then start the calculator normally.
  t0 = millis();
  bool any = false;
  while (!any && millis() - t0 < kResultShownMs) {
    keysPoll([](DKey) {});
    any = digitalRead(PIN_KEY_ON) == LOW;
    if (Serial.available()) any = true;
    for (int k = 0; k < kKeyCount && !any; ++k) any = keysHeld(DKey(k));
    delay(20);
  }
  Serial.flush();
  ESP.restart();
  while (true) {}
}
