niravkumar2008/AI-CALCULATOR/hardware/tools/v15_lcd/board_step2_route.py

# Stage 15 (v15-LCD) board step 2: place J5 (30-pin LCD FPC socket), Q4 (LCD power switch), Q5 (backlight
# switch), R21..R23, C19, C36; route everything; refill zones. Coordinates in mm, board frame.
# Run with KiCad's python after board_step1_cleanup.py.
#
# GPIO decisions taken here (mirrored in lcd.kicad_sch / mcu.kicad_sch / pins_v15_lcd.h):
#   IO4  (U1 pad 8)  = LCD_BL_EN   (was KEYPAD_INT; its F.Cu escape can reach the LCD area)
#   IO3  (U1 pad 7)  = KEYPAD_INT  (was free; RTC pin, so it still wakes the chip; it is boxed in by the U1 fan-out)
#   IO33 (U1 pad 28) = LCD_PWR_N   (was EPD_BUSY; its existing via at (138.5, 94.65) feeds a B.Cu run along y 81)
#   IO5/6/8/41/42   = LCD_RST/CS/SCK/DC/MOSI (the five e-paper SPI lines, re-named so the bus order matches the socket)
import os, sys
import pcbnew
from pcbnew import VECTOR2I, FromMM as mm, ToMM as tm

B = r"C:\Users\r_kas\OneDrive\Documents\GitHub\AI-CALCULATOR\hardware\kicad_v15_lcd\ai_calc_v15_lcd.kicad_pcb"
PROJ = os.path.dirname(B)
KLIB = r"C:\Program Files\KiCad\10.0\share\kicad\footprints"
b = pcbnew.LoadBoard(B)
F, Bk = pcbnew.F_Cu, pcbnew.B_Cu
FAB = pcbnew.F_Fab


def net(name):
    n = b.FindNet(name)
    if n is None:
        n = pcbnew.NETINFO_ITEM(b, name); b.Add(n)
    return n


def place(ref, libnick, libdir, name, value, x, y, rot, lcsc, nets, descr="", mpn=""):
    fp = pcbnew.FootprintLoad(libdir, name)
    fp.SetFPID(pcbnew.LIB_ID(libnick, name))
    fp.SetReference(ref); fp.SetValue(value)
    fp.SetPosition(VECTOR2I(mm(x), mm(y))); fp.SetOrientationDegrees(rot); fp.SetLayer(F)
    fp.SetField("LCSC", lcsc)
    if descr:
        fp.SetField("Description", descr)
    if mpn:
        fp.SetField("MPN", mpn)
    # extra fields hidden on F.Fab (a new field is created visible on the silkscreen!); references hidden like the rest of the board
    for fld in fp.GetFields():
        if fld.GetName() not in ("Reference", "Value"):
            fld.SetVisible(False); fld.SetLayer(FAB)
    fp.Reference().SetVisible(False)
    fp.Value().SetVisible(False)
    b.Add(fp)
    for p in fp.Pads():
        n = nets.get(p.GetNumber())
        if n:
            p.SetNet(net(n))
    return fp


def pads(fp):
    return {p.GetNumber(): (round(tm(p.GetPosition().x), 3), round(tm(p.GetPosition().y), 3)) for p in fp.Pads()}


def track(x1, y1, x2, y2, netname, layer=F, w=0.2):
    t = pcbnew.PCB_TRACK(b); t.SetStart(VECTOR2I(mm(x1), mm(y1))); t.SetEnd(VECTOR2I(mm(x2), mm(y2)))
    t.SetWidth(mm(w)); t.SetLayer(layer); t.SetNet(net(netname)); b.Add(t); return t


def route(points, netname, layer=F, w=0.2):
    for (x1, y1), (x2, y2) in zip(points, points[1:]):
        track(x1, y1, x2, y2, netname, layer, w)


def via(x, y, netname, d=0.5, drill=0.3):
    v = pcbnew.PCB_VIA(b); v.SetPosition(VECTOR2I(mm(x), mm(y))); v.SetWidth(mm(d)); v.SetDrill(mm(drill))
    v.SetViaType(pcbnew.VIATYPE_THROUGH); v.SetLayerPair(F, Bk); v.SetNet(net(netname)); b.Add(v); return v


def silk_line(x1, y1, x2, y2, w=0.15):
    s = pcbnew.PCB_SHAPE(b); s.SetShape(pcbnew.SHAPE_T_SEGMENT); s.SetLayer(pcbnew.F_SilkS)
    s.SetStart(VECTOR2I(mm(x1), mm(y1))); s.SetEnd(VECTOR2I(mm(x2), mm(y2))); s.SetWidth(mm(w)); b.Add(s)


# ------------------------------------------------------------------ leftovers from step 1, GPIO re-assignment at U1
for t in list(b.GetTracks()):
    n = str(t.GetNetname()); s_, e_ = t.GetStart(), t.GetEnd()
    xs = (tm(s_.x), tm(e_.x)); ys = (tm(s_.y), tm(e_.y))
    if n == "LCD_BL_EN" and max(xs) > 160:
        b.Delete(t); continue
    if n == "GND" and t.GetClass() == "PCB_TRACK" and min(xs) >= 155.0 and max(xs) <= 184.0 and min(ys) >= 79.0 and max(ys) <= 111.0:
        b.Delete(t); continue
    if max(xs) >= 177.0 and min(xs) <= 178.8 and max(ys) >= 82.7 and min(ys) <= 103.5:
        b.Delete(t); continue
    if n == "LCD_BL_EN":
        t.SetNet(net("LCD_PWR_N"))        # U1 pad 28 stub + via (138.5, 94.65)
U1 = b.FindFootprintByReference("U1")
for p_ in U1.Pads():
    if p_.GetNumber() == "7":
        p_.SetNet(net("KEYPAD_INT"))
    elif p_.GetNumber() == "8":
        p_.SetNet(net("LCD_BL_EN"))
    elif p_.GetNumber() == "28":
        p_.SetNet(net("LCD_PWR_N"))
for t in list(b.GetTracks()):
    if str(t.GetNetname()) == "KEYPAD_INT" and t.GetClass() == "PCB_TRACK":
        s_, e_ = t.GetStart(), t.GetEnd()
        if abs(tm(s_.x) - 127.55) < 0.01 and abs(tm(e_.x) - 127.55) < 0.01 and min(tm(s_.y), tm(e_.y)) < 104.1:
            top = VECTOR2I(mm(127.55), mm(105.5))
            if tm(s_.y) < tm(e_.y):
                t.SetStart(top)
            else:
                t.SetEnd(top)
            print("KEYPAD_INT vertical now starts at y 105.5")
route([(126.7, 104.0), (126.7, 104.55), (127.55, 105.4), (127.55, 105.5)], "KEYPAD_INT", F, 0.15)
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
